anticipation-labs/anticipy-hardware/03_PCB/R1_TARGET_NOT_YET_DESIGNED/README.md

# R1 — not yet designed

This folder is intentionally empty.

R1 is the current target board. As of 2026-09-06 it exists only as a written brief:
[`../../01_CURRENT_TARGET_R1/Anticipy_PROD_R1_Flux_Build_Brief.md`](../../01_CURRENT_TARGET_R1/Anticipy_PROD_R1_Flux_Build_Brief.md).

No schematic, layout, BOM or fabrication output exists. When work starts, the KiCad project
belongs here.

The brief's own first instruction is worth repeating: create the project, record the requirements,
and return a block diagram, an interface/power-rail table, a proposed BOM with active manufacturer
part numbers, and a list of unresolved conflicts — **before** placing or routing anything.
