anticipation-labs/anticipy-hardware/08_HISTORICAL_PACKAGES/2026-08-27_v07_four_day_build_pack/mechanical/V07_FIT_REPORT.md

# Anticipy v0.7 no-custom-PCB retained fit report

Classification: four-day hand-assembled founder prototype, not customer production.

1. PASS — finished envelope
2. PASS — 15% XY envelopes inside cavity and outside chain keepout
3. PASS — 15% same-layer envelopes do not overlap
4. PASS — actual component boxes do not collide
5. PASS — actual components do not intersect printed structure
6. PASS — base, carrier and lid close without solid interference
7. PASS — all explicit Z gaps positive
8. PASS — 15% seated Z envelopes retain positive keeper/lid gaps
9. PASS — primary print meshes watertight
10. PASS — one positive body per primary print mesh

Finished envelope: 76.0 × 33.0 × 19.0 mm.
The 51 × 21 × 11 mm target is not claimed because the protected 35 × 25 × 6 mm pack alone needs 40.25 × 28.75 mm XY reservation after the 15% margin.
Printed plastic estimate: 17.11 g.
Nominal complete estimate: 36.91 g; with 15% uncertainty: 42.44 g.
Mass remains a physical weigh-in gate because supplier pack, wiring, foam and screw weights are not controlled here.

Positive digital clearance does not prove battery runtime, drop survival, acoustics, RF range, sealing or electrical safety.
