anticipation-labs/anticipy-hardware/latest_builds/E1P1/pcb/manufacturing/drill_report.txt

Drill report for Anticipy_R1_E1_PROTOTYPE.kicad_pcb
Created on 2026-09-09T07:02:48

Copper Layer Stackup:
    =============================================================
    L1 :  F.Cu                      front
    L2 :  In1.Cu                    in1
    L3 :  In2.Cu                    in2
    L4 :  B.Cu                      back

Drill file 'Anticipy_R1_E1_PROTOTYPE-PTH.drl' contains
    plated through holes:
    =============================================================
    T1  0.200mm  0.0079"  (128 holes))
    T2  0.304mm  0.0120"  (9 holes))
    T3  0.600mm  0.0236"  (4 holes)  (with 4 slots)

    Total plated holes count 141

Drill file 'Anticipy_R1_E1_PROTOTYPE-NPTH.drl' contains
    unplated through holes:
    =============================================================

    Total unplated holes count 0
