anticipation-labs/anticipy-hardware/02_PROTOTYPE_XIAO/00_FOLDER_STATUS.md

# Folder status

This is the latest saved XIAO wiring/CAD packet that does not depend on Lee's Electronics. Its old SAPA/Saturday schedule is no longer an active commitment. Use the wiring, CAD and QA gates as engineering reference only; do not assume SAPA has accepted the job or has the parts.

The enclosed UF2 remains on physical release hold. Do not ship a unit until the real battery, motor, charging, audio, BLE, thermal, enclosure and mechanical tests pass.
