anticipation-labs/anticipy-hardware/05_FIRMWARE/SOURCE/THIRD_PARTY_NOTICES.md

# Third-party basis and notices

This EVT is a modified fork of the public Omi DevKit firmware from `BasedHardware/omi`, inspected at commit `0303fd24579f8e3d0a3b1c3d9e5ad99adf87a4d2` (2026-08-28). That repository is distributed under the MIT License. Preserve its copyright and license notice when distributing source or binaries.

The embedded Opus 1.2.1 source contains copyright notices from Xiph.Org Foundation, Skype Limited and other contributors and is distributed under permissive BSD-style terms recorded in the individual source headers. Binary distributions must reproduce the applicable notices and disclaimers in their documentation/materials.

Nordic nRF Connect SDK, Zephyr, board support and toolchain components have their own upstream licenses. A production release must run a complete software-bill-of-materials and license-notice generation step; this short notice is not a substitute for that compliance output.
