anticipation-labs/anticipy-hardware/08_HISTORICAL_PACKAGES/2026-08-28_tuesday_evt_v0.1/TUESDAY_TRUTH.md

# Tuesday truth

The from-components architecture is technically plausible at the strict size. It is not yet proven hardware.

- **Plausible by Tuesday:** 10 cosmetic shells and 1–2 working engineering units, if all parts and a correctly sized protected cell are physically available Monday.
- **High-risk attempt:** 10 bench-built units by Tuesday evening with two experienced technicians, but with almost no debugging or validation time.
- **Not an honest promise:** 10 safe, private, 16-hour, customer-ready pendants by Tuesday.

The immediate blocker is not PLAUD or a custom PCB. It is obtaining 12 documented protected cells that physically measure no more than 25 × 20 × 5 mm, followed by proving unit 1.
