anticipation-labs/anticipy-hardware/08_HISTORICAL_PACKAGES/2026-08-28_execution_v1.0/07_SOURCES/SOURCE_LEDGER_V1.md

# Primary source ledger

| Decision | Source |
|---|---|
| PLAUD NotePin S is 51 × 21 × 11 mm and 17.4 g | https://www.plaud.ai/pages/plaud-notepin-s |
| PLAUD material family is aluminum alloy + polycarbonate | https://support.plaud.ai/hc/en-us/articles/53770668740761-What-is-the-difference-between-Plaud-NotePin-and-NotePin-S |
| Raytac AN54LV-15 is 8.4 × 6.4 × 1.5 mm and pre-certified | https://www.raytac.com/product/ins.php?index_id=169 |
| Raytac official land/keepout guide | https://www.raytac.com/document/act.php?act=1&index_id=103 |
| IM69D128S: PDM, 69 dB SNR, 520 µA, component-level IP57 | https://www.infineon.com/part/IM69D128S |
| nPM1300 charger, power path and fuel-gauge features | https://www.nordicsemi.com/Products/nPM1300 |
| DRV2605L A2/REG is the 1.8 V regulator output and requires bypass to ground | https://www.ti.com/lit/ds/symlink/drv2605l.pdf |
| MKDV4GCL-ABF: 4 Gbit, about 481 MB usable, managed SD/SPI NAND | https://datasheet.lcsc.com/datasheet/pdf/861dc17860b6ca6b6ed9c649f697f4e2.pdf?productCode=C51966232 |
| MKDV4GCL-ABF JLC/LCSC assembly stock record | https://jlcpcb.com/partdetail/MK-MKDV4GCLABF/C51966232 |
| PTS841 public dimensions/land and 100k-cycle rating | https://www.littelfuse.com/products/switches/tactile-switches/pts841 |
| VC0720B015F 7 mm leaded coin motor | https://www.vybronics.com/coin-vibration-motors/with-brushes/v-c0720b015f |
| LP571225 comparator battery | https://www.lithium-polymer-akkus.de/wp-content/uploads/2021/04/LP571225-3.7V-200mAh.pdf |
| Seeed XIAO nRF52840 Sense 3-pack for lab build | https://www.seeedstudio.com/Seeed-Studio-XIAO-nRF52840-Sense-3PCS-p-5922.html |
| P2S specifications and supported-material baseline | https://bambulab.com/en/p2s/specs |
| Bambu Silk/Silk+ printing guidance | https://wiki.bambulab.com/en/x1/manual/printing-with-silk-filaments |
| Bambu PLA Metal is metal-textured plastic, not an aluminum part | https://ca.store.bambulab.com/products/pla-metal |
| JLCPCB baseline PCB lead-time explanation | https://jlcpcb.com/help/article/pcb-fabrication-services-and-production-time |
| JLCPCB SMT lead-time explanation | https://jlcpcb.com/help/article/smt-service-lead-time-overview |

Source pages can change. Inventory and delivery remain unallocated until checkout or a written supplier acknowledgement.
