anticipation-labs/anticipy-hardware/08_HISTORICAL_PACKAGES/2026-09-05_master_package/06_ROUTING_CANDIDATES_NOT_FOR_FAB/00_MASTER_PACKAGE_WARNING.md

# Do not fabricate these candidates

These are independent subsystem-routing experiments from the 36-hour sprint. They are not cumulative and are not a released PCB. A senior PCB engineer may use them as routing evidence only after rebuilding/consolidating the final board and rerunning complete ERC, DRC, DFM, RF, power and mechanical review with zero unconnected items.
