anticipation-labs/anticipy-hardware/08_HISTORICAL_PACKAGES/2026-08-19_anticipy_design_ds_bundle/hardware/xiao-spec.html

Electronics

# XIAO nRF52840 Sense

Property | Value
PCB | 20.955 × 17.78 × 1.24 mm
USB-C shell | 8.94 w × 3.21 h · overhangs edge 1.53 mm
mic | PDM MEMS, aperture on top face
charger | BQ25101 — 50 mA stock, 100 mA with P0.13 low
flash | 2 MB QSPI (≈8 min Opus — emergency buffer only)
battery | BLL 752042 · 3.7 V · 500 mAh · max 8.0×20.5×43 mm
storage add-on | Adafruit 4682 3V microSD (SPI: D8 SCK · D9 MISO · D10 MOSI · D0 CS)
firmware | Omi devkit lineage, Zephyr · Opus 16 kHz over BLE · SD offline sync GATT service
