anticipation-labs/anticipy-hardware/08_HISTORICAL_PACKAGES/2026-09-05_master_package/05_OLDER_R0_KICAD_NOT_FOR_FAB/drc_unrouted_report.txt

** Drc report for /workspace/scratch/295a51172f48/anticipy_pcb_kicad/Anticipy_PROD_R0_EVT.kicad_pcb **
** Created on 2026-08-30 02:28:59 **

** Found 134 DRC violations **
[silk_overlap]: Silkscreen overlap
    Rule: board setup constraints silk; Severity: warning
    @(31.0000 mm, 38.6000 mm): PCB Text 'SW' on F.Silkscreen
    @(29.3500 mm, 38.4000 mm): Line on F.Silkscreen
[silk_overlap]: Silkscreen overlap
    Rule: board setup constraints silk; Severity: warning
    @(54.2500 mm, 35.3500 mm): Line on F.Silkscreen
    @(53.6594 mm, 35.2900 mm): Line on F.Silkscreen
[silk_over_copper]: Silkscreen clipped by solder mask
    Local override; Severity: warning
    @(31.2000 mm, 32.9000 mm): PCB Text 'U2 PMIC' on F.Silkscreen
[silk_over_copper]: Silkscreen clipped by solder mask
    Local override; Severity: warning
    @(38.3464 mm, 38.2200 mm): Line on F.Silkscreen
[silk_over_copper]: Silkscreen clipped by solder mask
    Local override; Severity: warning
    @(54.2500 mm, 35.3500 mm): Line on F.Silkscreen
[silk_over_copper]: Silkscreen clipped by solder mask
    Local override; Severity: warning
    @(53.1500 mm, 35.3500 mm): Line on F.Silkscreen
[silk_over_copper]: Silkscreen clipped by solder mask
    Local override; Severity: warning
    @(37.0000 mm, 38.5600 mm): Line on F.Silkscreen
[silk_over_copper]: Silkscreen clipped by solder mask
    Local override; Severity: warning
    @(37.0000 mm, 38.5600 mm): Line on F.Silkscreen
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
    @(50.2600 mm, 21.9400 mm): Pad 5 [GND] of MIC2 on F.Cu
[hole_clearance]: Hole clearance violation (board setup constraints hole clearance 0.2500 mm; actual 0.1000 mm)
    Rule: board setup constraints hole; Severity: error
    @(51.0000 mm, 21.9400 mm): NPTH pad of MIC2
    @(51.0000 mm, 21.3900 mm): Pad 5 [GND] of MIC2 on F.Cu
[hole_clearance]: Hole clearance violation (board setup constraints hole clearance 0.2500 mm; actual 0.1000 mm)
    Rule: board setup constraints hole; Severity: error
    @(51.0000 mm, 21.9400 mm): NPTH pad of MIC2
    @(51.0000 mm, 22.4900 mm): Pad 5 [GND] of MIC2 on F.Cu
[hole_clearance]: Hole clearance violation (board setup constraints hole clearance 0.2500 mm; actual 0.1944 mm)
    Rule: board setup constraints hole; Severity: error
    @(23.2050 mm, 27.1100 mm): NPTH pad of J1
    @(24.2800 mm, 26.8000 mm): Pad A1 [GND] of J1 on F.Cu
[hole_clearance]: Hole clearance violation (board setup constraints hole clearance 0.2500 mm; actual 0.1944 mm)
    Rule: board setup constraints hole; Severity: error
    @(23.2050 mm, 27.1100 mm): NPTH pad of J1
    @(24.2800 mm, 26.8000 mm): Pad B12 [GND] of J1 on F.Cu
[hole_clearance]: Hole clearance violation (board setup constraints hole clearance 0.2500 mm; actual 0.1944 mm)
    Rule: board setup constraints hole; Severity: error
    @(23.2050 mm, 32.8900 mm): NPTH pad of J1
    @(24.2800 mm, 33.2000 mm): Pad A12 [GND] of J1 on F.Cu
[hole_clearance]: Hole clearance violation (board setup constraints hole clearance 0.2500 mm; actual 0.1944 mm)
    Rule: board setup constraints hole; Severity: error
    @(23.2050 mm, 32.8900 mm): NPTH pad of J1
    @(24.2800 mm, 33.2000 mm): Pad B1 [GND] of J1 on F.Cu

** Found 171 unconnected pads **
[unconnected_items]: Missing connection between items
    Local override; Severity: error
    @(29.0000 mm, 30.7750 mm): Pad 2 [GND] of C3 on B.Cu
    @(28.7625 mm, 30.7500 mm): Pad 6 [GND] of U2 on F.Cu
[unconnected_items]: Missing connection between items
    Local override; Severity: error
    @(48.7625 mm, 36.3500 mm): Pad 8 [GND] of U3 on F.Cu
    @(48.7625 mm, 36.8500 mm): Pad 7 [GND] of U3 on F.Cu
[unconnected_items]: Missing connection between items
    Local override; Severity: error
    @(48.2500 mm, 36.8625 mm): Pad 6 [GND] of U3 on F.Cu
    @(48.7625 mm, 36.8500 mm): Pad 7 [GND] of U3 on F.Cu
[unconnected_items]: Missing connection between items
    Local override; Severity: error
    @(27.2000 mm, 32.4800 mm): Pad 2 [GND] of C16 on B.Cu
    @(27.0000 mm, 31.9250 mm): Pad 2 [GND] of C4 on F.Cu
[unconnected_items]: Missing connection between items
    Local override; Severity: error
    @(39.0100 mm, 38.6000 mm): Pad 2 [GND] of R13 on F.Cu
    @(39.3500 mm, 38.0000 mm): Pad 2 [GND] of C21 on B.Cu
[unconnected_items]: Missing connection between items
    Local override; Severity: error
    @(37.1625 mm, 22.6365 mm): Pad 4 [GND] of MIC1 on F.Cu
    @(37.2600 mm, 21.9400 mm): Pad 5 [GND] of MIC1 on F.Cu
[unconnected_items]: Missing connection between items
    Local override; Severity: error
    @(37.9375 mm, 36.0500 mm): Pad 2 [GND] of Q1 on F.Cu
    @(37.4350 mm, 35.5250 mm): Pad 11 [GND] of J2 on B.Cu
[unconnected_items]: Missing connection between items
    Local override; Severity: error
    @(31.2000 mm, 30.0000 mm): Pad 33 [GND] of U2 on F.Cu
    @(31.9750 mm, 30.0000 mm): Pad 2 [GND] of C6 on B.Cu
[unconnected_items]: Missing connection between items
    Local override; Severity: error
    @(37.1625 mm, 22.6365 mm): Pad 4 [GND] of MIC1 on F.Cu
    @(38.0000 mm, 22.4900 mm): Pad 5 [GND] of MIC1 on F.Cu
[unconnected_items]: Missing connection between items
    Local override; Severity: error
    @(51.7400 mm, 21.9400 mm): Pad 5 [GND] of MIC2 on F.Cu
    @(51.0000 mm, 22.4900 mm): Pad 5 [GND] of MIC2 on F.Cu
[unconnected_items]: Missing connection between items
    Local override; Severity: error
    @(50.2600 mm, 21.9400 mm): Pad 5 [GND] of MIC2 on F.Cu
    @(51.0000 mm, 21.3900 mm): Pad 5 [GND] of MIC2 on F.Cu
[unconnected_items]: Missing connection between items
    Local override; Severity: error
    @(51.0000 mm, 21.3900 mm): Pad 5 [GND] of MIC2 on F.Cu
    @(51.7400 mm, 21.9400 mm): Pad 5 [GND] of MIC2 on F.Cu
[unconnected_items]: Missing connection between items
    Local override; Severity: error
    @(38.0000 mm, 21.3900 mm): Pad 5 [GND] of MIC1 on F.Cu
    @(37.2600 mm, 21.9400 mm): Pad 5 [GND] of MIC1 on F.Cu
[unconnected_items]: Missing connection between items
    Local override; Severity: error
    @(38.7400 mm, 21.9400 mm): Pad 5 [GND] of MIC1 on F.Cu
    @(38.0000 mm, 22.4900 mm): Pad 5 [GND] of MIC1 on F.Cu
[unconnected_items]: Missing connection between items
    Local override; Severity: error
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
    @(33.0100 mm, 34.2000 mm): Pad 2 [I2C_SCL] of R1 on F.Cu
    @(47.2375 mm, 35.3500 mm): Pad 1 [I2C_SCL] of U3 on F.Cu
[unconnected_items]: Missing connection between items
    Local override; Severity: error
    @(31.4500 mm, 32.4375 mm): Pad 13 [I2C_SDA] of U2 on F.Cu
    @(31.2100 mm, 34.2000 mm): Pad 2 [I2C_SDA] of R2 on F.Cu
[unconnected_items]: Missing connection between items
    Local override; Severity: error
    @(47.2375 mm, 36.8500 mm): Pad 4 [I2C_SDA] of U3 on F.Cu
    @(53.8500 mm, 26.0000 mm): Pad 16 [I2C_SDA] of U1 on F.Cu
[unconnected_items]: Missing connection between items
    Local override; Severity: error
    @(31.2100 mm, 34.2000 mm): Pad 2 [I2C_SDA] of R2 on F.Cu
    @(47.2375 mm, 36.8500 mm): Pad 4 [I2C_SDA] of U3 on F.Cu
[unconnected_items]: Missing connection between items
    Local override; Severity: error
    @(28.7625 mm, 31.2500 mm): Pad 7 [PMIC_INT] of U2 on F.Cu
    @(58.0500 mm, 34.6500 mm): Pad 41 [PMIC_INT] of U1 on F.Cu
[unconnected_items]: Missing connection between items
    Local override; Severity: error
    @(47.7500 mm, 35.3375 mm): Pad 12 [ACC_INT1] of U3 on F.Cu
    @(59.6500 mm, 34.6500 mm): Pad 44 [ACC_INT1] of U1 on F.Cu
[unconnected_items]: Missing connection between items
    Local override; Severity: error
    @(48.2500 mm, 35.3375 mm): Pad 11 [ACC_INT2] of U3 on F.Cu
    @(59.2500 mm, 33.7500 mm): Pad 43 [ACC_INT2] of U1 on F.Cu
[unconnected_items]: Missing connection between items
    Local override; Severity: error
    @(56.8500 mm, 33.7500 mm): Pad 38 [PDM_CLK] of U1 on F.Cu
    @(51.8375 mm, 22.6365 mm): Pad 2 [PDM_CLK] of MIC2 on F.Cu
[unconnected_items]: Missing connection between items
    Local override; Severity: error
    @(51.8375 mm, 22.6365 mm): Pad 2 [PDM_CLK] of MIC2 on F.Cu
    @(38.8375 mm, 22.6365 mm): Pad 2 [PDM_CLK] of MIC1 on F.Cu
[unconnected_items]: Missing connection between items
    Local override; Severity: error
    @(57.2500 mm, 34.6500 mm): Pad 39 [PDM_DATA] of U1 on F.Cu
    @(54.7100 mm, 23.3000 mm): Pad 2 [PDM_DATA] of R15 on F.Cu
[unconnected_items]: Missing connection between items
    Local override; Severity: error
    @(54.7100 mm, 23.3000 mm): Pad 2 [PDM_DATA] of R15 on F.Cu
    @(41.7100 mm, 23.3000 mm): Pad 2 [PDM_DATA] of R14 on F.Cu
[unconnected_items]: Missing connection between items
    Local override; Severity: error
    @(37.1625 mm, 23.4585 mm): Pad 3 [PDM_DATA_MIC1] of MIC1 on F.Cu
    @(40.6900 mm, 23.3000 mm): Pad 1 [PDM_DATA_MIC1] of R14 on F.Cu
[unconnected_items]: Missing connection between items
    Local override; Severity: error
    @(50.1625 mm, 23.4585 mm): Pad 3 [PDM_DATA_MIC2] of MIC2 on F.Cu
    @(53.6900 mm, 23.3000 mm): Pad 1 [PDM_DATA_MIC2] of R15 on F.Cu
[unconnected_items]: Missing connection between items
    Local override; Severity: error
    @(42.6900 mm, 38.0000 mm): Pad 1 [SD_SCK_MCU] of R8 on B.Cu
    @(56.4500 mm, 34.6500 mm): Pad 37 [SD_SCK_MCU] of U1 on F.Cu
[unconnected_items]: Missing connection between items
    Local override; Severity: error
    @(43.7100 mm, 38.0000 mm): Pad 2 [SD_SCK_CARD] of R8 on B.Cu
    @(44.2950 mm, 35.6500 mm): Pad 5 [SD_SCK_CARD] of J2 on B.Cu
[unconnected_items]: Missing connection between items
    Local override; Severity: error
    @(44.8900 mm, 38.0000 mm): Pad 1 [SD_MOSI_MCU] of R9 on B.Cu
    @(56.0500 mm, 33.7500 mm): Pad 36 [SD_MOSI_MCU] of U1 on F.Cu
[unconnected_items]: Missing connection between items
    Local override; Severity: error
    @(42.0950 mm, 35.6500 mm): Pad 3 [SD_MOSI_CARD] of J2 on B.Cu
    @(45.9100 mm, 38.0000 mm): Pad 2 [SD_MOSI_CARD] of R9 on B.Cu
[unconnected_items]: Missing connection between items
    Local override; Severity: error
    @(48.1100 mm, 38.0000 mm): Pad 2 [SD_MISO_MCU] of R10 on B.Cu
    @(54.7500 mm, 32.0000 mm): Pad 29 [SD_MISO_MCU] of U1 on F.Cu
[unconnected_items]: Missing connection between items
    Local override; Severity: error
    @(46.4950 mm, 35.6500 mm): Pad 7 [SD_MISO_CARD] of J2 on B.Cu
    @(47.0900 mm, 38.0000 mm): Pad 1 [SD_MISO_CARD] of R10 on B.Cu
[unconnected_items]: Missing connection between items
    Local override; Severity: error
    @(40.9950 mm, 35.6500 mm): Pad 2 [SD_CS] of J2 on B.Cu
    @(41.5100 mm, 38.0000 mm): Pad 2 [SD_CS] of R7 on B.Cu
[unconnected_items]: Missing connection between items
    Local override; Severity: error
    @(54.7500 mm, 31.2000 mm): Pad 27 [SD_CS] of U1 on F.Cu
    @(40.9950 mm, 35.6500 mm): Pad 2 [SD_CS] of J2 on B.Cu
[unconnected_items]: Missing connection between items
    Local override; Severity: error
    @(37.2600 mm, 29.5000 mm): Pad 9 [SD_DETECT] of J2 on B.Cu
    @(60.0500 mm, 33.7500 mm): Pad 45 [SD_DETECT] of U1 on F.Cu
[unconnected_items]: Missing connection between items
    Local override; Severity: error
    @(32.8100 mm, 35.5000 mm): Pad 2 [USER_BTN] of R11 on F.Cu
    @(32.4500 mm, 32.4375 mm): Pad 15 [USER_BTN] of U2 on F.Cu
[unconnected_items]: Missing connection between items
    Local override; Severity: error
    @(29.3000 mm, 37.0000 mm): Pad 1 [USER_BTN] of SW1 on F.Cu
    @(32.8100 mm, 35.5000 mm): Pad 2 [USER_BTN] of R11 on F.Cu
[unconnected_items]: Missing connection between items
    Local override; Severity: error
    @(53.8500 mm, 29.2000 mm): Pad 22 [USER_BTN] of U1 on F.Cu
    @(32.4500 mm, 32.4375 mm): Pad 15 [USER_BTN] of U2 on F.Cu
[unconnected_items]: Missing connection between items
    Local override; Severity: error
    @(36.1900 mm, 38.6000 mm): Pad 1 [HAPTIC_PWM] of R12 on F.Cu
    @(53.8500 mm, 30.0000 mm): Pad 24 [HAPTIC_PWM] of U1 on F.Cu
[unconnected_items]: Missing connection between items
    Local override; Severity: error
    @(37.9900 mm, 38.6000 mm): Pad 1 [HAPTIC_GATE] of R13 on F.Cu
    @(37.9375 mm, 37.9500 mm): Pad 1 [HAPTIC_GATE] of Q1 on F.Cu
[unconnected_items]: Missing connection between items
    Local override; Severity: error
    @(37.2100 mm, 38.6000 mm): Pad 2 [HAPTIC_GATE] of R12 on F.Cu
    @(37.9900 mm, 38.6000 mm): Pad 1 [HAPTIC_GATE] of R13 on F.Cu
[unconnected_items]: Missing connection between items
    Local override; Severity: error
    @(39.1500 mm, 37.0000 mm): Pad 1 [HAPTIC_NEG] of D1 on F.Cu
    @(39.4800 mm, 35.2000 mm): Pad 2 [HAPTIC_NEG] of C23 on F.Cu
[unconnected_items]: Missing connection between items
    Local override; Severity: error
    @(36.0625 mm, 37.0000 mm): Pad 3 [HAPTIC_NEG] of Q1 on F.Cu
    @(39.1500 mm, 37.0000 mm): Pad 1 [HAPTIC_NEG] of D1 on F.Cu
[unconnected_items]: Missing connection between items
    Local override; Severity: error
    @(27.6000 mm, 37.5500 mm): Pad 1 [LED_BLUE_K] of LED1 on F.Cu
    @(32.9500 mm, 27.5625 mm): Pad 25 [LED_BLUE_K] of U2 on F.Cu
[unconnected_items]: Missing connection between items
    Local override; Severity: error
    @(27.6000 mm, 36.8500 mm): Pad 3 [LED_RED_K] of LED1 on F.Cu
    @(32.4500 mm, 27.5625 mm): Pad 26 [LED_RED_K] of U2 on F.Cu
[unconnected_items]: Missing connection between items
    Local override; Severity: error
    @(49.5000 mm, 38.3000 mm): Pad 1 [SWDIO] of TP1 on B.Cu
    @(62.8500 mm, 34.6500 mm): Pad 51 [SWDIO] of U1 on F.Cu
[unconnected_items]: Missing connection between items
    Local override; Severity: error
    @(51.0000 mm, 38.3000 mm): Pad 1 [SWDCLK] of TP2 on B.Cu
    @(63.6500 mm, 34.6500 mm): Pad 53 [SWDCLK] of U1 on F.Cu
[unconnected_items]: Missing connection between items
    Local override; Severity: error
    @(52.5000 mm, 38.3000 mm): Pad 1 [RESET] of TP3 on B.Cu
    @(57.6500 mm, 33.7500 mm): Pad 40 [RESET] of U1 on F.Cu
[unconnected_items]: Missing connection between items
    Local override; Severity: error
    @(54.7500 mm, 28.8000 mm): Pad 21 [UART_TX] of U1 on F.Cu
    @(57.0000 mm, 38.3000 mm): Pad 1 [UART_TX] of TP6 on B.Cu
[unconnected_items]: Missing connection between items
    Local override; Severity: error
    @(53.8500 mm, 28.4000 mm): Pad 20 [UART_RX] of U1 on F.Cu
    @(58.5000 mm, 38.3000 mm): Pad 1 [UART_RX] of TP7 on B.Cu

** Found 0 Footprint errors **

** End of Report **
