anticipation-labs/anticipy-hardware/03_PCB/R0B_CHECKPOINT_NOT_FOR_FAB/99_Superseded_Notice/SUPERSEDED_FILES_NOTICE.md

# Superseded files notice

The earlier Flux build brief, R0A source tree, 49 x 20 mm layout, removable microSD concept, and all experimental autorouter outputs are deliberately excluded from the active handoff.

The controlling checkpoint in this ZIP is `ANT-PROD-R0B` with a 45.8 x 18.0 mm board outline, soldered NAND storage, updated ESD protection, button/light-pipe interface targets, and explicit fabrication blockers.

Do not merge R0A, Flux, or experimental route files into R0B. If an engineer reuses any older idea, it must be independently reviewed and intentionally incorporated into a new controlled revision.
