anticipation-labs/anticipy-hardware/03_PCB/R0B_CHECKPOINT_NOT_FOR_FAB/01_Electrical_Source/Reports/placement.png

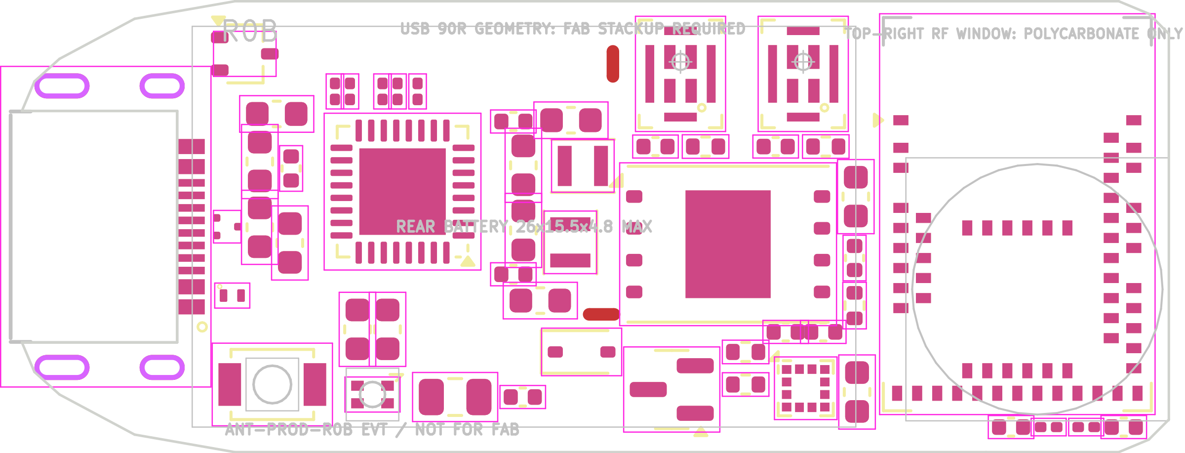
03_PCB/R0B_CHECKPOINT_NOT_FOR_FAB/01_Electrical_Source/Reports/placement.png
