anticipation-labs/anticipy-hardware/04_MECHANICAL/OPENSCAD_SHELL_PROGRAM_v5.1/beauty_back.png

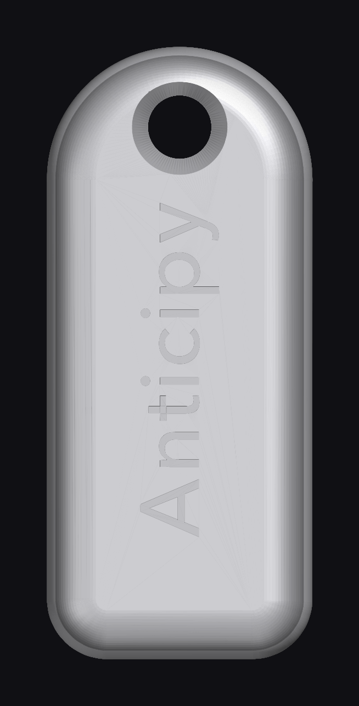
04_MECHANICAL/OPENSCAD_SHELL_PROGRAM_v5.1/beauty_back.png
