anticipation-labs/anticipy-hardware/04_MECHANICAL/OPENSCAD_SHELL_PROGRAM_v5.1/cmp_side_by_side.png

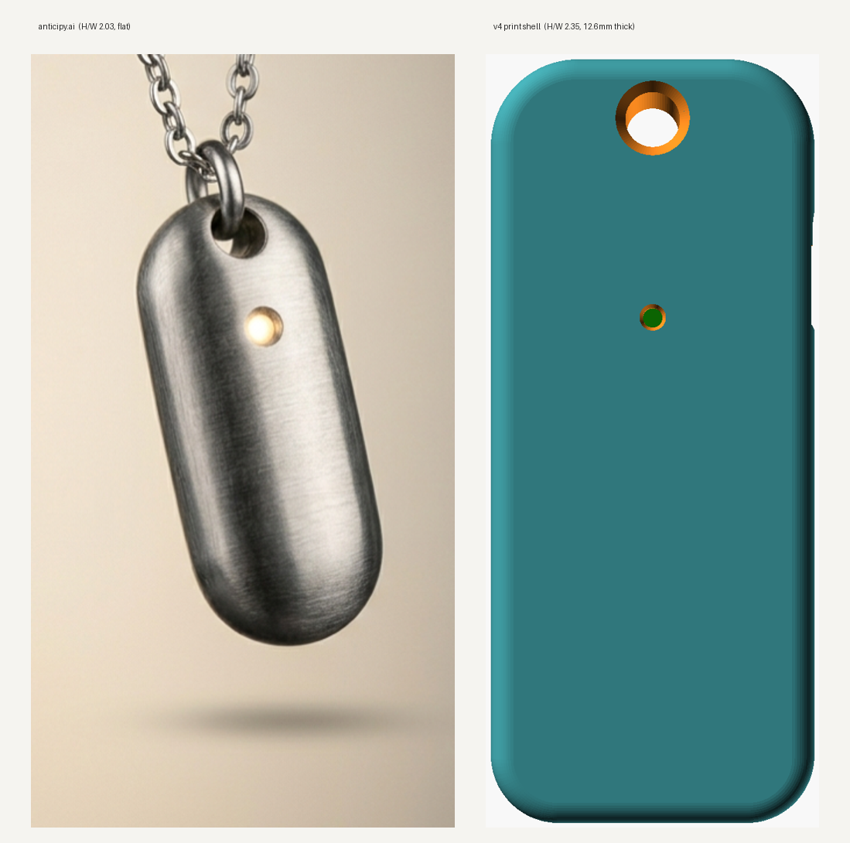
04_MECHANICAL/OPENSCAD_SHELL_PROGRAM_v5.1/cmp_side_by_side.png
