anticipation-labs/anticipy-hardware/04_MECHANICAL/OPENSCAD_SHELL_PROGRAM_v5.1/FINAL_v4_views.png

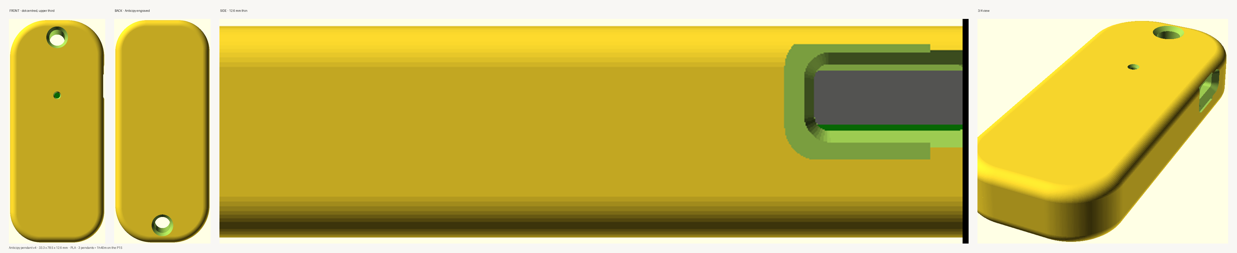
04_MECHANICAL/OPENSCAD_SHELL_PROGRAM_v5.1/FINAL_v4_views.png
