anticipation-labs/anticipy-hardware/04_MECHANICAL/OPENSCAD_SHELL_PROGRAM_v5.1/n_open.png

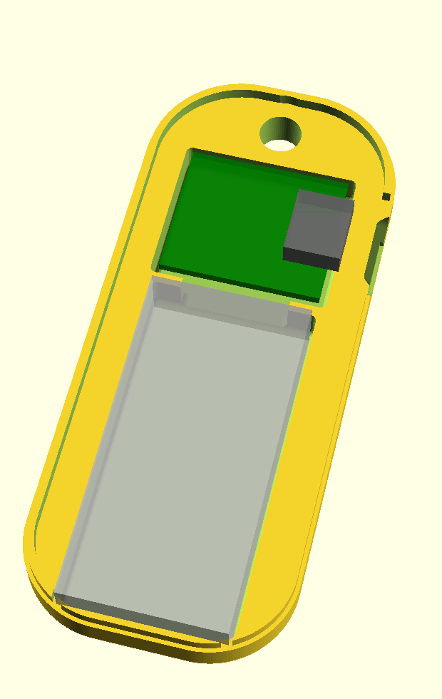
04_MECHANICAL/OPENSCAD_SHELL_PROGRAM_v5.1/n_open.png
