anticipation-labs/anticipy-hardware/04_MECHANICAL/OPENSCAD_SHELL_PROGRAM_v5.1/shape_A_square.png

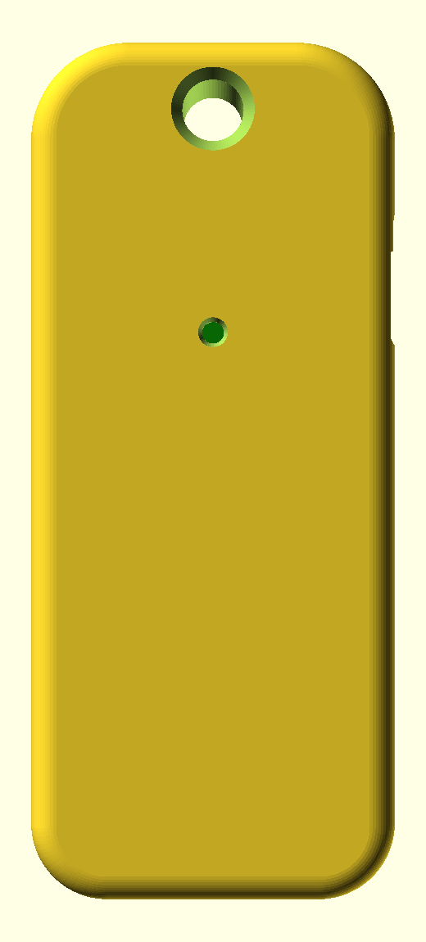
04_MECHANICAL/OPENSCAD_SHELL_PROGRAM_v5.1/shape_A_square.png
