anticipation-labs/anticipy-hardware/04_MECHANICAL/OPENSCAD_SHELL_PROGRAM_v5.1/v4_side.png

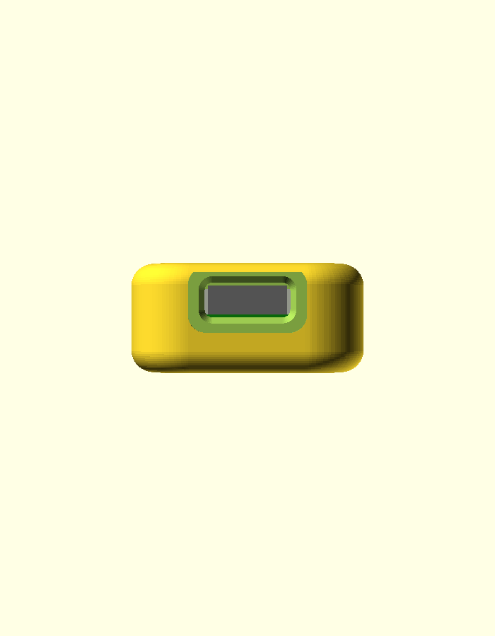
04_MECHANICAL/OPENSCAD_SHELL_PROGRAM_v5.1/v4_side.png
