anticipation-labs/anticipy-hardware/08_HISTORICAL_PACKAGES/2026-08-27_v07_four_day_build_pack/mechanical/v07_internal_layout.png

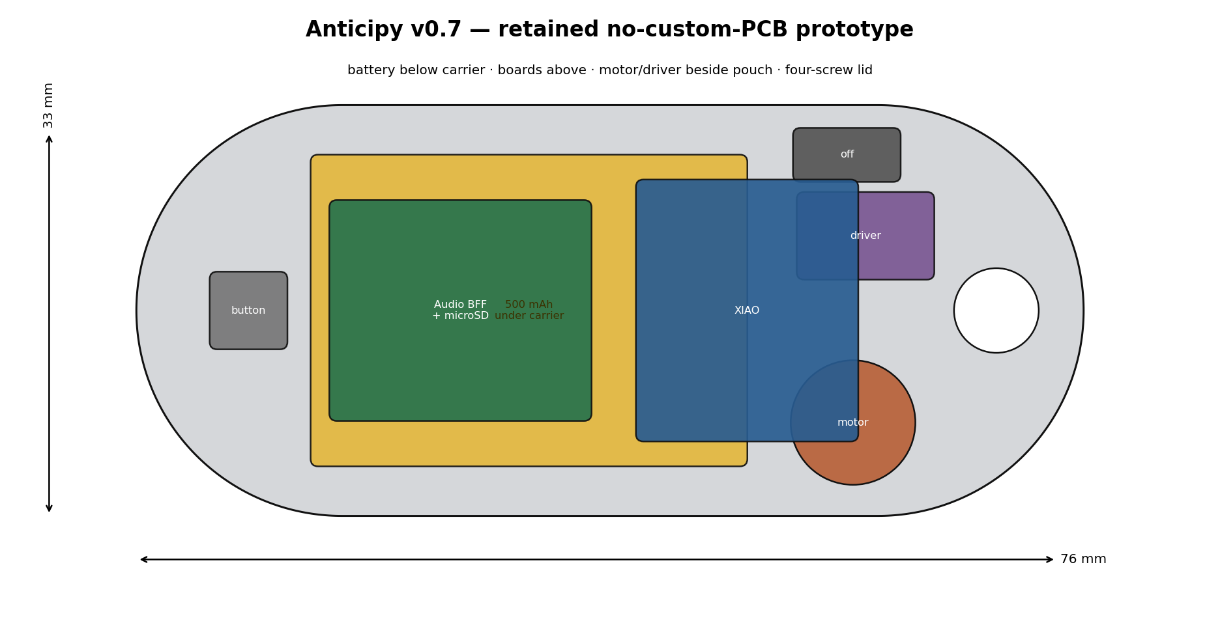
08_HISTORICAL_PACKAGES/2026-08-27_v07_four_day_build_pack/mechanical/v07_internal_layout.png
