anticipation-labs/anticipy-hardware/08_HISTORICAL_PACKAGES/2026-08-28_execution_v1.0/02_PRODUCTION_CAD/production_internal_layout.png

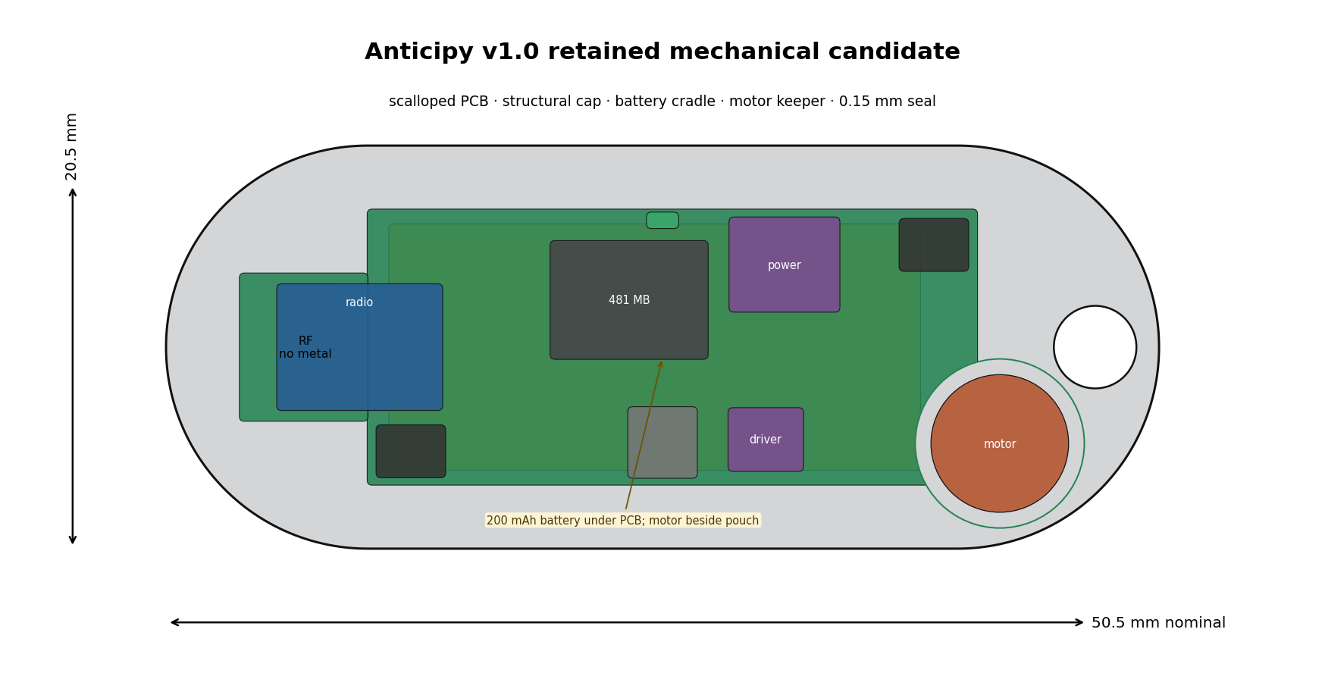
08_HISTORICAL_PACKAGES/2026-08-28_execution_v1.0/02_PRODUCTION_CAD/production_internal_layout.png
