anticipation-labs/anticipy-hardware/08_HISTORICAL_PACKAGES/2026-08-28_p2s_v07_enclosure/production_internal_layout.png

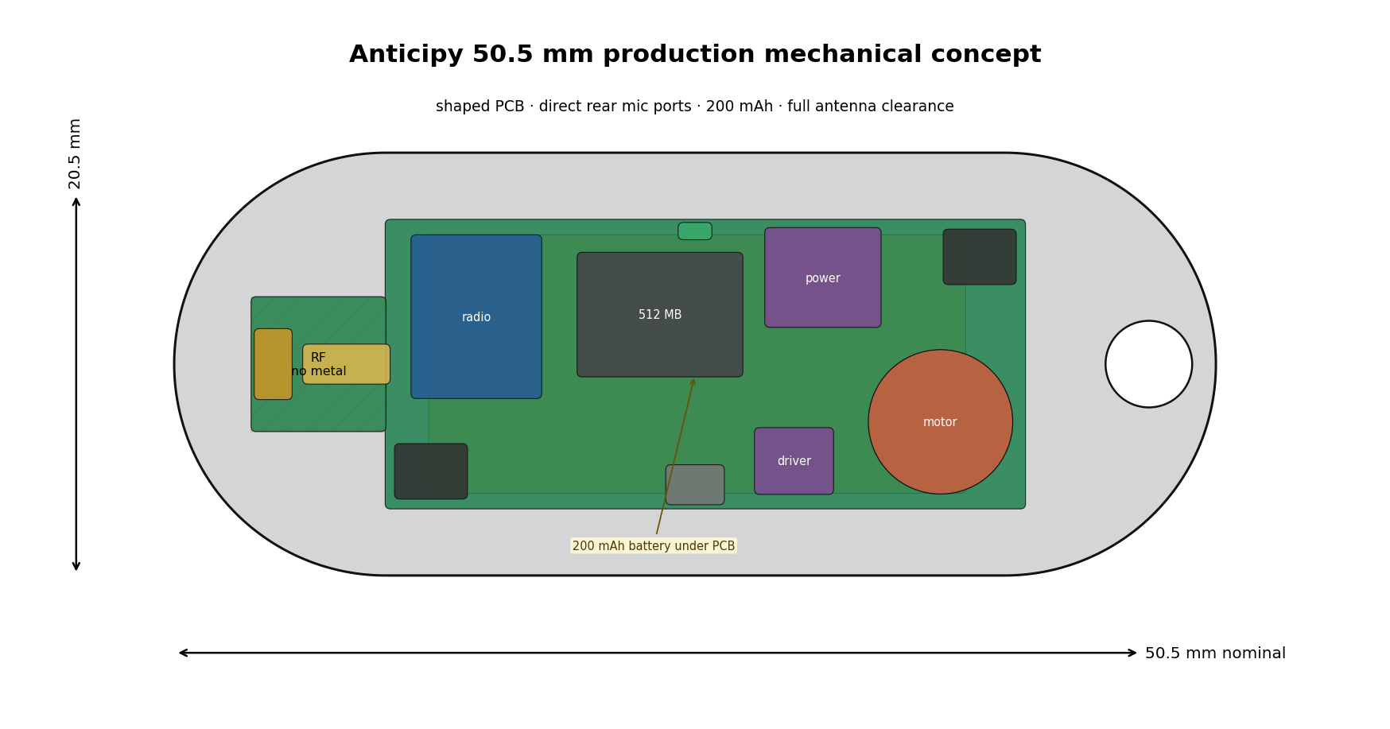
08_HISTORICAL_PACKAGES/2026-08-28_p2s_v07_enclosure/production_internal_layout.png
