anticipation-labs/anticipy-hardware/08_HISTORICAL_PACKAGES/2026-08-28_tuesday_evt_v0.1/anticipy_strict_evt_front_appearance.png

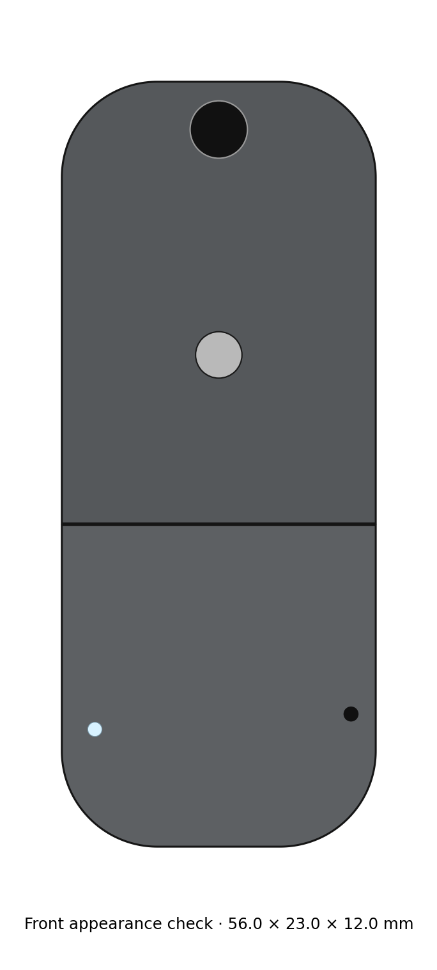
08_HISTORICAL_PACKAGES/2026-08-28_tuesday_evt_v0.1/anticipy_strict_evt_front_appearance.png
