anticipation-labs/anticipy-hardware/06_FACTORY_AND_QA/TEST_EVIDENCE/EXACT_SOURCING_2026-08-29.md

# Exact-size production candidate: live sourcing check

**Checked:** 2026-08-29 UTC  
**Destination:** West Vancouver, British Columbia, Canada  
**Scope:** corrected exact candidates for 3 EVT units and a later 50-unit build. No order was placed and no account/cart credentials were used. Stock and checkout freight can change without notice.

## Decision summary

- **Raytac AN54LV-15 is real and buyable in EVT quantity.** Raytac lists the 6.4 x 8.4 x 1.5 mm module as an active product. DigiKey Marketplace shows 45 pieces at USD 4.30, but Raytac—not DigiKey—ships them in approximately 14 days and charges USD 25 flat freight. Raytac's officially linked eBay listing adds five pieces at USD 6.00 plus USD 5.00 worldwide shipping.
- **It is not yet a production-secure 50-unit source.** The two visible online lots total exactly 50 pieces (45 + 5), leaving no attrition, rework or qualification spares and splitting the lot across channels. Direct Raytac allocation for at least 55–60 pieces is the appropriate production gate.
- **The standard LP571225 is not a 10 kOhm NTC pack.** Its product page and one-page drawing both explicitly say `NTC: No`. The supplier says it can customize a 10 kOhm ±1% at 25 C, B3380 NTC, but that requires a distinct controlled order drawing and a third lead.
- **The battery certification evidence is not purchase-release evidence for the custom NTC pack.** The standard page is tagged "IEC62133 Certified" and the drawing says the battery *parts* are IEC 62133 and RoHS compliant; another supplier page markets an "IEC62133 Certificate" version with different 50 mm wires and 26 mm length. No certificate/test-report number, exact-pack CB report, or exact LP571225 UN 38.3 test summary is downloadable from those pages. Obtain and match documents to the signed NTC pack drawing.
- **A complete exact-candidate cart is not executable today.** DigiKey currently shows zero VC0720B015F motors, while Vybronics' page still says 651 at DigiKey. That conflict must be resolved in writing. The custom battery is RFQ-only.

## Exact-candidate status table

Quantities assume one of each part per finished unit except **two IM69D128S microphones per unit**, matching the current production BOM.

| Candidate / exact order code | Live primary/authorized-source evidence | Cost for 3 EVT | Cost for 50 units | Status and procurement caveat |
|---|---|---:|---:|---|
| **Raytac AN54LV-15** | [Raytac](https://www.raytac.com/product/ins.php?index_id=169): 6.4 x 8.4 x 1.5 mm, chip antenna; FCC, IC/ISED, CE, Telec, KC, SRRC, NCC, RCM and WPC listed. [DigiKey Marketplace](https://www.digikey.com/en/products/detail/raytac/AN54LV-15/27793700): **45** in stock, USD 4.30 each, USD 25 flat freight, ships in approximately 14 days. [Raytac-linked eBay](https://www.ebay.com/itm/178290035890): **5** available, USD 6.00 each + USD 5.00 worldwide freight. | Preferred traceable route: USD **37.90** from DigiKey Marketplace (3 x 4.30 + 25 freight). Lower-cost official-linked eBay route: USD **23.00** (3 x 6 + 5 freight), before import charges. | Nominal online exhaustion: 45 DigiKey + 5 eBay = USD **253.50** including the two listed freight charges, before tax/import. | **EVT buyable; 50-unit production not released.** Exactly 50 visible gives zero spares. The eBay page says worldwide shipping and showed a Sep 4–22 estimate for its displayed generic location, not an address-validated West Vancouver promise. [Raytac direct](https://www.raytac.com/contact/) is RFQ/contact and says replies may take five business days. Raytac's RoHS/REACH report is still marked “Coming Soon.” |
| **Winbond W25N04KVZEIR** | [DigiKey Canada](https://www.digikey.ca/en/products/detail/winbond-electronics/W25N04KVZEIR/15182086): **406** in stock, active, but temporarily constrained and no backorders. [LCSC C6750381](https://www.lcsc.com/product-detail/C6750381.html): exact `W25N04KVZEIR TR`, **1,680** in stock/ships now, MOQ and multiple 30, USD 19.7556 at 30+. [JLCPCB C5342170](https://jlcpcb.com/partdetail/WinbondElec-W25N04KVZEIR/C5342170) lists the exact MPN as an Extended PCBA part; preordered material is for JLCPCB assembly only. | DigiKey: 3 x CAD 48.02 = CAD **144.06**. | DigiKey: 50 x CAD 41.9782 = CAD **2,098.91**. LCSC/JLC production option: buy 60 because of the 30-piece multiple = USD **1,185.34**, before freight/import/assembly. | **Buyable for 3 and 50.** Constrained-supply warning makes early reservation prudent. LCSC's 60-piece multiple provides 10 spares but uses a different commercial/PCBA flow. |
| **Infineon IM69D128SV01XTMA1** (2/unit) | [DigiKey Canada](https://www.digikey.ca/en/products/detail/infineon-technologies/IM69D128SV01XTMA1/17399510): **5,178** in stock; CAD 3.28 at 1, CAD 2.0346 at 100; 30-week manufacturer lead beyond stock. | 6 x CAD 3.28 = CAD **19.68**. | 100 x CAD 2.0346 = CAD **203.46**. | **Buyable.** Reserve all 100 plus yield spares from present stock; the quoted 30-week replenishment lead is material. |
| **Nordic NPM1300-CAAA-R** | [DigiKey Canada](https://www.digikey.ca/en/products/detail/nordic-semiconductor-asa/NPM1300-CAAA-R/19722484): **5,208** in stock; CAD 4.68 at 1, CAD 3.202 at 25; 20-week manufacturer lead beyond stock. | 3 x CAD 4.68 = CAD **14.04**. | 50 x CAD 3.202 = CAD **160.10**. | **Buyable.** WLCSP assembly/X-ray remains an assembler capability gate, not a sourcing gate. |
| **Texas Instruments DRV2605LYZFR** | [DigiKey Canada](https://www.digikey.ca/en/products/detail/texas-instruments/DRV2605LYZFR/4866959): **10,702** in stock; CAD 3.51 at 1, CAD 2.3636 at 25; 26-week manufacturer lead beyond stock. | 3 x CAD 3.51 = CAD **10.53**. | 50 x CAD 2.3636 = CAD **118.18**. | **Buyable.** DSBGA reflow/X-ray and exact support passives remain assembly/release gates. |
| **C&K / Littelfuse PTS841 GM SMTR LFS** | [Mouser Canada](https://www.mouser.ca/ProductDetail/CK/PTS841-GM-SMTR-LFS?qs=d0WKAl%252BL4KaUAcUzdsUy8A%3D%3D): **2,960** in stock/can ship immediately; CAD 0.619 at 1, CAD 0.569 at 25; nine-week factory lead beyond stock. | CAD **1.86**. | CAD **28.45**. | **Buyable.** Mouser's sub-CAD-100 shipment freight is extra unless consolidated with other Mouser material. |
| **Vybronics VC0720B015F** | [Vybronics](https://www.vybronics.com/coin-vibration-motors/with-brushes/v-c0720b015f) says **651** in DigiKey stock and quotes direct only for 2,000+ pieces. [DigiKey Canada](https://www.digikey.ca/en/products/detail/vybronics-inc/VC0720B015F/6570601) currently says **0** in stock, 500 past due, and nine-week standard lead; listed prices remain CAD 5.63 at 1 and CAD 4.5838 at 50. | **Not executable.** Price indication if replenished: CAD **16.89**. | **Not executable.** Price indication if replenished: CAD **229.19**. | **Conflicting / no verified buyable stock.** Do not count the manufacturer's mirrored DigiKey number until DigiKey or Vybronics confirms an allocated lot. The 25% tariff notation on Vybronics' page is a US tariff note, not a Canadian landed-cost quote. |
| **LiPol LP571225, custom three-wire 10 kOhm NTC pack** | [Standard LP571225 page](https://www.lipobattery.us/lithium-polymer-battery-lp571225-3-7v-200mah-0-74wh-with-protection-circuit-wires-10mm/): 5.7 x 12 x 25 mm, PCM, two 10 mm wires, **NTC: No**, MOQ 5, one week to ship only when stocked; new production 6–7 weeks at MOQ 5,000. Supplier offers custom 10 kOhm ±1%, B3380. [Standard drawing](https://www.lipobattery.us/wp-content/uploads/2021/04/LP571225-3.7V-200mAh.pdf): NTC No, PCM Yes, thickness tolerance to 6.0 mm, 26 mm finished length shown. [Alternate IEC-labelled page](https://www.lipobatteries.net/hot-selling-lipo-battery/lp571225-200mah-iec62133-certificate-lipo-batteries-manufacturer/) uses 50 mm wires and 26 mm length and says most packs lack thermistors. | **RFQ; MOQ 5; no public price or confirmed custom-sample lead.** | **RFQ; no published 50-piece production path.** Published new-production terms are MOQ 5,000 and 6–7 weeks. | **Custom controlled item; not purchase released.** Standard LP571225 does not meet the three-wire NTC requirement. Obtain a supplier-signed drawing and pack-specific compliance/transport documents before PO. |

## Candidate-cart arithmetic

These totals include only the corrected candidates above, not passives, PCB fabrication/assembly, programming, housings, freight not explicitly stated, or taxes.

| Build | Known-cost subtotal | Missing / blocking items |
|---|---:|---|
| **3 EVT, Canadian authorized distributors + DigiKey Marketplace module** | CAD **190.17** + USD **37.90**. The CAD subtotal is DigiKey semiconductors plus the Mouser switch; DigiKey's CAD 188.31 regular-stock portion is above its free-delivery threshold. | Exact motor unavailable; custom battery RFQ. Mouser freight is extra on its CAD 1.86 standalone order. |
| **50, DigiKey/Mouser semiconductor route + nominal split module lot** | CAD **2,609.10** + USD **253.50**. | Exact motor unavailable; custom battery RFQ; module lot has no spares and is therefore not a production release. |
| **50, LCSC/JLC-oriented W25 route + nominal split module lot** | CAD **510.19** + USD **1,185.34** for 60 W25 parts + USD **253.50** for 50 modules. | Same motor/battery/module blockers; add LCSC freight, import costs, consignment/global-sourcing handling, and PCBA charges. |

## LP571225 release requirements

The production item should remain `BAT-ANT-200-001`, not merely `LP571225`. Require a supplier-signed drawing that fixes all of the following:

- finished maximum envelope **27.0 x 12.5 x 6.0 mm**, including PCM, tape, weld tabs, NTC and lead exit; the public comparator drawing permits 26 ± 1 mm finished length, so 26 mm cannot be treated as the maximum;
- 3.7 V nominal, 200 mAh minimum/accepted capacity tolerance, 1S1P PCM thresholds, permitted charge current and temperature limits;
- **three leads**, exact colors/polarity/length/connector or stripped termination;
- NTC **10 kOhm ±1% at 25 C, B3380** and its physical placement on the cell;
- swelling allowance and lifecycle acceptance criteria;
- the exact finished pack's **IEC 62133-2 test report or CB certificate**, **UN 38.3 test summary**, SDS/MSDS, RoHS/REACH declarations, and dangerous-goods shipping declaration.

The supplier page's incorrect “27.75 Wh” field (the same page otherwise says 0.74 Wh) is an additional reason to rely on a signed drawing rather than web copy. Adding an NTC may also consume the entire 6.0 mm thickness limit; approve measured samples before enclosure release.

## Delivery, tax and schedule conclusion

- [DigiKey Canada](https://www.digikey.ca/en/help-support/delivery-information/delivery-time-and-cost) says regular CAD orders are DDP, free-delivery above CAD 100, and usually reach Canada in about 24 hours after dispatch, with customs capable of adding delay. Marketplace material is separate, CPT, excluded from free freight, and has duty/customs/tax due on delivery.
- Mouser Canada presents CAD orders as DDP and says prices include duty/customs on select shipping methods; GST/PST remain applicable. The switch-only order is below its CAD 100 free-freight threshold.
- The Raytac eBay, LCSC and battery-supplier routes are cross-border shipments. Budget checkout freight, brokerage, GST and BC PST as applicable; do not apply the US-only 25% Vybronics tariff note to a Canadian landed-cost model. Lithium batteries may also attract dangerous-goods freight and carrier restrictions.

**Reject a two-week promise.** A 2026-09-12 arrival for exact, assembled EVT units is not credible: the DigiKey Marketplace AN54LV-15 alone takes approximately 14 days merely to dispatch; its official-linked eBay page showed a Sep 4–22 range for a generic displayed location rather than West Vancouver; the exact motor has no verified distributor stock; and the required NTC battery is a custom RFQ item with no published sample lead.

For planning only, late September/October is the first defensible **3-EVT** window *after* written motor allocation and custom-battery sample confirmation, plus PCB assembly and transit. It is not presently a commit date. The **50-unit** build is not schedulable today: obtain a direct Raytac allocation with spares and a written 50-pack exception/lead from LiPol first. If the battery requires new production, its published 6–7 week clock precedes assembly and shipping, making November 2026 an aggressive planning floor rather than a promise.
