anticipation-labs/anticipy-hardware/latest_builds/E1P1/sourcing/SMT_27_Group_Live_Stock_Refresh.md

# E1P1: complete SMT source refresh

**The selected BOM has 27 ordering groups and 47 fitted components per board. Live pages cover 26 groups for 20 boards plus two-board spares. The remaining group is U1: its 25 previously ordered modules are consignment candidates, with no verified usable count or assembler receipt. A complete 20-board kit has not been verified.**

Checked 9 September 2026, 13:57–13:59 UTC (09:57–09:59 Boston). Every row below was read from its live product page. This is source availability, not allocation, delivery, assembly acceptance, or a purchase. The selected native changes and packaging aliases must appear in the release BOM before ordering.

Quantities: **940 fitted SMT pieces for 20 boards; 1,034 with two-board spares**. The 94 extra pieces are optional and do not replace an assembler-specific feeder/leader/attrition requirement. Offboard battery, motor, NTC, harness, cases and programming/test tools are separate.

| References | Selected ordering MPN | 20 fitted | Optional spares | Live stock | Source / UTC |
|---|---|---:|---:|---:|---|
| R13 R7 R12 | RC0402FR-0710KL | 60 | 6 | 12,854,598 | [DigiKey US](https://www.digikey.com/en/products/detail/yageo/RC0402FR-0710KL/729470) / 13:57:28 |
| R6 | RC0402FR-07100KL | 20 | 2 | 8,088,185 | [DigiKey US](https://www.digikey.com/en/products/detail/yageo/RC0402FR-07100KL/726526) / 13:57:29 |
| C7 C8 C2 C4 C3 C10 C9 | GRM188R61E106MA73D | 140 | 14 | 299,202 | [DigiKey US](https://www.digikey.com/en/products/detail/murata-electronics/GRM188R61E106MA73D/3900497) / 13:58:21 |
| C6 | EMK107BB7225KA-T | 20 | 2 | 171,421 | [DigiKey US](https://www.digikey.com/en/products/detail/taiyo-yuden/EMK107BB7225KA-T/4970646) / 13:57:31 |
| U4 | TPD2EUSB30ADRTR | 20 | 2 | 80,460 | [DigiKey US](https://www.digikey.com/en/products/detail/texas-instruments/TPD2EUSB30ADRTR/2520830) / 13:58:44 |
| L1 L2 | CIGT201610EH2R2MNE | 40 | 4 | 178,231 | [DigiKey US](https://www.digikey.com/en/products/detail/samsung-electro-mechanics/CIGT201610EH2R2MNE/7041223) / 13:57:32 |
| U1 | MDBT50Q-1MV2 | 20 | 2 | 14 | [DigiKey Marketplace / Raytac](https://www.digikey.com/en/products/detail/raytac/MDBT50Q-1MV2/13677591) / 13:57:33 |
| R2 R1 | RC0201FR-0710KL | 40 | 4 | 6,044,695 | [DigiKey US](https://www.digikey.com/en/products/detail/yageo/RC0201FR-0710KL/1948870) / 13:57:34 |
| LED1 | APHB1608LVBDSEKJ3C | 20 | 2 | 17,539 | [DigiKey US](https://www.digikey.com/en/products/detail/kingbright/APHB1608LVBDSEKJ3C/5803645) / 13:57:46 |
| SW1 | B3U-1000P | 20 | 2 | 119,580 | [DigiKey US](https://www.digikey.com/en/products/detail/omron-electronics-inc-emc-div/B3U-1000P/1859107) / 13:57:48 |
| Q1 | AO3400A | 20 | 2 | 299,214 | [DigiKey US](https://www.digikey.com/en/products/detail/alpha-omega-semiconductor-inc/AO3400A/1855772) / 13:57:49 |
| U2 | NPM1300-QEAA-R | 20 | 2 | 12,229 | [DigiKey US](https://www.digikey.com/en/products/detail/nordic-semiconductor-asa/NPM1300-QEAA-R/19722479) / 13:57:07 |
| R5 R8 | RC0402FR-07100RL | 40 | 4 | 2,456,693 | [DigiKey US](https://www.digikey.com/en/products/detail/yageo/RC0402FR-07100RL/726527) / 13:57:50 |
| J1 | USB4500-03-1-A | 20 | 2 | 16,152 | [DigiKey US](https://www.digikey.com/en/products/detail/gct/USB4500-03-1-A/15283198) / 13:57:08 |
| C14 C15 C16 | C0402C104M4RACTU | 60 | 6 | 148,419 | [DigiKey US](https://www.digikey.com/en/products/detail/kemet/C0402C104M4RACTU/2196240) / 13:57:51 |
| C17 C19 C22 | C1005X7R1C104K050BC | 60 | 6 | 1,506,626 | [DigiKey US](https://www.digikey.com/en/products/detail/tdk-corporation/C1005X7R1C104K050BC/2093220) / 13:57:52 |
| D1 | 1N4148WS-13-F | 20 | 2 | 1,824 | [Mouser USA](https://www.mouser.com/en/ProductDetail/Diodes-Incorporated/1N4148WS-13-F?qs=uwE%252BXfKqZqTz4dP8PH7EKg%3D%3D) / 13:58 |
| C13 | C0603X5R1E104K030BB | 20 | 2 | 933,292 | [DigiKey US](https://www.digikey.com/en/products/detail/tdk-corporation/C0603X5R1E104K030BB/3950907) / 13:58:41 |
| U6 | TPD2E2U06DCKR | 20 | 2 | 34 | [DigiKey US](https://www.digikey.com/en/products/detail/texas-instruments/TPD2E2U06DCKR/11502208) / 13:57:09 |
| R11 R10 | CRCW02010000Z0ED | 40 | 4 | 5,915,370 | [DigiKey US](https://www.digikey.com/en/products/detail/vishay-dale/CRCW02010000Z0ED/1178434) / 13:58:22 |
| C26 C25 | GRM155R60J106ME15D | 40 | 4 | 1,368,074 | [DigiKey US](https://www.digikey.com/en/products/detail/murata-electronics/GRM155R60J106ME15D/5877401) / 13:58:23 |
| MIC1 | CMM-3424DT-26165-TR | 20 | 2 | 2,759 | [DigiKey US](https://www.digikey.com/en/products/detail/same-sky-formerly-cui-devices/CMM-3424DT-26165-TR/20380848) / 13:58:24 |
| C23 | GRM21BR60J476ME01L | 20 | 2 | 777 | [DigiKey US](https://www.digikey.com/en/products/detail/murata-electronics/GRM21BR60J476ME01L/10703358) / 13:58:43 |
| R3 R4 | RC0201FR-07150KL | 40 | 4 | 8,350 | [DigiKey US](https://www.digikey.com/en/products/detail/yageo/RC0201FR-07150KL/3202384) / 13:58:25 |
| D2 | ESD441DPYR | 20 | 2 | 2,613 | [DigiKey US](https://www.digikey.com/en/products/detail/texas-instruments/ESD441DPYR/28715599) / 13:58:26 |
| C1 C18 C5 | C1608X7R1C105K080AC | 60 | 6 | 1,548,727 | [DigiKey US](https://www.digikey.com/en/products/detail/tdk-corporation/C1608X7R1C105K080AC/634395) / 13:58:28 |
| U5 | MX35LF4GE4AD-Z4I | 20 | 2 | 2,339 | [DigiKey US](https://www.digikey.com/en/products/detail/macronix/MX35LF4GE4AD-Z4I/18110032) / 13:57:10 |

## The actionable exceptions

- **U1 / MDBT50Q-1MV2:** DigiKey lists 14 via Raytac Marketplace and approximately 14 days to dispatch. This is neither enough quantity nor the Saturday route. Find and count the 25 previously ordered modules, preserve lot/moisture packaging, and transport an accepted kit to the assembler. Do not automatically repurchase them. Adafruit product 4078, which identifies this exact module, is currently out of stock; no verified domestic replacement stock for 20 was found in this bounded pass.
- **U6 / TPD2E2U06DCKR:** DigiKey has only34, but [Mouser USA](https://www.mouser.com/en/ProductDetail/Texas-Instruments/TPD2E2U06DCKR?qs=xZ%2FP%252ba9zWqa9UMTS1HgCWA%3D%3D) was live **107**, **Can Ship Immediately**, **USD0.268 each at10+**, around13:59UTC. This is the exact MPN, not a substitution. It can be sourced alongside D1 if still available. A dispatch statement does not reserve these units.
- **D1 / 1N4148WS-13-F:** live Mouser quantity1,824 and immediate-dispatch statement are reconfirmed. The -13 versus -7 code is the documented reel-package option, same SOD323 device. Cut tape is available, minimum1; no10,000-piece reel is required.
- DigiKey displays a high-volume processing warning that may add **one business day**. An in-stock page is insufficient to promise Boston arrival or a completed assembly by Saturday.

## Purchased-parts evidence and the correct credit

The saved `outputs/Anticipy_Boston_Procurement_2026-09-08/evidence/Live_Order_and_Delivery_Verification.json` was checked at00:58UTC on9September. It records a TME package of25 invoiced Raytac modules, carrier-delivered in British Columbia on3September at16:17UTC−0700. The companion `Updated_Inventory.json` explicitly keeps usable physical count null and Boston availability unverified. The DigiKey package containing25 invoiced AO3400A and20 invoiced B3U-1000P was carrier-delivered to West Vancouver on1September at12:25. This pass read that saved evidence; it did not perform a fresh carrier lookup or open/count packages.

Treat these three groups as **carrier-delivered consignment candidates**, not as an accepted production kit. If all are counted, usable and received by the assembler, fitted20 needs no new U1/Q1/SW1 purchases; optional22 needs two additional switches. The JSON carries conditional quantities while leaving actual usable stock and assembler receipt unknown. No private email IDs or tracking links are reproduced here.

## Selection traceability

- Packaging/ordering changes already supported by manufacturer documentation: GRM188R61E106MA73J→GRM188R61E106MA73D; C0402C104M4RAC7867→C0402C104M4RACTU; 1N4148WS-7-F→1N4148WS-13-F.
- Engineering selections in this release pass: U4 TPD2EUSB30ADRTR; C17/C19/C22 C1005X7R1C104K050BC; C13 C0603X5R1E104K030BB; C23 GRM21BR60J476ME01L. See the separate USB and passive component decision reports; these are not all mere package aliases.
- C6 EMK107BB7225KA-T is an actual active exact listing, live171,421. nPM1300-QEAA-R live12,229 and USB4500-03-1-A live16,152 are actual exact listings. No further invalid ordering code was found in these27 selected groups.
- Only MIC1 is fitted; do not purchase or install MIC2 for this population. The native BOM remains the placement authority.

**Release use:** this report completes the source-selection audit for the chosen design. Purchasing must reconfirm and allocate stock, and the assembler must receive the complete kit. It does not assert physical qualification or a Saturday production commitment. No supplier email, order, or file upload was sent.
