anticipation-labs/anticipy-hardware/03_PCB/R0B_CHECKPOINT_NOT_FOR_FAB/07_Messages/SUPPLIER_CONTACTS.md

# Verified supplier and engineering contacts

Verified on 2026-08-29 from official company pages.

| Organization | Use | Contact |
|---|---|---|
| CCI Canadian Circuits, Surrey | Primary rush PCB/PCBA capability request | `sales@canadiancircuits.com`, 604-599-8600, https://www.canadiancircuits.com/contact/ |
| Enigma Interconnect, Burnaby | Local bare-board backup | `boards@enigmacorp.com`, 604-420-3313, https://www.enigmacorp.com/quote |
| MistyWest, Vancouver | Full-service hardware engineering option | `contact@mistywest.com`, 604-292-7036, https://www.mistywest.com/contact/ |

These contacts are leads, not booked commitments. Ask for written confirmation of scope, owner, start time, price, material stock, and exact delivery date.
