anticipation-labs/anticipy-hardware/03_PCB/R0B_CHECKPOINT_NOT_FOR_FAB/00_Master_Guide/Anticipy_Project_Control.xlsx

Sheet: Overview
Anticipy R0B Project Control | Anticipy R0B Project Control | Anticipy R0B Project Control | Anticipy R0B Project Control | Anticipy R0B Project Control | Anticipy R0B Project Control
Release ANT-PROD-R0B-EVT-HANDOFF-2026-08-29 | Engineering WIP | Not approved for fabrication | Release ANT-PROD-R0B-EVT-HANDOFF-2026-08-29 | Engineering WIP | Not approved for fabrication | Release ANT-PROD-R0B-EVT-HANDOFF-2026-08-29 | Engineering WIP | Not approved for fabrication | Release ANT-PROD-R0B-EVT-HANDOFF-2026-08-29 | Engineering WIP | Not approved for fabrication | Release ANT-PROD-R0B-EVT-HANDOFF-2026-08-29 | Engineering WIP | Not approved for fabrication | Release ANT-PROD-R0B-EVT-HANDOFF-2026-08-29 | Engineering WIP | Not approved for fabrication
Metric | Current state
Fabrication status | BLOCKED
Board outline | 45.8 x 18.0 mm
PCB target | 4 layers, 0.80 mm
Provisional STEP | 0.82 mm - reconcile
Unrouted connections | 176
Open release gates | 18
Missing deliverables | 8
DO NOT upload the current KiCad board to a factory. A zero DRC violation count does not mean the board is routed; 176 unconnected items remain. | DO NOT upload the current KiCad board to a factory. A zero DRC violation count does not mean the board is routed; 176 unconnected items remain. | DO NOT upload the current KiCad board to a factory. A zero DRC violation count does not mean the board is routed; 176 unconnected items remain. | DO NOT upload the current KiCad board to a factory. A zero DRC violation count does not mean the board is routed; 176 unconnected items remain. | DO NOT upload the current KiCad board to a factory. A zero DRC violation count does not mean the board is routed; 176 unconnected items remain. | DO NOT upload the current KiCad board to a factory. A zero DRC violation count does not mean the board is routed; 176 unconnected items remain.
Immediate action | Owner | Status | Deadline | Evidence | Stop condition
Hire one accountable senior PCB lead | Omar | Open | Day 0 | Written acceptance and start time | No named owner
Select exact protected battery | PCB Lead | Open | Day 1 | Controlled drawing, sample and compliance file | Any missing battery evidence
Send capability RFQs without manufacturing release | Omar | Open | Day 0 | Written stack-up, stock and schedule | Factory assumes current files are released
Assign firmware and mechanical owners | Omar | Open | Day 0 | Named owners and availability | No bring-up or enclosure owner
Finish routing and Gate 0 review | PCB Lead | Open | Day 1-2 | Zero unconnected/ERC/DRC and release ZIP | Any unresolved engineering gate

Sheet: Gates
Release Gates | Release Gates | Release Gates | Release Gates | Release Gates | Release Gates
Every open row blocks the next release stage unless the exact evidence field is complete. | Every open row blocks the next release stage unless the exact evidence field is complete. | Every open row blocks the next release stage unless the exact evidence field is complete. | Every open row blocks the next release stage unless the exact evidence field is complete. | Every open row blocks the next release stage unless the exact evidence field is complete. | Every open row blocks the next release stage unless the exact evidence field is complete.
Gate ID | Phase | Requirement | Owner | Status | Required evidence / notes
G0-01 | P0 | Approve exact protected 3-wire battery and evidence | PCB Lead + Anticipy | Open | MPN, max drawing/STEP, protection, 10k NTC, polarity, limits, UN38.3, IEC 62133 evidence, MSDS, sample and stock
G0-02 | P0 | Complete and manually review every PCB connection | PCB Lead | Open | 176 unrouted connections at handoff
G0-03 | P0 | Review nPM1300 loops and grounds against Nordic reference | PCB Lead | Open | Signed schematic/layout review
G0-04 | P0 | Approve fabricator 0.80 mm stack and USB geometry | PCB Lead + Factory | Open | Stack-up, Dk, copper, dielectric, width/gap, coupon and TDR
G0-05 | P0 | Resolve 0.80 mm target versus 0.82 mm STEP export | PCB Lead + Mechanical | Open | Written thickness disposition
G0-06 | P0 | Close ERC, DRC, net-equivalence and unconnected reports | PCB Lead | Open | Zero unresolved errors and zero unconnected items
G0-07 | P0 | Generate and collision-review final PCBA STEP | PCB Lead + Mechanical | Open | Released STEP with maximum-height bodies
G0-08 | P0 | Generate dated checksummed manufacturing release | PCB Lead | Open | Gerbers, drills, IPC-356, BOM, CPL, drawings, STEP and README
GA-01 | Gate A | Bring up FA-001 and FA-002 with current limit | PCB + Firmware | Open | Rail/current/thermal logs
GA-02 | Gate A | Pass USB in both plug orientations | Firmware Lead | Open | Power, CC, enumeration and data transfer
GA-03 | Gate A | Pass BLE security, control and transfer | Firmware Lead | Open | RSSI and packet-loss record
GA-04 | Gate A | Pass both microphone channels and coexistence | Firmware + Audio | Open | Noise/tone/speech and haptic/BLE interference records
GA-05 | Gate A | Pass NAND ECC, bad-block and power-fail tests | Firmware Lead | Open | Write/read/hash, recovery, erase and near-capacity records
GA-06 | Gate A | Pass approved battery and charging tests | PCB Lead | Open | NTC, charge current, termination, protection and thermal logs
GA-07 | Gate A | Issue written remaining-ten release | Anticipy Approver | Open | Two passing serials and exact release checksums
GB-01 | Gate B | Pass final enclosure fit and retention | Mechanical Lead | Open | No collision, rattle, chafe or battery movement
GB-02 | Gate B | Pass sealed-unit acoustic and RF tests | Mechanical + Firmware | Open | Audio and BLE limits in worn/free-space orientations
GB-03 | Gate B | Pass sealed-unit charge, drop and runtime | QA Lead | Open | Thermal, overnight recording, backfill and drop records

Sheet: Deliverables
Deliverables Register | Deliverables Register | Deliverables Register | Deliverables Register | Deliverables Register
Present does not mean released. Use the status and notes columns before sending any file downstream. | Present does not mean released. Use the status and notes columns before sending any file downstream. | Present does not mean released. Use the status and notes columns before sending any file downstream. | Present does not mean released. Use the status and notes columns before sending any file downstream. | Present does not mean released. Use the status and notes columns before sending any file downstream.
Deliverable | Owner | Status | Location | Release note
Native KiCad project | PCB Lead | Present - WIP | 01_Electrical_Source | Editable but unrouted
Custom footprint library | PCB Lead | Present - verify | 01_Electrical_Source/Anticipy_R0B.pretty | Manufacturer review required
Draft BOM | PCB Lead + Procurement | Present - draft | BOM_DRAFT_DO_NOT_PROCURE.csv | Battery is TBD
Provisional board STEP/DXF | Mechanical Lead | Present - provisional | 02_Mechanical_CAD | Board only; STEP reports 0.82 mm
Released Gerbers and drills | PCB Lead | Missing | Future release | Blocked by routing/review
Released BOM and CPL | PCB Lead | Missing | Future release | Requires availability and final layout
Fab/assembly drawings + IPC-356 | PCB Lead | Missing | Future release | Requires final native source
Final PCBA STEP | PCB Lead | Missing | Future release | Requires full 3D bodies
Exact battery STEP/drawing | Battery Supplier + PCB Lead | Missing | Future release | Hard safety and fit gate
Production/factory firmware | Firmware Lead | Missing | Future release | Source, binary, hash and test commands
Final enclosure CAD/DXFs | Mechanical Lead | Missing | Future release | Requires PCBA and battery STEP
Assembly traveler | Mechanical + Integrator | Missing | Future release | Adhesive, cure, inspection and tests

Sheet: 7-Day Plan
Seven-Day Rush Plan | Seven-Day Rush Plan | Seven-Day Rush Plan | Seven-Day Rush Plan | Seven-Day Rush Plan | Seven-Day Rush Plan
A target, not a promise: one to five working EVT units is the practical success range if revision one works. | A target, not a promise: one to five working EVT units is the practical success range if revision one works. | A target, not a promise: one to five working EVT units is the practical success range if revision one works. | A target, not a promise: one to five working EVT units is the practical success range if revision one works. | A target, not a promise: one to five working EVT units is the practical success range if revision one works. | A target, not a promise: one to five working EVT units is the practical success range if revision one works.
Day | PCB / electrical | Mechanical | Firmware / test | Manufacturing / integration | Exit gate
0 | Hire PCB lead; review blockers | Start packaging study | Freeze bring-up plan | Send RFQs; reserve capacity | Named owners and written availability
1 | Battery decision; finish routing/review | Develop centre/face concept | Bench image and SWD plan | Factory returns stack-up and stock | Gate 0 release candidate
2 | Release only if every check passes | Update from released PCBA STEP | Release hashed FA firmware | Start exactly two first articles | Checksummed manufacturing release
3 | Support DFM/CAM | Fit and tolerance review | Prepare fixture and scripts | Fabricate/assemble FA-001/002 | No unapproved exception
4 | Lead current-limited bring-up | Correct fit issues | USB/BLE/audio/storage tests | Provide AOI/X-ray evidence | Both open-board FAs pass
5 | Close faults or approve remaining ten | Freeze enclosure after evidence | Freeze passed firmware hash | Assemble ten only after release | Written remaining-ten release
6 | Support integration faults | Produce/finish enclosure parts | Sealed regression | Integrate two sealed FAs | Both sealed FAs pass
7 | Final disposition | Final corrections | Runtime/backfill review | Integrate passed units; serialize | Passed units only

Sheet: Contacts
Contacts | Contacts | Contacts | Contacts | Contacts | Contacts
Verified from official company pages on 2026-08-29. Capability and schedule are not commitments until confirmed in writing. | Verified from official company pages on 2026-08-29. Capability and schedule are not commitments until confirmed in writing. | Verified from official company pages on 2026-08-29. Capability and schedule are not commitments until confirmed in writing. | Verified from official company pages on 2026-08-29. Capability and schedule are not commitments until confirmed in writing. | Verified from official company pages on 2026-08-29. Capability and schedule are not commitments until confirmed in writing. | Verified from official company pages on 2026-08-29. Capability and schedule are not commitments until confirmed in writing.
Organization | Use | Email | Phone | Official URL | Status
CCI Canadian Circuits | Primary rush PCB/PCBA capability request | sales@canadiancircuits.com | 604-599-8600 | https://www.canadiancircuits.com/contact/ | Not booked
Enigma Interconnect | Local bare-board backup | boards@enigmacorp.com | 604-420-3313 | https://www.enigmacorp.com/quote | Not booked
MistyWest | Full-service Vancouver hardware engineering option | contact@mistywest.com | 604-292-7036 | https://www.mistywest.com/contact/ | Not booked

Sheet: BOM Draft
Draft BOM - DO NOT PROCURE | Draft BOM - DO NOT PROCURE | Draft BOM - DO NOT PROCURE | Draft BOM - DO NOT PROCURE | Draft BOM - DO NOT PROCURE | Draft BOM - DO NOT PROCURE | Draft BOM - DO NOT PROCURE | Draft BOM - DO NOT PROCURE | Draft BOM - DO NOT PROCURE
Battery is a non-orderable placeholder and every row remains subject to final engineering and availability review. | Battery is a non-orderable placeholder and every row remains subject to final engineering and availability review. | Battery is a non-orderable placeholder and every row remains subject to final engineering and availability review. | Battery is a non-orderable placeholder and every row remains subject to final engineering and availability review. | Battery is a non-orderable placeholder and every row remains subject to final engineering and availability review. | Battery is a non-orderable placeholder and every row remains subject to final engineering and availability review. | Battery is a non-orderable placeholder and every row remains subject to final engineering and availability review. | Battery is a non-orderable placeholder and every row remains subject to final engineering and availability review. | Battery is a non-orderable placeholder and every row remains subject to final engineering and availability review.
reference | quantity_per_board | value | manufacturer | mpn | footprint | side | description | datasheet
U1 | 1 | MDBT50Q-1MV2 | Raytac | MDBT50Q-1MV2 | Anticipy_R0B:Raytac_MDBT50Q_R0B | Top | Certified nRF52840 module; rotation 0 puts antenna at the top board edge | https://www.raytac.com/download/index.php?index_id=43
U2 | 1 | nPM1300 | Nordic Semiconductor | NPM1300-QEAA-R | Package_DFN_QFN:QFN-32-1EP_5x5mm_P0.5mm_EP3.45x3.45mm | Top | PMIC, USB charger, two bucks, two LDO/load switches | https://docs.nordicsemi.com/bundle/ps_npm1300/
U3 | 1 | LIS2DW12TR | STMicroelectronics | LIS2DW12TR | Package_LGA:LGA-12_2x2mm_P0.5mm | Top | Low-power accelerometer, I2C, SA0 low | https://www.st.com/resource/en/datasheet/lis2dw12.pdf
U4 | 1 | TPD2EUSB30DRTR | Texas Instruments | TPD2EUSB30DRTR | Anticipy_R0B:Texas_DRT-3_R0B | Top | USB 2.0 data-line ESD protection | https://www.ti.com/lit/ds/symlink/tpd2eusb30.pdf
U6 | 1 | TPD2E2U06DCKR | Texas Instruments | TPD2E2U06DCKR | Package_TO_SOT_SMD:SOT-323_SC-70 | Top | Connector-side 5.5-V CC1/CC2 shunt ESD protection; no series impedance | https://www.ti.com/lit/gpn/TPD2E2U06
U5 | 1 | MX35LF4GE4AD-Z4I | Macronix | MX35LF4GE4AD-Z4I | Package_SON:WSON-8-1EP_8x6mm_P1.27mm_EP3.4x4.3mm | Top | 4-Gbit SLC serial NAND; firmware needs ECC, bad-block and power-loss handling | https://www.macronix.com/Lists/Datasheet/Attachments/9047/MX35LF4GE4AD%2C%203V%2C%204Gb%2C%20v1.6.pdf
MIC1 | 1 | CMM-3424DT-26165-TR | Same Sky | CMM-3424DT-26165-TR | Anticipy_R0B:SameSky_CMM-3424DT-26165-TR_TopPort_PDM | Top | Front-side top-port IP67 PDM microphone; SELECT low | https://www.sameskydevices.com/product/resource/cmm-3424dt-26165-tr.pdf
MIC2 | 1 | CMM-3424DT-26165-TR | Same Sky | CMM-3424DT-26165-TR | Anticipy_R0B:SameSky_CMM-3424DT-26165-TR_TopPort_PDM | Top | Front-side top-port IP67 PDM microphone; SELECT high | https://www.sameskydevices.com/product/resource/cmm-3424dt-26165-tr.pdf
J1 | 1 | USB4500-03-1-A | GCT | USB4500-03-1-A | Anticipy_R0B:USB_C_Receptacle_GCT_USB4500-03-1-A_MidMount | Top | 0.8-mm mid-mount USB-C; 12 grouped contacts plus four plated shell stakes | https://gct.co/connector/usb4500
BT1 | 1 | PROVISIONAL <=26x15.5x4.8mm PROTECTED 10kNTC | TBD | BATTERY-TBD-3WIRE | Anticipy_R0B:Battery_LiPo_3Wire_Solder_26x15.5 | Rear / hand solder | DO NOT SOURCE: exact protected three-wire pack, controlled max-tolerance drawing, polarity, 10k NTC configuration, UN38.3/IEC62133/MSDS, stock and runtime are release gates
SW1 | 1 | B3U-1000P | Omron | B3U-1000P | Button_Switch_SMD:SW_SPST_B3U-1000P | Top | Hard reset / ship-hold button; intentionally not tied to MCU
LED1 | 1 | APHB1608LVBDSEKJ3C | Kingbright | APHB1608LVBDSEKJ3C | Anticipy_R0B:LED_Kingbright_APHB1608LVBDSEKJ3C | Top | Red/blue status LED on nPM1300 fixed 5-mA sinks; blue low-battery brightness is a first-article gate | https://www.kingbrightusa.com/images/catalog/SPEC/APHB1608LVBDSEKJ3C.pdf
Q1 | 1 | AO3400A | Alpha & Omega Semiconductor | AO3400A | Package_TO_SOT_SMD:SOT-23 | Top | Low-side haptic MOSFET
D1 | 1 | 1N4148WS-7-F | Diodes Incorporated | 1N4148WS-7-F | Diode_SMD:D_SOD-323 | Top | Active-lifecycle haptic flyback diode; KiCad pad 1 is cathode | https://www.diodes.com/assets/Datasheets/ds12019.pdf
D2 | 1 | ESD441DPYR | Texas Instruments | ESD441DPYR | Anticipy_R0B:TI_DPY0002A_X1SON | Top | Connector-side 5.5-V VBUS shunt ESD/surge protector; TI DPY0002A land pattern | https://www.ti.com/lit/gpn/ESD441
M1 | 1 | VCLP1020B002L | Vybronics | VCLP1020B002L | Anticipy_R0B:Haptic_VCLP1020B002L_WirePads | Rear / hand solder | 10-mm coin haptic, hand soldered
NT1 | 1 | PVSS1-GND | Anticipy | NETTIE | NetTie:NetTie-2_SMD_Pad0.5mm | Top | Single-point buck-1 power-ground tie
NT2 | 1 | PVSS2-GND | Anticipy | NETTIE | NetTie:NetTie-2_SMD_Pad0.5mm | Top | Single-point buck-2 power-ground tie
L1 | 1 | 2.2uH | Samsung Electro-Mechanics | CIGT201610EH2R2MNE | Inductor_SMD:L_Murata_DFE201610P | Top | Buck-1 inductor
L2 | 1 | 2.2uH | Samsung Electro-Mechanics | CIGT201610EH2R2MNE | Inductor_SMD:L_Murata_DFE201610P | Top | Buck-2 inductor
R1 | 1 | 10k 1% | Yageo | RC0201FR-0710KL | Resistor_SMD:R_0201_0603Metric | Top | I2C pull-up
R2 | 1 | 10k 1% | Yageo | RC0201FR-0710KL | Resistor_SMD:R_0201_0603Metric | Top | I2C pull-up
R3 | 1 | 330k 1% | Yageo | RC0201FR-07330KL | Resistor_SMD:R_0201_0603Metric | Top | Buck-1 starts at 2.7 V; firmware raises 3V_MAIN to 3.0 V
R4 | 1 | 150k 1% | Yageo | RC0201FR-07150KL | Resistor_SMD:R_0201_0603Metric | Top | Buck-2 starts at 3.0 V
R5 | 1 | 100R 1% | Yageo | RC0402FR-07100RL | Resistor_SMD:R_0402_1005Metric | Top | MOSFET gate resistor
R6 | 1 | 100k 1% | Yageo | RC0402FR-07100KL | Resistor_SMD:R_0402_1005Metric | Top | MOSFET gate pulldown
R7 | 1 | 100k 1% | Yageo | RC0402FR-07100KL | Resistor_SMD:R_0402_1005Metric | Top | Flash chip-select default high
R8 | 1 | 100R 1% | Yageo | RC0402FR-07100RL | Resistor_SMD:R_0402_1005Metric | Top | PDM source isolation
R9 | 1 | 100R 1% | Yageo | RC0402FR-07100RL | Resistor_SMD:R_0402_1005Metric | Top | PDM source isolation
R10 | 1 | 27R 1% | Vishay Dale | CRCW020127R0FNED | Resistor_SMD:R_0201_0603Metric | Top | Raytac-recommended USB D+ series resistor
R11 | 1 | 27R 1% | Vishay Dale | CRCW020127R0FNED | Resistor_SMD:R_0201_0603Metric | Top | Raytac-recommended USB D- series resistor
C1 | 1 | 1uF 16V X7R | TDK | C1608X7R1C105K080AC | Capacitor_SMD:C_0603_1608Metric | Top | PMIC VBUS input
C2 | 1 | 10uF 25V X5R | Murata | GRM188R61E106MA73J | Capacitor_SMD:C_0603_1608Metric | Top | Buck-1 PVDD local return
C3 | 1 | 10uF 25V X5R | Murata | GRM188R61E106MA73J | Capacitor_SMD:C_0603_1608Metric | Top | Buck-2 PVDD local return
C4 | 1 | 10uF 25V X5R | Murata | GRM188R61E106MA73J | Capacitor_SMD:C_0603_1608Metric | Top | System rail bulk
C5 | 1 | 1uF 16V X7R | TDK | C1608X7R1C105K080AC | Capacitor_SMD:C_0603_1608Metric | Top | Protected USB output bypass
C6 | 1 | 2.2uF 16V X7R | Taiyo Yuden | EMK107BB7225KA-T | Capacitor_SMD:C_0603_1608Metric | Top | Battery input bypass
C7 | 1 | 10uF 25V X5R | Murata | GRM188R61E106MA73J | Capacitor_SMD:C_0603_1608Metric | Top | Buck-1 output
C8 | 1 | 10uF 25V X5R | Murata | GRM188R61E106MA73J | Capacitor_SMD:C_0603_1608Metric | Top | Buck-2 output
C9 | 1 | 10uF 25V X5R | Murata | GRM188R61E106MA73J | Capacitor_SMD:C_0603_1608Metric | Top | System rail second bulk
C10 | 1 | 10uF 25V X5R | Murata | GRM188R61E106MA73J | Capacitor_SMD:C_0603_1608Metric | Top | Microphone LDO output
C13 | 1 | 100nF 16V X5R | TDK | C0603X5R1C104K030BC | Capacitor_SMD:C_0201_0603Metric | Top | PMIC logic bypass; Nordic QEAA 0201 assembler gate
C14 | 1 | 100nF 16V X7R | KEMET | C0402C104M4RAC7867 | Capacitor_SMD:C_0402_1005Metric | Top | Buck-1 high-frequency input bypass; Nordic QEAA ref 1.2
C15 | 1 | 100nF 16V X7R | KEMET | C0402C104M4RAC7867 | Capacitor_SMD:C_0402_1005Metric | Top | Buck-2 high-frequency input bypass; Nordic QEAA ref 1.2
C16 | 1 | 100nF 16V X7R | KEMET | C0402C104M4RAC7867 | Capacitor_SMD:C_0402_1005Metric | Top | System high-frequency bypass; Nordic QEAA ref 1.2
C17 | 1 | 100nF 10V X7R | TDK | C1005X7R1A104K050BC | Capacitor_SMD:C_0402_1005Metric | Top | Flash local bypass
C18 | 1 | 1uF 16V X7R | TDK | C1608X7R1C105K080AC | Capacitor_SMD:C_0603_1608Metric | Top | Flash local bulk
C19 | 1 | 100nF 10V X7R | TDK | C1005X7R1A104K050BC | Capacitor_SMD:C_0402_1005Metric | Top | MIC1 local bypass
C20 | 1 | 100nF 10V X7R | TDK | C1005X7R1A104K050BC | Capacitor_SMD:C_0402_1005Metric | Top | MIC2 local bypass
C21 | 1 | 100nF 16V X5R | TDK | C0603X5R1C104K030BC | Capacitor_SMD:C_0201_0603Metric | Top | Accelerometer VDD local bypass
C22 | 1 | 100nF 10V X7R | TDK | C1005X7R1A104K050BC | Capacitor_SMD:C_0402_1005Metric | Top | Motor brush-noise capacitor
C23 | 1 | 47uF 6.3V X5R | Yageo | CC0805MKX5R5BB476 | Capacitor_SMD:C_0805_2012Metric | Top | Haptic rail bulk
C24 | 1 | 10uF 25V X5R | Murata | GRM188R61E106MA73J | Capacitor_SMD:C_0603_1608Metric | Top | Accelerometer local bulk
C25 | 1 | 10uF 6.3V X5R | Murata | GRM155R60J106ME15D | Capacitor_SMD:C_0402_1005Metric | Top | Raytac VDD/VDDH local bulk; effective capacitance is a first-article gate
C26 | 1 | 10uF 6.3V X5R | Murata | GRM155R60J106ME15D | Capacitor_SMD:C_0402_1005Metric | Top | Raytac VBUS local bulk; effective capacitance is a first-article gate
C27 | 1 | 100nF 16V X5R | TDK | C0603X5R1C104K030BC | Capacitor_SMD:C_0201_0603Metric | Top | Accelerometer VDDIO local bypass
