anticipation-labs/anticipy-hardware/03_PCB/R0B_CHECKPOINT_NOT_FOR_FAB/01_Electrical_Source/pad_net_report.csv

reference | value | pad | net | x_mm | y_mm | side
BT1 | PROVISIONAL <=26x15.5x4.8mm PROTECTED 10kNTC | 3 | GND | 54.4000 | 30.0700 | B
BT1 | PROVISIONAL <=26x15.5x4.8mm PROTECTED 10kNTC | 2 | NTC | 54.4000 | 28.8000 | B
BT1 | PROVISIONAL <=26x15.5x4.8mm PROTECTED 10kNTC | 1 | VBAT | 54.4000 | 27.5300 | B
C1 | 1uF 16V X7R | 1 | VBUS | 29.5000 | 30.8000 | F
C1 | 1uF 16V X7R | 2 | GND | 29.5000 | 29.2500 | F
C10 | 10uF 25V X5R | 1 | 3V_MIC | 34.6000 | 34.8750 | F
C10 | 10uF 25V X5R | 2 | GND | 34.6000 | 33.3250 | F
C13 | 100nF 16V X5R |  |  | 35.8000 | 24.9450 | F
C13 | 100nF 16V X5R |  |  | 35.8000 | 24.2550 | F
C13 | 100nF 16V X5R | 1 | 3V_MAIN | 35.8000 | 24.9200 | F
C13 | 100nF 16V X5R | 2 | GND | 35.8000 | 24.2800 | F
C14 | 100nF 16V X7R | 1 | VSYS | 39.1450 | 31.9000 | F
C14 | 100nF 16V X7R | 2 | PVSS1 | 40.1050 | 31.9000 | F
C15 | 100nF 16V X7R | 1 | VSYS | 39.1450 | 25.8000 | F
C15 | 100nF 16V X7R | 2 | PVSS2 | 40.1050 | 25.8000 | F
C16 | 100nF 16V X7R | 1 | VSYS | 30.7500 | 28.1550 | F
C16 | 100nF 16V X7R | 2 | GND | 30.7500 | 27.1950 | F
C17 | 100nF 10V X7R | 1 | 3V_FLASH | 53.2500 | 31.7300 | F
C17 | 100nF 10V X7R | 2 | GND | 53.2500 | 30.7700 | F
C18 | 1uF 16V X7R | 1 | 3V_FLASH | 53.3000 | 29.5750 | F
C18 | 1uF 16V X7R | 2 | GND | 53.3000 | 28.0250 | F
C19 | 100nF 10V X7R | 1 | 3V_MIC | 44.8200 | 26.8000 | F
C19 | 100nF 10V X7R | 2 | GND | 45.7800 | 26.8000 | F
C2 | 10uF 25V X5R | 1 | VSYS | 40.0250 | 30.9250 | F
C2 | 10uF 25V X5R | 2 | PVSS1 | 40.0250 | 29.3750 | F
C20 | 100nF 10V X7R | 1 | 3V_MIC | 49.6200 | 26.8000 | F
C20 | 100nF 10V X7R | 2 | GND | 50.5800 | 26.8000 | F
C21 | 100nF 16V X5R |  |  | 49.4550 | 38.2000 | F
C21 | 100nF 16V X5R |  |  | 50.1450 | 38.2000 | F
C21 | 100nF 16V X5R | 1 | 3V_MAIN | 49.4800 | 38.2000 | F
C21 | 100nF 16V X5R | 2 | GND | 50.1200 | 38.2000 | F
C22 | 100nF 10V X7R | 1 | 3V_MAIN | 39.5200 | 36.8000 | F
C22 | 100nF 10V X7R | 2 | HAPTIC_NEG | 40.4800 | 36.8000 | F
C23 | 47uF 6.3V X5R | 1 | 3V_MAIN | 36.3500 | 36.8000 | F
C23 | 47uF 6.3V X5R | 2 | GND | 38.2500 | 36.8000 | F
C24 | 10uF 25V X5R | 1 | 3V_MAIN | 53.3500 | 37.3750 | F
C24 | 10uF 25V X5R | 2 | GND | 53.3500 | 35.8250 | F
C25 | 10uF 6.3V X5R | 1 | 3V_MAIN | 58.0200 | 38.0000 | F
C25 | 10uF 6.3V X5R | 2 | GND | 58.9800 | 38.0000 | F
C26 | 10uF 6.3V X5R | 1 | VBUSOUT | 63.0200 | 38.0000 | F
C26 | 10uF 6.3V X5R | 2 | GND | 63.9800 | 38.0000 | F
C27 | 100nF 16V X5R |  |  | 51.1550 | 38.2000 | F
C27 | 100nF 16V X5R |  |  | 51.8450 | 38.2000 | F
C27 | 100nF 16V X5R | 1 | 3V_MAIN | 51.1800 | 38.2000 | F
C27 | 100nF 16V X5R | 2 | GND | 51.8200 | 38.2000 | F
C3 | 10uF 25V X5R | 1 | VSYS | 40.0250 | 26.7750 | F
C3 | 10uF 25V X5R | 2 | PVSS2 | 40.0250 | 28.3250 | F
C4 | 10uF 25V X5R | 1 | VSYS | 29.5000 | 26.6250 | F
C4 | 10uF 25V X5R | 2 | GND | 29.5000 | 28.1750 | F
C5 | 1uF 16V X7R | 1 | VBUSOUT | 30.7000 | 31.4250 | F
C5 | 1uF 16V X7R | 2 | GND | 30.7000 | 29.8750 | F
C6 | 2.2uF 16V X7R | 1 | VBAT | 29.4000 | 25.5000 | F
C6 | 2.2uF 16V X7R | 2 | GND | 30.9500 | 25.5000 | F
C7 | 10uF 25V X5R | 1 | 3V_MAIN | 39.9250 | 32.9500 | F
C7 | 10uF 25V X5R | 2 | PVSS1 | 41.4750 | 32.9500 | F
C8 | 10uF 25V X5R | 1 | 3V_FLASH | 41.1500 | 25.7500 | F
C8 | 10uF 25V X5R | 2 | PVSS2 | 42.7000 | 25.7500 | F
C9 | 10uF 25V X5R | 1 | VSYS | 33.4000 | 34.8750 | F
C9 | 10uF 25V X5R | 2 | GND | 33.4000 | 33.3250 | F
D1 | 1N4148WS-7-F | 1 | 3V_MAIN | 41.3000 | 35.0000 | F
D1 | 1N4148WS-7-F | 2 | HAPTIC_NEG | 43.4000 | 35.0000 | F
D2 | ESD441DPYR | 2 | GND | 28.7500 | 32.7500 | F
D2 | ESD441DPYR | 1 | VBUS | 28.0500 | 32.7500 | F
J1 | USB4500-03-1-A | S4 | GND | 21.6000 | 24.3800 | F
J1 | USB4500-03-1-A | S3 | GND | 21.6000 | 35.6200 | F
J1 | USB4500-03-1-A | S2 | GND | 25.6000 | 24.3800 | F
J1 | USB4500-03-1-A | S1 | GND | 25.6000 | 35.6200 | F
J1 | USB4500-03-1-A | 12 | GND | 26.7500 | 26.8000 | F
J1 | USB4500-03-1-A | 11 | VBUS | 26.7500 | 27.6000 | F
J1 | USB4500-03-1-A | 10 | USB_CC2 | 26.7500 | 28.2500 | F
J1 | USB4500-03-1-A | 9 |  | 26.7500 | 28.7500 | F
J1 | USB4500-03-1-A | 8 | USB_D+ | 26.7500 | 29.2500 | F
J1 | USB4500-03-1-A | 7 | USB_D- | 26.7500 | 29.7500 | F
J1 | USB4500-03-1-A | 6 | USB_D+ | 26.7500 | 30.2500 | F
J1 | USB4500-03-1-A | 5 | USB_D- | 26.7500 | 30.7500 | F
J1 | USB4500-03-1-A | 4 | USB_CC1 | 26.7500 | 31.2500 | F
J1 | USB4500-03-1-A | 3 |  | 26.7500 | 31.7500 | F
J1 | USB4500-03-1-A | 2 | VBUS | 26.7500 | 32.4000 | F
J1 | USB4500-03-1-A | 1 | GND | 26.7500 | 33.2000 | F
L1 | 2.2uH | 1 | 3V_MAIN | 41.9000 | 31.3500 | F
L1 | 2.2uH | 2 | SW1 | 41.9000 | 29.9000 | F
L2 | 2.2uH | 1 | 3V_FLASH | 43.1250 | 27.5750 | F
L2 | 2.2uH | 2 | SW2 | 41.6750 | 27.5750 | F
LED1 | APHB1608LVBDSEKJ3C | 4 | VSYS | 33.4000 | 37.0500 | F
LED1 | APHB1608LVBDSEKJ3C | 3 | LED_RED_K | 34.6000 | 37.0500 | F
LED1 | APHB1608LVBDSEKJ3C | 2 | VSYS | 33.4000 | 36.3500 | F
LED1 | APHB1608LVBDSEKJ3C | 1 | LED_BLUE_K | 34.6000 | 36.3500 | F
M1 | VCLP1020B002L | 2 | HAPTIC_NEG | 54.4000 | 33.6350 | B
M1 | VCLP1020B002L | 1 | 3V_MAIN | 54.4000 | 32.3650 | B
MIC1 | CMM-3424DT-26165-TR | 8 | GND | 45.0750 | 23.9000 | F
MIC1 | CMM-3424DT-26165-TR | 7 | GND | 46.3000 | 22.1750 | F
MIC1 | CMM-3424DT-26165-TR | 6 | GND | 47.5250 | 23.9000 | F
MIC1 | CMM-3424DT-26165-TR | 5 | GND | 46.3000 | 25.6250 | F
MIC1 | CMM-3424DT-26165-TR | 4 | PDM_DATA_MIC1 | 45.8750 | 24.5750 | F
MIC1 | CMM-3424DT-26165-TR | 3 | PDM_CLK | 45.8750 | 23.2250 | F
MIC1 | CMM-3424DT-26165-TR | 2 | GND | 46.7250 | 23.2250 | F
MIC1 | CMM-3424DT-26165-TR | 1 | 3V_MIC | 46.7250 | 24.5750 | F
MIC2 | CMM-3424DT-26165-TR | 8 | GND | 49.9750 | 23.9000 | F
MIC2 | CMM-3424DT-26165-TR | 7 | GND | 51.2000 | 22.1750 | F
MIC2 | CMM-3424DT-26165-TR | 6 | GND | 52.4250 | 23.9000 | F
MIC2 | CMM-3424DT-26165-TR | 5 | GND | 51.2000 | 25.6250 | F
MIC2 | CMM-3424DT-26165-TR | 4 | PDM_DATA_MIC2 | 50.7750 | 24.5750 | F
MIC2 | CMM-3424DT-26165-TR | 3 | PDM_CLK | 50.7750 | 23.2250 | F
MIC2 | CMM-3424DT-26165-TR | 2 | 3V_MIC | 51.6250 | 23.2250 | F
MIC2 | CMM-3424DT-26165-TR | 1 | 3V_MIC | 51.6250 | 24.5750 | F
NT1 | PVSS1-GND | 1 | PVSS1 | 42.6500 | 33.5000 | F
NT1 | PVSS1-GND | 2 | GND | 43.6500 | 33.5000 | F
NT2 | PVSS2-GND | 1 | PVSS2 | 43.6000 | 24.0000 | F
NT2 | PVSS2-GND | 2 | GND | 43.6000 | 23.0000 | F
Q1 | AO3400A | 1 | HAPTIC_GATE | 46.8875 | 37.4500 | F
Q1 | AO3400A | 2 | GND | 46.8875 | 35.5500 | F
Q1 | AO3400A | 3 | HAPTIC_NEG | 45.0125 | 36.5000 | F
R1 | 10k 1% |  |  | 34.4000 | 24.9450 | F
R1 | 10k 1% |  |  | 34.4000 | 24.2550 | F
R1 | 10k 1% | 1 | 3V_MAIN | 34.4000 | 24.9200 | F
R1 | 10k 1% | 2 | I2C_SCL | 34.4000 | 24.2800 | F
R10 | 27R 1% |  |  | 59.9550 | 38.0000 | F
R10 | 27R 1% |  |  | 60.6450 | 38.0000 | F
R10 | 27R 1% | 1 | USB_D+ | 59.9800 | 38.0000 | F
R10 | 27R 1% | 2 | USB_MCU_D+ | 60.6200 | 38.0000 | F
R11 | 27R 1% |  |  | 61.4550 | 38.0000 | F
R11 | 27R 1% |  |  | 62.1450 | 38.0000 | F
R11 | 27R 1% | 1 | USB_D- | 61.4800 | 38.0000 | F
R11 | 27R 1% | 2 | USB_MCU_D- | 62.1200 | 38.0000 | F
R2 | 10k 1% |  |  | 35.0000 | 24.9450 | F
R2 | 10k 1% |  |  | 35.0000 | 24.2550 | F
R2 | 10k 1% | 1 | 3V_MAIN | 35.0000 | 24.9200 | F
R2 | 10k 1% | 2 | I2C_SDA | 35.0000 | 24.2800 | F
R3 | 330k 1% |  |  | 32.5000 | 24.9450 | F
R3 | 330k 1% |  |  | 32.5000 | 24.2550 | F
R3 | 330k 1% | 1 | VSET1 | 32.5000 | 24.9200 | F
R3 | 330k 1% | 2 | GND | 32.5000 | 24.2800 | F
R4 | 150k 1% |  |  | 33.1000 | 24.9450 | F
R4 | 150k 1% |  |  | 33.1000 | 24.2550 | F
R4 | 150k 1% | 1 | VSET2 | 33.1000 | 24.9200 | F
R4 | 150k 1% | 2 | GND | 33.1000 | 24.2800 | F
R5 | 100R 1% | 1 | HAPTIC_PWM | 48.3900 | 35.0000 | F
R5 | 100R 1% | 2 | HAPTIC_GATE | 49.4100 | 35.0000 | F
R6 | 100k 1% | 1 | HAPTIC_GATE | 48.3900 | 36.3000 | F
R6 | 100k 1% | 2 | GND | 49.4100 | 36.3000 | F
R7 | 100k 1% | 1 | 3V_FLASH | 53.2500 | 33.6600 | F
R7 | 100k 1% | 2 | FLASH_CS | 53.2500 | 32.6400 | F
R8 | 100R 1% | 1 | PDM_DATA_MIC1 | 46.7900 | 26.8000 | F
R8 | 100R 1% | 2 | PDM_DATA | 47.8100 | 26.8000 | F
R9 | 100R 1% | 1 | PDM_DATA_MIC2 | 51.5900 | 26.8000 | F
R9 | 100R 1% | 2 | PDM_DATA | 52.6100 | 26.8000 | F
SW1 | B3U-1000P | 1 | SHPHLD_BTN | 28.3000 | 36.3000 | F
SW1 | B3U-1000P | 2 | GND | 31.7000 | 36.3000 | F
TP1 | SWDIO | 1 | SWDIO | 35.0000 | 30.0000 | B
TP10 | VSYS | 1 | VSYS | 35.0000 | 31.5000 | B
TP11 | VBUSOUT | 1 | VBUSOUT | 36.5000 | 31.5000 | B
TP12 | 3V_FLASH | 1 | 3V_FLASH | 38.0000 | 31.5000 | B
TP13 | 3V_MIC | 1 | 3V_MIC | 39.5000 | 31.5000 | B
TP14 | PMIC_INT | 1 | PMIC_INT | 41.0000 | 31.5000 | B
TP2 | SWDCLK | 1 | SWDCLK | 36.5000 | 30.0000 | B
TP3 | RESET | 1 | RESET | 38.0000 | 30.0000 | B
TP4 | 3V_MAIN | 1 | 3V_MAIN | 39.5000 | 30.0000 | B
TP5 | GND | 1 | GND | 41.0000 | 30.0000 | B
TP6 | UART_TX | 1 | UART_TX | 42.5000 | 30.0000 | B
TP7 | UART_RX | 1 | UART_RX | 44.0000 | 30.0000 | B
TP8 | VBAT | 1 | VBAT | 45.5000 | 30.0000 | B
TP9 | VBUS | 1 | VBUS | 47.0000 | 30.0000 | B
U1 | MDBT50Q-1MV2 | 1 | GND | 55.1000 | 25.7500 | F
U1 | MDBT50Q-1MV2 | 2 | GND | 55.1000 | 26.8500 | F
U1 | MDBT50Q-1MV2 | 3 |  | 55.1000 | 27.6500 | F
U1 | MDBT50Q-1MV2 | 4 |  | 55.1000 | 29.2500 | F
U1 | MDBT50Q-1MV2 | 5 |  | 56.0000 | 29.6500 | F
U1 | MDBT50Q-1MV2 | 6 |  | 55.1000 | 30.0500 | F
U1 | MDBT50Q-1MV2 | 7 |  | 56.0000 | 30.4500 | F
U1 | MDBT50Q-1MV2 | 8 |  | 55.1000 | 30.8500 | F
U1 | MDBT50Q-1MV2 | 9 |  | 56.0000 | 31.2500 | F
U1 | MDBT50Q-1MV2 | 10 |  | 55.1000 | 31.6500 | F
U1 | MDBT50Q-1MV2 | 11 |  | 56.0000 | 32.0500 | F
U1 | MDBT50Q-1MV2 | 12 |  | 55.1000 | 32.4500 | F
U1 | MDBT50Q-1MV2 | 13 |  | 56.0000 | 32.8500 | F
U1 | MDBT50Q-1MV2 | 14 |  | 55.1000 | 33.2500 | F
U1 | MDBT50Q-1MV2 | 15 | GND | 54.9500 | 36.6500 | F
U1 | MDBT50Q-1MV2 | 16 | I2C_SDA | 55.7500 | 36.6500 | F
U1 | MDBT50Q-1MV2 | 17 |  | 56.5500 | 36.6500 | F
U1 | MDBT50Q-1MV2 | 18 |  | 57.3500 | 36.6500 | F
U1 | MDBT50Q-1MV2 | 19 | I2C_SCL | 57.7500 | 35.7500 | F
U1 | MDBT50Q-1MV2 | 20 | UART_RX | 58.1500 | 36.6500 | F
U1 | MDBT50Q-1MV2 | 21 | UART_TX | 58.5500 | 35.7500 | F
U1 | MDBT50Q-1MV2 | 22 |  | 58.9500 | 36.6500 | F
U1 | MDBT50Q-1MV2 | 23 |  | 59.3500 | 35.7500 | F
U1 | MDBT50Q-1MV2 | 24 | HAPTIC_PWM | 59.7500 | 36.6500 | F
U1 | MDBT50Q-1MV2 | 25 |  | 60.1500 | 35.7500 | F
U1 | MDBT50Q-1MV2 | 26 |  | 60.5500 | 36.6500 | F
U1 | MDBT50Q-1MV2 | 27 |  | 60.9500 | 35.7500 | F
U1 | MDBT50Q-1MV2 | 28 | 3V_MAIN | 61.3500 | 36.6500 | F
U1 | MDBT50Q-1MV2 | 29 |  | 61.7500 | 35.7500 | F
U1 | MDBT50Q-1MV2 | 30 | 3V_MAIN | 62.1500 | 36.6500 | F
U1 | MDBT50Q-1MV2 | 31 |  | 62.9500 | 36.6500 | F
U1 | MDBT50Q-1MV2 | 32 | VBUSOUT | 63.7500 | 36.6500 | F
U1 | MDBT50Q-1MV2 | 33 | GND | 64.5500 | 36.6500 | F
U1 | MDBT50Q-1MV2 | 34 | USB_MCU_D- | 64.4000 | 35.6500 | F
U1 | MDBT50Q-1MV2 | 35 | USB_MCU_D+ | 64.4000 | 34.8500 | F
U1 | MDBT50Q-1MV2 | 36 |  | 63.5000 | 34.4500 | F
U1 | MDBT50Q-1MV2 | 37 |  | 64.4000 | 34.0500 | F
U1 | MDBT50Q-1MV2 | 38 | PDM_CLK | 63.5000 | 33.6500 | F
U1 | MDBT50Q-1MV2 | 39 | PDM_DATA | 64.4000 | 33.2500 | F
U1 | MDBT50Q-1MV2 | 40 | RESET | 63.5000 | 32.8500 | F
U1 | MDBT50Q-1MV2 | 41 | PMIC_INT | 64.4000 | 32.4500 | F
U1 | MDBT50Q-1MV2 | 42 | FLASH_SCK | 63.5000 | 32.0500 | F
U1 | MDBT50Q-1MV2 | 43 | FLASH_IO0 | 63.5000 | 31.2500 | F
U1 | MDBT50Q-1MV2 | 44 | FLASH_CS | 64.4000 | 30.8500 | F
U1 | MDBT50Q-1MV2 | 45 | FLASH_IO2 | 63.5000 | 30.4500 | F
U1 | MDBT50Q-1MV2 | 46 | FLASH_IO1 | 64.4000 | 30.0500 | F
U1 | MDBT50Q-1MV2 | 47 | FLASH_IO3 | 63.5000 | 29.6500 | F
U1 | MDBT50Q-1MV2 | 48 | ACC_INT1 | 64.4000 | 29.2500 | F
U1 | MDBT50Q-1MV2 | 49 | ACC_INT2 | 63.5000 | 28.8500 | F
U1 | MDBT50Q-1MV2 | 50 |  | 63.5000 | 28.0500 | F
U1 | MDBT50Q-1MV2 | 51 | SWDIO | 64.4000 | 27.6500 | F
U1 | MDBT50Q-1MV2 | 52 |  | 63.5000 | 27.2500 | F
U1 | MDBT50Q-1MV2 | 53 | SWDCLK | 64.4000 | 26.8500 | F
U1 | MDBT50Q-1MV2 | 54 |  | 63.5000 | 26.4500 | F
U1 | MDBT50Q-1MV2 | 55 | GND | 64.4000 | 25.7500 | F
U1 | MDBT50Q-1MV2 | 56 |  | 57.7500 | 30.0500 | F
U1 | MDBT50Q-1MV2 | 57 |  | 58.5500 | 30.0500 | F
U1 | MDBT50Q-1MV2 | 58 |  | 59.3500 | 30.0500 | F
U1 | MDBT50Q-1MV2 | 59 |  | 60.1500 | 30.0500 | F
U1 | MDBT50Q-1MV2 | 60 |  | 60.9500 | 30.0500 | F
U1 | MDBT50Q-1MV2 | 61 |  | 61.7500 | 30.0500 | F
U2 | nPM1300 | 1 | 3V_MAIN | 37.6375 | 30.3500 | F
U2 | nPM1300 | 2 | PVSS1 | 37.6375 | 29.8500 | F
U2 | nPM1300 | 3 | SW1 | 37.6375 | 29.3500 | F
U2 | nPM1300 | 4 | VSYS | 37.6375 | 28.8500 | F
U2 | nPM1300 | 5 | SW2 | 37.6375 | 28.3500 | F
U2 | nPM1300 | 6 | PVSS2 | 37.6375 | 27.8500 | F
U2 | nPM1300 | 7 | PMIC_INT | 37.6375 | 27.3500 | F
U2 | nPM1300 | 8 |  | 37.6375 | 26.8500 | F
U2 | nPM1300 | 9 |  | 36.9500 | 26.1625 | F
U2 | nPM1300 | 10 |  | 36.4500 | 26.1625 | F
U2 | nPM1300 | 11 |  | 35.9500 | 26.1625 | F
U2 | nPM1300 | 12 | 3V_MAIN | 35.4500 | 26.1625 | F
U2 | nPM1300 | 13 | I2C_SDA | 34.9500 | 26.1625 | F
U2 | nPM1300 | 14 | I2C_SCL | 34.4500 | 26.1625 | F
U2 | nPM1300 | 15 | SHPHLD_BTN | 33.9500 | 26.1625 | F
U2 | nPM1300 | 16 | VSET2 | 33.4500 | 26.1625 | F
U2 | nPM1300 | 17 | VSET1 | 32.7625 | 26.8500 | F
U2 | nPM1300 | 18 | NTC | 32.7625 | 27.3500 | F
U2 | nPM1300 | 19 | VBAT | 32.7625 | 27.8500 | F
U2 | nPM1300 | 20 | VSYS | 32.7625 | 28.3500 | F
U2 | nPM1300 | 21 | VBUS | 32.7625 | 28.8500 | F
U2 | nPM1300 | 22 | VBUSOUT | 32.7625 | 29.3500 | F
U2 | nPM1300 | 23 | USB_CC1 | 32.7625 | 29.8500 | F
U2 | nPM1300 | 24 | USB_CC2 | 32.7625 | 30.3500 | F
U2 | nPM1300 | 25 | LED_BLUE_K | 33.4500 | 31.0375 | F
U2 | nPM1300 | 26 | LED_RED_K | 33.9500 | 31.0375 | F
U2 | nPM1300 | 27 |  | 34.4500 | 31.0375 | F
U2 | nPM1300 | 28 | VSYS | 34.9500 | 31.0375 | F
U2 | nPM1300 | 29 | 3V_MIC | 35.4500 | 31.0375 | F
U2 | nPM1300 | 30 |  | 35.9500 | 31.0375 | F
U2 | nPM1300 | 31 |  | 36.4500 | 31.0375 | F
U2 | nPM1300 | 32 | 3V_FLASH | 36.9500 | 31.0375 | F
U2 | nPM1300 | 33 | GND | 35.2000 | 28.6000 | F
U2 | nPM1300 |  |  | 36.3500 | 29.7500 | F
U2 | nPM1300 |  |  | 36.3500 | 28.6000 | F
U2 | nPM1300 |  |  | 36.3500 | 27.4500 | F
U2 | nPM1300 |  |  | 35.2000 | 29.7500 | F
U2 | nPM1300 |  |  | 35.2000 | 28.6000 | F
U2 | nPM1300 |  |  | 35.2000 | 27.4500 | F
U2 | nPM1300 |  |  | 34.0500 | 29.7500 | F
U2 | nPM1300 |  |  | 34.0500 | 28.6000 | F
U2 | nPM1300 |  |  | 34.0500 | 27.4500 | F
U3 | LIS2DW12TR | 1 | I2C_SCL | 50.5375 | 35.7000 | F
U3 | LIS2DW12TR | 2 | 3V_MAIN | 50.5375 | 36.2000 | F
U3 | LIS2DW12TR | 3 | GND | 50.5375 | 36.7000 | F
U3 | LIS2DW12TR | 4 | I2C_SDA | 50.5375 | 37.2000 | F
U3 | LIS2DW12TR | 5 |  | 51.0500 | 37.2125 | F
U3 | LIS2DW12TR | 6 | GND | 51.5500 | 37.2125 | F
U3 | LIS2DW12TR | 7 | GND | 52.0625 | 37.2000 | F
U3 | LIS2DW12TR | 8 | GND | 52.0625 | 36.7000 | F
U3 | LIS2DW12TR | 9 | 3V_MAIN | 52.0625 | 36.2000 | F
U3 | LIS2DW12TR | 10 | 3V_MAIN | 52.0625 | 35.7000 | F
U3 | LIS2DW12TR | 11 | ACC_INT2 | 51.5500 | 35.6875 | F
U3 | LIS2DW12TR | 12 | ACC_INT1 | 51.0500 | 35.6875 | F
U4 | TPD2EUSB30DRTR | 1 | USB_D+ | 27.7750 | 29.6500 | F
U4 | TPD2EUSB30DRTR | 2 | USB_D- | 27.7750 | 30.3500 | F
U4 | TPD2EUSB30DRTR | 3 | GND | 28.6250 | 30.0000 | F
U5 | MX35LF4GE4AD-Z4I | 1 | FLASH_CS | 44.4500 | 28.7950 | F
U5 | MX35LF4GE4AD-Z4I | 2 | FLASH_IO1 | 44.4500 | 30.0650 | F
U5 | MX35LF4GE4AD-Z4I | 3 | FLASH_IO2 | 44.4500 | 31.3350 | F
U5 | MX35LF4GE4AD-Z4I | 4 | GND | 44.4500 | 32.6050 | F
U5 | MX35LF4GE4AD-Z4I | 5 | FLASH_IO0 | 51.9500 | 32.6050 | F
U5 | MX35LF4GE4AD-Z4I | 6 | FLASH_SCK | 51.9500 | 31.3350 | F
U5 | MX35LF4GE4AD-Z4I | 7 | FLASH_IO3 | 51.9500 | 30.0650 | F
U5 | MX35LF4GE4AD-Z4I | 8 | 3V_FLASH | 51.9500 | 28.7950 | F
U5 | MX35LF4GE4AD-Z4I | 9 | GND | 48.2000 | 30.7000 | F
U5 | MX35LF4GE4AD-Z4I |  |  | 47.3500 | 29.6250 | F
U5 | MX35LF4GE4AD-Z4I |  |  | 47.3500 | 31.7750 | F
U5 | MX35LF4GE4AD-Z4I |  |  | 49.0500 | 29.6250 | F
U5 | MX35LF4GE4AD-Z4I |  |  | 49.0500 | 31.7750 | F
U6 | TPD2E2U06DCKR | 1 | USB_CC1 | 27.9000 | 22.4500 | F
U6 | TPD2E2U06DCKR | 2 | USB_CC2 | 27.9000 | 23.7500 | F
U6 | TPD2E2U06DCKR | 3 | GND | 29.9000 | 23.1000 | F
