anticipation-labs/anticipy-hardware/08_HISTORICAL_PACKAGES/2026-08-27_v07_four_day_build_pack/mechanical/v07_full_assembly.step

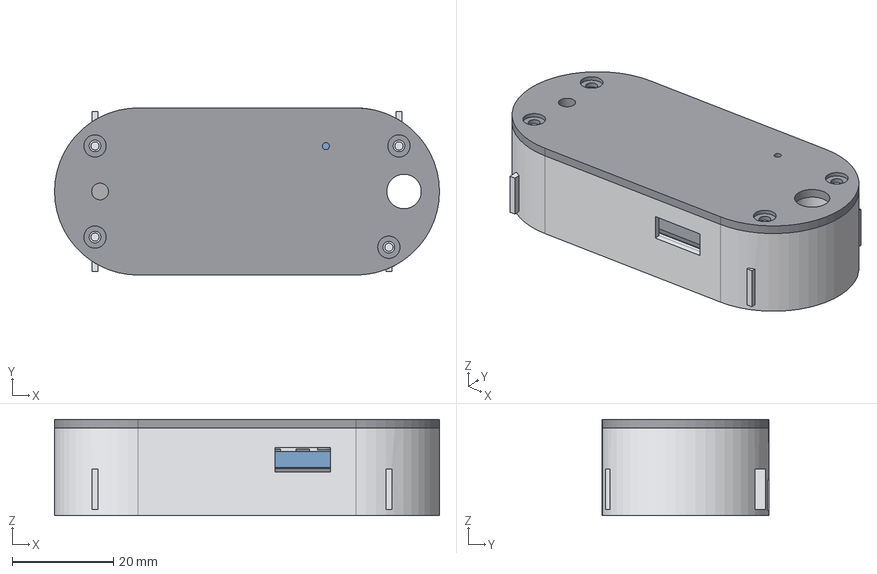
[picture p41: CAD file, 2026-09-06]
08_HISTORICAL_PACKAGES/2026-08-27_v07_four_day_build_pack/mechanical/v07_full_assembly.step
76.0 x 33.0 x 19.0 mm
P2S printed base
P2S printed lid
P2S printed board carrier
BBM protected 602535 500 mAh pack
Vybronics VCLP1020B002L ERM
haptic driver + 100 uF bulk-cap cluster
C&K OS102011MA1QN1 hard-off switch
Adafruit Audio BFF 5769 with microSD
Seeed XIAO nRF52840 Sense headerless
C&K KSC201G-LFS button
