anticipation-labs/anticipy-hardware/08_HISTORICAL_PACKAGES/2026-08-28_execution_v1.0/05_QA_FIXTURES/step/drop_release_released_assembly.step

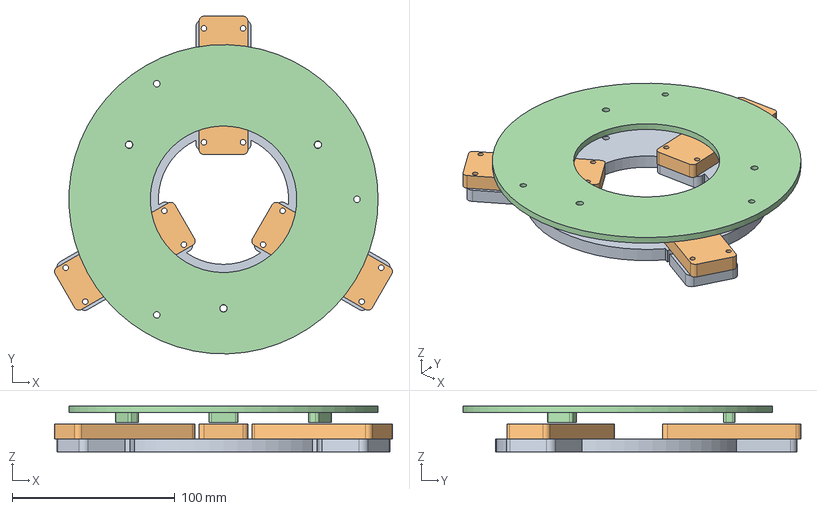
[picture p42: CAD file, 2026-09-06]
08_HISTORICAL_PACKAGES/2026-08-28_execution_v1.0/05_QA_FIXTURES/step/drop_release_released_assembly.step
207.7 x 207.5 x 28.0 mm
guide_1 x 3
finger_1 x 3
common_latch
