anticipation-labs/anticipy-hardware/02_PROTOTYPE_XIAO/CAD/PRINT_THESE/mic_drill_jig_usb_end_notched.stl

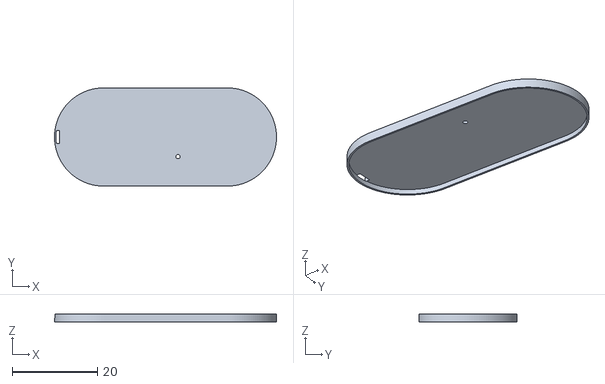
[picture p43: CAD file, 2026-09-06]
02_PROTOTYPE_XIAO/CAD/PRINT_THESE/mic_drill_jig_usb_end_notched.stl
52.0 x 23.0 x 1.80
