anticipation-labs/anticipy-hardware/02_PROTOTYPE_XIAO/CAD/REFERENCE_ONLY_STEP/ALT_LOCAL_MEASURE_MAX_battery_12x10x5p5.step

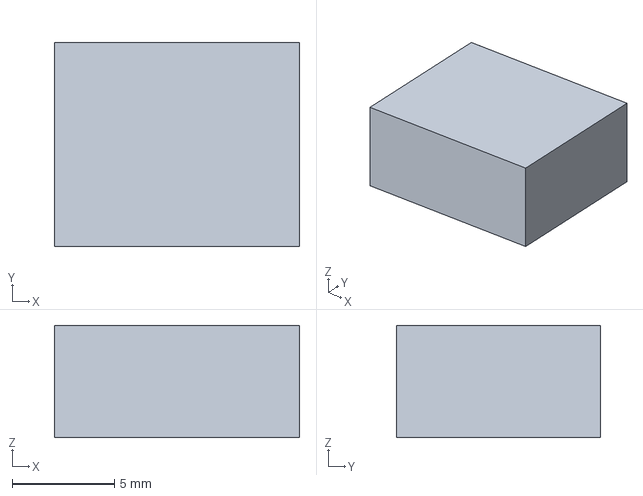
[picture p44: CAD file, 2026-09-06]
02_PROTOTYPE_XIAO/CAD/REFERENCE_ONLY_STEP/ALT_LOCAL_MEASURE_MAX_battery_12x10x5p5.step
12.0 x 10.0 x 5.50 mm
