anticipation-labs/anticipy-hardware/03_PCB/R0B_CHECKPOINT_NOT_FOR_FAB/02_Mechanical_CAD/ANT-PROD-R0B_PROVISIONAL_BOARD_ONLY.step

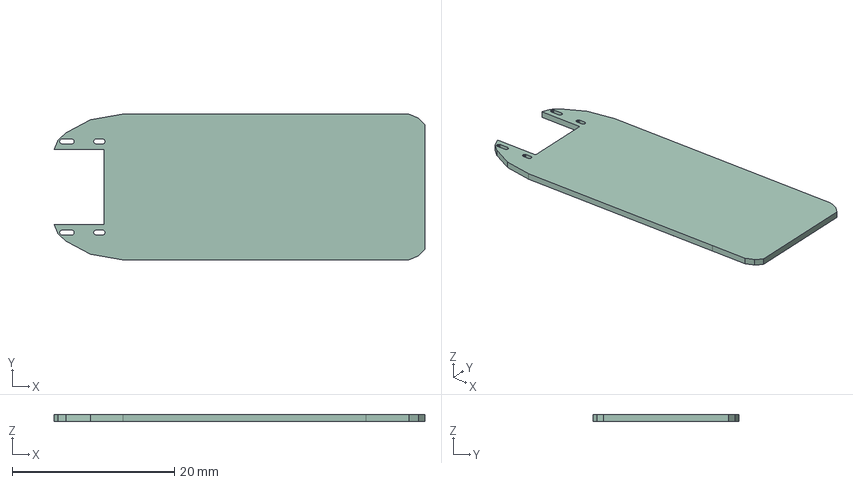
[picture p45: CAD file, 2026-09-06]
03_PCB/R0B_CHECKPOINT_NOT_FOR_FAB/02_Mechanical_CAD/ANT-PROD-R0B_PROVISIONAL_BOARD_ONLY.step
45.8 x 18.0 x 0.82 mm
