anticipation-labs/anticipy-hardware/04_MECHANICAL/MACHINIST_DRAWINGS/production_aluminum_cap.step

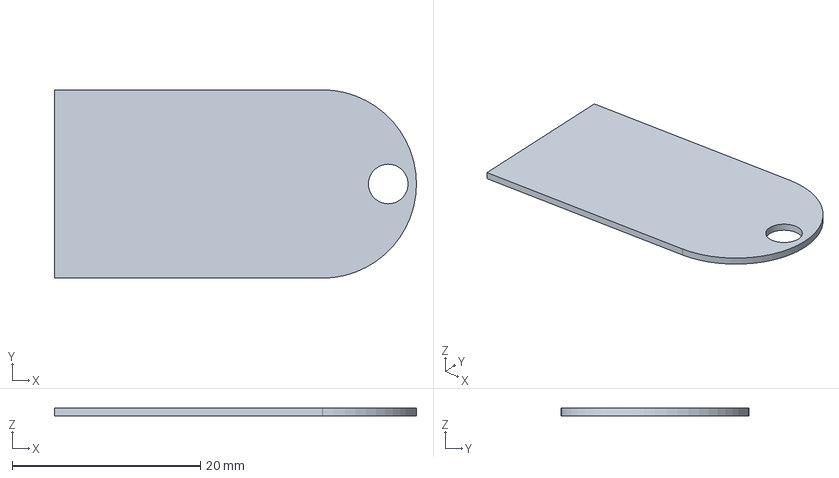
[picture p46: CAD file, 2026-09-06]
04_MECHANICAL/MACHINIST_DRAWINGS/production_aluminum_cap.step
38.4 x 20.0 x 0.8 mm
