anticipation-labs/anticipy-hardware/04_MECHANICAL/OPENSCAD_SHELL_PROGRAM_v5.1/ANTICIPY_v4_3pendants.3mf

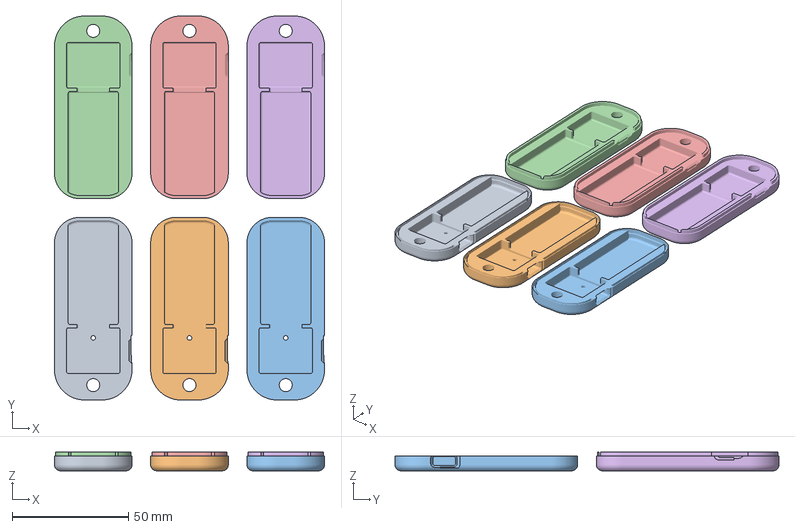
[picture p47: CAD file, 2026-09-06]
04_MECHANICAL/OPENSCAD_SHELL_PROGRAM_v5.1/ANTICIPY_v4_3pendants.3mf
116.0 x 164.9 x 8.00 mm
pendant1-front
pendant2-front
pendant3-front
pendant1-back
pendant2-back
pendant3-back
