anticipation-labs/anticipy-hardware/04_MECHANICAL/OPENSCAD_SHELL_PROGRAM_v5.1/stl/anticipy_v4_back.stl

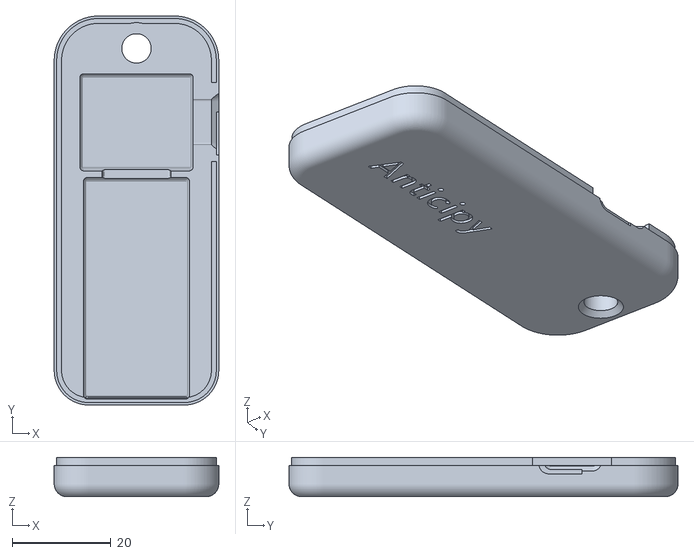
[picture p48: CAD file, 2026-09-06]
04_MECHANICAL/OPENSCAD_SHELL_PROGRAM_v5.1/stl/anticipy_v4_back.stl
33.3 x 78.8 x 8.00
