anticipation-labs/anticipy-hardware/04_MECHANICAL/OPENSCAD_SHELL_PROGRAM_v5.1/stl_v5/coupon_front_22.stl

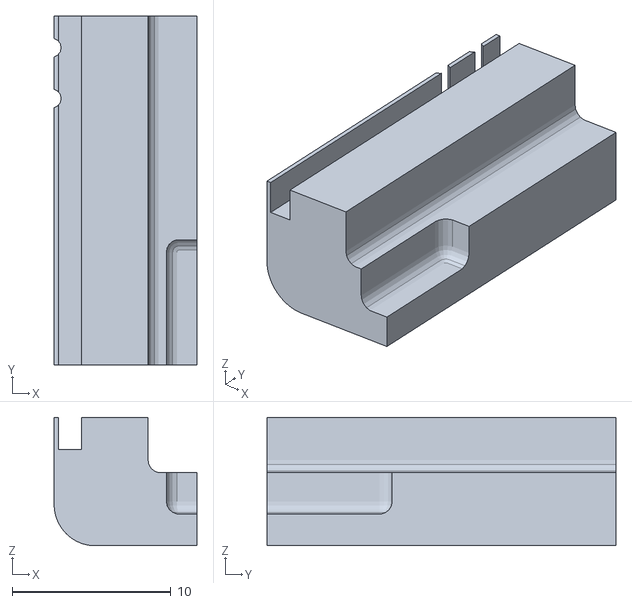
[picture p49: CAD file, 2026-09-06]
04_MECHANICAL/OPENSCAD_SHELL_PROGRAM_v5.1/stl_v5/coupon_front_22.stl
8.99 x 22.0 x 8.10
