anticipation-labs/anticipy-hardware/04_MECHANICAL/PRINT_READY/v09_compact_base.step

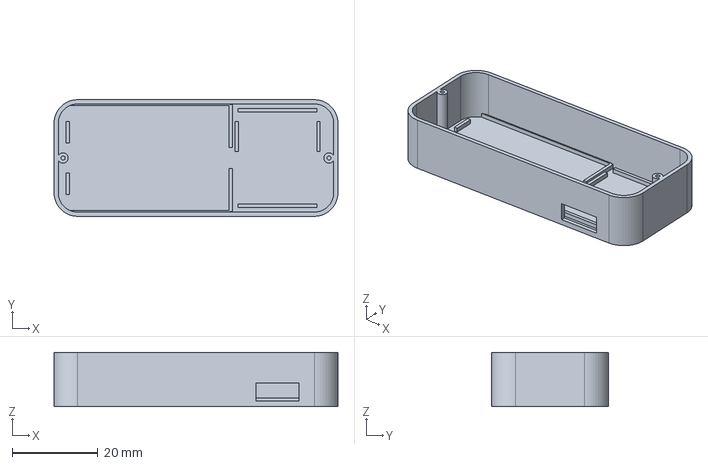
[picture p50: CAD file, 2026-09-06]
04_MECHANICAL/PRINT_READY/v09_compact_base.step
66.2 x 27.2 x 12.6 mm
