anticipation-labs/anticipy-hardware/04_MECHANICAL/PRINT_READY/xiao_prototype_plates/ALT_LOCAL_MEASURE_MAX_battery_24x10x5p5.stl

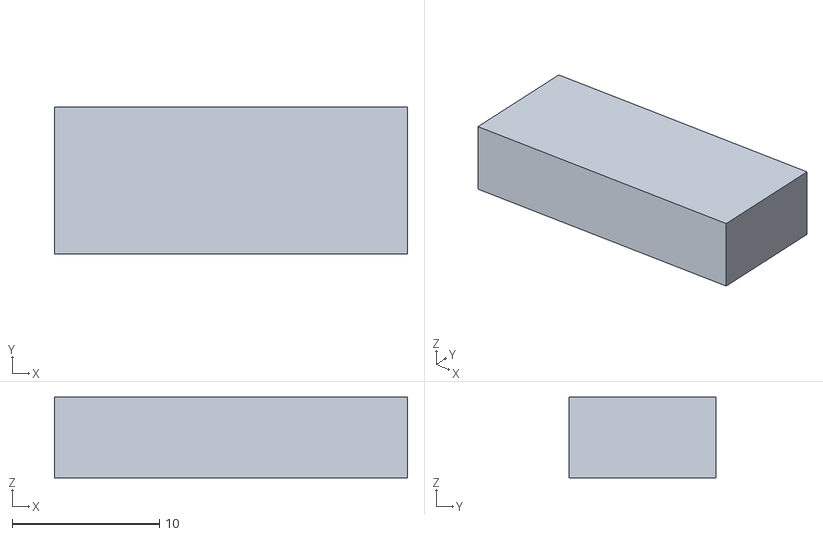
[picture p51: CAD file, 2026-09-06]
04_MECHANICAL/PRINT_READY/xiao_prototype_plates/ALT_LOCAL_MEASURE_MAX_battery_24x10x5p5.stl
24.0 x 10.0 x 5.50
