anticipation-labs/anticipy-hardware/04_MECHANICAL/REFERENCE_STEP/production_aluminum_cap_outline.dxf

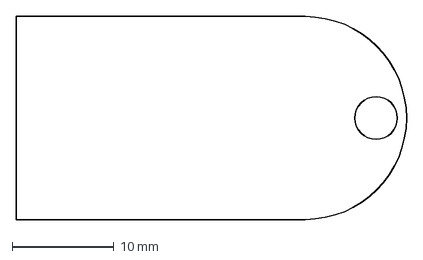
[picture p52: CAD file, 2026-09-06]
04_MECHANICAL/REFERENCE_STEP/production_aluminum_cap_outline.dxf
38.4 x 20.0 mm
