anticipation-labs/anticipy-hardware/06_FACTORY_AND_QA/QA_FIXTURES/step/drop_pose_key_25_C_XM_YM_ZP.step

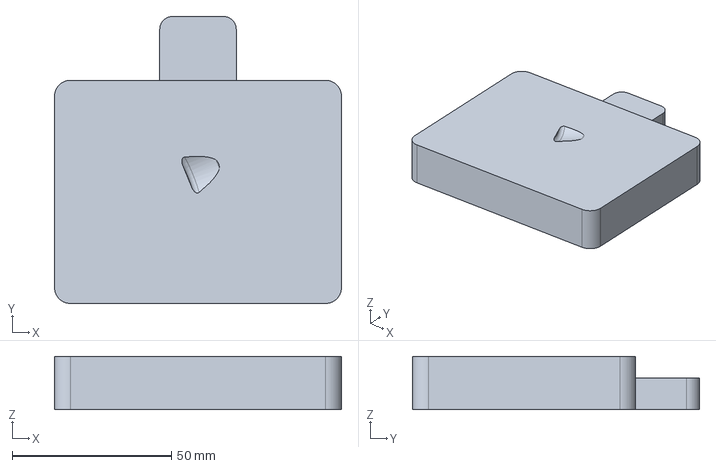
[picture p53: CAD file, 2026-09-06]
06_FACTORY_AND_QA/QA_FIXTURES/step/drop_pose_key_25_C_XM_YM_ZP.step
90.0 x 90.0 x 16.7 mm
