anticipation-labs/anticipy-hardware/08_HISTORICAL_PACKAGES/2026-08-19_anticipy_shell_openscad/PRINT_ME_anticipy_all8.3mf

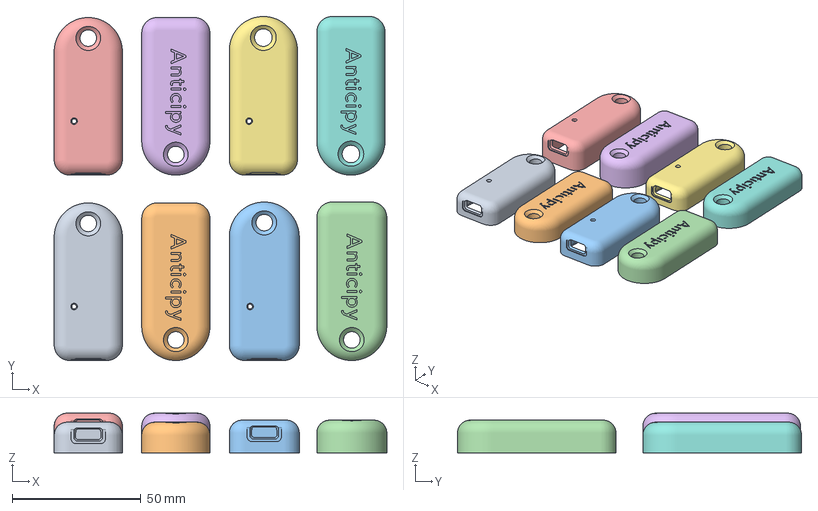
[picture p54: CAD file, 2026-09-06]
08_HISTORICAL_PACKAGES/2026-08-19_anticipy_shell_openscad/PRINT_ME_anticipy_all8.3mf
129.2 x 133.6 x 15.4 mm
V1 front
V1 back
V2 front
V2 back
V3 front
V3 back
V4 front
V4 back
