anticipation-labs/anticipy-hardware/08_HISTORICAL_PACKAGES/2026-08-19_anticipy_shell_openscad/stl_v5/v5_v1_back.stl

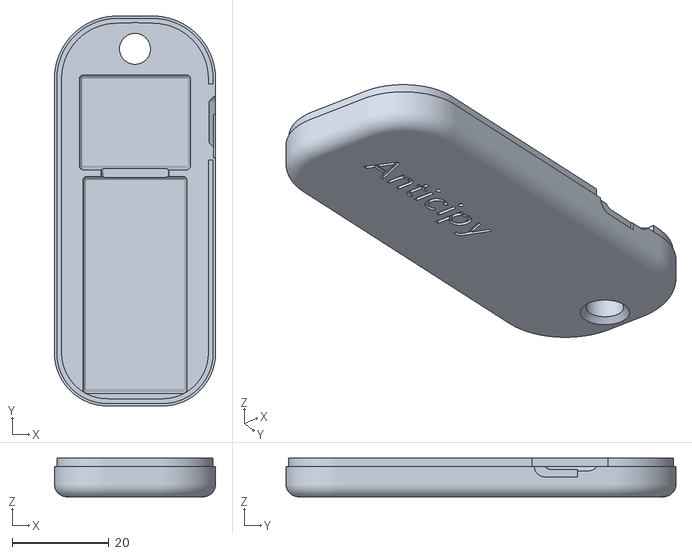
[picture p55: CAD file, 2026-09-06]
08_HISTORICAL_PACKAGES/2026-08-19_anticipy_shell_openscad/stl_v5/v5_v1_back.stl
33.3 x 80.7 x 8.00
