anticipation-labs/anticipy-hardware/08_HISTORICAL_PACKAGES/2026-08-27_v07_four_day_build_pack/mechanical/v07_base_shell.step

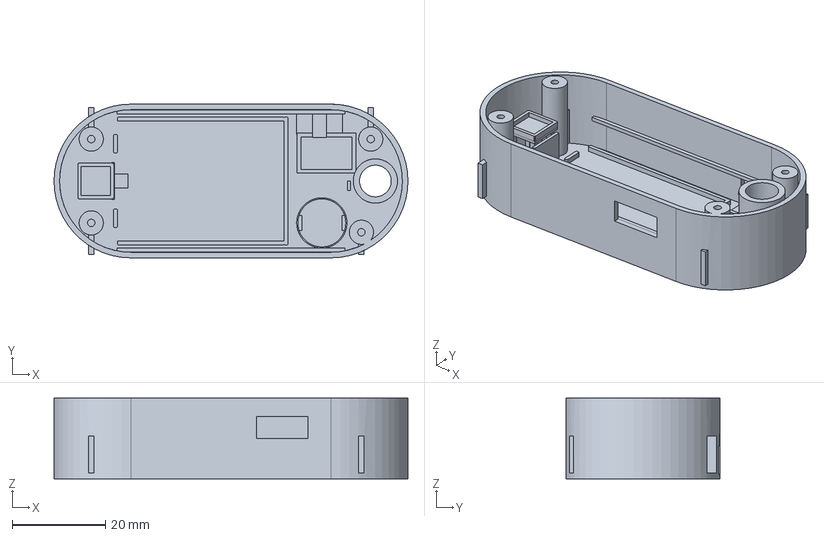
[picture p56: CAD file, 2026-09-06]
08_HISTORICAL_PACKAGES/2026-08-27_v07_four_day_build_pack/mechanical/v07_base_shell.step
76.0 x 33.0 x 17.3 mm
