anticipation-labs/anticipy-hardware/08_HISTORICAL_PACKAGES/2026-08-28_48h_v13/01_PRINT/PRINT_THIS_ONE_UNIT_P2S.3mf

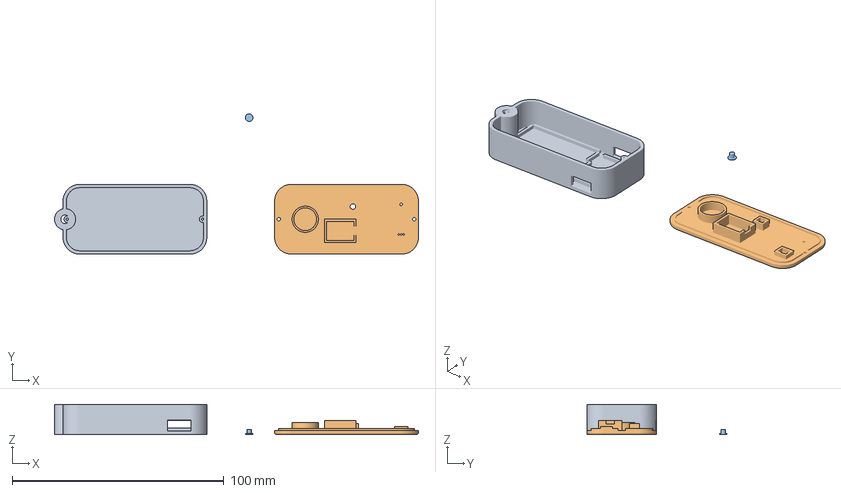
[picture p57: CAD file, 2026-09-06]
08_HISTORICAL_PACKAGES/2026-08-28_48h_v13/01_PRINT/PRINT_THIS_ONE_UNIT_P2S.3mf
172.0 x 66.3 x 14.4 mm
ANTICIPY_BASE
ANTICIPY_LID
ANTICIPY_BUTTON
