anticipation-labs/anticipy-hardware/08_HISTORICAL_PACKAGES/2026-08-28_execution_v1.0/01_PRINT_NOW/v09_dummy_haptic_12x8x3.stl

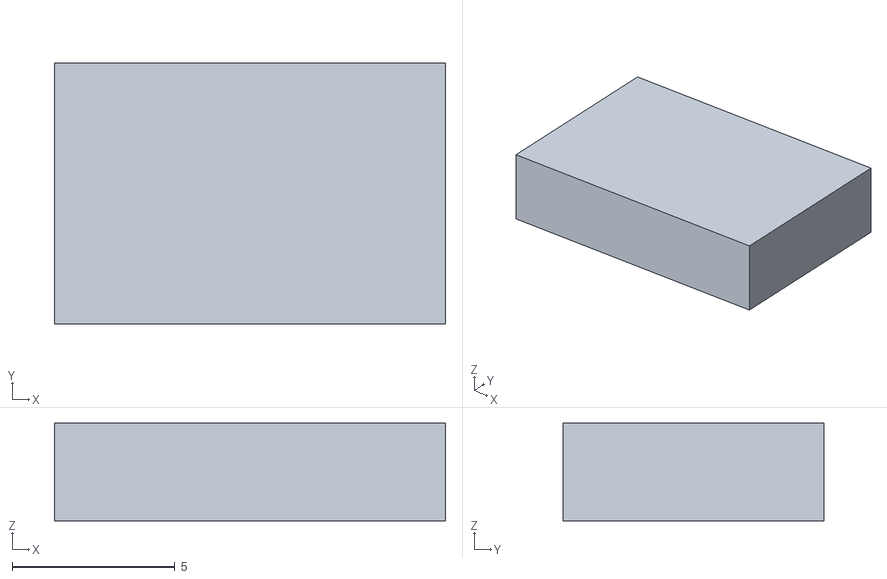
[picture p58: CAD file, 2026-09-06]
08_HISTORICAL_PACKAGES/2026-08-28_execution_v1.0/01_PRINT_NOW/v09_dummy_haptic_12x8x3.stl
12.0 x 8.00 x 3.00
