anticipation-labs/anticipy-hardware/08_HISTORICAL_PACKAGES/2026-08-28_execution_v1.0/02_PRODUCTION_CAD/production_print_front.stl

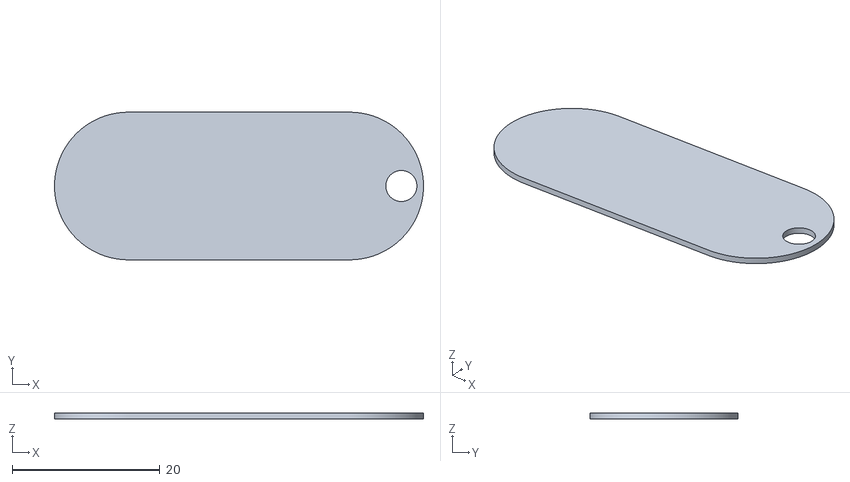
[picture p59: CAD file, 2026-09-06]
08_HISTORICAL_PACKAGES/2026-08-28_execution_v1.0/02_PRODUCTION_CAD/production_print_front.stl
50.0 x 20.0 x 0.8
