anticipation-labs/anticipy-hardware/08_HISTORICAL_PACKAGES/2026-08-28_p2s_v07_enclosure/P2S_v07_nopcb_retained.3mf

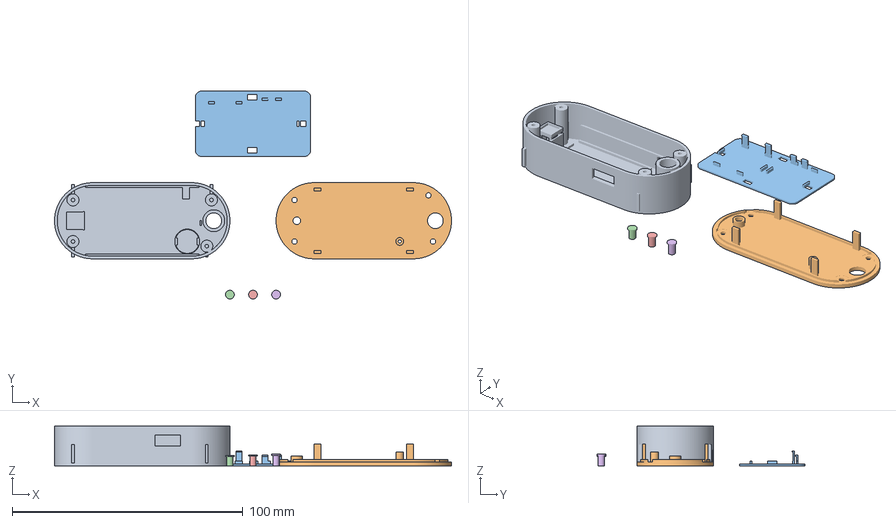
[picture p60: CAD file, 2026-09-06]
08_HISTORICAL_PACKAGES/2026-08-28_p2s_v07_enclosure/P2S_v07_nopcb_retained.3mf
172.0 x 90.1 x 17.3 mm
v07_base_shell.stl
v07_lid.stl
v07_carrier.stl
v07_button_plunger_4p0.stl
v07_button_plunger_4p3.stl
v07_button_plunger_4p6.stl
