anticipation-labs/anticipy-hardware/08_HISTORICAL_PACKAGES/2026-08-28_tuesday_evt_v0.1/anticipy_strict_evt_button_plunger_1p15.stl

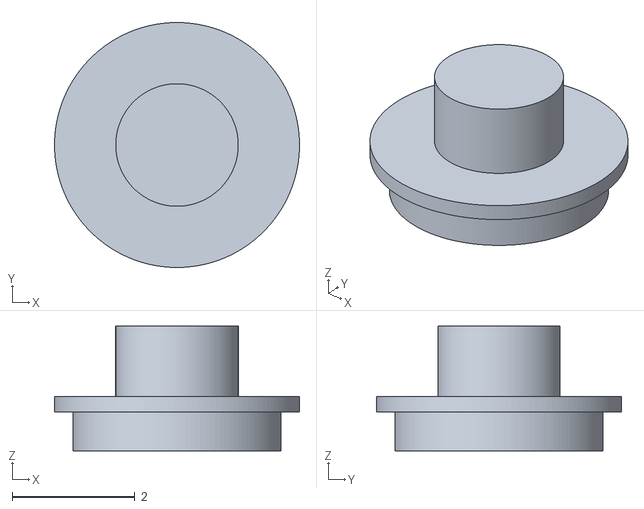
[picture p61: CAD file, 2026-09-06]
08_HISTORICAL_PACKAGES/2026-08-28_tuesday_evt_v0.1/anticipy_strict_evt_button_plunger_1p15.stl
4.00 x 4.00 x 2.04
