anticipation-labs/anticipy-hardware/latest_builds/E1P1/cad/Front_Oval_Shell.step

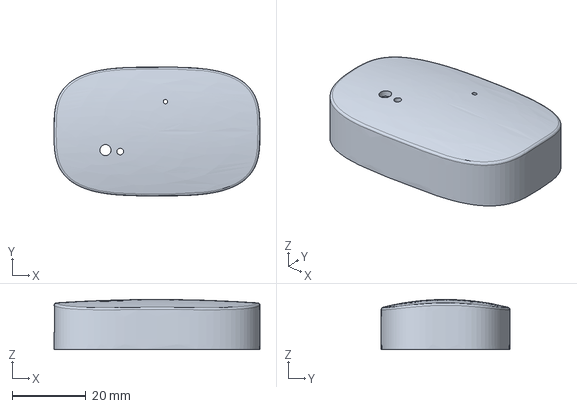
[picture p62: CAD file, 2026-09-10]
latest_builds/E1P1/cad/Front_Oval_Shell.step
56.0 x 35.0 x 13.6 mm
