anticipation-labs/anticipy-hardware/latest_builds/E1P1/pcb/electrical/models/Capacitor_SMD__C_0805_2012Metric.step

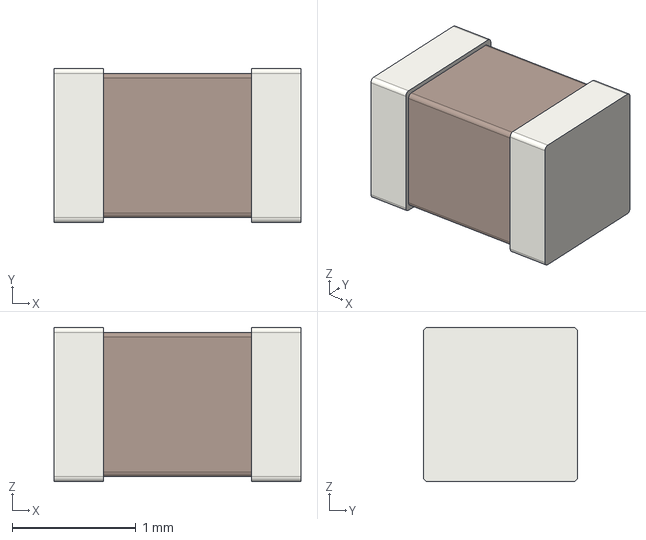
[picture p63: CAD file, 2026-09-10]
latest_builds/E1P1/pcb/electrical/models/Capacitor_SMD__C_0805_2012Metric.step
2.00 x 1.25 x 1.25 mm
