anticipation-labs/anticipy-hardware/latest_builds/E1P1/pcb/manufacturing/E1P1_Board_and_Nominal_Components.step

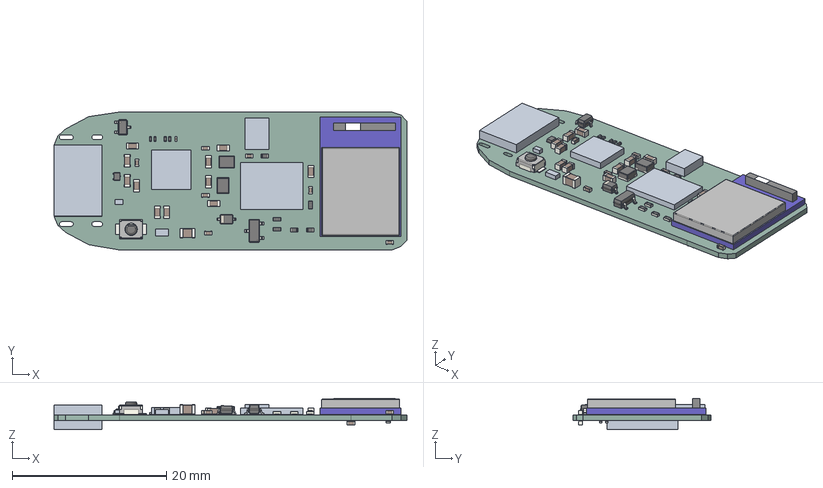
[picture p64: CAD file, 2026-09-10]
latest_builds/E1P1/pcb/manufacturing/E1P1_Board_and_Nominal_Components.step
45.8 x 17.9 x 4.04 mm
R_0402_1005Metric x 6
C_0603_1608Metric x 11
DRT_3
L_Murata_DFE201610P x 2
Raytac_MDBT50Q
R_0201_0603Metric x 6
SW_SPST_B3U-1000P
SOT-23
C_0402_1005Metric x 8
D_SOD-323
C_0201_0603Metric
SOT-323_SC-70
C_0805_2012Metric
Anticipy_R1_E1_PROTOTYPE_PCB
