anticipation-labs/anticipy-hardware/02_PROTOTYPE_XIAO/02_CAD_PRINT/driver_max_8x4x2_gauge.stl

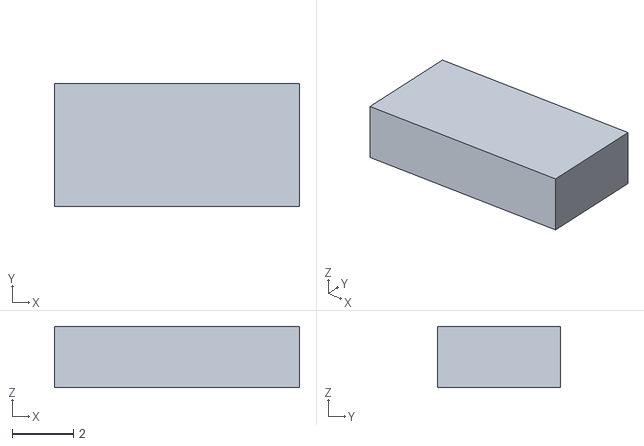
[picture p65: CAD file, 2026-09-06]
02_PROTOTYPE_XIAO/02_CAD_PRINT/driver_max_8x4x2_gauge.stl
8.00 x 4.00 x 2.00
