anticipation-labs/anticipy-hardware/02_PROTOTYPE_XIAO/CAD/PRINT_THESE/PRINT_TWO_PRIMARY_RENATA_ONLY_M2_keyed_retainer_posts_HEAD_DOWN.stl

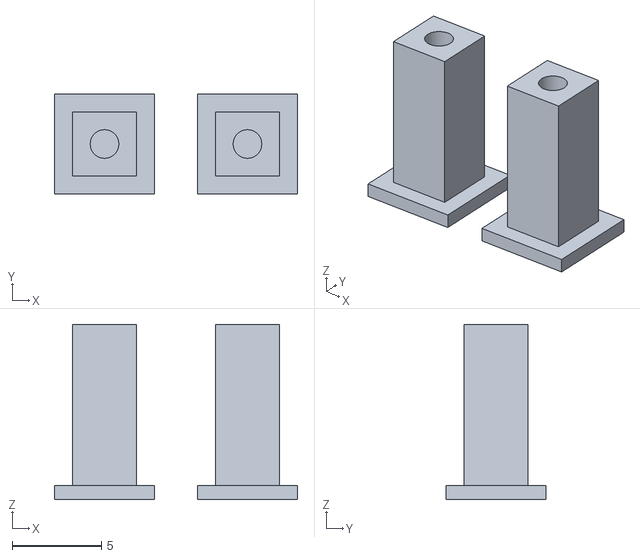
[picture p66: CAD file, 2026-09-06]
02_PROTOTYPE_XIAO/CAD/PRINT_THESE/PRINT_TWO_PRIMARY_RENATA_ONLY_M2_keyed_retainer_posts_HEAD_DOWN.stl
13.6 x 5.60 x 9.80
