anticipation-labs/anticipy-hardware/02_PROTOTYPE_XIAO/CAD/REFERENCE_ONLY_STEP/ALT_BENCH_ONLY_lower_fit_gauge_batt15_Vybronics10p2.step

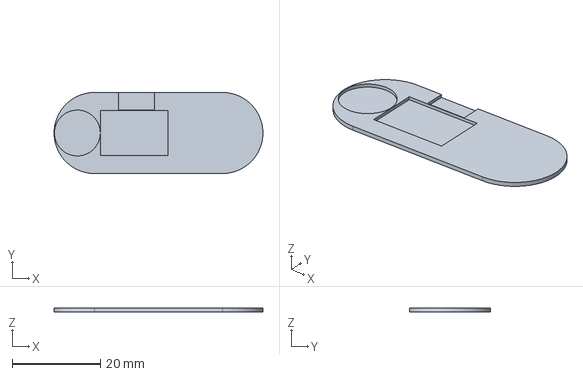
[picture p67: CAD file, 2026-09-06]
02_PROTOTYPE_XIAO/CAD/REFERENCE_ONLY_STEP/ALT_BENCH_ONLY_lower_fit_gauge_batt15_Vybronics10p2.step
47.4 x 18.4 x 0.8 mm
