anticipation-labs/anticipy-hardware/03_PCB/R0B_CHECKPOINT_NOT_FOR_FAB/02_Mechanical_CAD/ANT-PROD-R0B_PROVISIONAL_BOARD_OUTLINE.dxf

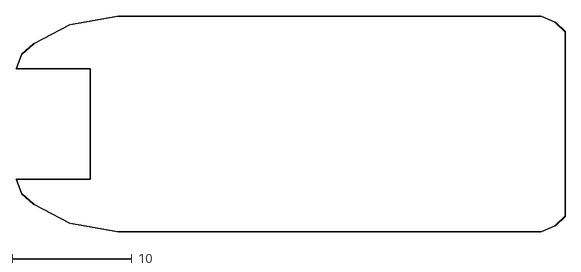
[picture p68: CAD file, 2026-09-06]
03_PCB/R0B_CHECKPOINT_NOT_FOR_FAB/02_Mechanical_CAD/ANT-PROD-R0B_PROVISIONAL_BOARD_OUTLINE.dxf
45.8 x 18.0
