anticipation-labs/anticipy-hardware/04_MECHANICAL/PRINT_READY/v09_button_plunger_1p7mm.stl

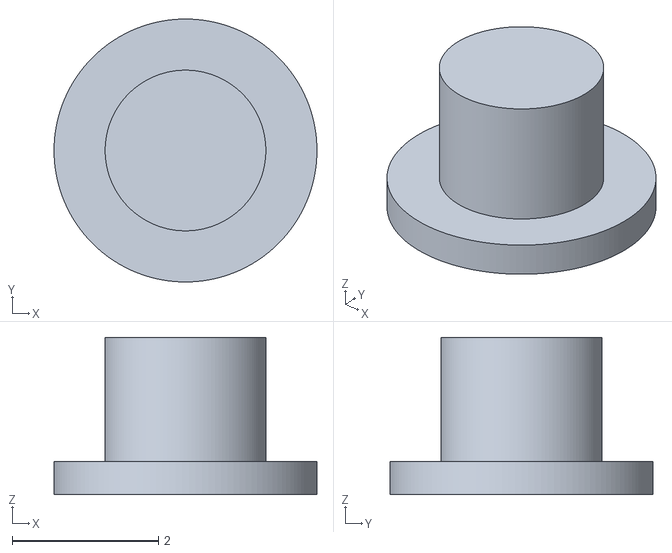
[picture p69: CAD file, 2026-09-06]
04_MECHANICAL/PRINT_READY/v09_button_plunger_1p7mm.stl
3.60 x 3.60 x 2.15
