anticipation-labs/anticipy-hardware/04_MECHANICAL/REFERENCE_STEP/production_button_boot.step

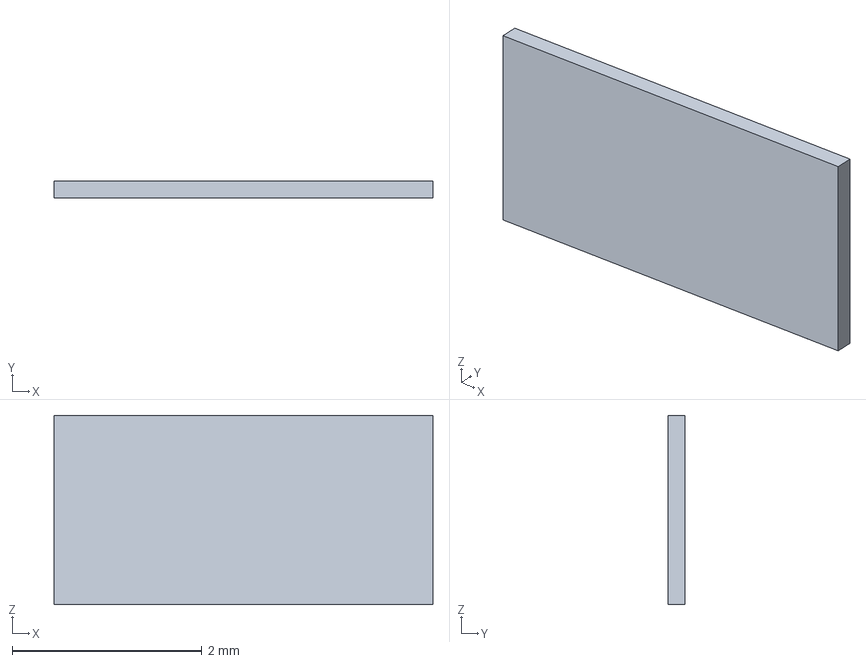
[picture p70: CAD file, 2026-09-06]
04_MECHANICAL/REFERENCE_STEP/production_button_boot.step
4.00 x 0.18 x 2.00 mm
