anticipation-labs/anticipy-hardware/06_FACTORY_AND_QA/QA_FIXTURES/step/drop_pose_key_18_E_YM_ZM.step

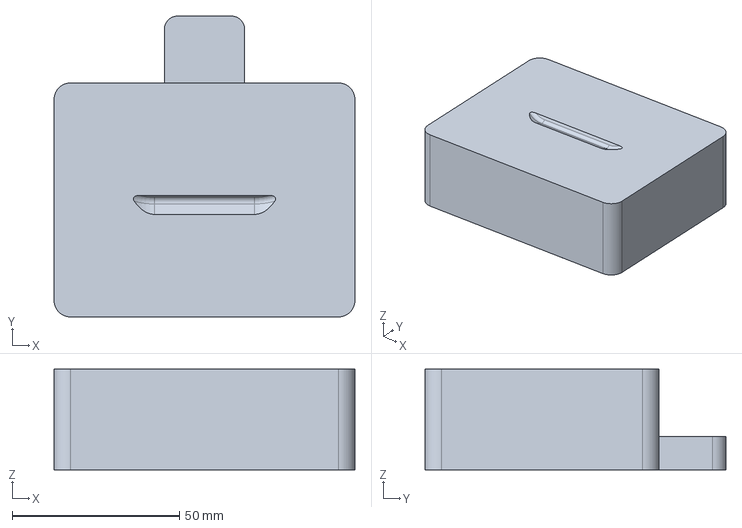
[picture p71: CAD file, 2026-09-06]
06_FACTORY_AND_QA/QA_FIXTURES/step/drop_pose_key_18_E_YM_ZM.step
90.0 x 90.0 x 30.1 mm
