anticipation-labs/anticipy-hardware/08_HISTORICAL_PACKAGES/2026-08-19_anticipy_shell_openscad/PRINT_ME_v5_3pendants.3mf

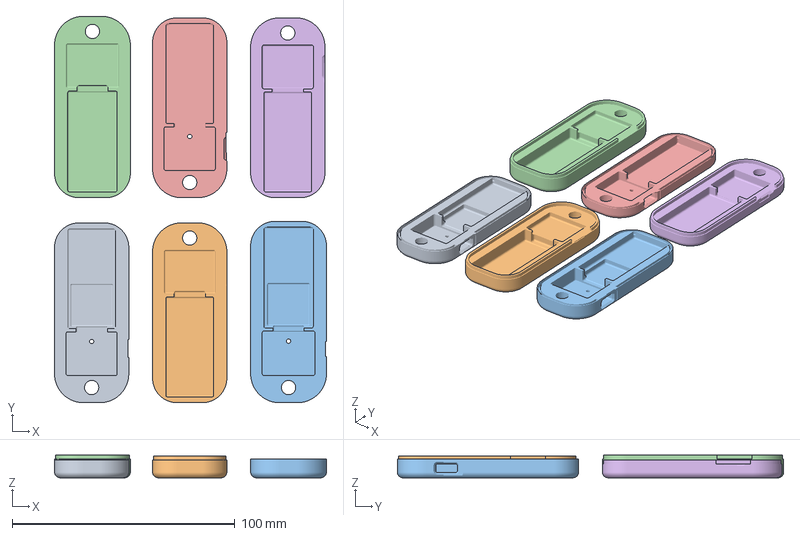
[picture p72: CAD file, 2026-09-06]
08_HISTORICAL_PACKAGES/2026-08-19_anticipy_shell_openscad/PRINT_ME_v5_3pendants.3mf
122.0 x 173.4 x 10.1 mm
V1-STORAGE front
V1-STORAGE back
V2-STORAGE-ROOMY front
V2-STORAGE-ROOMY back
V1-standard front
V1-standard back
