anticipation-labs/anticipy-hardware/08_HISTORICAL_PACKAGES/2026-08-27_v07_four_day_build_pack/mechanical/v07_button_plunger_4p3.step

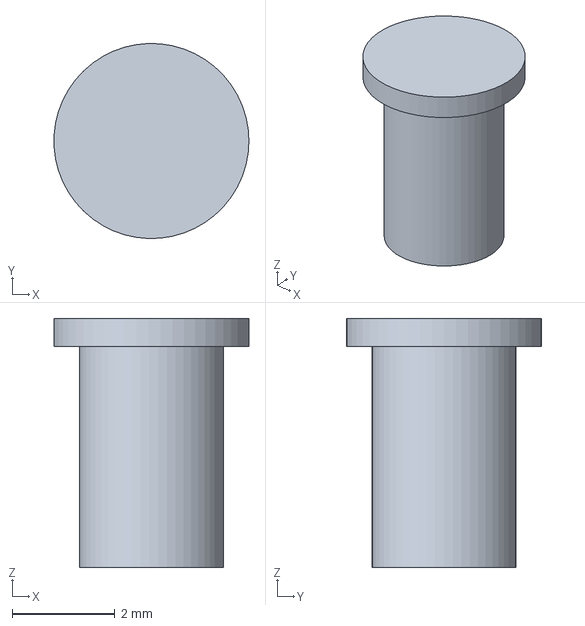
[picture p73: CAD file, 2026-09-06]
08_HISTORICAL_PACKAGES/2026-08-27_v07_four_day_build_pack/mechanical/v07_button_plunger_4p3.step
3.80 x 3.80 x 4.85 mm
