anticipation-labs/anticipy-hardware/08_HISTORICAL_PACKAGES/2026-08-28_48h_v13/01_PRINT/v13_button_plunger_2p0mm.stl

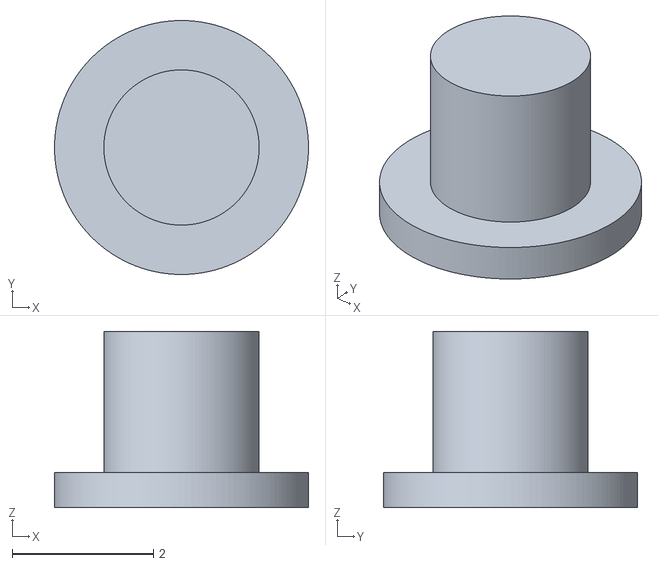
[picture p74: CAD file, 2026-09-06]
08_HISTORICAL_PACKAGES/2026-08-28_48h_v13/01_PRINT/v13_button_plunger_2p0mm.stl
3.60 x 3.60 x 2.50
