anticipation-labs/anticipy-hardware/08_HISTORICAL_PACKAGES/2026-08-28_execution_v1.0/01_PRINT_NOW/v09_dummy_motor_10x10x2p1.stl

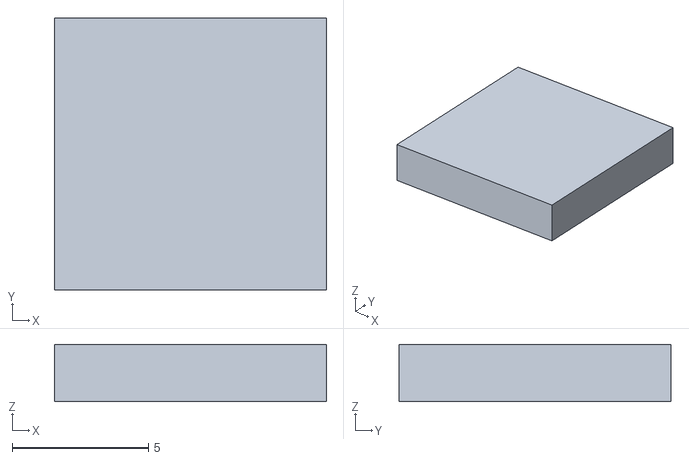
[picture p75: CAD file, 2026-09-06]
08_HISTORICAL_PACKAGES/2026-08-28_execution_v1.0/01_PRINT_NOW/v09_dummy_motor_10x10x2p1.stl
10.0 x 10.0 x 2.10
