anticipation-labs/anticipy-hardware/08_HISTORICAL_PACKAGES/2026-08-28_execution_v1.0/02_PRODUCTION_CAD/production_dummy_pcb_shaped_37.5x14x0.6.step

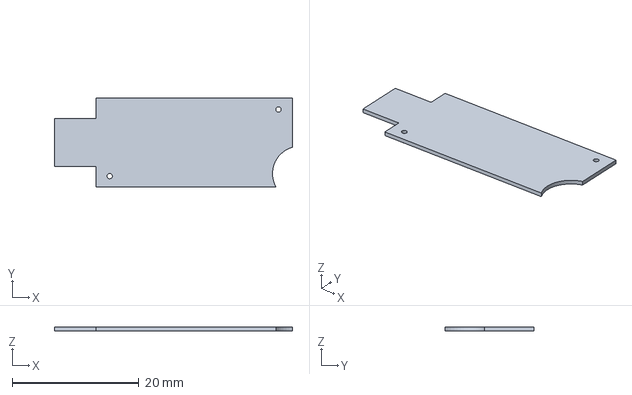
[picture p76: CAD file, 2026-09-06]
08_HISTORICAL_PACKAGES/2026-08-28_execution_v1.0/02_PRODUCTION_CAD/production_dummy_pcb_shaped_37.5x14x0.6.step
37.5 x 14.0 x 0.6 mm
