anticipation-labs/anticipy-hardware/08_HISTORICAL_PACKAGES/2026-08-28_execution_v1.0/05_QA_FIXTURES/step/drop_pose_key_03_F_YP.step

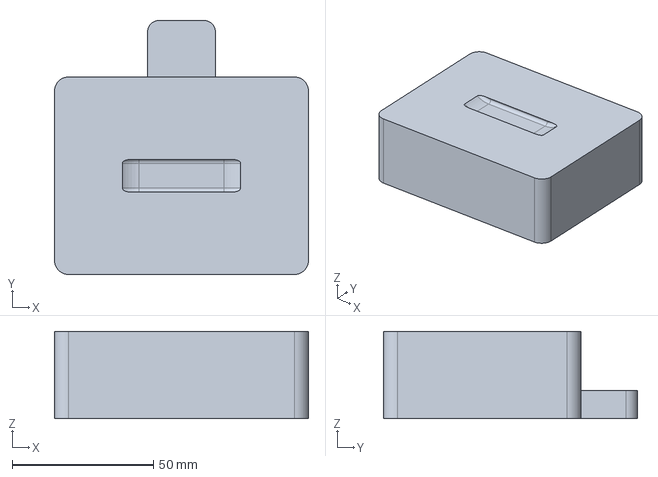
[picture p77: CAD file, 2026-09-06]
08_HISTORICAL_PACKAGES/2026-08-28_execution_v1.0/05_QA_FIXTURES/step/drop_pose_key_03_F_YP.step
90.0 x 90.0 x 31.0 mm
