anticipation-labs/anticipy-hardware/08_HISTORICAL_PACKAGES/2026-08-28_p2s_v07_enclosure/P2S_v07_fit_gauges.3mf

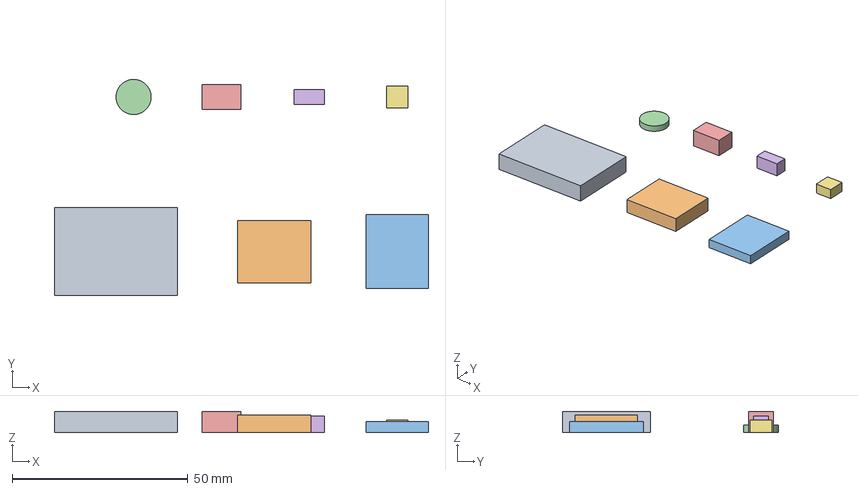
[picture p78: CAD file, 2026-09-06]
08_HISTORICAL_PACKAGES/2026-08-28_p2s_v07_enclosure/P2S_v07_fit_gauges.3mf
106.4 x 61.5 x 6.00 mm
v07_dummy_battery_35x25x6.stl
v07_dummy_audio_bff_21x17p7x5.stl
v07_dummy_xiao_rotated_17p8x21x3p2.stl
v07_dummy_motor_10x2p1.stl
v07_dummy_haptic_cap_cluster_11x7x6.stl
v07_dummy_switch_8p6x4p3x4p7.stl
v07_dummy_button_6p2x6p2x3p5.stl
