anticipation-labs/anticipy-hardware/08_HISTORICAL_PACKAGES/2026-08-28_tuesday_evt_v0.1/dummy_protected_502025_200_mah_lipo.stl

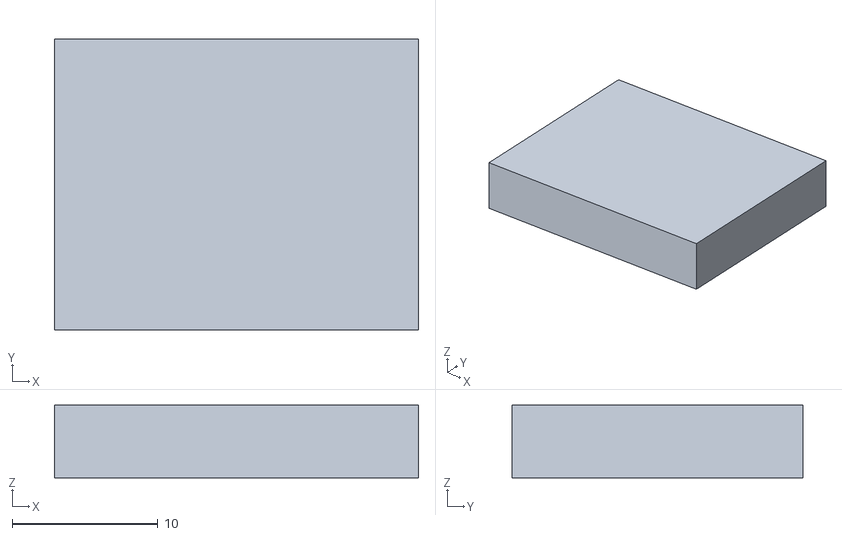
[picture p79: CAD file, 2026-09-06]
08_HISTORICAL_PACKAGES/2026-08-28_tuesday_evt_v0.1/dummy_protected_502025_200_mah_lipo.stl
25.0 x 20.0 x 5.00
