anticipation-labs/anticipy-hardware/08_HISTORICAL_PACKAGES/2026-09-05_master_package/02_XIAO_NO_LEES_REFERENCE/02_CAD_PRINT/midband_4p50mm_loose.stl

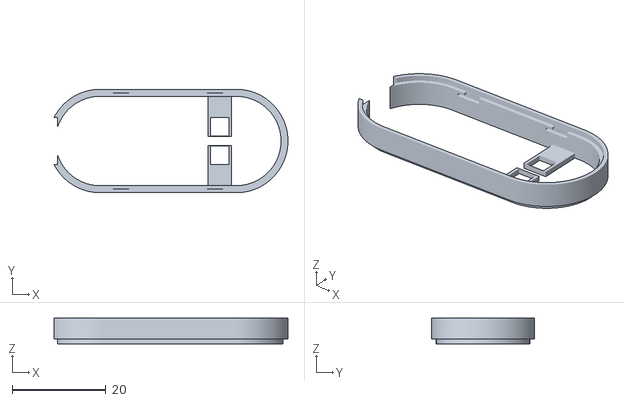
[picture p80: CAD file, 2026-09-06]
08_HISTORICAL_PACKAGES/2026-09-05_master_package/02_XIAO_NO_LEES_REFERENCE/02_CAD_PRINT/midband_4p50mm_loose.stl
49.8 x 22.0 x 5.50
