anticipation-labs/anticipy-hardware/08_HISTORICAL_PACKAGES/2026-09-05_master_package/03_XIAO_ALL_CAD/PRINT_THESE/ordered_shell_midband_rise_4p50mm_loose_tongue.stl

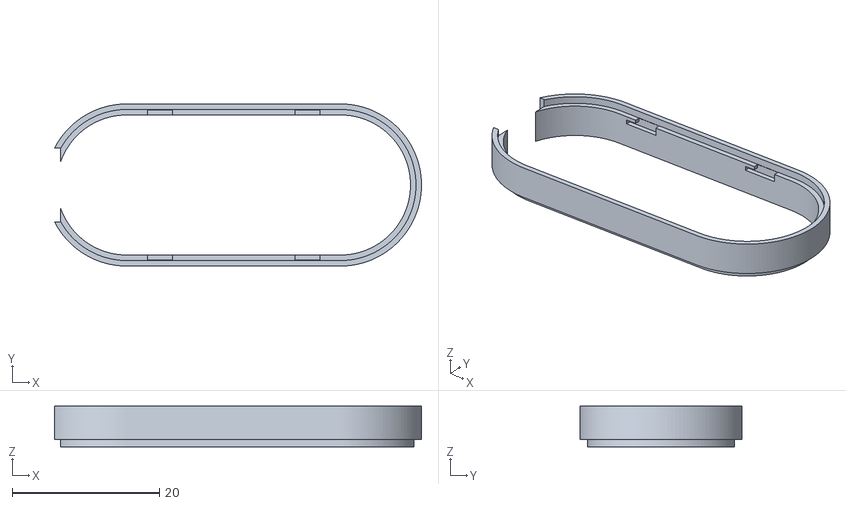
[picture p81: CAD file, 2026-09-06]
08_HISTORICAL_PACKAGES/2026-09-05_master_package/03_XIAO_ALL_CAD/PRINT_THESE/ordered_shell_midband_rise_4p50mm_loose_tongue.stl
49.8 x 22.0 x 5.50
