anticipation-labs/anticipy-hardware/latest_builds/E1P1/cad/Rear_Service_Cover.step

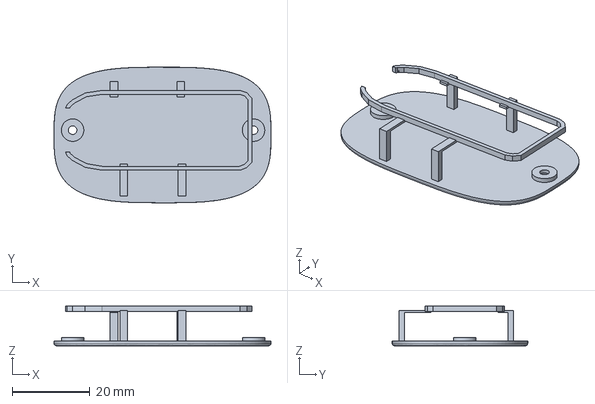
[picture p82: CAD file, 2026-09-10]
latest_builds/E1P1/cad/Rear_Service_Cover.step
56.0 x 35.0 x 10.3 mm
