anticipation-labs/anticipy-hardware/latest_builds/E1P1/pcb/electrical/models/Resistor_SMD__R_0201_0603Metric.step

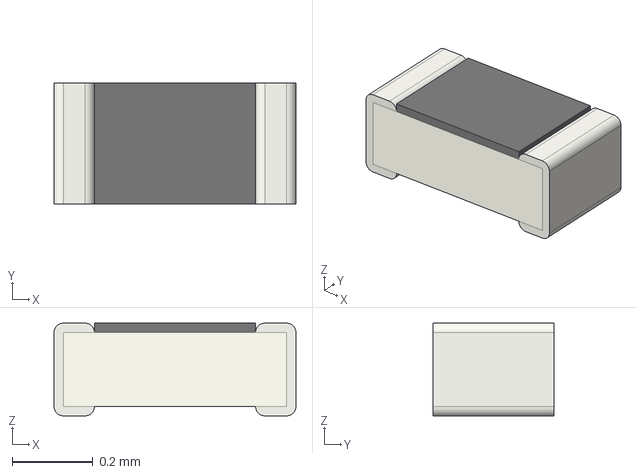
[picture p83: CAD file, 2026-09-10]
latest_builds/E1P1/pcb/electrical/models/Resistor_SMD__R_0201_0603Metric.step
0.6 x 0.3 x 0.23 mm
