anticipation-labs/anticipy-hardware/04_MECHANICAL/OPENSCAD_SHELL_PROGRAM_v5.1/COUPON_FIRST.3mf

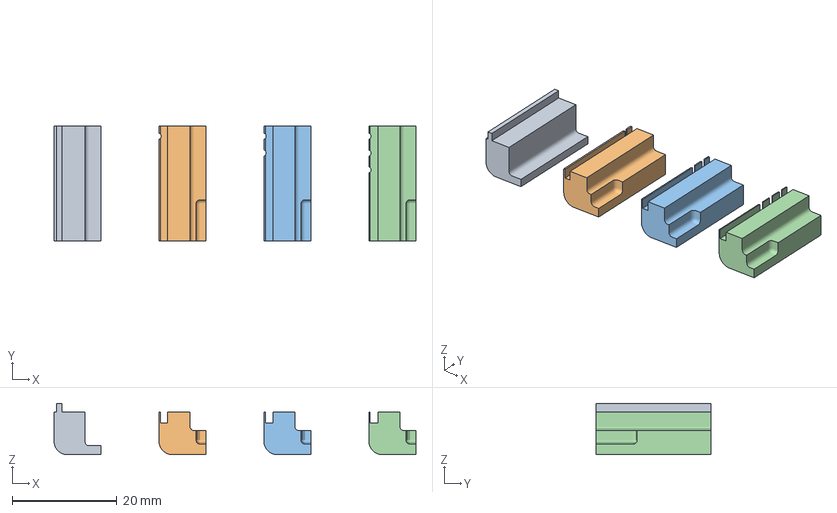
[picture p84: CAD file, 2026-09-06]
04_MECHANICAL/OPENSCAD_SHELL_PROGRAM_v5.1/COUPON_FIRST.3mf
69.0 x 22.0 x 9.80 mm
tongue (mate against each front)
groove 0.16 - 1 notch
groove 0.22 - 2 notches
groove 0.28 - 3 notches
