anticipation-labs/anticipy-hardware/04_MECHANICAL/OPENSCAD_SHELL_PROGRAM_v5.1/stl/pendant_v4_back.stl

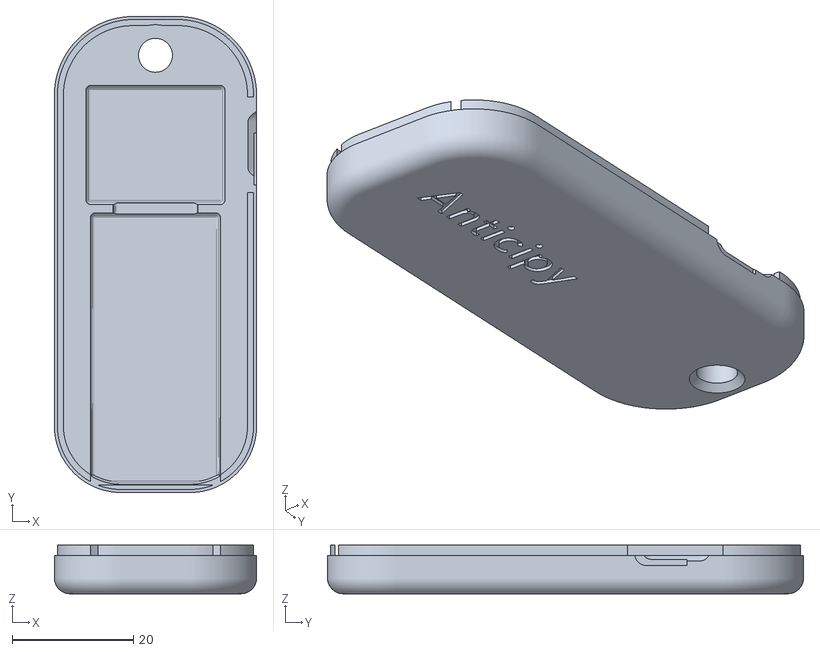
[picture p85: CAD file, 2026-09-06]
04_MECHANICAL/OPENSCAD_SHELL_PROGRAM_v5.1/stl/pendant_v4_back.stl
33.3 x 78.5 x 8.00
