anticipation-labs/anticipy-hardware/04_MECHANICAL/PRINT_READY/Anticipy_v09_five_units_P2S.3mf

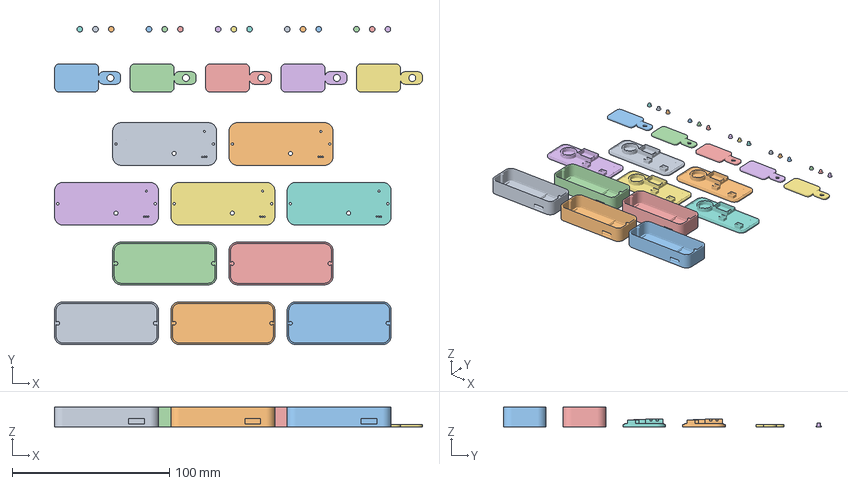
[picture p86: CAD file, 2026-09-06]
04_MECHANICAL/PRINT_READY/Anticipy_v09_five_units_P2S.3mf
234.1 x 202.4 x 12.6 mm
unit_1_base
unit_2_base
unit_3_base
unit_4_base
unit_5_base
unit_1_lid_exterior_face_down
unit_2_lid_exterior_face_down
unit_3_lid_exterior_face_down
unit_4_lid_exterior_face_down
unit_5_lid_exterior_face_down
unit_1_lanyard_backplate
unit_2_lanyard_backplate
unit_3_lanyard_backplate
unit_4_lanyard_backplate
unit_5_lanyard_backplate
unit_1_plunger_1.7mm
unit_1_plunger_1.9mm
unit_1_plunger_2.1mm
unit_2_plunger_1.7mm
unit_2_plunger_1.9mm
unit_2_plunger_2.1mm
unit_3_plunger_1.7mm
unit_3_plunger_1.9mm
unit_3_plunger_2.1mm
unit_4_plunger_1.7mm
unit_4_plunger_1.9mm
unit_4_plunger_2.1mm
unit_5_plunger_1.7mm
unit_5_plunger_1.9mm
unit_5_plunger_2.1mm
