anticipation-labs/anticipy-hardware/04_MECHANICAL/PRINT_READY/xiao_prototype_plates/PRINT_DECK_DOWN_then_FLIP_battery_safety_bridge.stl

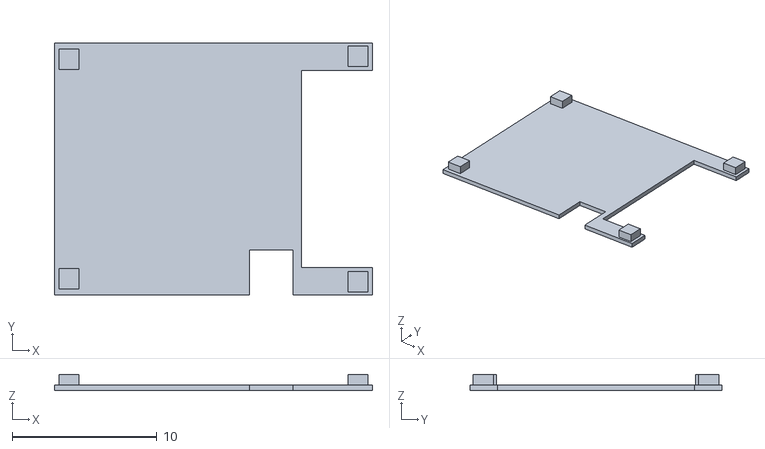
[picture p87: CAD file, 2026-09-06]
04_MECHANICAL/PRINT_READY/xiao_prototype_plates/PRINT_DECK_DOWN_then_FLIP_battery_safety_bridge.stl
22.0 x 17.4 x 1.13
