anticipation-labs/anticipy-hardware/04_MECHANICAL/REFERENCE_STEP/production_dummy_radio_AN54LV_8.4x6.4x1.5.step

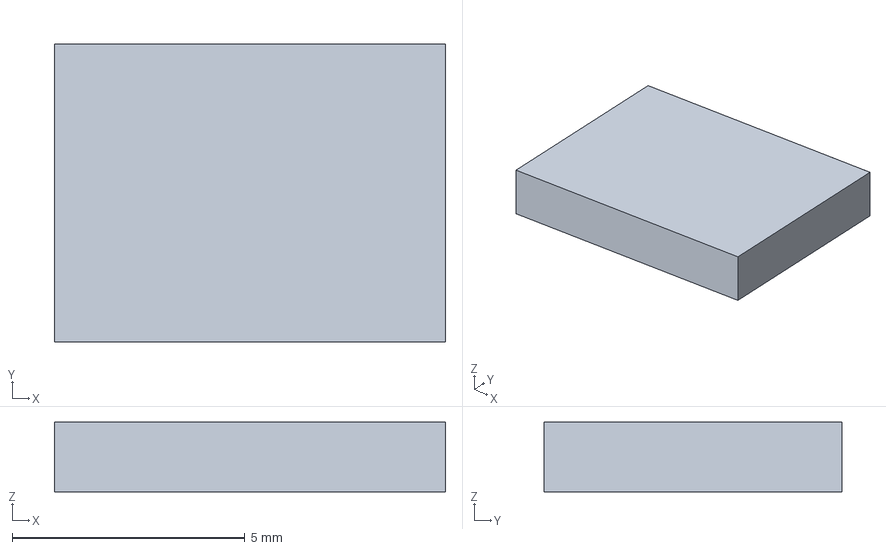
[picture p88: CAD file, 2026-09-06]
04_MECHANICAL/REFERENCE_STEP/production_dummy_radio_AN54LV_8.4x6.4x1.5.step
8.40 x 6.40 x 1.50 mm
