anticipation-labs/anticipy-hardware/08_HISTORICAL_PACKAGES/2026-08-19_anticipy_shell_openscad/PRINT_P1S_3pendants.3mf

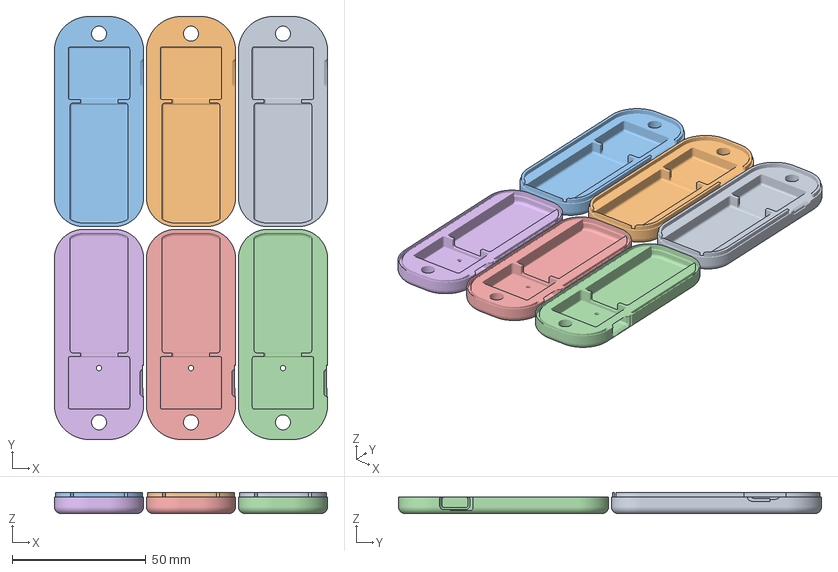
[picture p89: CAD file, 2026-09-06]
08_HISTORICAL_PACKAGES/2026-08-19_anticipy_shell_openscad/PRINT_P1S_3pendants.3mf
102.0 x 157.9 x 8.00 mm
pendant1-back
pendant2-back
pendant3-back
pendant1-front
pendant2-front
pendant3-front
