anticipation-labs/anticipy-hardware/08_HISTORICAL_PACKAGES/2026-08-19_anticipy_shell_openscad/stl_v5/v5_bat200_back.stl

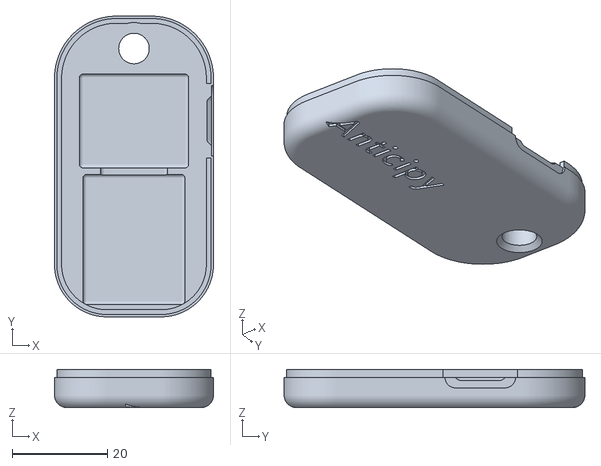
[picture p90: CAD file, 2026-09-06]
08_HISTORICAL_PACKAGES/2026-08-19_anticipy_shell_openscad/stl_v5/v5_bat200_back.stl
33.3 x 63.1 x 8.00
