anticipation-labs/anticipy-hardware/08_HISTORICAL_PACKAGES/2026-08-27_v07_four_day_build_pack/mechanical/v07_dummy_audio_bff_21x17p7x5.step

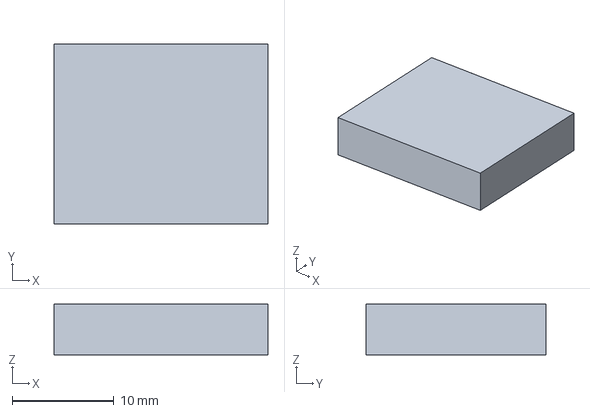
[picture p91: CAD file, 2026-09-06]
08_HISTORICAL_PACKAGES/2026-08-27_v07_four_day_build_pack/mechanical/v07_dummy_audio_bff_21x17p7x5.step
21.0 x 17.7 x 5.00 mm
