anticipation-labs/anticipy-hardware/08_HISTORICAL_PACKAGES/2026-08-28_48h_v13/01_PRINT/v13_dummy_haptic_driver.stl

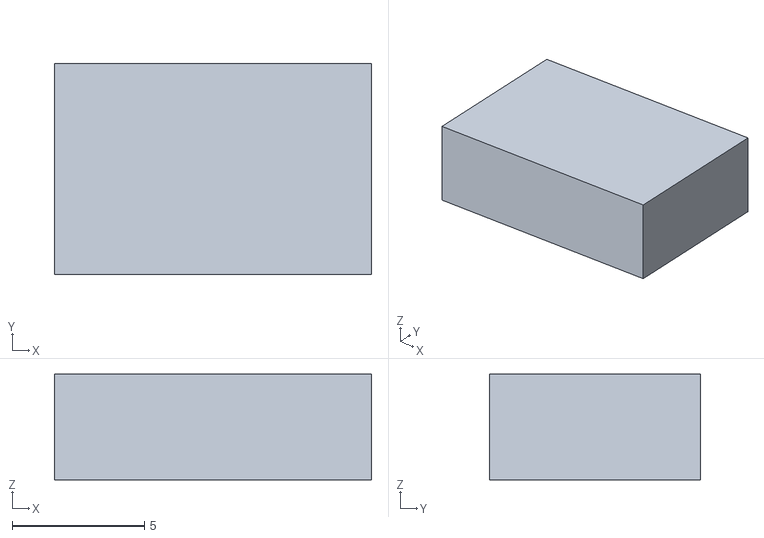
[picture p92: CAD file, 2026-09-06]
08_HISTORICAL_PACKAGES/2026-08-28_48h_v13/01_PRINT/v13_dummy_haptic_driver.stl
12.0 x 8.00 x 4.00
