anticipation-labs/anticipy-hardware/08_HISTORICAL_PACKAGES/2026-08-28_execution_v1.0/05_QA_FIXTURES/step/drop_pose_key_14_E_XM_ZM.step

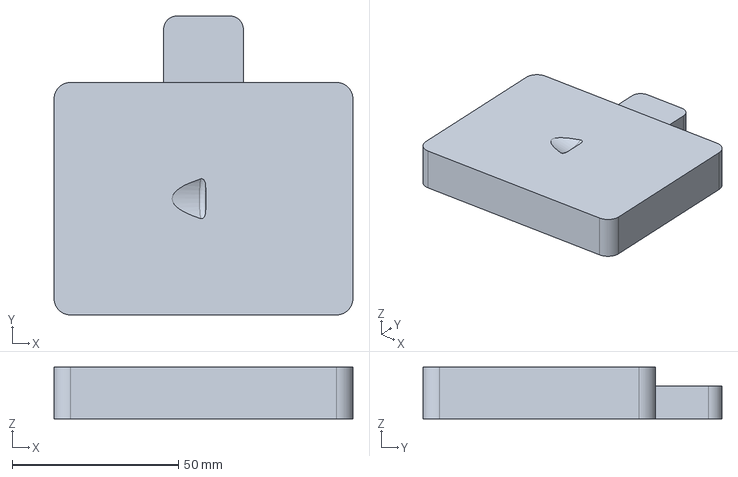
[picture p93: CAD file, 2026-09-06]
08_HISTORICAL_PACKAGES/2026-08-28_execution_v1.0/05_QA_FIXTURES/step/drop_pose_key_14_E_XM_ZM.step
90.0 x 90.0 x 15.6 mm
