anticipation-labs/anticipy-hardware/08_HISTORICAL_PACKAGES/2026-09-05_master_package/03_XIAO_ALL_CAD/PRINT_THESE/MEASURE_XIAO_official_bbox_22p482x17p78x4p46.stl

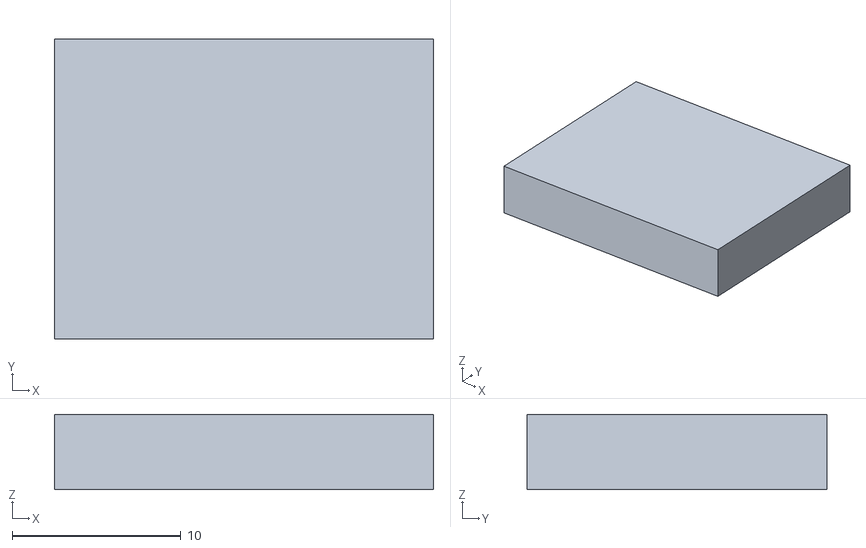
[picture p95: CAD file, 2026-09-06]
08_HISTORICAL_PACKAGES/2026-09-05_master_package/03_XIAO_ALL_CAD/PRINT_THESE/MEASURE_XIAO_official_bbox_22p482x17p78x4p46.stl
22.5 x 17.8 x 4.46
