anticipation-labs/anticipy-hardware/latest_builds/E1P1/cad/Clear_Lightpipe.step

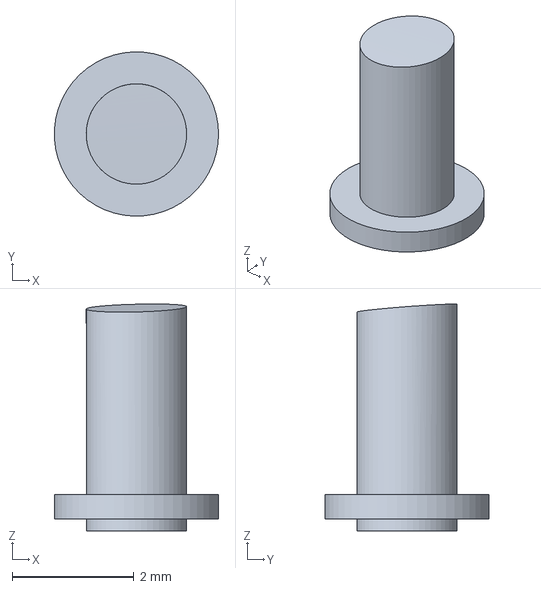
[picture p96: CAD file, 2026-09-10]
latest_builds/E1P1/cad/Clear_Lightpipe.step
2.70 x 2.70 x 3.73 mm
