anticipation-labs/anticipy-hardware/latest_builds/E1P1/pcb/electrical/models/Package_TO_SOT_SMD__Texas_DRT-3.step

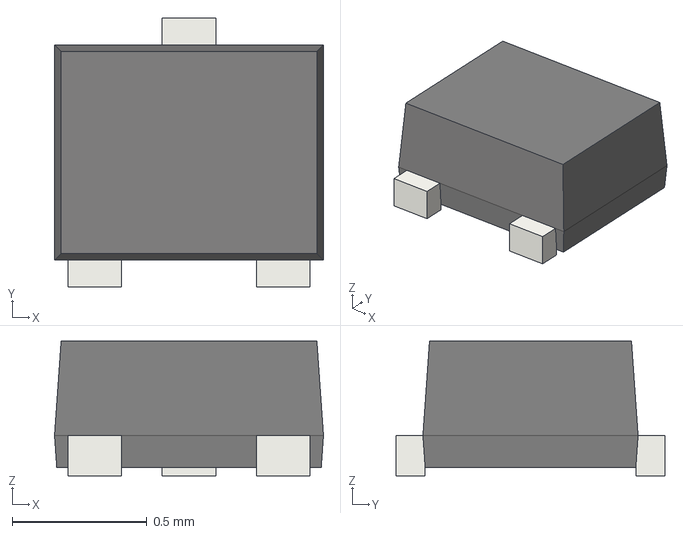
[picture p97: CAD file, 2026-09-10]
latest_builds/E1P1/pcb/electrical/models/Package_TO_SOT_SMD__Texas_DRT-3.step
1.00 x 1.00 x 0.5 mm
