anticipation-labs/anticipy-hardware/04_MECHANICAL/OPENSCAD_SHELL_PROGRAM_v5.1/stl_v5/v5_bat200_front.stl

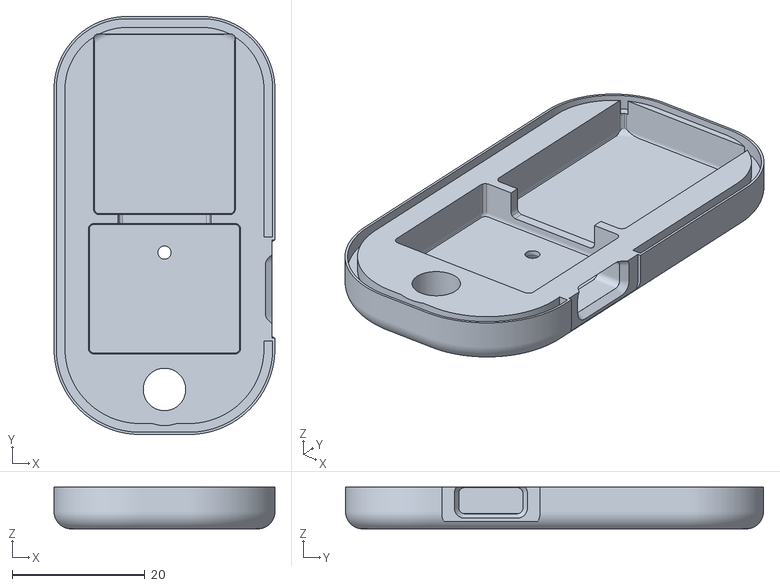
[picture p98: CAD file, 2026-09-06]
04_MECHANICAL/OPENSCAD_SHELL_PROGRAM_v5.1/stl_v5/v5_bat200_front.stl
33.3 x 63.1 x 6.30
