anticipation-labs/anticipy-hardware/04_MECHANICAL/PRINT_READY/v09_compact_lid.step

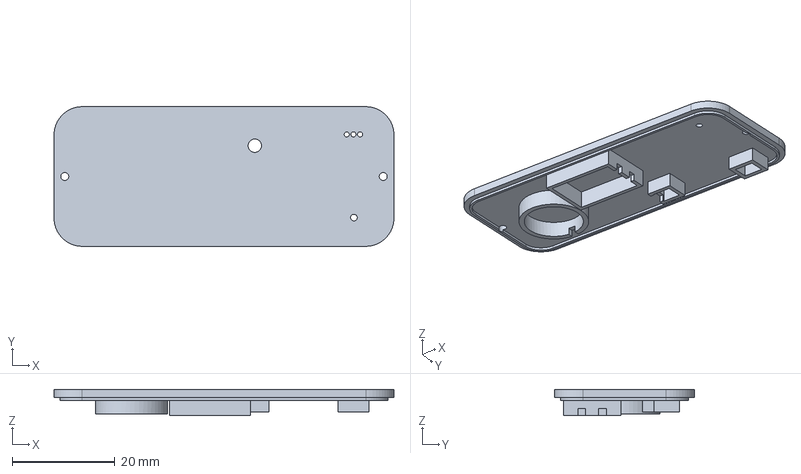
[picture p99: CAD file, 2026-09-06]
04_MECHANICAL/PRINT_READY/v09_compact_lid.step
66.2 x 27.2 x 5.15 mm
