anticipation-labs/anticipy-hardware/04_MECHANICAL/PRINT_READY/xiao_prototype_plates/PLAN_B_BENCH_ONLY_lower_fit_gauge_DTP401525_Vybronics_driver_rotated.stl

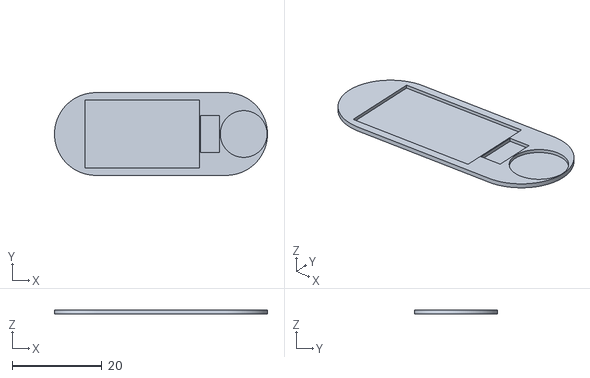
[picture p100: CAD file, 2026-09-06]
04_MECHANICAL/PRINT_READY/xiao_prototype_plates/PLAN_B_BENCH_ONLY_lower_fit_gauge_DTP401525_Vybronics_driver_rotated.stl
47.4 x 18.4 x 0.8
