anticipation-labs/anticipy-hardware/08_HISTORICAL_PACKAGES/2026-08-19_anticipy_shell_openscad/stl_v5/v5s_v2_front.stl

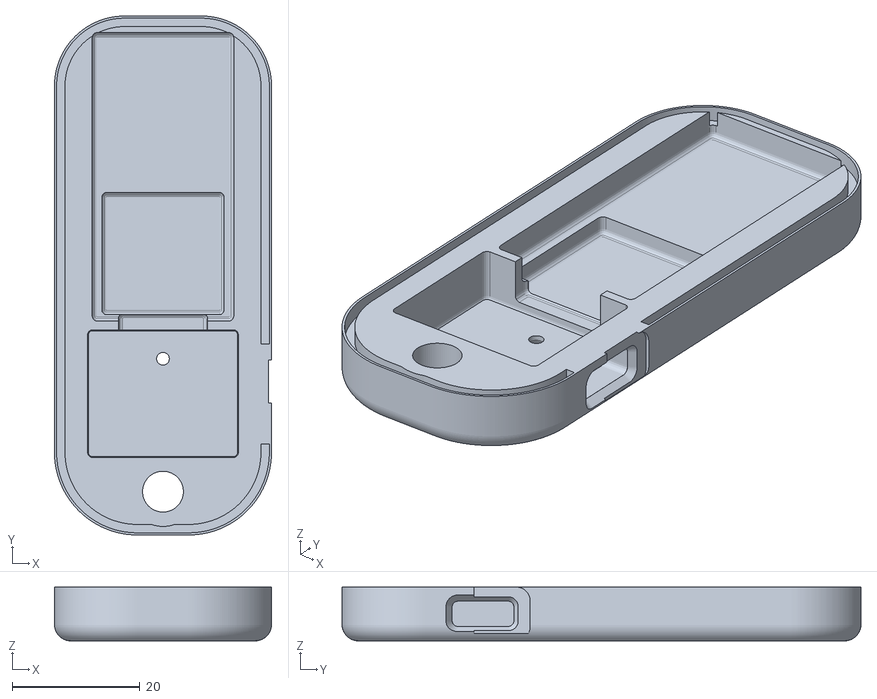
[picture p101: CAD file, 2026-09-06]
08_HISTORICAL_PACKAGES/2026-08-19_anticipy_shell_openscad/stl_v5/v5s_v2_front.stl
34.0 x 81.4 x 8.45
