anticipation-labs/anticipy-hardware/08_HISTORICAL_PACKAGES/2026-08-28_48h_v13/01_PRINT/v13_dummy_XIAO_SD_stack.stl

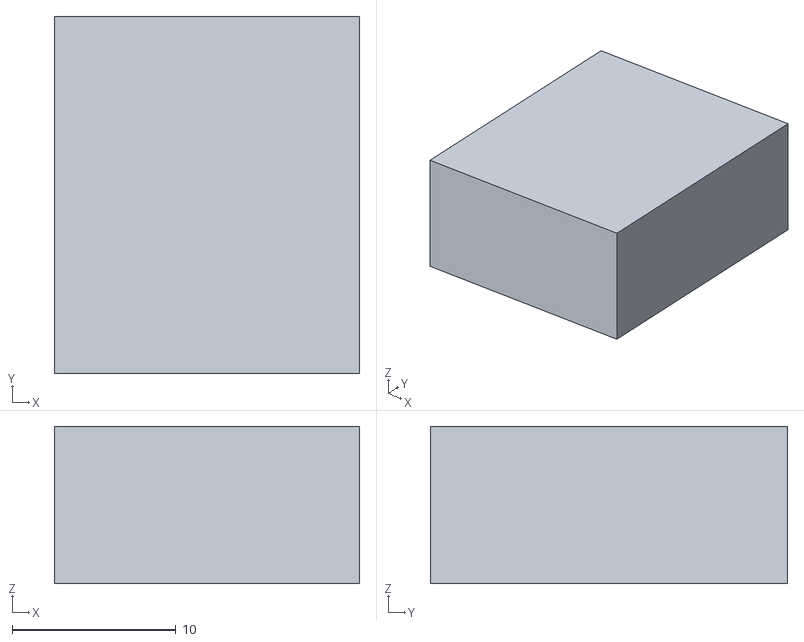
[picture p103: CAD file, 2026-09-06]
08_HISTORICAL_PACKAGES/2026-08-28_48h_v13/01_PRINT/v13_dummy_XIAO_SD_stack.stl
18.6 x 21.8 x 9.60
