anticipation-labs/anticipy-hardware/08_HISTORICAL_PACKAGES/2026-08-28_execution_v1.0/01_PRINT_NOW/v09_dummy_board_stack_17p8x21x7p0.stl

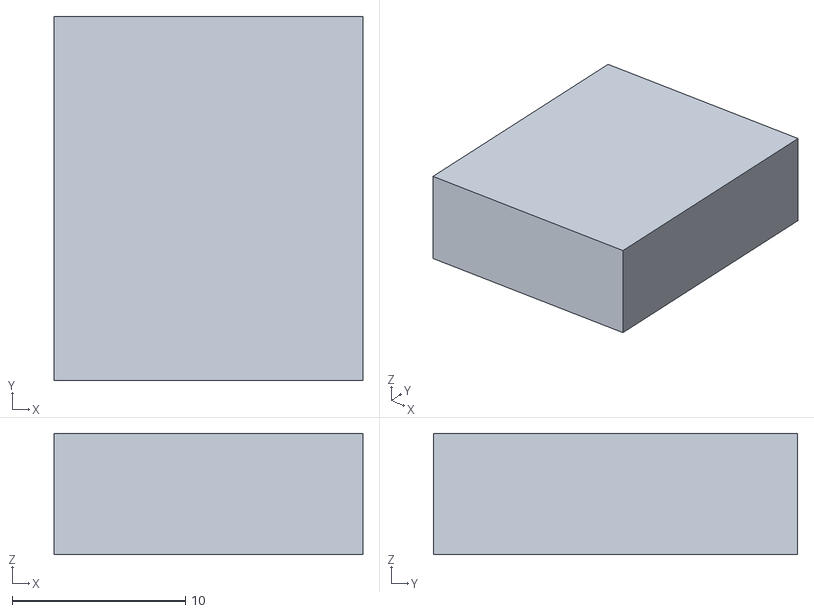
[picture p104: CAD file, 2026-09-06]
08_HISTORICAL_PACKAGES/2026-08-28_execution_v1.0/01_PRINT_NOW/v09_dummy_board_stack_17p8x21x7p0.stl
17.8 x 21.0 x 7.00
