anticipation-labs/anticipy-hardware/08_HISTORICAL_PACKAGES/2026-08-28_tuesday_evt_v0.1/anticipy_strict_evt_12_accessory_sets_plate.stl

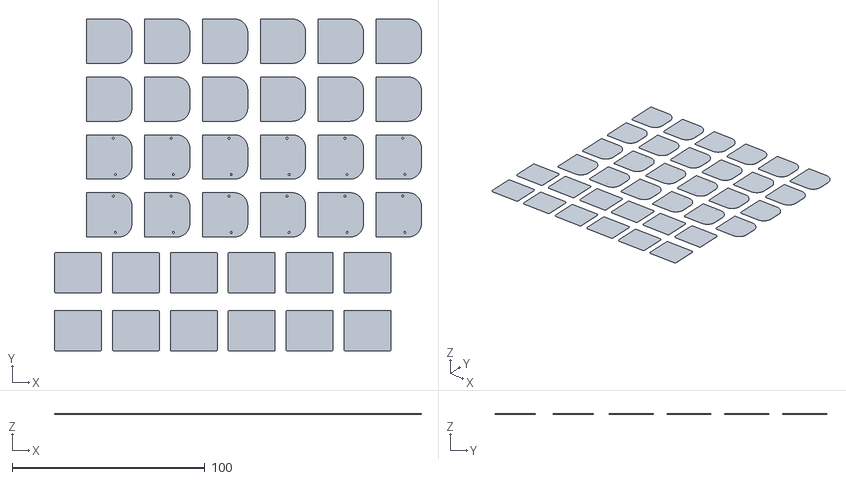
[picture p106: CAD file, 2026-09-06]
08_HISTORICAL_PACKAGES/2026-08-28_tuesday_evt_v0.1/anticipy_strict_evt_12_accessory_sets_plate.stl
190.2 x 172.1 x 0.635
