anticipation-labs/anticipy-hardware/latest_builds/E1P1/cad/Oval_E1_Three_Print_Parts_GEOMETRY_ONLY.3mf

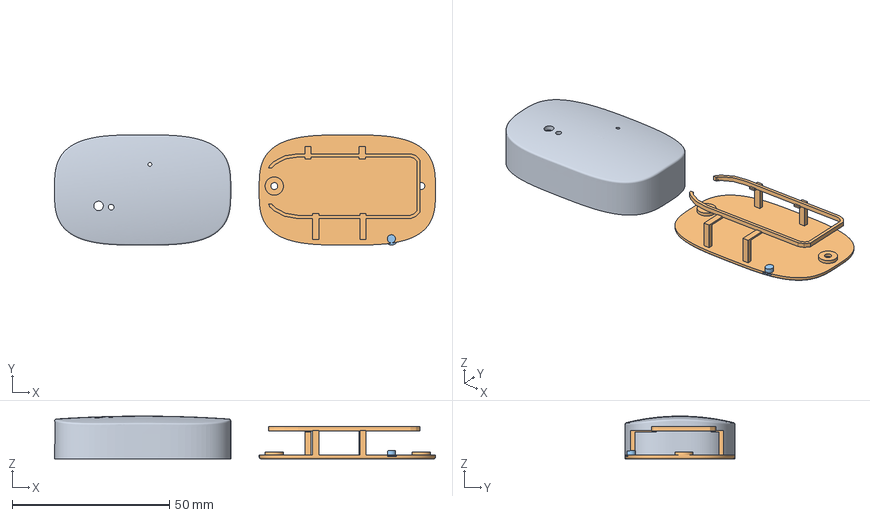
[picture p107: CAD file, 2026-09-10]
latest_builds/E1P1/cad/Oval_E1_Three_Print_Parts_GEOMETRY_ONLY.3mf
121.0 x 35.0 x 13.6 mm
Front_Oval_Shell
Rear_Service_Cover
Button_Plunger
