anticipation-labs/anticipy-hardware/latest_builds/E1P1/pcb/electrical/models/Inductor_SMD__L_Murata_DFE201610P.step

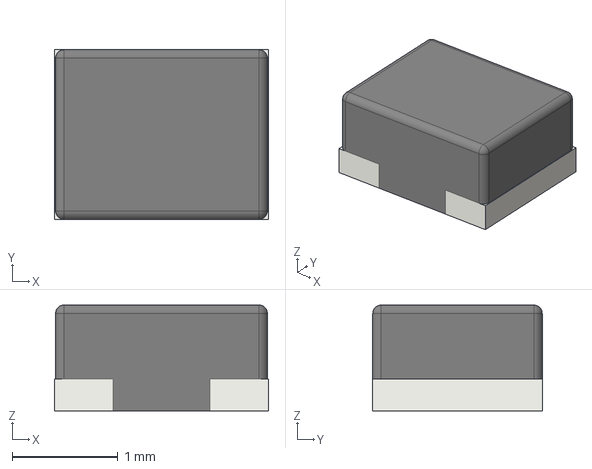
[picture p108: CAD file, 2026-09-10]
latest_builds/E1P1/pcb/electrical/models/Inductor_SMD__L_Murata_DFE201610P.step
2.02 x 1.60 x 1.00 mm
