anticipation-labs/anticipy-hardware/02_PROTOTYPE_XIAO/CAD/REFERENCE_ONLY_STEP/MEASURE_MAX_Vybronics_VCLP1020B002L_10p2x2p3.step

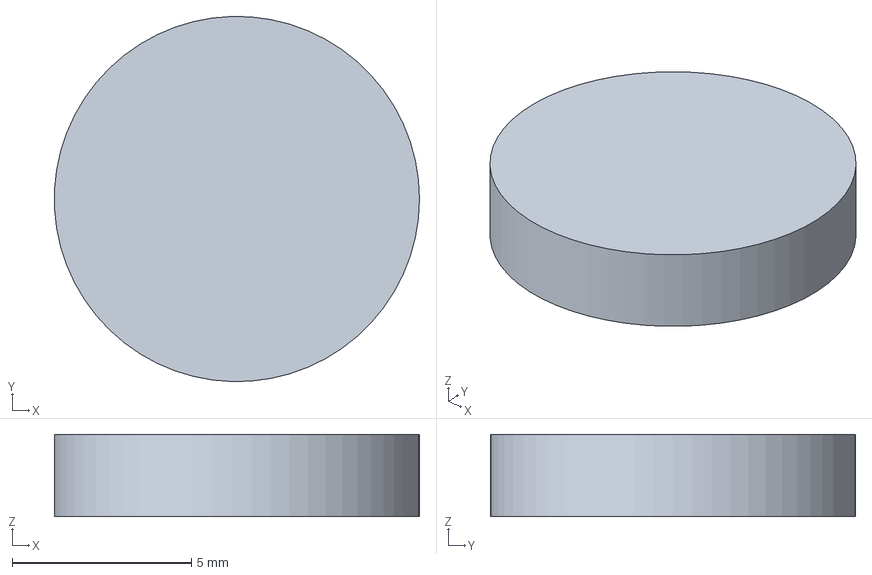
[picture p109: CAD file, 2026-09-06]
02_PROTOTYPE_XIAO/CAD/REFERENCE_ONLY_STEP/MEASURE_MAX_Vybronics_VCLP1020B002L_10p2x2p3.step
10.2 x 10.2 x 2.30 mm
