anticipation-labs/anticipy-hardware/04_MECHANICAL/PRINT_READY/v09_dummy_button_B3U_3x2p5x1p6.stl

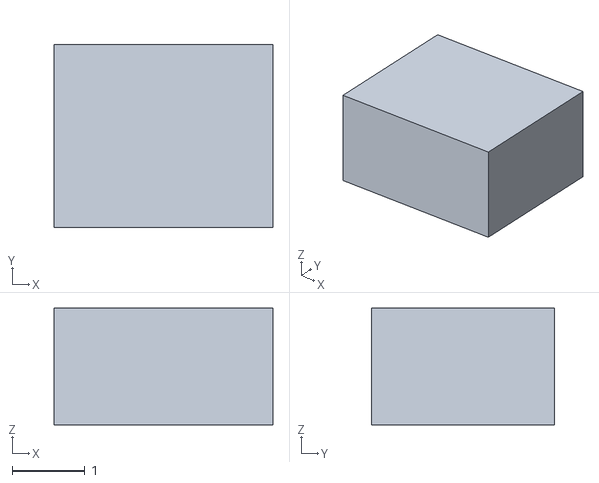
[picture p111: CAD file, 2026-09-06]
04_MECHANICAL/PRINT_READY/v09_dummy_button_B3U_3x2p5x1p6.stl
3.00 x 2.50 x 1.60
