anticipation-labs/anticipy-hardware/06_FACTORY_AND_QA/QA_FIXTURES/step/drop_three_cord_lift_yoke_petg.step

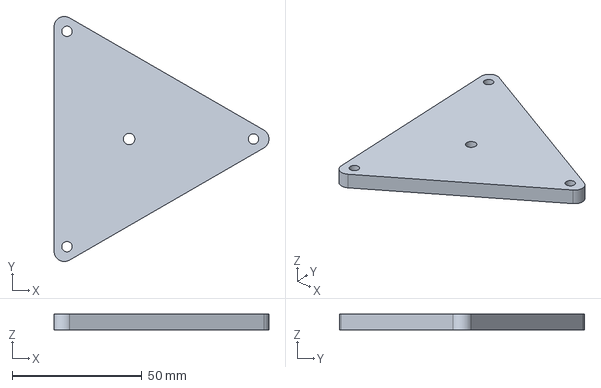
[picture p112: CAD file, 2026-09-06]
06_FACTORY_AND_QA/QA_FIXTURES/step/drop_three_cord_lift_yoke_petg.step
83.0 x 94.6 x 6.00 mm
