anticipation-labs/anticipy-hardware/08_HISTORICAL_PACKAGES/2026-08-19_anticipy_shell_openscad/stl/pendant_v4_front.stl

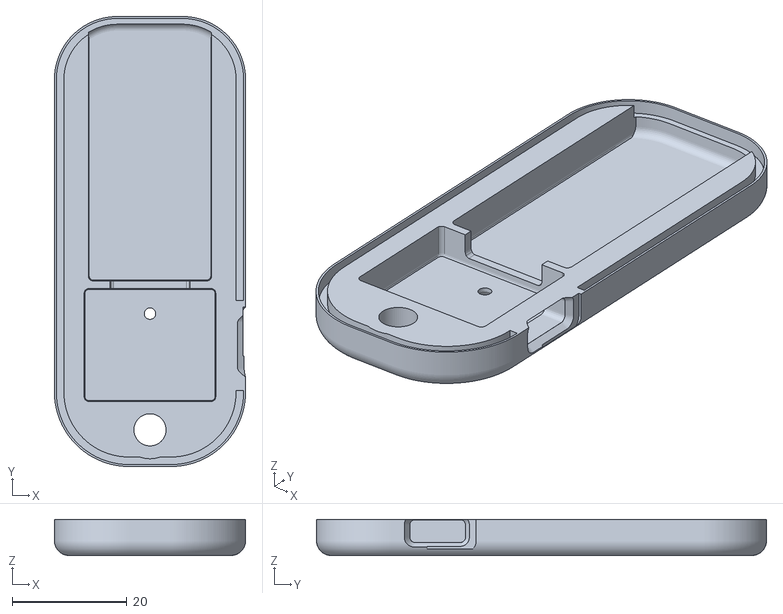
[picture p113: CAD file, 2026-09-06]
08_HISTORICAL_PACKAGES/2026-08-19_anticipy_shell_openscad/stl/pendant_v4_front.stl
33.3 x 78.5 x 6.30
