anticipation-labs/anticipy-hardware/08_HISTORICAL_PACKAGES/2026-08-28_48h_v13/01_PRINT/v13_dummy_BBM_602535_battery.stl

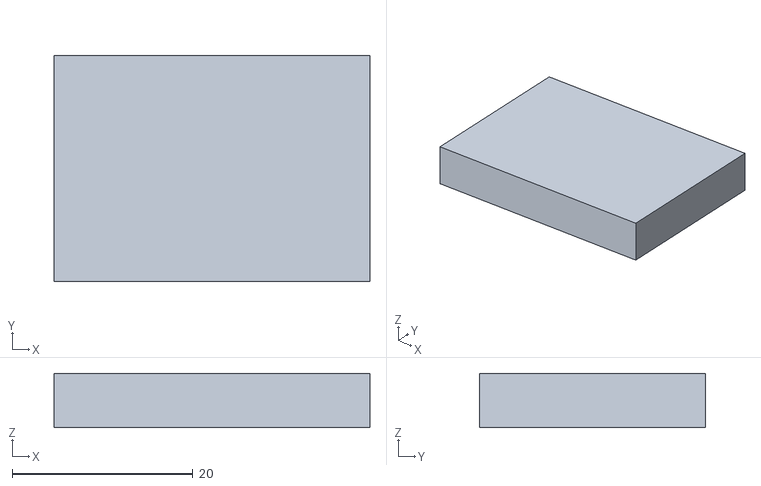
[picture p114: CAD file, 2026-09-06]
08_HISTORICAL_PACKAGES/2026-08-28_48h_v13/01_PRINT/v13_dummy_BBM_602535_battery.stl
35.0 x 25.0 x 6.00
