anticipation-labs/anticipy-hardware/08_HISTORICAL_PACKAGES/2026-08-28_execution_v1.0/02_PRODUCTION_CAD/production_dummy_battery_27x12.5x6.step

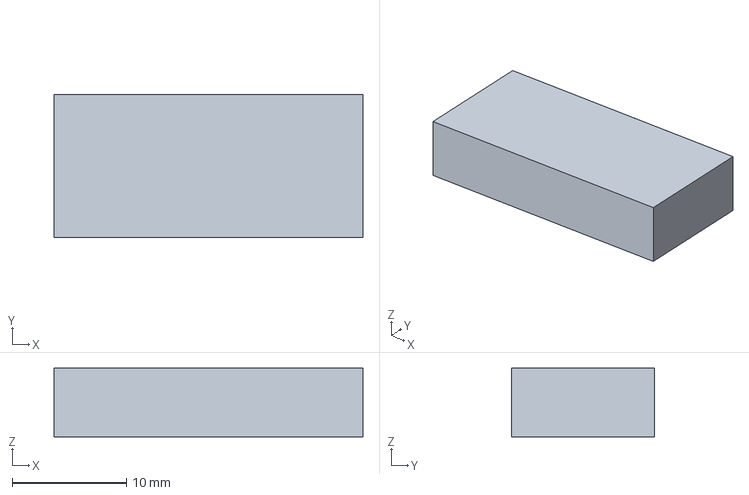
[picture p115: CAD file, 2026-09-06]
08_HISTORICAL_PACKAGES/2026-08-28_execution_v1.0/02_PRODUCTION_CAD/production_dummy_battery_27x12.5x6.step
27.0 x 12.5 x 6.00 mm
