anticipation-labs/anticipy-hardware/08_HISTORICAL_PACKAGES/2026-08-28_execution_v1.0/05_QA_FIXTURES/step/rattle_cassette_liner_base_tpu95a.step

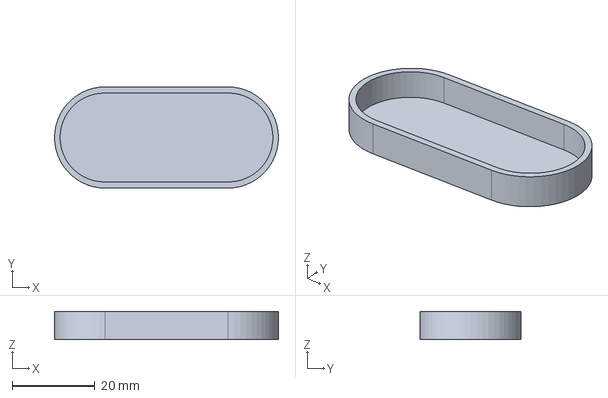
[picture p116: CAD file, 2026-09-06]
08_HISTORICAL_PACKAGES/2026-08-28_execution_v1.0/05_QA_FIXTURES/step/rattle_cassette_liner_base_tpu95a.step
54.2 x 24.5 x 6.80 mm
