anticipation-labs/anticipy-hardware/08_HISTORICAL_PACKAGES/2026-08-28_tuesday_evt_v0.1/anticipy_strict_evt_back_rf_nose.step

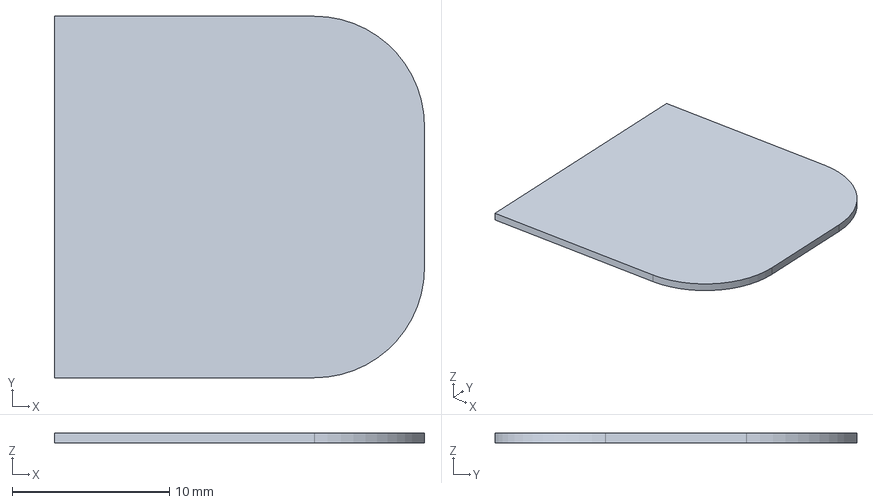
[picture p117: CAD file, 2026-09-06]
08_HISTORICAL_PACKAGES/2026-08-28_tuesday_evt_v0.1/anticipy_strict_evt_back_rf_nose.step
23.5 x 23.0 x 0.635 mm
