anticipation-labs/anticipy-hardware/08_HISTORICAL_PACKAGES/2026-08-19_anticipy_design_ds_bundle/assembly/build-steps.html

Assembly

# Build sequence

01Clip header pins flush · kapton the stubs and cell

02EVA-line both bays · battery in, wire-end toward board, wires never cross the closing channel

03SD module flat on battery face · caps across power · leads through tunnel

04Board nose-first at 15° into the flush port, flat onto shelf

05Magnetic tip into port · click shut · run the FULL test gate unglued

06Pass → acetone-weld rims · cure 24 h · seam slurry

07Sand 220→600 · primer ×2 · Rub 'n Buff titanium · steel-wool grain · satin clear ×2 · cure 48 h

08Thread 22" curb chain · nape magnetic clasp · wear
