anticipation-labs/anticipy-hardware/07_PROCUREMENT/Anticipy_Build_Guide_VISUAL.pdf

1

# LAY OUT YOUR PARTS

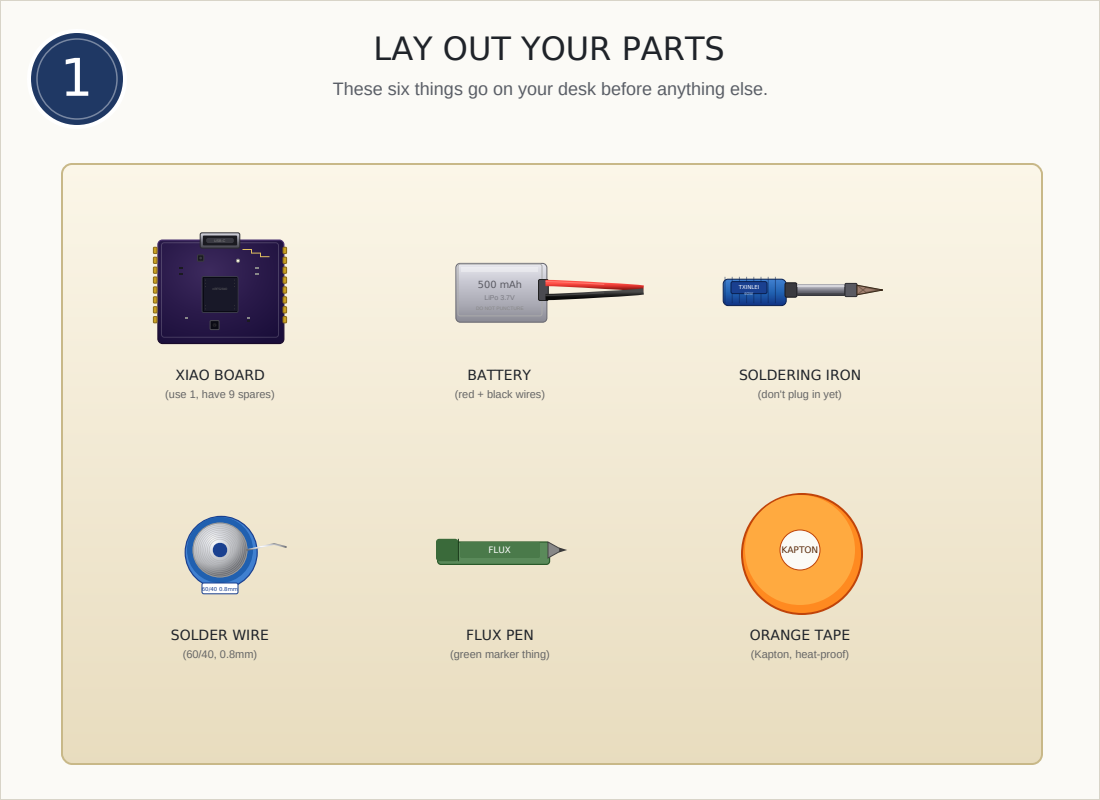
[picture p135: page 1]
USB-C; nRF52840; 500 mAh; LiPo 3.7V; TXINLEI; SOLDER WIRE; FLUX; KAPTON

These six things go on your desk before anything else.

DO NOT PUNCTURE

XIAO BOARD
(use 1, have 9 spares)

BATTERY
(red + black wires)

SOLDERING IRON
(don't plug in yet)

FLUX PEN
(green marker thing)

ORANGE TAPE
(Kapton, heat-proof)

2

# PLUG IN THE IRON

Put it in the stand. Set the dial to 350°C. Wait 5 minutes.

SET TO
350°C

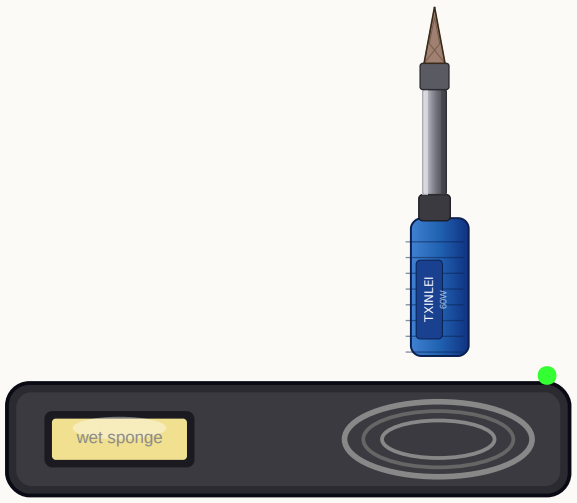
[picture p136: figure]
wet sponge; TXINLEI

(660°F)

⏱ WAIT 5 MIN

3

# ⚠ SAFETY

The iron tip is hot enough to burn through skin in 1 second.
!

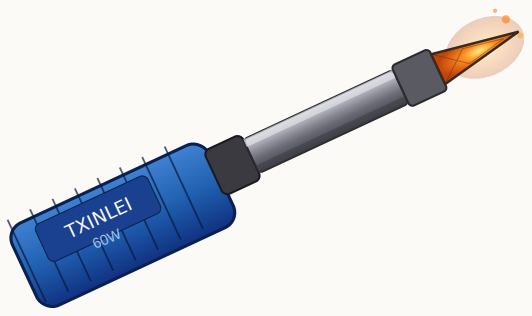
[picture p137: figure]
TXINLEI

### NEVER TOUCH THE METAL PART

4

# WIPE TIP ON WET SPONGE

Just brush it across. It'll sizzle. That's right.

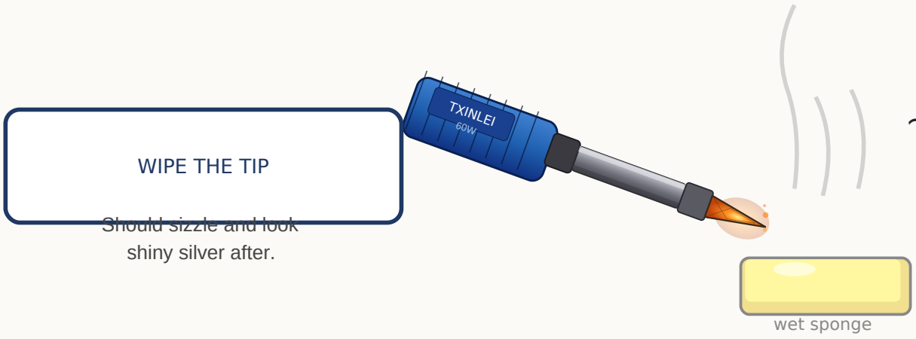
[picture p138: figure]
TXINLEI; wet sponge; WIPE THE TIP; Should sizzle and look shiny silver after.

## ~ sssss ~

5

# FLIP THE BOARD OVER

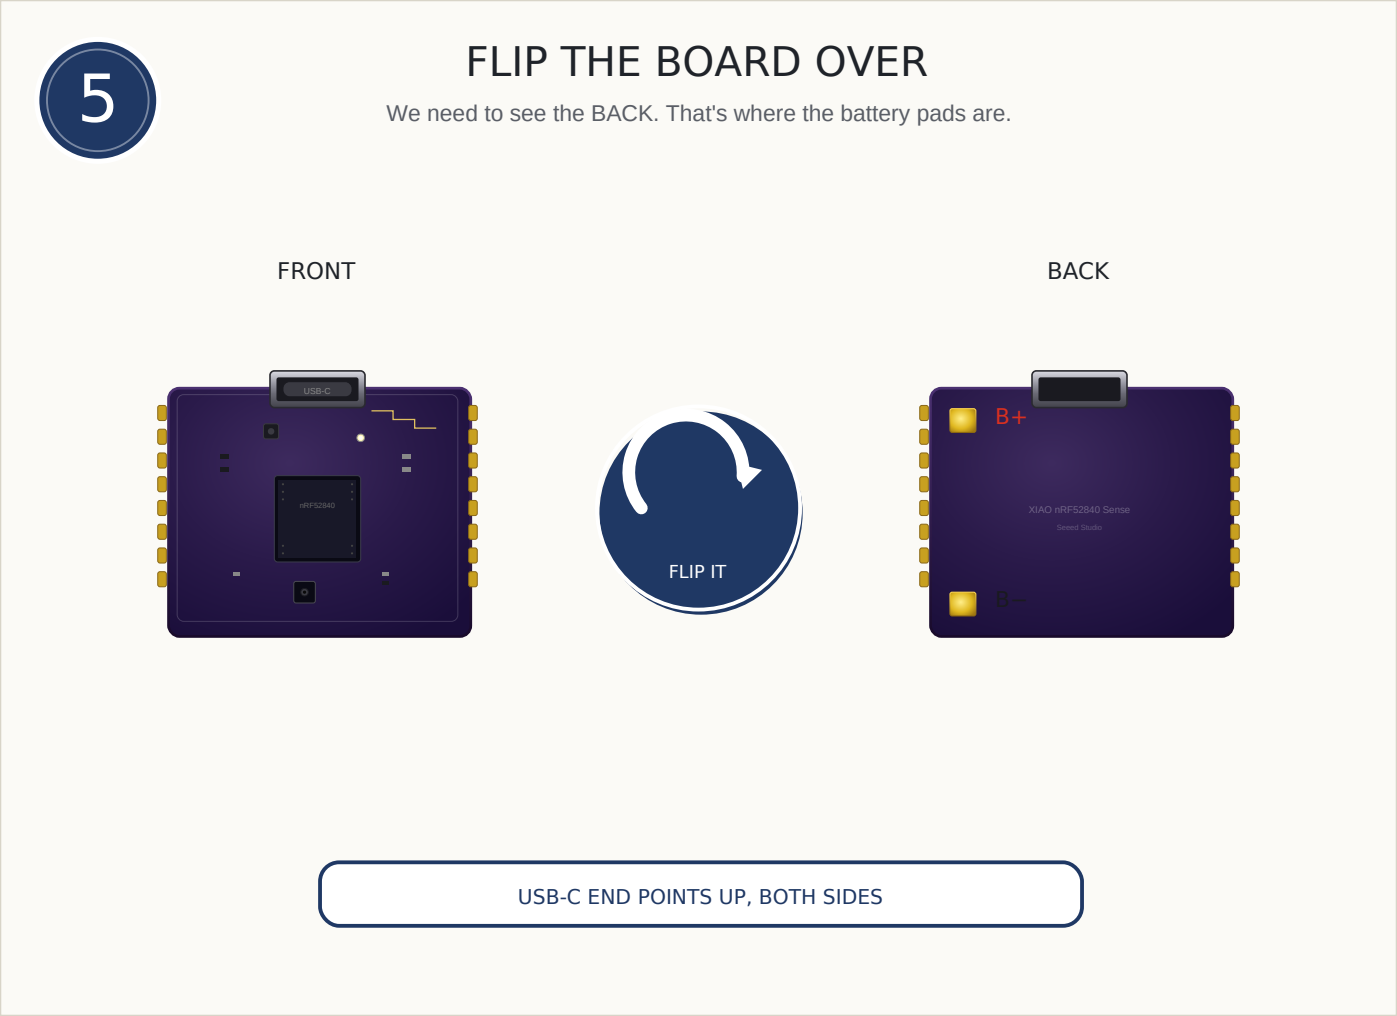
[picture p139: page 5]
FRONT; USB-C; nRF52840; FLIP IT; BACK; XIAO nRF52840 Sense; Seeed Studio

We need to see the BACK. That's where the battery pads are.

USB-C END POINTS UP, BOTH SIDES

6

# FIND THE TWO GOLD SQUARES

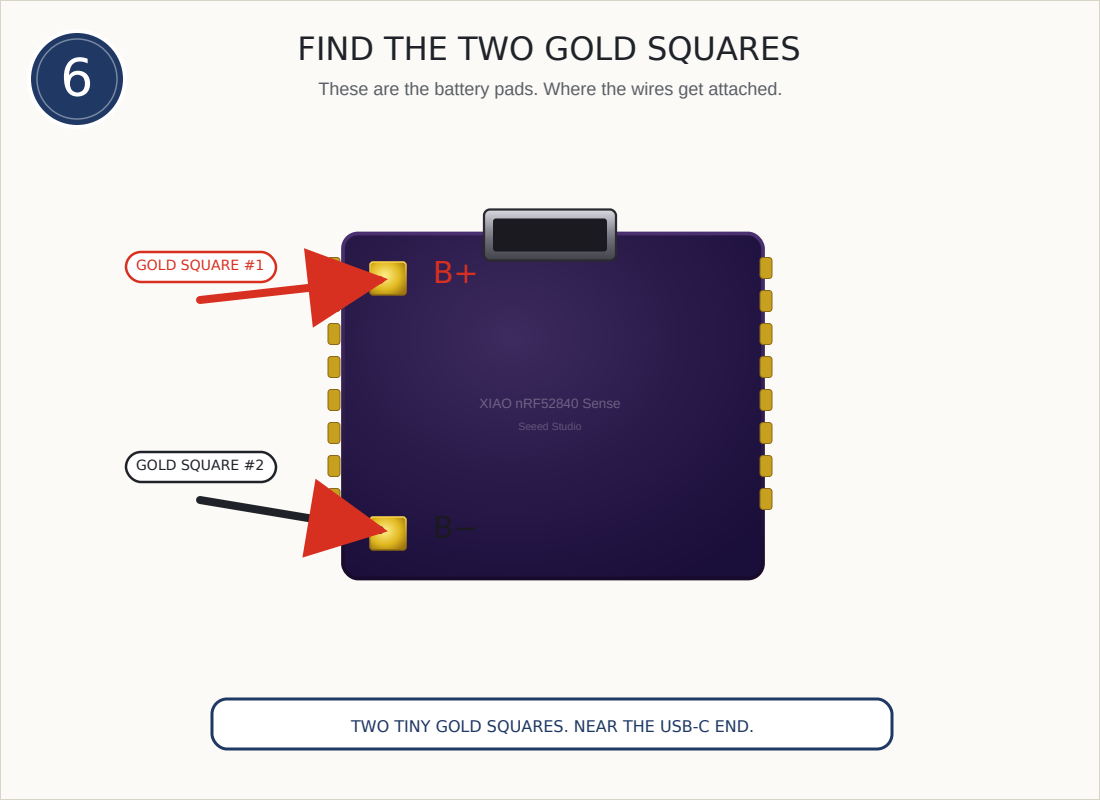
[picture p140: page 6]
XIAO nRF52840 Sense; Seeed Studio; GOLD SQUARE #1; GOLD SQUARE #2

These are the battery pads. Where the wires get attached.

TWO TINY GOLD SQUARES. NEAR THE USB-C END.

7

# B+ AND B−

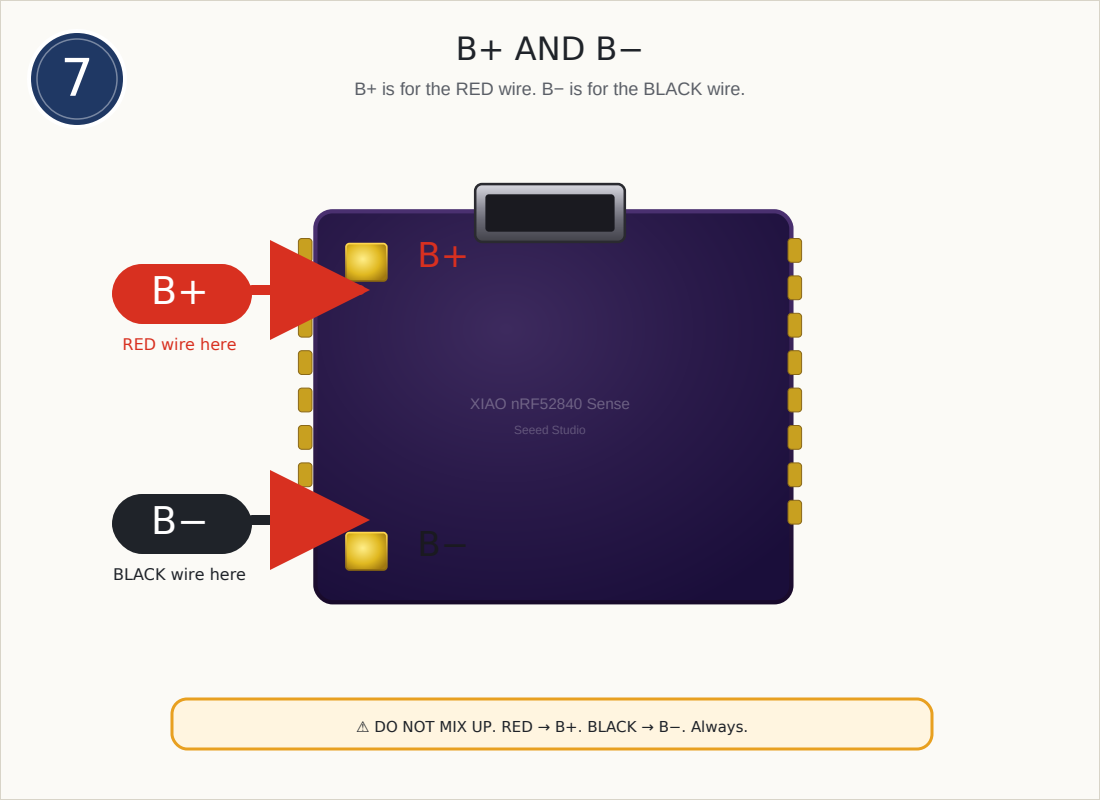
[picture p141: page 7]
XIAO nRF52840 Sense; Seeed Studio

B+ is for the RED wire. B− is for the BLACK wire.

RED wire here

BLACK wire here

⚠ DO NOT MIX UP. RED → B+. BLACK → B−. Always.

8

# GET THE BATTERY OUT

Open the baggie. Take one battery out. Set the rest aside.

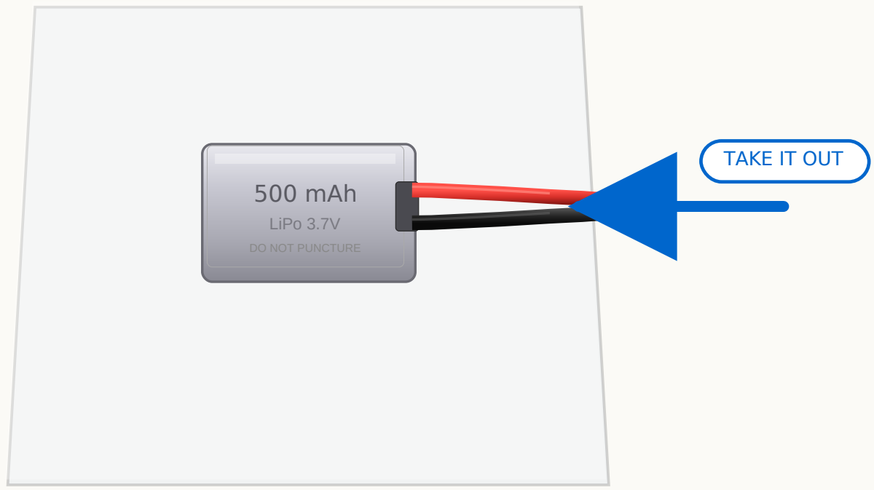
[picture p142: figure]
500 mAh; LiPo 3.7V; DO NOT PUNCTURE; TAKE IT OUT

PICK ONE BATTERY. THE 500mAh DRONE LiPO.

9

# CHECK THE WIRES

Look at the wire tips. About 3mm of bare silver should be showing.

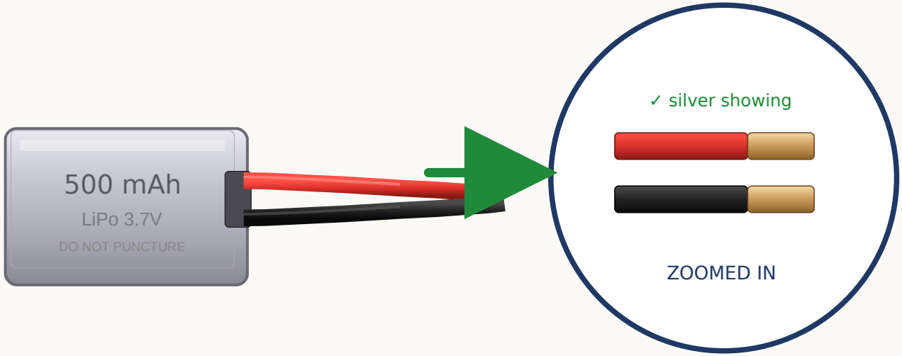
[picture p143: figure]
500 mAh; LiPo 3.7V; DO NOT PUNCTURE; ZOOMED IN; ✓ silver showing

✓ THE BARE SILVER/COPPER TIPS SHOULD ALREADY BE SHOWING

10

# NEVER LET WIRES TOUCH

Bare red touching bare black = short circuit. Always keep them apart.

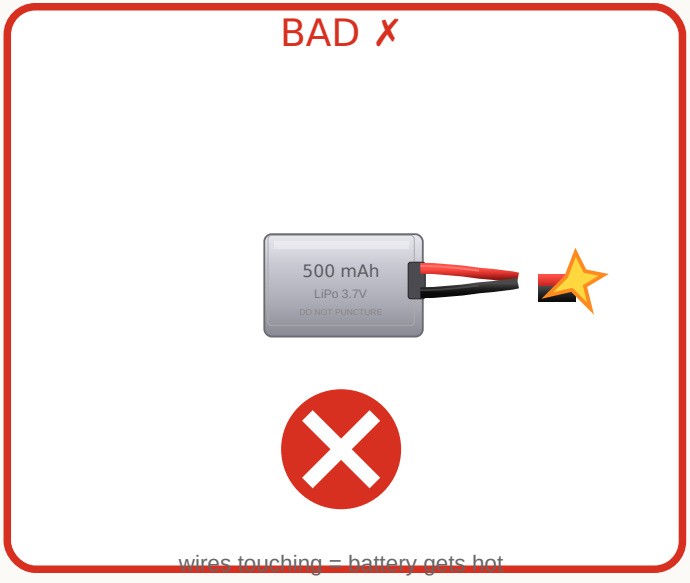
[picture p144: figure]
500 mAh; LiPo 3.7V; DO NOT PUNCTURE; BAD ✗; wires touching = battery gets hot
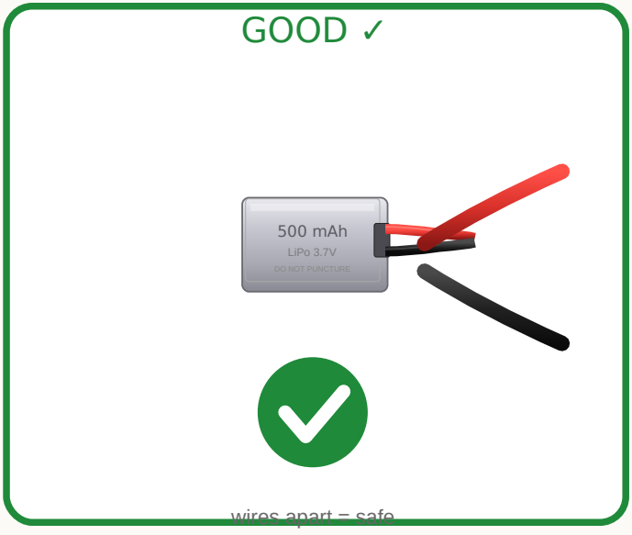
[picture p145: figure]
500 mAh; LiPo 3.7V; DO NOT PUNCTURE; GOOD ✓; wires apart = safe

11

# DAB A DOT OF FLUX ON B+

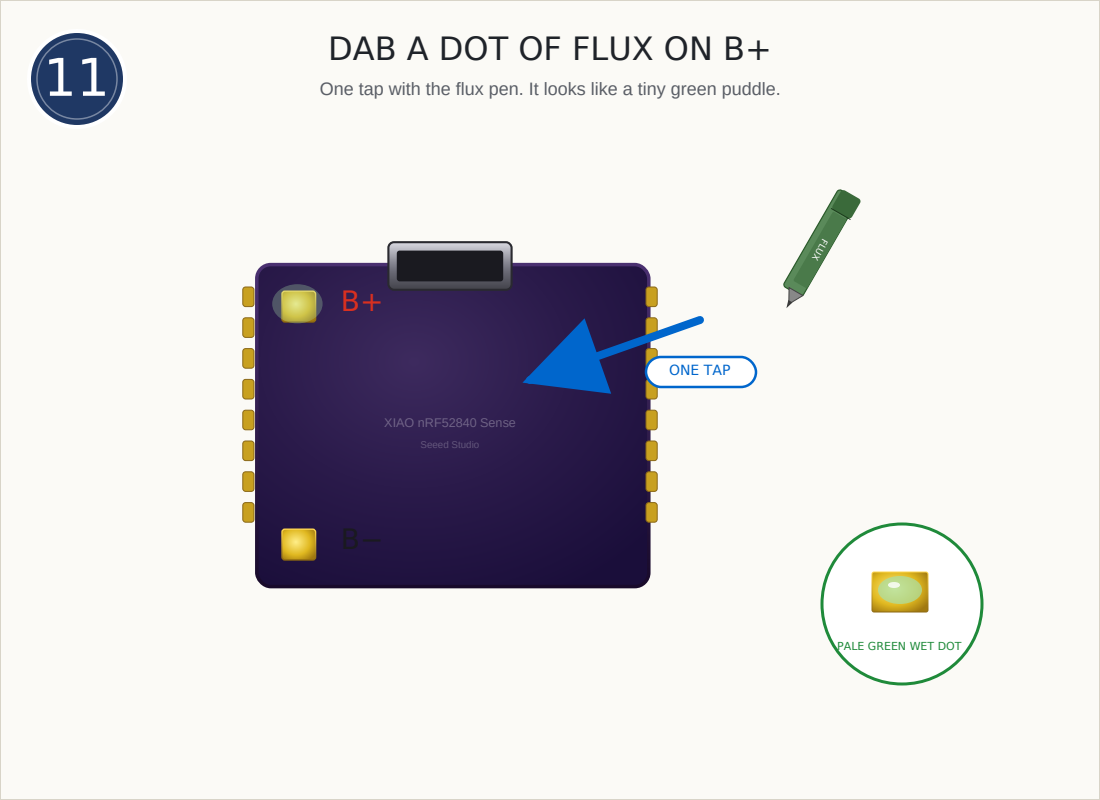
[picture p146: page 11]
XIAO nRF52840 Sense; Seeed Studio; FLUX; ONE TAP

One tap with the flux pen. It looks like a tiny green puddle.

PALE GREEN WET DOT

12

# PLACE RED WIRE ON B+

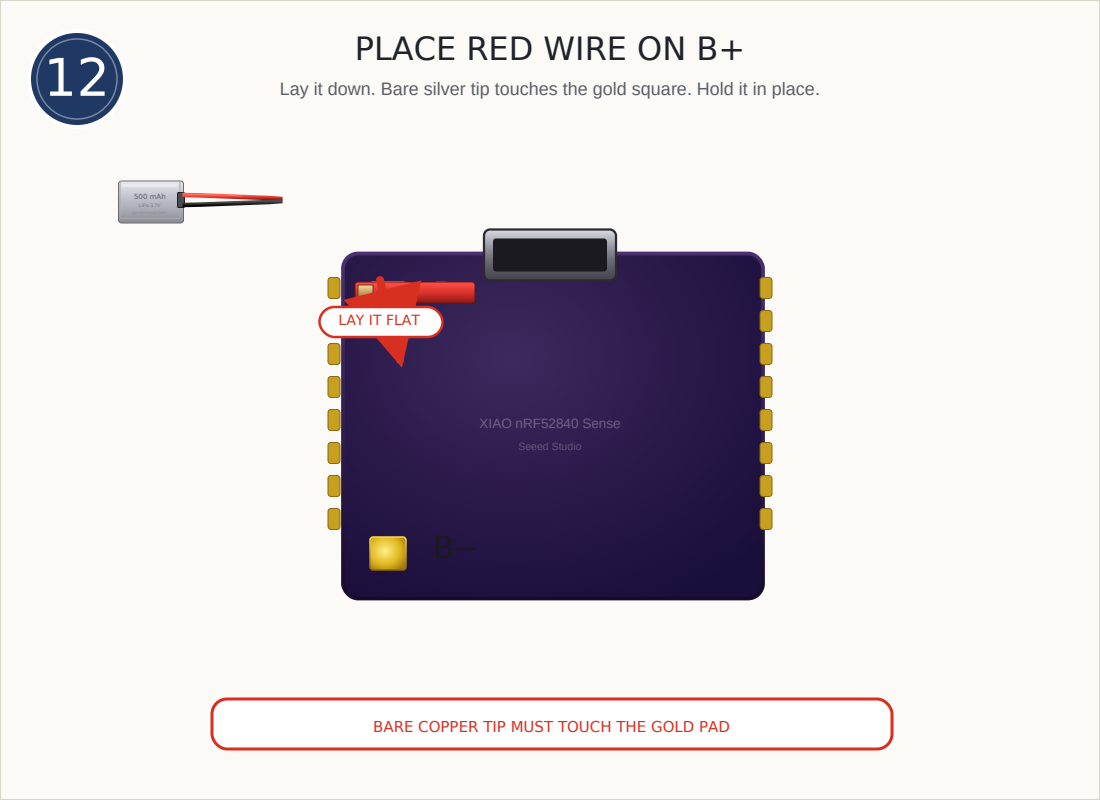
[picture p147: page 12]
XIAO nRF52840 Sense; Seeed Studio; 500 mAh; LiPo 3.7V

Lay it down. Bare silver tip touches the gold square. Hold it in place.

DO NOT PUNCTURE

LAY IT FLAT

BARE COPPER TIP MUST TOUCH THE GOLD PAD

13

# TOUCH IRON TO WIRE+PAD

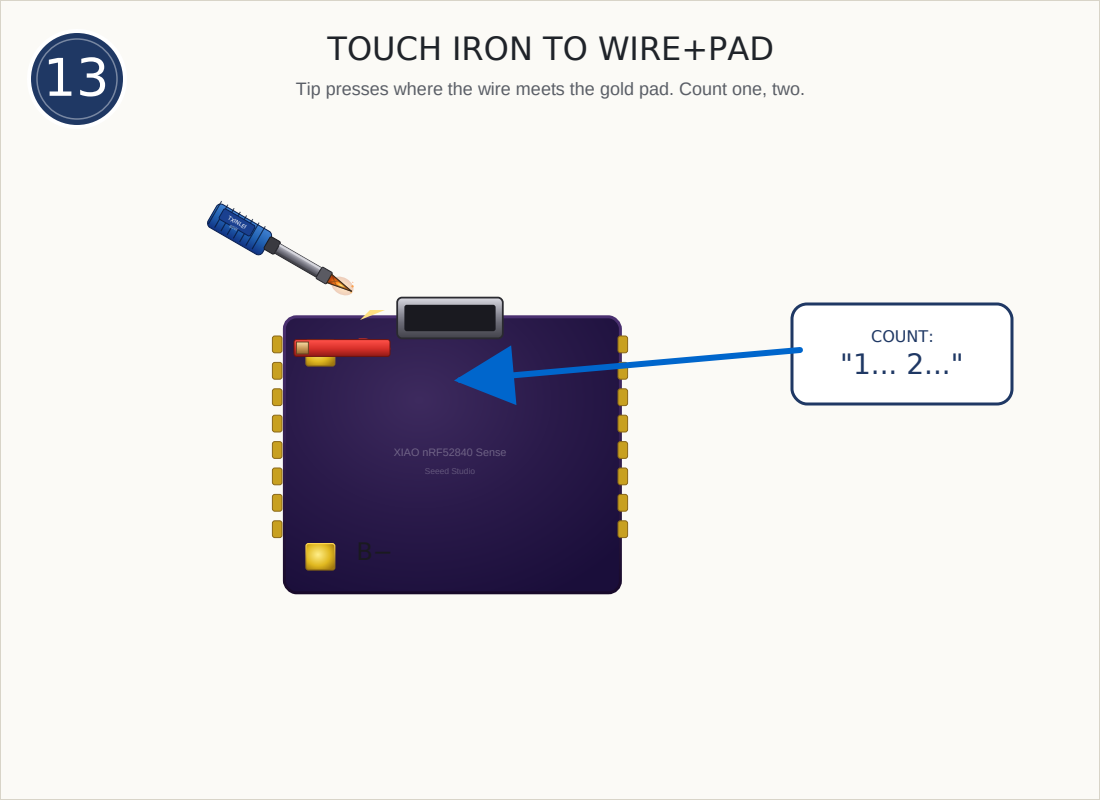
[picture p148: page 13]
XIAO nRF52840 Sense; Seeed Studio; TXINLEI; COUNT: "1... 2..."

Tip presses where the wire meets the gold pad. Count one, two.

14

# FEED SOLDER INTO THE JOINT

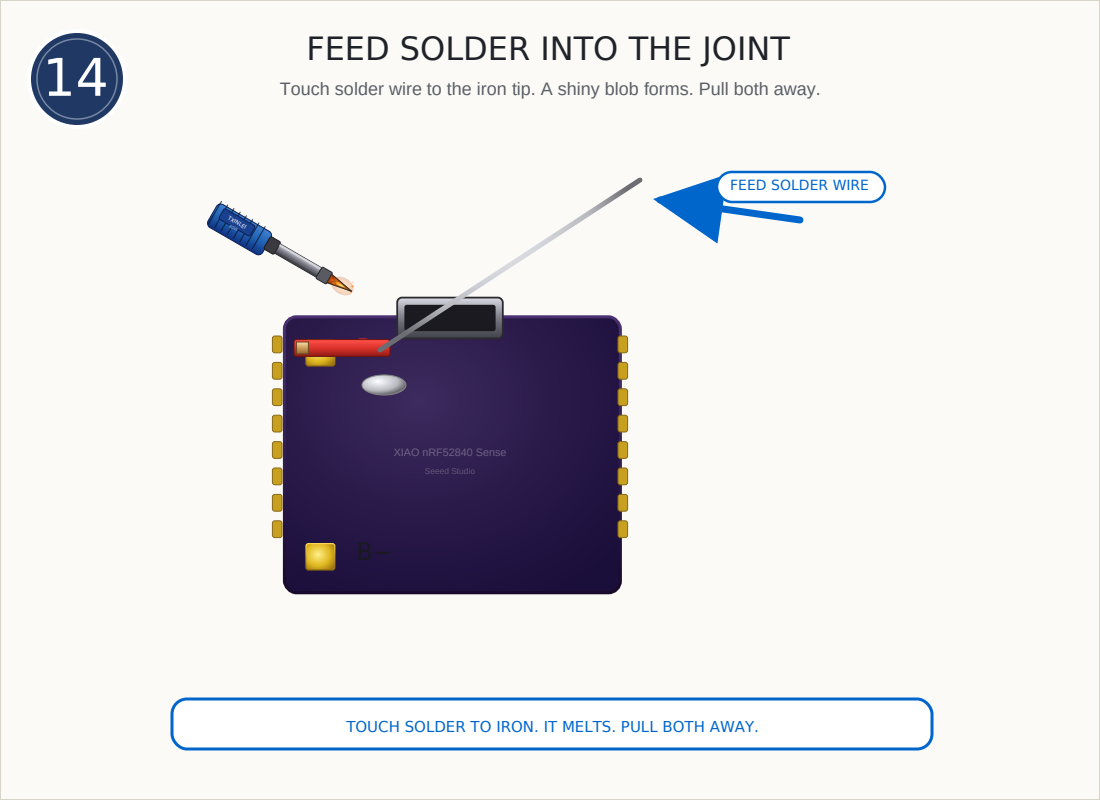
[picture p149: page 14]
XIAO nRF52840 Sense; Seeed Studio; TXINLEI

Touch solder wire to the iron tip. A shiny blob forms. Pull both away.

FEED SOLDER WIRE

TOUCH SOLDER TO IRON. IT MELTS. PULL BOTH AWAY.

15

# DON'T MOVE FOR 5 SECONDS

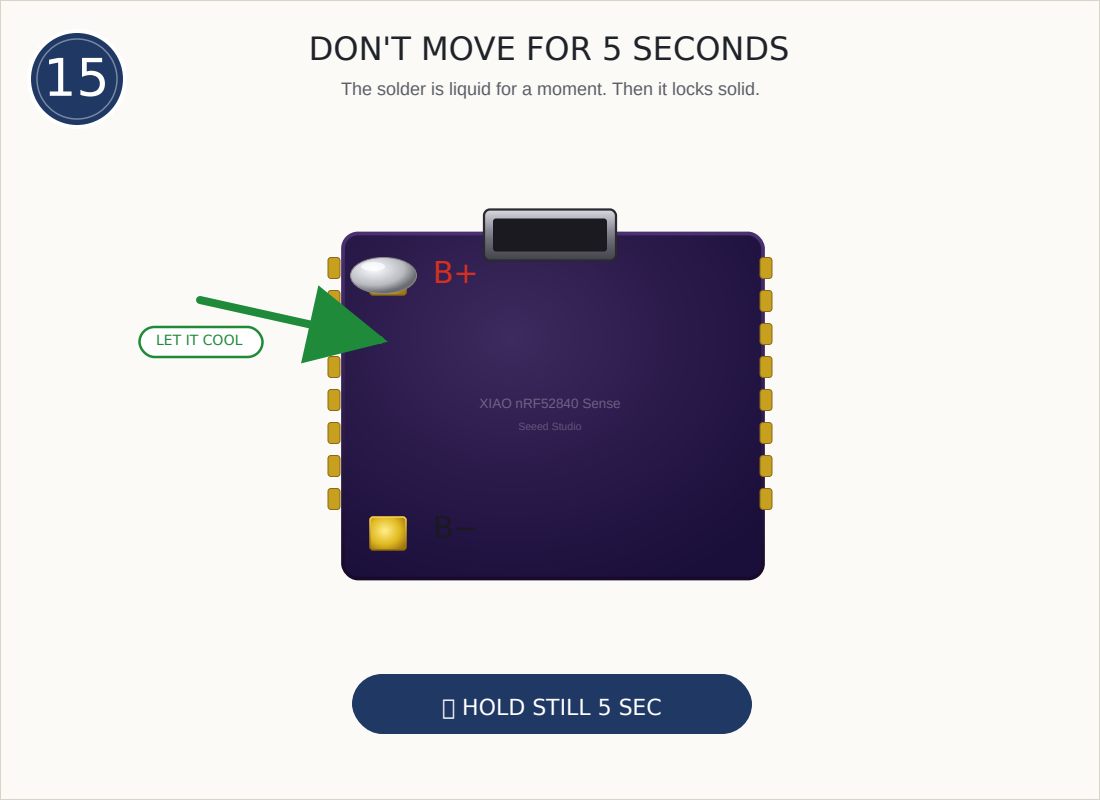
[picture p150: page 15]
XIAO nRF52840 Sense; Seeed Studio

The solder is liquid for a moment. Then it locks solid.

LET IT COOL

⏱ HOLD STILL 5 SEC

16

# WHAT GOOD LOOKS LIKE

Shiny silver dome. Smooth. Wider at the bottom than the top.

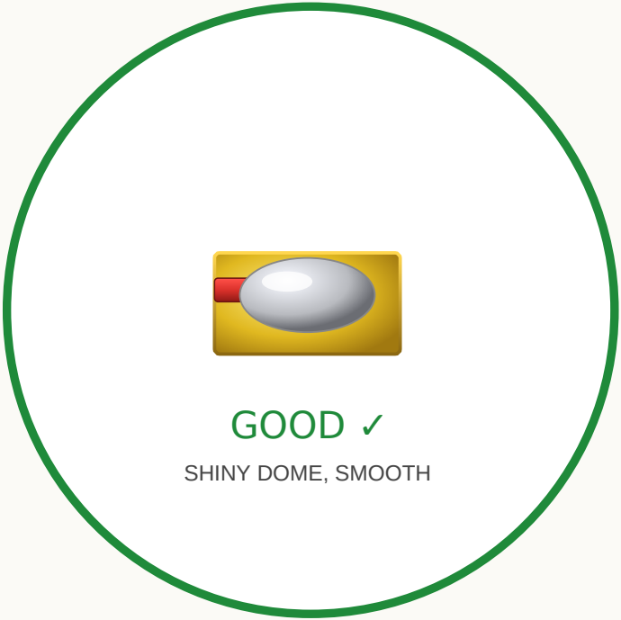
[picture p151: figure]
GOOD ✓; SHINY DOME, SMOOTH

✓ MIRROR SHINY = ELECTRICITY FLOWS

17

# WHAT BAD LOOKS LIKE

Dull gray means it didn't bond. A ball means too much solder.

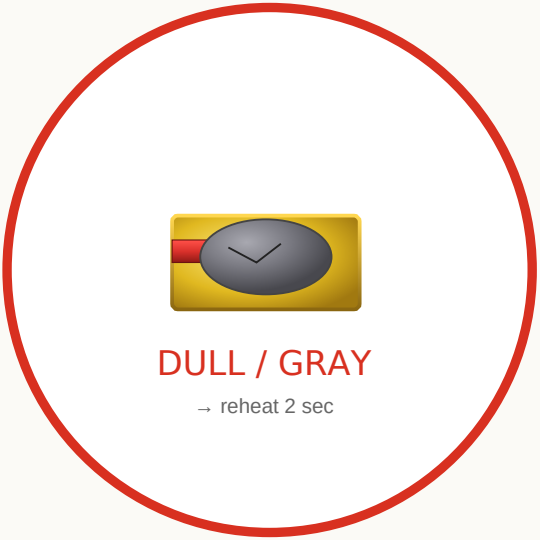
[picture p152: figure]
DULL / GRAY; → reheat 2 sec
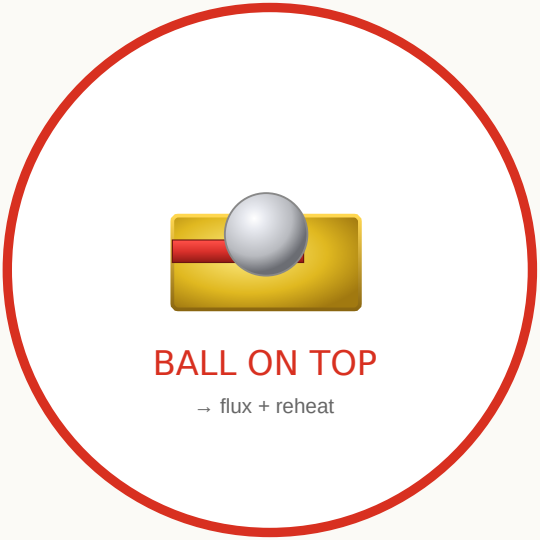
[picture p153: figure]
BALL ON TOP; → flux + reheat

IF EITHER OF THESE → REHEAT AND TRY AGAIN

18

# NOW SOLDER THE BLACK WIRE

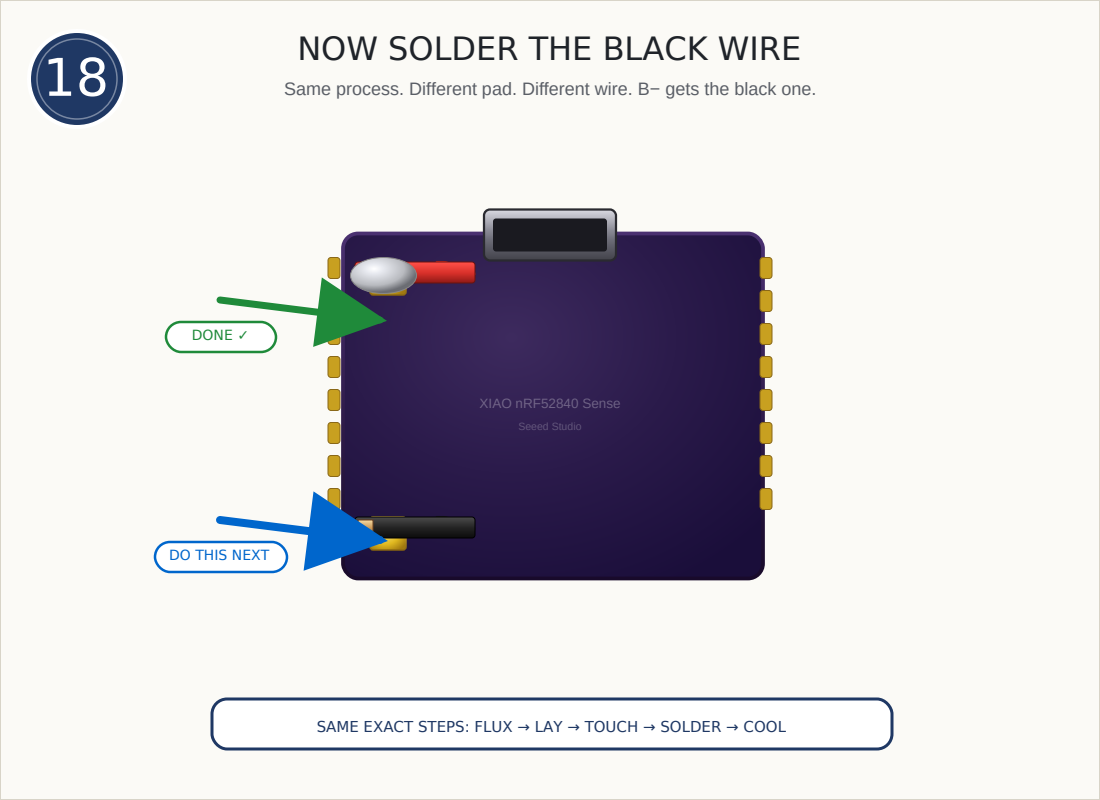
[picture p154: page 18]
XIAO nRF52840 Sense; Seeed Studio; DONE ✓

Same process. Different pad. Different wire. B− gets the black one.

DO THIS NEXT

SAME EXACT STEPS: FLUX → LAY → TOUCH → SOLDER → COOL

19

# BOTH WIRES SOLDERED

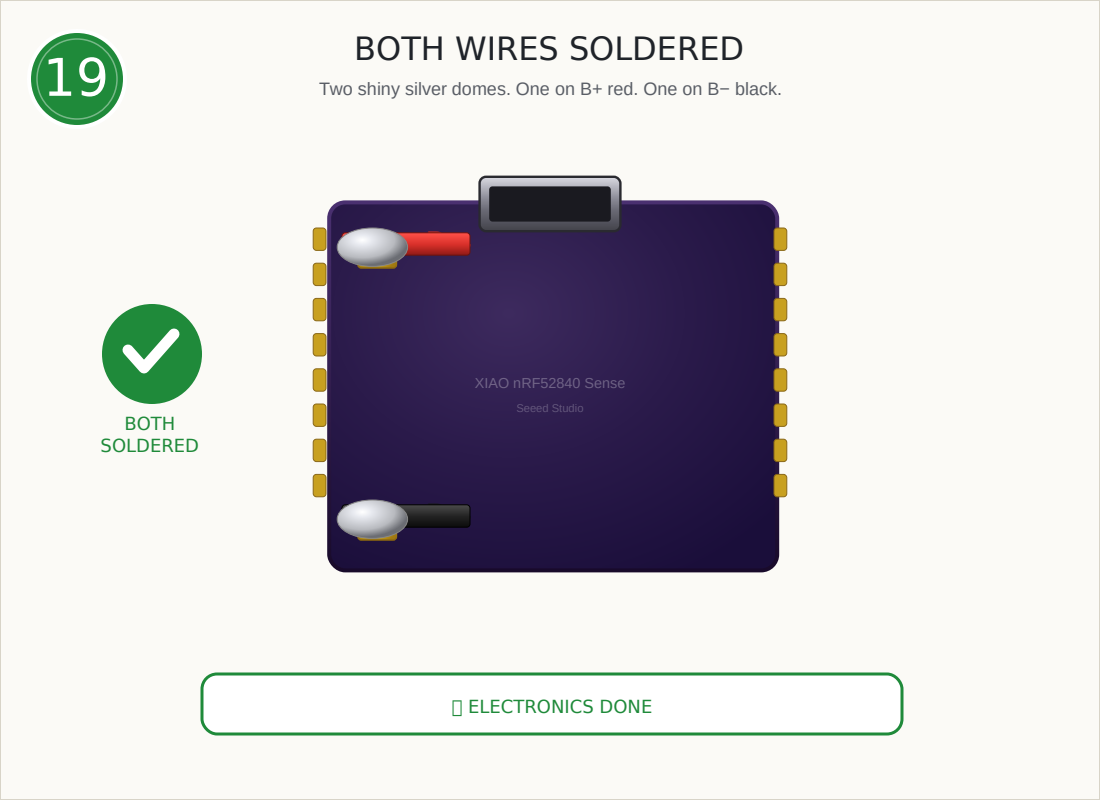
[picture p155: page 19]
XIAO nRF52840 Sense; Seeed Studio; BOTH SOLDERED; 🎉 ELECTRONICS DONE

Two shiny silver domes. One on B+ red. One on B− black.

20

# PUT THE IRON BACK

Always in the stand. Even when you're 'just resting' it. Always. TXINLEI 60W

BACK IN THE STAND

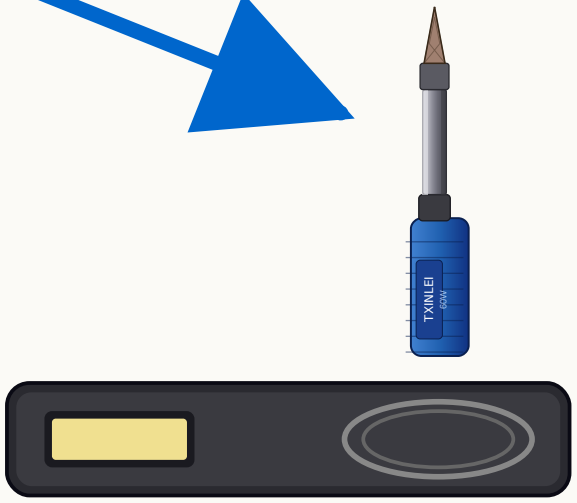
[picture p156: figure]

⚠ NEVER LAY THE IRON ON THE DESK. EVEN COOL, IT BURNS.

21

# PLUG INTO YOUR MAC

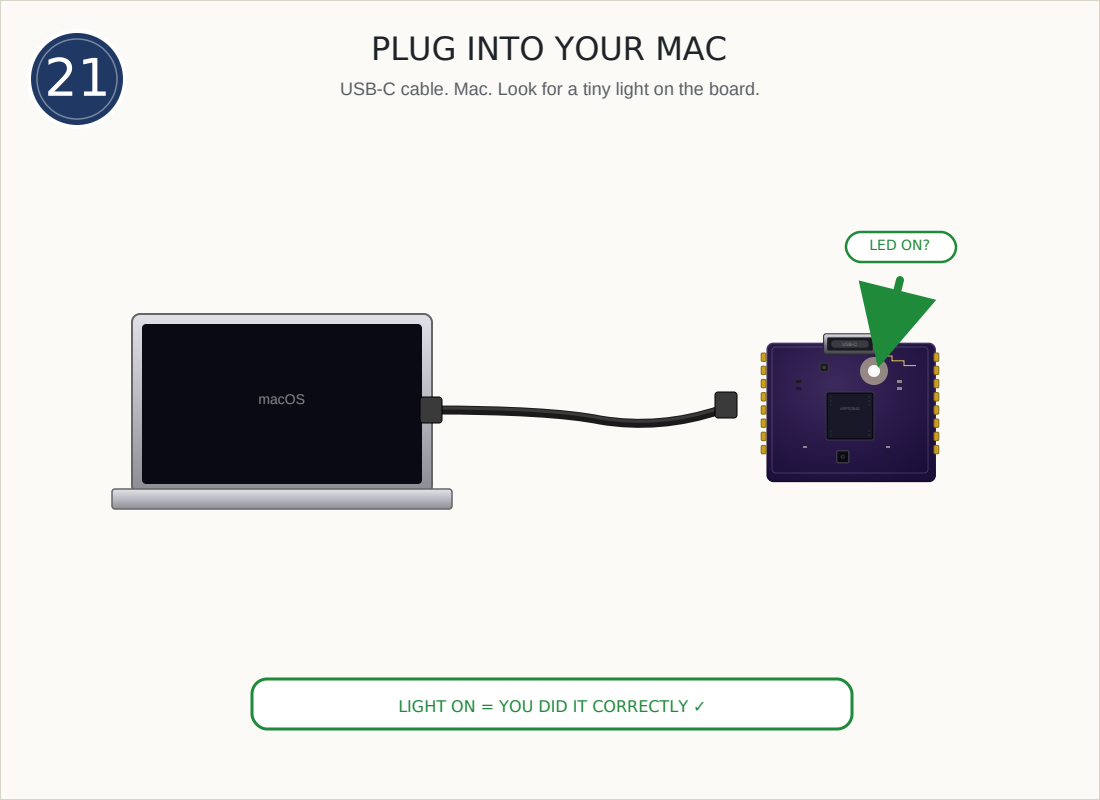
[picture p157: page 21]
macOS; USB-C; nRF52840; LED ON?

USB-C cable. Mac. Look for a tiny light on the board.

LIGHT ON = YOU DID IT CORRECTLY ✓

22

# LED GLOWS = CELEBRATE

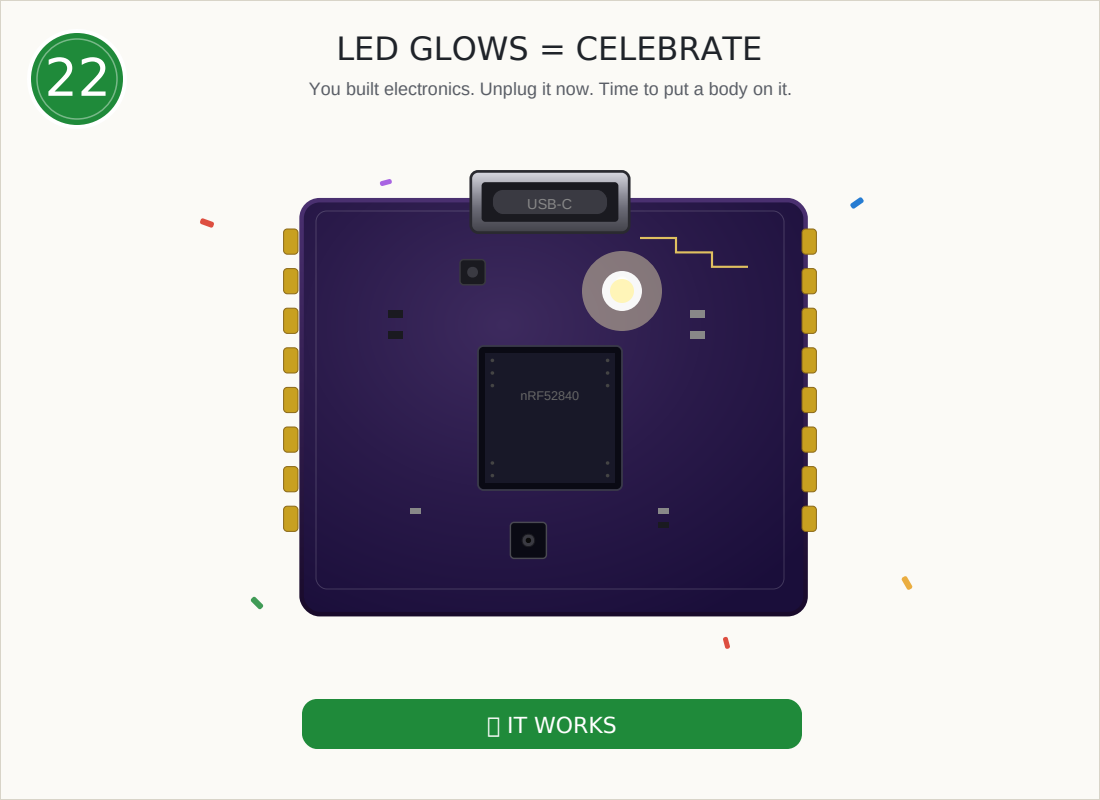
[picture p158: page 22]
USB-C; nRF52840; 🎉 IT WORKS

You built electronics. Unplug it now. Time to put a body on it.

23

# IF NO LIGHT

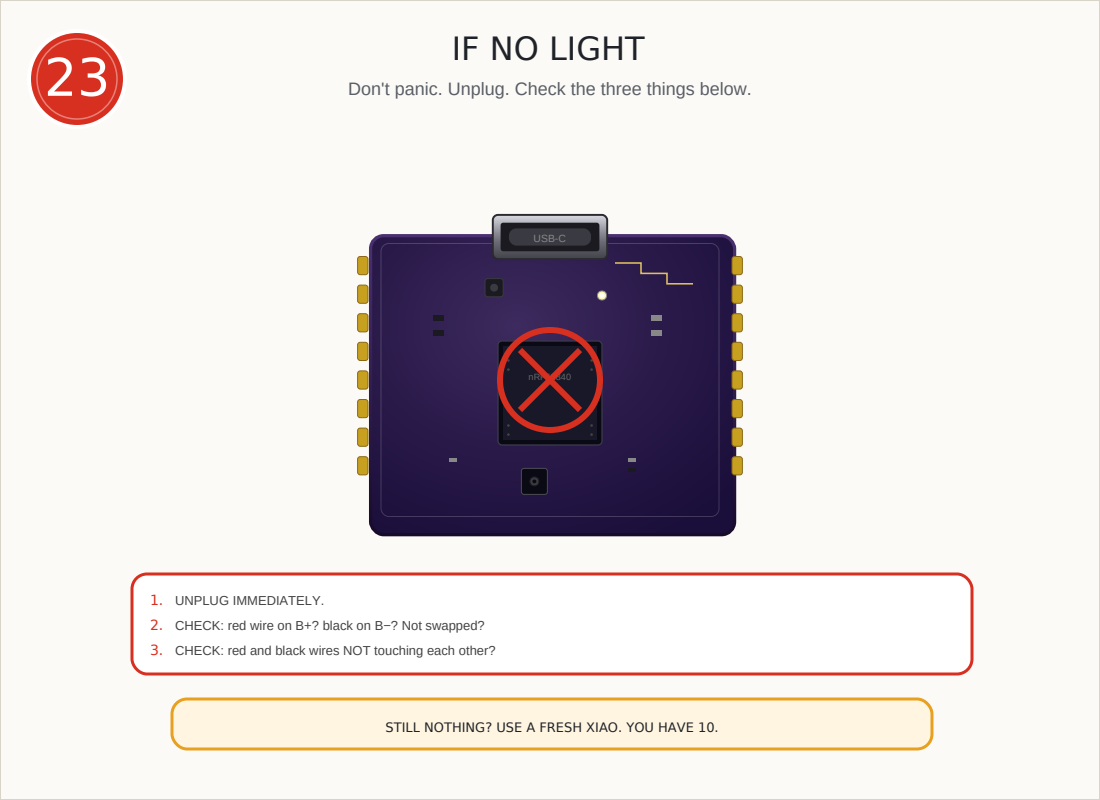
[picture p159: page 23]
USB-C; nRF52840

Don't panic. Unplug. Check the three things below.

1. UNPLUG IMMEDIATELY.
2. CHECK: red wire on B+? black on B−? Not swapped?
3. CHECK: red and black wires NOT touching each other?

STILL NOTHING? USE A FRESH XIAO. YOU HAVE 10.

24

# CUT A SMALL PIECE OF FOAM TAPE

Black double-sided tape. Cut a piece about the size of a pinkie nail.

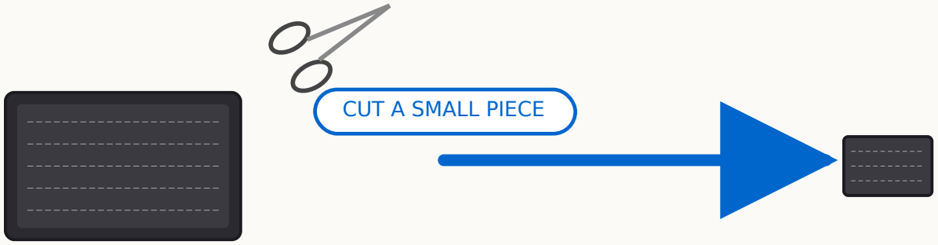
[picture p160: figure]
CUT A SMALL PIECE

15mm × 10mm
about the size of a pinkie nail

DOUBLE-SIDED FOAM TAPE FROM YOUR PARTS KIT

25

# PEEL ONE SIDE OF THE TAPE

Pull off the paper film. Sticky side is now exposed.

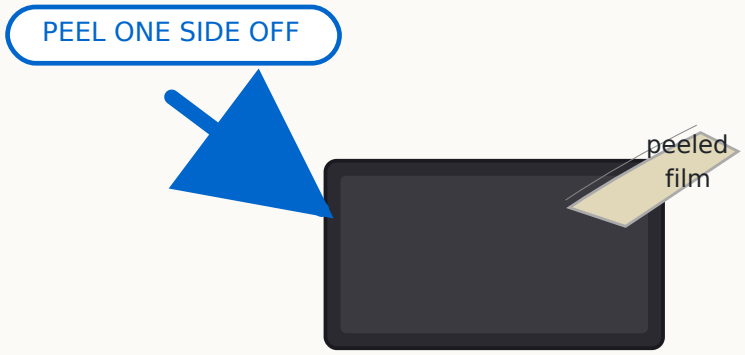
[picture p161: figure]
peeled film; PEEL ONE SIDE OFF

↑ STICKY SIDE NOW EXPOSED ↑

26

# STICK TAPE TO BATTERY

Press the exposed sticky side onto the flat side of the battery.

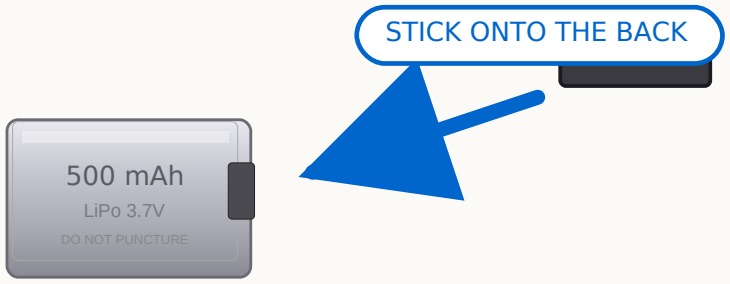
[picture p162: figure]
500 mAh; LiPo 3.7V; DO NOT PUNCTURE; STICK ONTO THE BACK

500 mAh

LiPo 3.7V

DO NOT PUNCTURE

STICK IT TO THE FLAT SIDE OF THE BATTERY (NOT THE WIRE END)

28

# WRAP IT IN ORANGE TAPE

One lap of Kapton tape around the whole stack. Keeps everything tight.

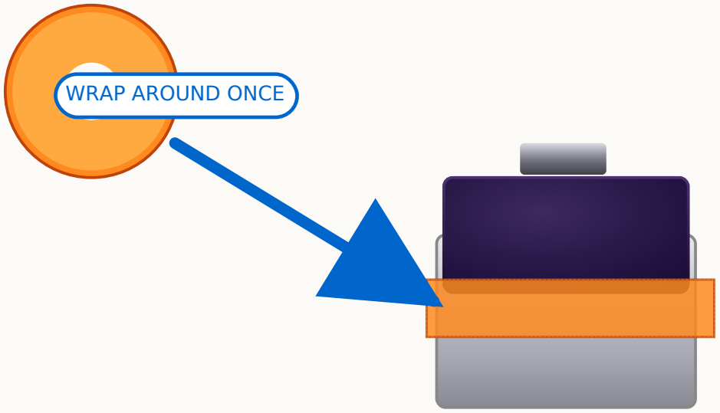
[picture p163: figure]
KAPTON; WRAP AROUND ONCE

ONE LAP OF ORANGE TAPE LOCKS IT ALL TOGETHER

29

# DONE: ELECTRONICS COMPLETE

Charge it once now. Then we put a body on it.

YOU HAVE A
WORKING BRAIN

about 25mm × 22mm × 8mm

smaller than a quarter

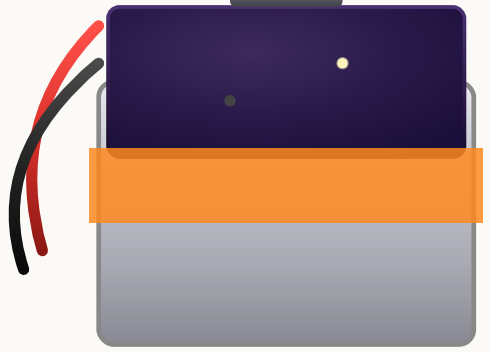
[picture p164: figure]

⚠ TREAT IT LIKE A TINY PHONE. NO DROPS. NO WATER.
