anticipation-labs/anticipy-hardware/07_PROCUREMENT/Anticipy_v0_Build_Guide.pdf

# Build Your Anticipy Pendant

The super-simple picture guide. Like building Legos.

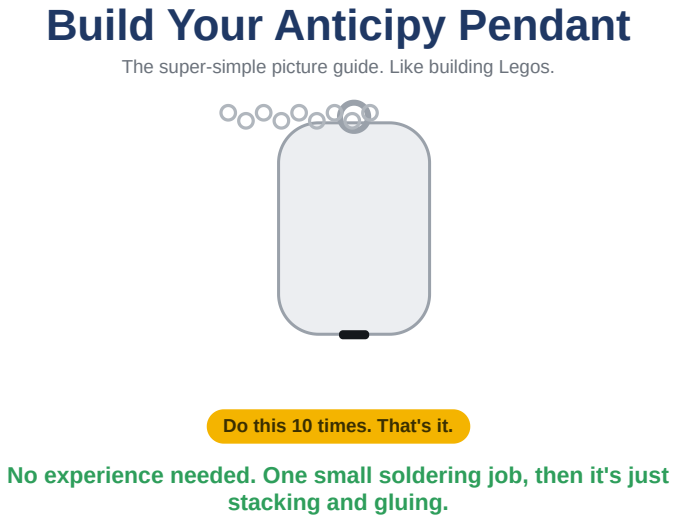
[picture p165: page 1]

Do this 10 times. That's it.

No experience needed. One small soldering job, then it's just

stacking and gluing.

# What you have

Four things make one pendant.

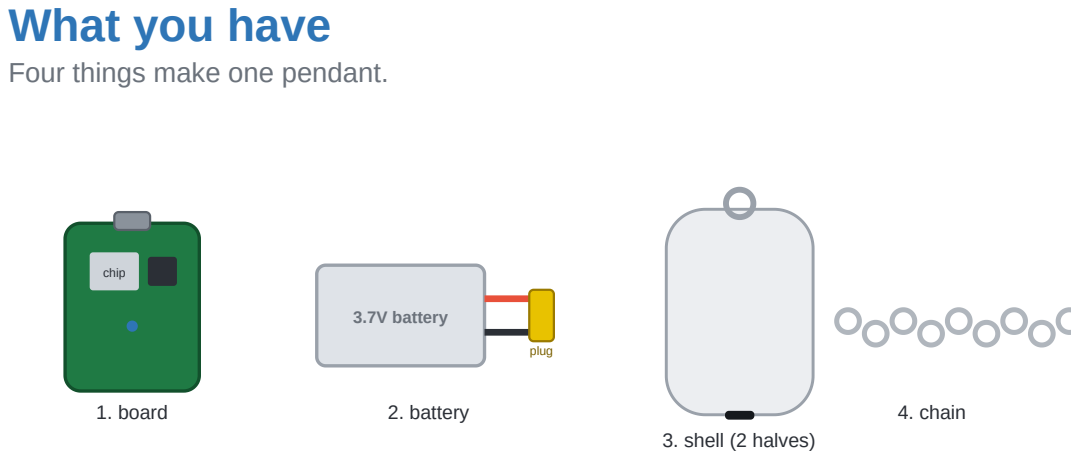
[picture p166: page 2]
chip; 1. board; 3.7V battery; plug; 2. battery; 3. shell (2 halves); 4. chain

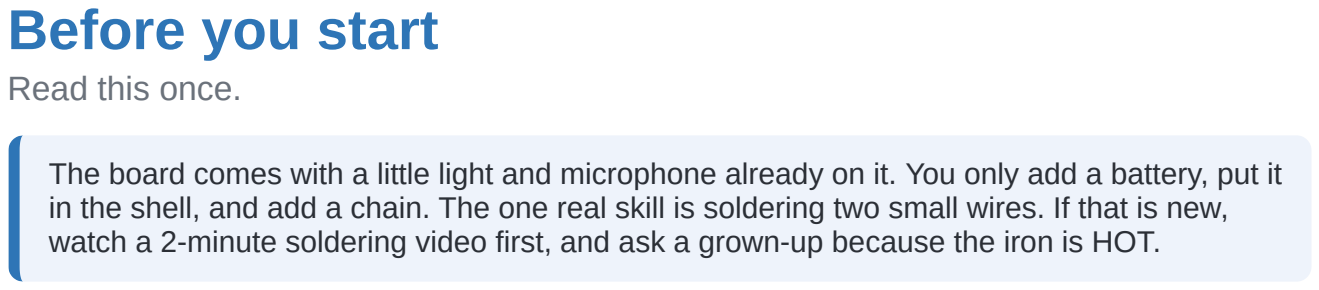
[picture p167: figure]
Before you start; Read this once.

The board comes with a little light and microphone already on it. You only add a battery, put it in the shell, and add a chain. The one real skill is soldering two small wires. If that is new, watch a 2-minute soldering video first, and ask a grown-up because the iron is HOT.

1

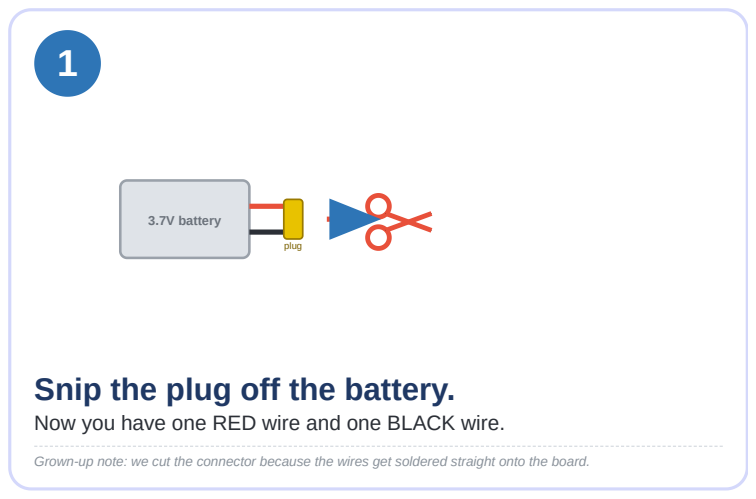
[picture p168: page 4]
3.7V battery; plug

Snip the plug off the battery.
Now you have one RED wire and one BLACK wire.

Grown-up note: we cut the connector because the wires get soldered straight onto the board.

2

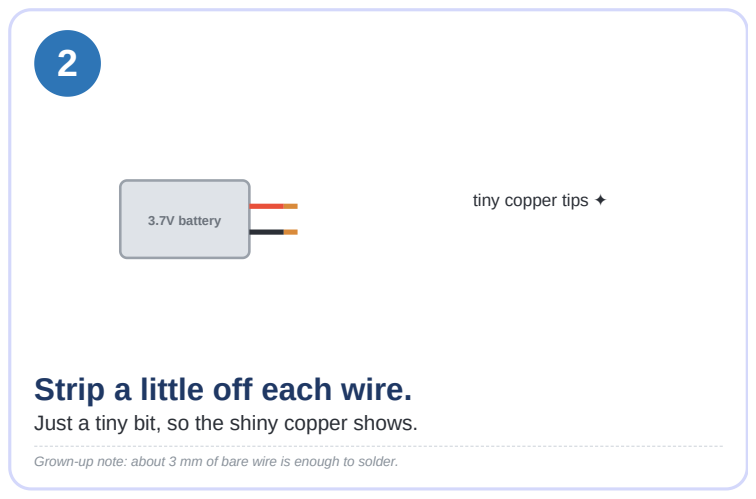
[picture p169: page 5]
3.7V battery

tiny copper tips ✦

Strip a little off each wire.
Just a tiny bit, so the shiny copper shows.

Grown-up note: about 3 mm of bare wire is enough to solder.

3

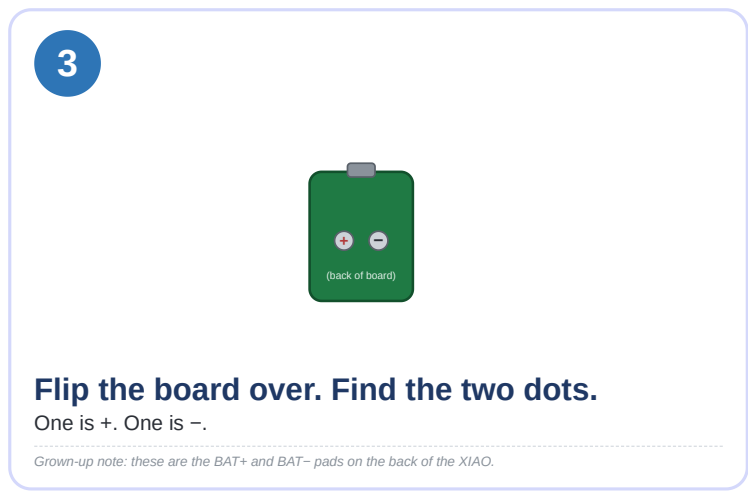
[picture p170: page 6]

(back of board)

Flip the board over. Find the two dots.
One is +. One is −.

Grown-up note: these are the BAT+ and BAT− pads on the back of the XIAO.

4

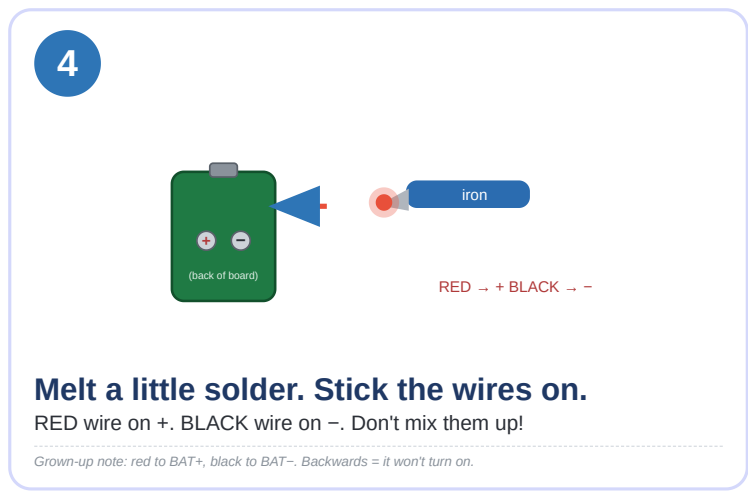
[picture p171: page 7]
iron; RED → + BLACK → −

(back of board)

Melt a little solder. Stick the wires on.
RED wire on +. BLACK wire on −. Don't mix them up!

Grown-up note: red to BAT+, black to BAT−. Backwards = it won't turn on.

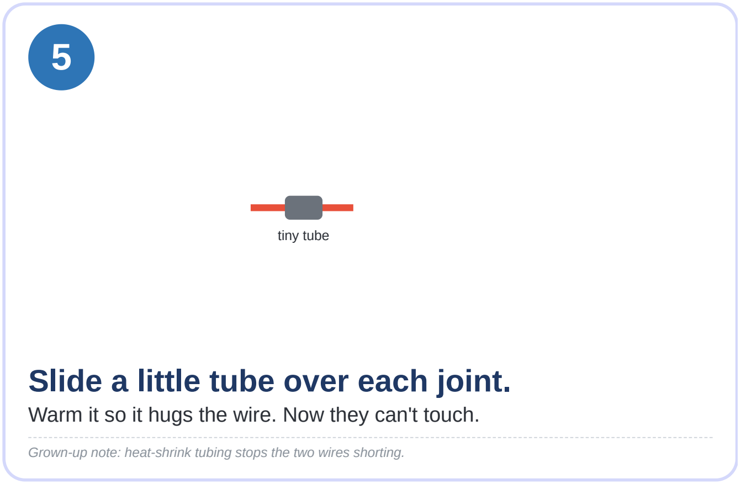
[picture p172: figure]
tiny tube; Slide a little tube over each joint.

Warm it so it hugs the wire. Now they can't touch.

Grown-up note: heat-shrink tubing stops the two wires shorting.

6

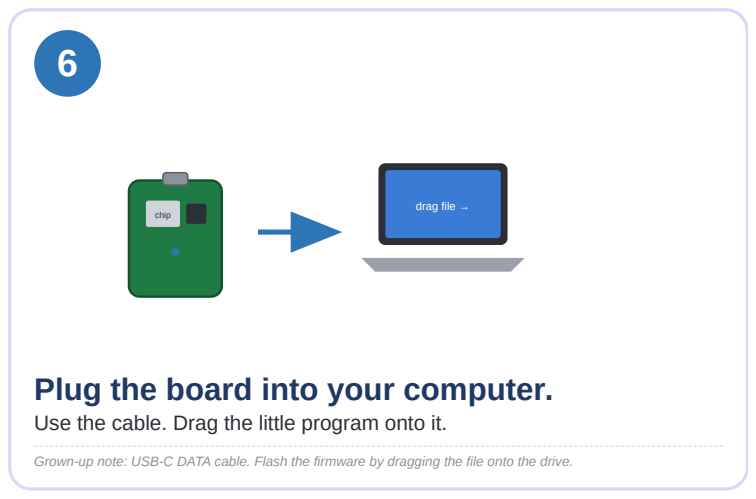
[picture p173: page 9]
chip; drag file →

Plug the board into your computer.
Use the cable. Drag the little program onto it.

Grown-up note: USB-C DATA cable. Flash the firmware by dragging the file onto the drive.

7

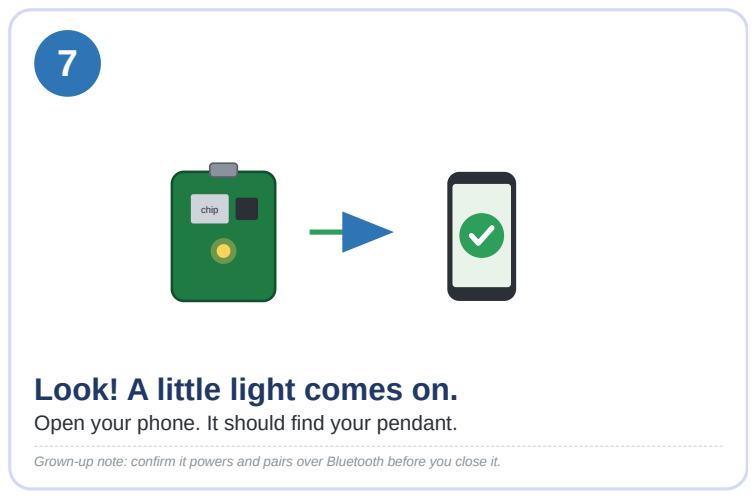
[picture p174: page 10]
chip

Look! A little light comes on.
Open your phone. It should find your pendant.

Grown-up note: confirm it powers and pairs over Bluetooth before you close it.

8

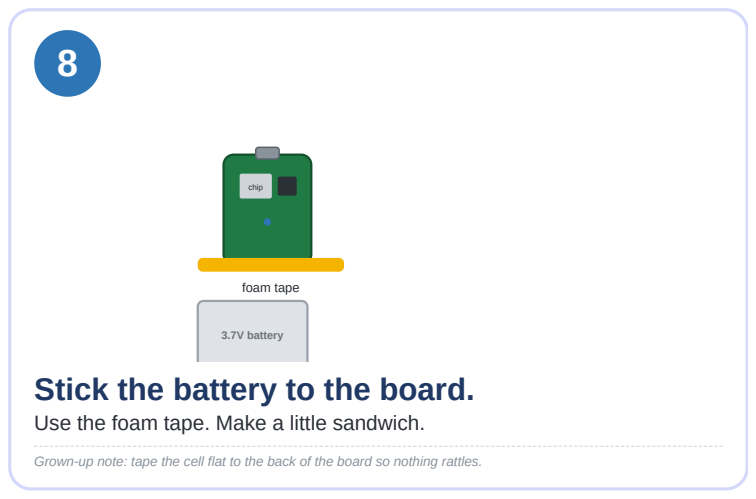
[picture p175: page 11]
chip; foam tape; 3.7V battery

Stick the battery to the board.
Use the foam tape. Make a little sandwich.

Grown-up note: tape the cell flat to the back of the board so nothing rattles.

9

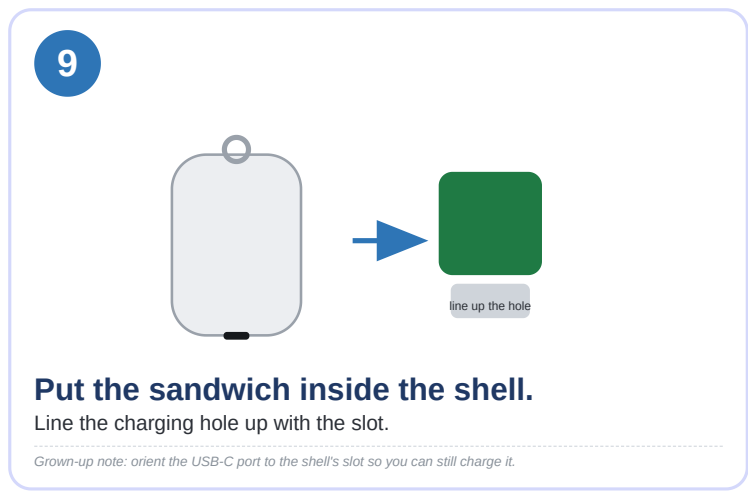
[picture p176: page 12]

line up the hole

Put the sandwich inside the shell.
Line the charging hole up with the slot.

Grown-up note: orient the USB-C port to the shell's slot so you can still charge it.

10

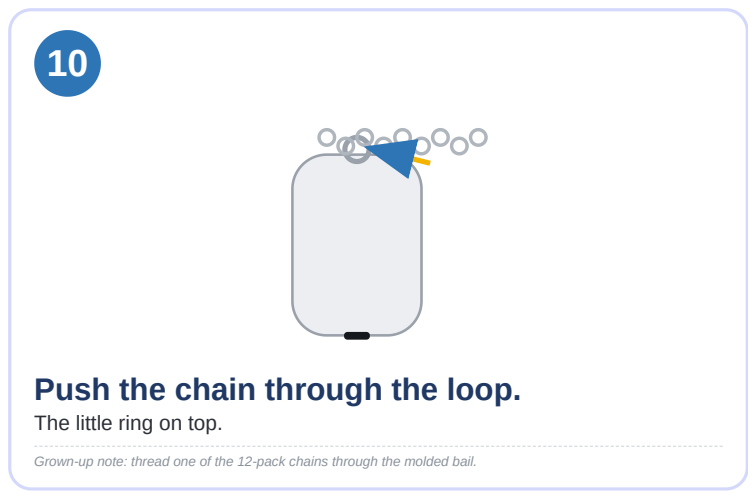
[picture p177: page 13]

Push the chain through the loop.
The little ring on top.

Grown-up note: thread one of the 12-pack chains through the molded bail.

11

+

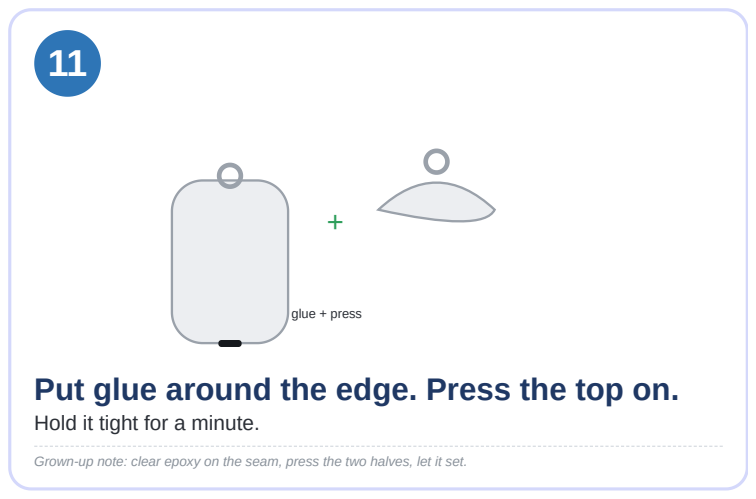
[picture p178: page 14]
glue + press

Put glue around the edge. Press the top on.
Hold it tight for a minute.

Grown-up note: clear epoxy on the seam, press the two halves, let it set.

12

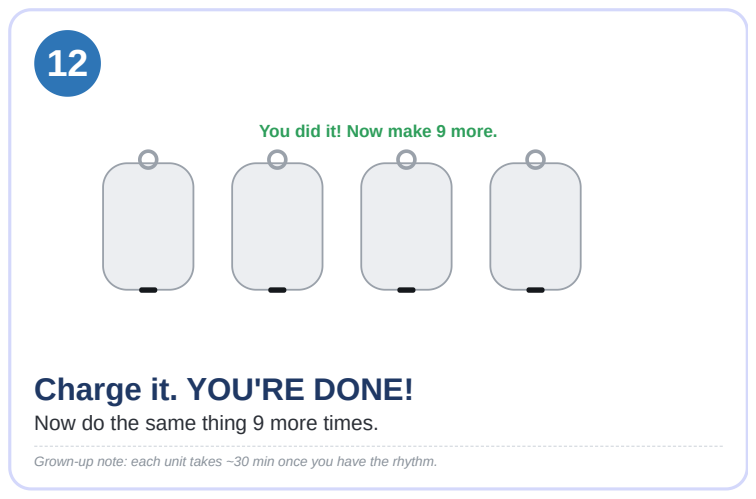
[picture p179: page 15]

You did it! Now make 9 more.

Charge it. YOU'RE DONE!
Now do the same thing 9 more times.

Grown-up note: each unit takes ~30 min once you have the rhythm.

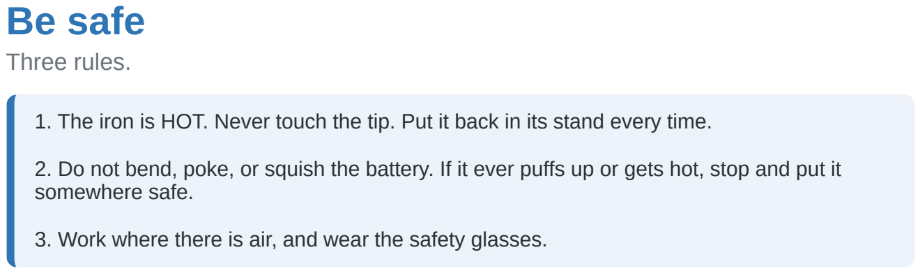
[picture p180: figure]
Be safe; Three rules.; somewhere safe.

1. The iron is HOT. Never touch the tip. Put it back in its stand every time.
2. Do not bend, poke, or squish the battery. If it ever puffs up or gets hot, stop and put it
3. Work where there is air, and wear the safety glasses.

# Shopping checklist

## GREEN = already in your cart. RED = still need to add. Bring this so you do not get

stuck.

Status | Item | Note
HAVE | 10 x XIAO board (nRF52840 Sense) | shipped from DigiKey
IN CART | Battery: 5-pack 3.7V 500mAh | you have 5 cells
IN CART | Battery: EEMB 3.7V 250mAh | 1 slim cell
IN CART | Chain: 12-pack stainless 20in
IN CART | Double-sided foam tape
IN CART | Clear epoxy (Gorilla, 5-min) | glue the shell shut
IN CART | Kapton tape | insulate the solder joints
IN CART | Silicone wire 30AWG | longer leads if needed
IN CART | Soldering iron kit (iron + 5 tips + stand) | NOTE: no solder included!
ADD | Solder wire, rosin-core 60/40 | the kit has none. REQUIRED
ADD | USB-C DATA cable (not charge-only) | to flash + charge the board. REQUIRED
ADD | Flush cutters | cut the battery plug + trim wires
ADD | Flux pen (rosin) | makes the tiny soldering easy
ADD MORE More batteries: bump the 5-pack to x2 or x3 | you have 6 cells; 10 units need ~12
OPTIONAL | Helping-hands clip (~$12, not the $61 one) | holds the board, or just tape it
OPTIONAL | Multimeter | check a cell / catch a short. Buy local, faster
OPTIONAL | Isopropyl alcohol (90%+) | clean off flux. Buy at a pharmacy
OPTIONAL | Heat-shrink tube | or just wrap joints in your kapton tape
DECIDE | 3D-print the shells OR order prints | you need 10-12 shells
LATER | Apple Developer + a test iPhone | for the phone app, not blocking
