anticipation-labs/anticipy-hardware/latest_builds/E1P1/E1P1_Fabrication_and_Assembly.pdf

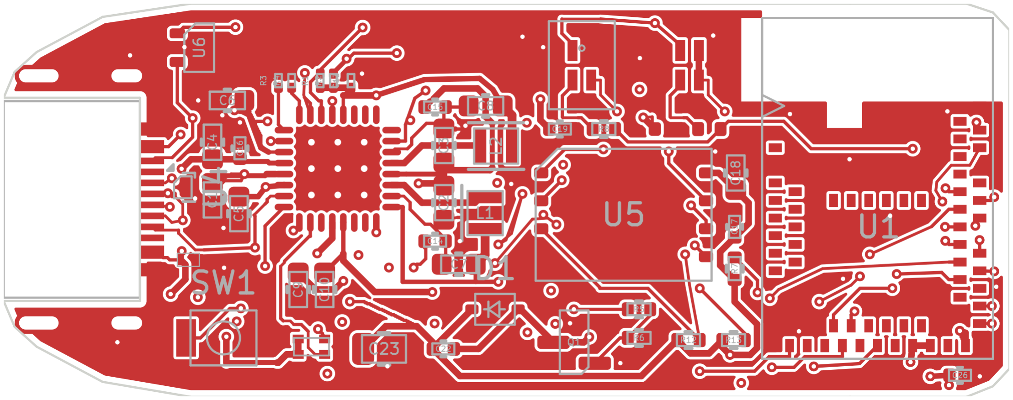
[picture p181: figure]

Anticipy E1P1 | Prototype manufacturing data | 2026-09-09 | 1

ANTICIPY LABS / E1P1 / 09 SEPTEMBER 2026

# PCB fabrication and assembly release

Corrected prototype manufacturing data. This document identifies the frozen PCB, its required fabrication process and the first-article checks. It is not a finished-wearable qualification certificate.

Actual native front-copper and placement export. USB-C is at the left cutout; the antenna keepout is at the upper right. Not a 1:1 print template.

Released geometry | Verified file checks
45.75 x 17.88 x 0.80 mm; 4 copper layers | DRC 0 / unrouted 0 / schematic parity 0 / ERC 0
47 machine-fitted parts: 44 top, 3 bottom | All 45 named nets pass independent copper connectivity
1,310 track segments / 137 vias | No ignored DRC/ERC categories or individual exclusions

## Corrections included

Moved U4 away from C1, repaired its three short front-copper branches and removed their negative courtyard exception. Corrected U2/U4 mask openings. Specified epoxy-filled, copper-capped vias. Fixed the four component selections and three packaging aliases across schematic, board, libraries and BOMs; named the selected Jauch battery consistently.

## Use the whole release

Native project: pcb/electrical/Anticipy_R1_E1_PROTOTYPE.kicad_pro. Use the matching Gerbers, drills, IPC netlist, placement CSV, fitted BOM, DNP list, paste and via-coordinate CSV in pcb/manufacturing/. The supplied STEP shows the board and nominal component envelopes; Gerbers and drills control manufacture.

PCB SHA-256: 78fe28acde6ceb3ab33aac8af503d4c4
18540cce31979cc91d3add5e5d0bec36

Anticipy E1P1 | Prototype manufacturing data | 2026-09-09 | 2

# Fabrication requirements

Use the exact outline and USB cutout. Do not scale. Target outline tolerance +/-0.10 mm and finished thickness 0.80 +/-0.08 mm. Material: FR-4; ENIG exposed finish, green mask and white silk. This process is more demanding than an ordinary tented-via four-layer order.

Layer, top to bottom | Nominal thickness | Dielectric basis
F.Cu | 0.0350 mm | Outer nominal 1 oz
Prepreg | 0.0994 mm | 3313 RC57%; Dk 4.10
In1.Cu | 0.0152 mm | Inner copper
Core | 0.5000 mm | NanYa NP-155F; Dk 4.48
In2.Cu | 0.0152 mm | Inner copper
Prepreg | 0.0994 mm | 3313 RC57%; Dk 4.10
B.Cu | 0.0350 mm | Outer nominal 1 oz

Native JLC04081H-3313 basis; copper plus dielectric sum 0.7992 mm. Approximately 10 um mask layers are additional. The manufacturer must return the actual finished stackup, plating/etch geometry and thickness.

Feature | Required process
All 137 vias | Nonconductive epoxy fill, planarize and copper cap both ends: IPC-4761 Type VII. 128 x nominal
0.200 mm bores; 9 x nominal 0.304 mm. Follow the via-coordinate CSV. Ordinary tenting is insufficient.
Four J1 plated slots | Keep open: two 0.600 x 1.400 mm and two 0.600 x 1.800 mm. Do not fill connector slots. No NPTH
features.
Track / annulus / mask | Minimum track and normal clearance 0.127 mm; smallest via annulus 0.125 mm. U2/U4 local mask
expansion 0.050 mm; U2 nominal mask dam 0.100 mm. Preserve supplied mask geometry.

## USB: 90 ohms differential +/-10%

Main B.Cu pair: 0.135 mm width / 0.150 mm gap, about 33.74 mm, over actual filled In2 ground across 0.0994 mm prepreg. The recorded supplier uniform-line model supports these dimensions. Require a representative 81-99 ohm coupon/TDR result and CAM review of launches, vias and nearby ground. Preserve the 0.300 mm coplanar zone spacing and RF keepouts. A coupon does not certify the whole USB channel.

Bare-board acceptance: 100% electrical test against IPC-D-356, AOI, dimensions, filled-via/cap quality and representative microsection/coupon records. Panel rails, tooling and depanel tabs belong outside the final outline and antenna area.

Anticipy E1P1 | Prototype manufacturing data | 2026-09-09 | 3

# Assembly and first articles

47 fitted SMT references, 27 exact MPN groups. C20, MIC2 and R9 are DNP. Use the fitted-only paste files; do not add paste to test pads. External BT1, M1 and TH1 are installed after reflow.

## Stencil and inspection

Starting specification: 80 um laser-cut electropolished stencil, Type 5 SAC305 paste, existing apertures. U4 maximum stencil thickness is 101.6 um. Minimum screened area ratio is 0.994 at 80 um; C13 is 1.118. U2 thermal paste is nine 0.925 mm square windows, 62.86% nominal coverage. Use SPI, profiled two-sided reflow, AOI and first-article hidden-joint X-ray. These checks define the process; production yield is not yet measured.
Closely placed PMIC parts assume +/-0.05 mm placement per part. U4/C1 maximum-body gap after repair is 0.375 mm before that placement allowance. Keep flux, cleaning fluid and debris out of the microphone acoustic port; do not ultrasonically clean it. Solder the USB shell stakes and avoid board bending during depaneling.
External part | Wiring
Jauch LP561836JU+PCM+2 WIRES 50MM 350 mAh minimum protected pack | BT1.1 = positive VBAT BT1.2 = negative GND
VCLP1020B002L motor | M1.1 = 3V_MAIN M1.2 = HAPTIC_NEG
B57540G1103F000, separate 10k NTC | TH1.1 = NTC / TH1.2 = GND Insulate and thermally couple to cell
SWD probe signal | Back-side PCB test pad
SWDIO / SWCLK | TP1 / TP2
nRESET (optional) / VTref sense / GND | TP3 / TP4 (3V_MAIN) / TP5

## First-power order

1. Inspect unpowered boards, soldering, shorts and polarity; leave battery disconnected.
2. Apply current-limited 5 V through J1; measure 3V_MAIN before attaching the probe.
3. Program the supplied E1P1 BUCK2-main bench HEX over SWD and verify readback. VTref only senses voltage; do not power the board from it.
4. Capture boot logs, rail/current measurements, audio, BLE/USB, LED/button and motor checks. Keep charging disabled; do not attach an unverified pack.

## Limits that remain

Physical hardware tests have not run. The included bench firmware has live PDM/Opus/BLE audio and NAND identification; full offline NAND recording/recovery/backfill, qualified charging and signed updates remain incomplete. Do not deliver these as qualified customer wearables. The board does not fit a 30 x 14 x 8 mm overall shell.

Supply: 26 of 27 MPN groups have sufficient listed distributor stock for 20 boards plus two-board spares. U1 radio modules must be allocated; 25 carrier-delivered modules in BC are consignment candidates, not confirmed usable stock at an assembler.

Anticipy E1P1 | Prototype manufacturing data | 2026-09-09 | 4

# Fitted placement index

Every machine-fitted reference, including parts whose native F.Fab reference label is hidden. Coordinates and rotation below are the exact exported placement CSV values: millimetres, X right / Y up; T = top, B = bottom. Native editor Y coordinates have the opposite sign. Do not mirror or negate these values a second time for machine import.

Ref / side | X | Y | Rot.
C1 / T | 29.500 | -30.025 | -90
C10 / T | 34.600 | -34.100 | -90
C13 / T | 35.800 | -24.600 | 90
C14 / T | 39.625 | -31.900 | 0
C15 / T | 39.625 | -25.800 | 0
C16 / T | 30.750 | -27.675 | 90
C17 / T | 53.250 | -31.250 | 90
C18 / T | 53.300 | -28.800 | 90
C19 / T | 45.300 | -26.800 | 0
C2 / T | 40.025 | -30.150 | -90
C22 / T | 40.000 | -36.800 | 0
C23 / T | 37.300 | -36.800 | 0
C25 / B | 58.500 | -38.000 | 180
C26 / T | 63.500 | -38.000 | 0
C3 / T | 40.025 | -27.550 | 90
C4 / T | 29.500 | -27.400 | 90
C5 / T | 30.700 | -30.650 | -90
C6 / T | 30.175 | -25.500 | 180
C7 / T | 40.700 | -32.950 | 180
C8 / T | 41.925 | -25.750 | 180
C9 / T | 33.400 | -34.100 | -90
D1 / T | 42.350 | -35.000 | 0
D2 / T | 28.400 | -32.750 | 0
J1 / T | 20.000 | -30.000 | 90
Ref / side | X | Y | Rot.
L1 / T | 41.900 | -30.625 | 90
L2 / T | 42.400 | -27.575 | 180
LED1 / T | 34.000 | -36.700 | 0
MIC1 / T | 46.300 | -23.900 | 0
Q1 / T | 45.950 | -36.500 | 180
R1 / T | 34.400 | -24.600 | 90
R10 / B | 63.300 | -34.600 | 0
R11 / B | 63.300 | -35.400 | 0
R12 / T | 51.150 | -36.400 | 0
R13 / T | 53.200 | -36.400 | 0
R2 / T | 35.000 | -24.600 | 90
R3 / T | 32.500 | -24.600 | 90
R4 / T | 33.100 | -24.600 | 90
R5 / T | 48.900 | -35.000 | 0
R6 / T | 48.900 | -36.300 | 0
R7 / T | 53.250 | -33.150 | 90
R8 / T | 47.300 | -26.800 | 0
SW1 / T | 30.000 | -36.300 | 0
U1 / T | 59.750 | -29.500 | 0
U2 / T | 35.200 | -28.600 | 180
U4 / T | 28.150 | -29.450 | -90
U5 / T | 48.200 | -30.700 | 0
U6 / T | 28.900 | -23.100 | 0

Use the native package drawing, component pin-1 marks and machine-specific rotation convention to validate the first placement. MPNs are in Machine_Assembly_BOM.csv. U2 is at native (35.2,28.6); U4 is at native (28.15,29.45).

1 | 2 | 3 | 4 | 5 | 6 | 7 | 8 | 9 | 10 | 11
1 | 2 | 3 | 4 | 5 | 6 | 7 | 8 | 9 | 10 | 11

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
FGH Date: 2026-09-09

KiCad E.D.A. 10.0.6

Size: A2 | Rev: E1P1 Id: 1/1

Title: Anticipy E1P1 power-corrected prototype schematic

File: Anticipy_R1_E1_PROTOTYPE.kicad_sch

Sheet: /

Anticipy

E1P1 FIRST-ARTICLE PACKAGE - PHYSICAL QUALIFICATION PENDING

E1 prototype / native ERC + PCB parity required / physical validation pending

A 1 | B

2 SW1 B3U-1000P

1 | 2 R11

0R

1 | 2 R10

0R

1 | 2 R9

100R 1%

1 | 2 R1

10k 1%

1 | 2 R2

10k 1%

IO 1 | GND 2 D2

ESD441DPYR

IO1 1

IO2 2 | GND 3 U6

TPD2E2U06DCKR

SWDCLK 1 | TP2

SWDCLK

SWDIO 1 | TP1

SWDIO

1 | 2 C19

100nF 16V X7R

1 | 2 C17

100nF 16V X7R

1 | 2 C7

10uF 25V X5R

1 | 2 C18

1uF 16V X7R

1 | 2 C16

100nF 16V X7R

1 | 2 C15

100nF 16V X7R

RESET 1 | TP3 RESET
3V_MAIN 1 | TP4

3V_MAIN

1 | 2 C22

100nF 16V X7R

1 | 2 C20

100nF 16V X7R

1 | 2 C26

10uF 6.3V X5R

1 | 2 C25

10uF 6.3V X5R

1 | 2 C23

47uF 6.3V X5R

1 | 2 C9

10uF 25V X5R

1 | 2 C8

10uF 25V X5R

1 | 2 C14

100nF 16V X7R

1 | 2 C13

100nF 25V X5R

1 | 2 C10

10uF 25V X5R

1 | 2 C6

2.2uF 16V X7R

1 | 2 R5

100R 1%

1 | 2 R6

100k 1%

1 | 2 R8

100R 1%

1 | 2 R7

10k 1%

1 | 2 R4

150k 1%

1 | 2 R3

150k 1%

1 | 2 C3

10uF 25V X5R

1 | 2 C2

10uF 25V X5R

1 | 2 C4

10uF 25V X5R

1 | 2 C5

1uF 16V X7R

BUCK1OUT 1 PVSS1 2

SW1 3 PVDD 4

# SW2 5 PVSS2 6 GPIO0 7 GPIO1 8 GPIO2 9 GPIO3 10 GPIO4 11

VDDIO 12

SDA 13

SCL 14

SHPHLD 15

VSET2 16

VSET1 17 | NTC 18

VBAT 19

VSYS 20

VBUS 21

VBUSOUT 22 CC1 23 CC2 24

LED0 25

LED1 26

LED2 27

LDO1IN 28

LDO1OUT 29

LDO2IN 30

LDO2OUT 31 BUCK2OUT 32

EP 33 U2

nPM1300

CS# 1

SO/SIO1 2 WP#/SIO2 3 GND 4

SI/SIO0 5

SCLK 6 HOLD#/SIO3 7

VCC 8

EP 9 U5 MX35LF4GE4AD-Z4I

IO1 1

IO2 2 | GND 3 U4

TPD2EUSB30ADRTR

VDD 1

SELECT 2 CLOCK 3 DATA 4 | GND 5 GND 6 GND 7 GND 8 MIC1 CMM-3424DT-26165-TR
1 | 2 C1

1uF 16V X7R

GND 1 GND 2 P1.10 3 P1.11 4 P1.12 5 P1.13 6 P1.14 7 P1.15 8 P0.03/AIN1 9 P0.29/AIN5 10 P0.02/AIN0 11 P0.31/AIN7 12 P0.28/AIN4 13 P0.30/AIN6 14 GND 15 P0.27 16 P0.00/XL1 17 P0.01/XL2 18 P0.26 19 P0.04/AIN2 20 P0.05/AIN3 21 P0.06 22 P0.07/TRACECLK 23 P0.08 24 P1.08 25 P1.09/TRACEDATA3 26 P0.11/TRACEDATA2 27

VDD 28 P0.12/TRACEDATA1 29

VDDH 30 DCCH 31

VBUS 32 GND 33 D- 34 D+ 35 P0.14 36 P0.13 37 P0.16 38 P0.15 39 P0.18/RESET 40 P0.17 41 P0.19 42 P0.21 43 P0.20 44 P0.23 45 P0.22 46 P1.00/TRACEDATA0 47 P0.24 48 P0.25 49 P1.02 50

SWDIO 51 P0.09/NFC1 52

SWDCLK 53 P0.10/NFC2 54 GND 55 P1.04 56 P1.06 57 P1.07 58 P1.05 59 P1.03 60 P1.01 61 U1 MDBT50Q-1MV2 | pwr 1 PWR_FLAG pwr 1 PWR_FLAG | pwr 1 PWR_FLAG
1 | 2 L2

2.2uH

1 | 2 L1

2.2uH

VDD 1

SELECT 2 CLOCK 3 DATA 4 | GND 5 GND 6 GND 7 GND 8 MIC2 CMM-3424DT-26165-TR

PVSS2

1 | GND

2 NT2 PVSS2-GND

PVSS1

1 | GND

2 NT1 PVSS1-GND

3V_MIC 1 | TP13

3V_MIC

VSYS 1 | TP10

VSYS

2V5_AUX 1 | TP12

2V5_AUX

VBUSOUT 1 | TP11

VBUSOUT

GND 1 | TP5 GND
PMIC_INT 1 | TP14 PMIC_INT
NTC 1 | GND 2 TH1

10k 1% external NTC

VBUS 1 | TP9

VBUS

UART_TX 1 | TP6 UART_TX
VBAT 1 | TP8

VBAT

UART_RX 1 | TP7 UART_RX

GND_A1_B12 1

VBUS_A4_B9 2

SBU2_B8 3 CC1_A5 4 D-_B7 5 D+_A6 6 D-_A7 7 D+_B6 8

SBU1_A8 9 CC2_B5 10

VBUS_B4_A9 11 GND_B1_A12 12

SHIELD S1

SHIELD S2

SHIELD S3

SHIELD S4 J1 USB4500-03-1-A

1 | 2 R13

10k 1%

1 | 2 R12

10k 1%

+

1 | -

2 M1

VCLP1020B002L

K

1

A 2 D1

1N4148WS-13-F

VBAT+ 1

VBAT- 2 BT1

Jauch 350mAh min protected 1S LiPo

G

1

S

2 | D

3 Q1

AO3400A

BLUE_K 1 BLUE_A 2 | RED_K 3 RED_A 4 LED1

APHB1608LVBDSEKJ3C

2V5_AUX

GND

LED_BLUE_K

VSYS

LED_RED_K

SHPHLD_BTN

GND | HAPTIC_GATE GND | HAPTIC_NEG

VSYS

3V_MAIN

VBAT | HAPTIC_NEG HAPTIC_NEG

3V_MAIN

GND

FLASH_IO3

3V_MAIN | FLASH_IO2

GND

3V_MAIN

GND

VBUS

VBAT

VBUS

## VBUS UART_RX UART_TX

## GND USB_D-

GND

PMIC_INT

USB_D+

NTC

USB_D+

USB_D-

USB_CC1

2V5_AUX

GND

3V_MIC

## VBUSOUT VSYS

GND

VBUS | PVSS1 PVSS2 | GND USB_CC2 | GND

USB_D-

GND | 2V5_AUX | SW1
3V_MAIN | SW2 GND

USB_MCU_D-

VSYS

PDM_DATA_MIC2 | PDM_DATA

SW2

USB_D+ | USB_MCU_D+
PVSS2 | VBUS | PVSS2
GND | PVSS1
PDM_DATA_MIC2 | GND

3V_MAIN

3V_MAIN | I2C_SCL

I2C_SDA

VBUS

PDM_CLK

SW1 | NTC

VBAT GND

I2C_SDA

I2C_SCL UART_RX UART_TX HAPTIC_PWM

GND USB_CC2 USB_CC1 | GND

VSYS

3V_MAIN

3V_MAIN

GND

PVSS1

3V_MIC

GND

VBUS

GND

PVSS2 PVSS1

VBUSOUT

3V_MAIN

VBUSOUT GND USB_MCU_D-

USB_MCU_D+

USB_CC1

3V_MAIN

PDM_CLK

PDM_DATA RESET PMIC_INT FLASH_SCK

FLASH_IO0

FLASH_CS

FLASH_IO2

FLASH_IO1

FLASH_IO3

3V_MIC

USB_CC2 | GND

SWDIO

USB_D+

SWDCLK | USB_D-

GND

VSYS

VSYS

VSYS

VSYS

GND

GND

PVSS2

VSYS | PVSS1

LED_BLUE_K

GND

GND

GND

PMIC_INT | LED_RED_K

3V_MAIN

I2C_SDA

I2C_SCL SHPHLD_BTN

VSET2

VSET1

VBUSOUT | GND
PDM_DATA_MIC1 | GND
VSYS | GND

PDM_CLK

GND

VSET1 | GND

3V_MIC

VSET2 | GND

3V_MAIN

3V_MAIN | FLASH_CS

FLASH_IO3

PDM_DATA_MIC1 | PDM_DATA

FLASH_SCK

HAPTIC_GATE | GND HAPTIC_GATE

GND

HAPTIC_PWM

FLASH_IO0

VBAT | GND
2V5_AUX | PVSS1

GND

## VBUSOUT RESET SWDIO

SWDCLK

VSYS | GND
3V_MIC | GND

FLASH_IO2

FLASH_IO1

3V_MAIN | GND

FLASH_CS GND

3V_MAIN | PVSS2

3V_MAIN

3V_MAIN | HAPTIC_NEG
3V_MAIN | GND

3V_MAIN

GND

3V_MAIN | GND

GND

3V_MIC

3V_MAIN

3V_MIC | GND

GND

GND

3V_MIC

MIC2/R9/C20 DNP baseline. No IMU. NAND type is a requirement exception proposal. RF: module antenna keepout from exact vendor drawing; shell/metal clearance NOT validated. STORAGE: 4-Gbit raw SLC NAND requires ECC, bad-block, filesystem and power-loss firmware. BT1: Jauch LP561836JU+PCM, 350mAh min + external TH1. CHARGING DISABLED pending pack-specific tests. BUTTON: SW1 switches SHPHLD to GND only; PMIC_INT reports state to MCU. USB CC1/CC2 connect directly to nPM1300. Do not fit external 5.1k Rd resistors. POWER: BUCK2 boots 3V_MAIN = 3.0V for MCU + NAND. BUCK1 = unloaded 2V5_AUX. LDSW1 input = 3V_MAIN. Never tie buck outputs. R1 E1 / FIRST-ARTICLE PROTOTYPE / QUALIFICATION PENDING

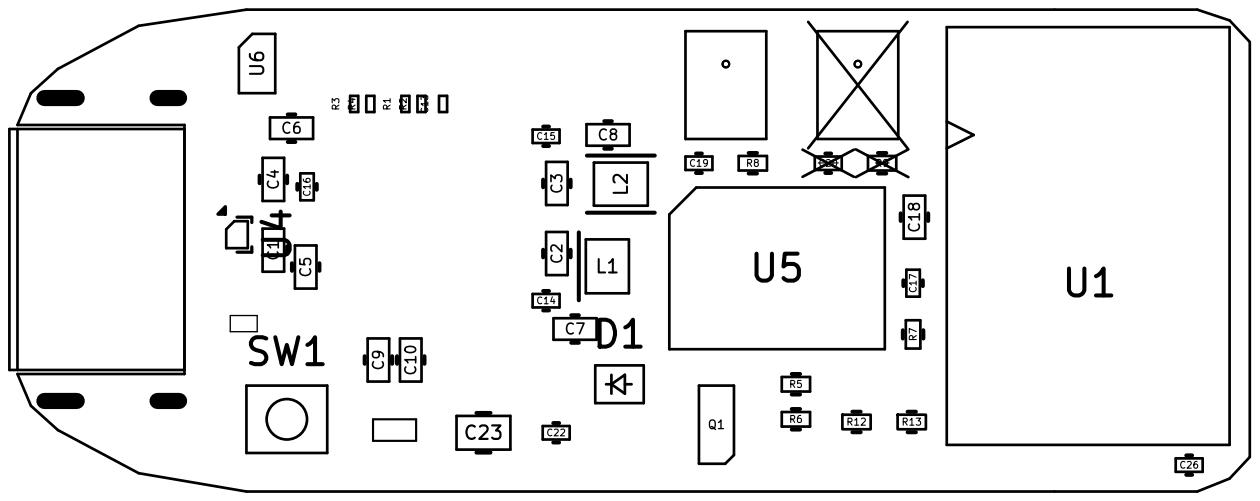
[picture p182: page 6]

R11 R10 | C25

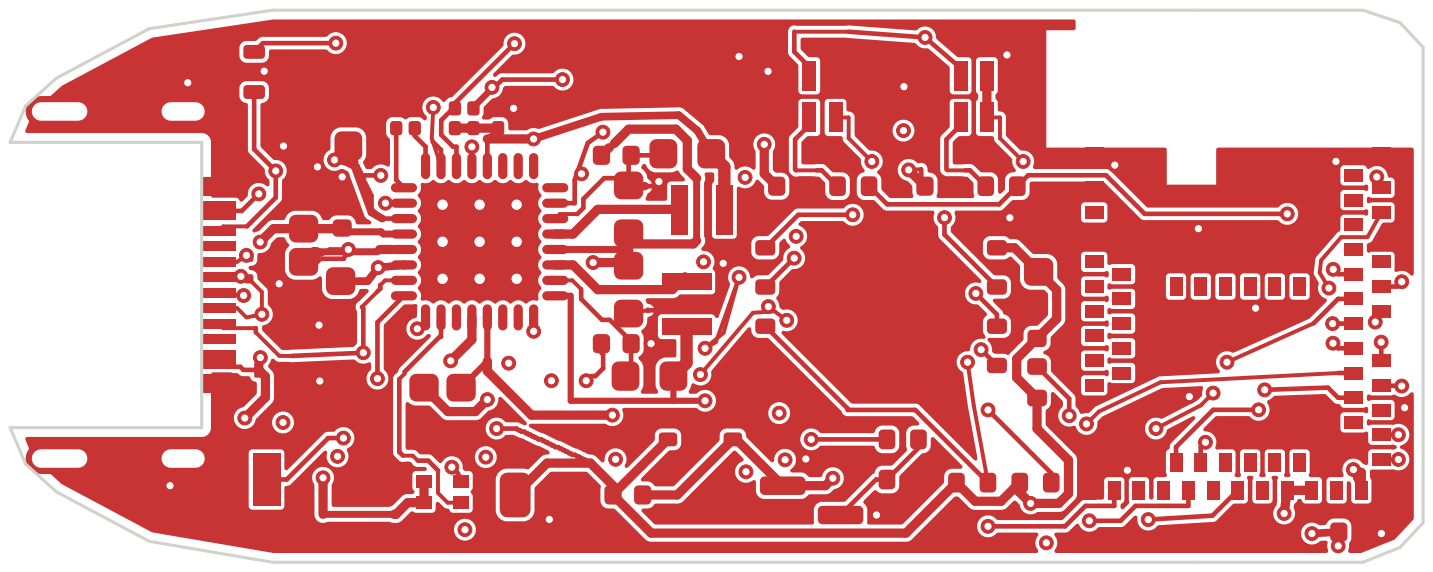
[picture p183: page 8]

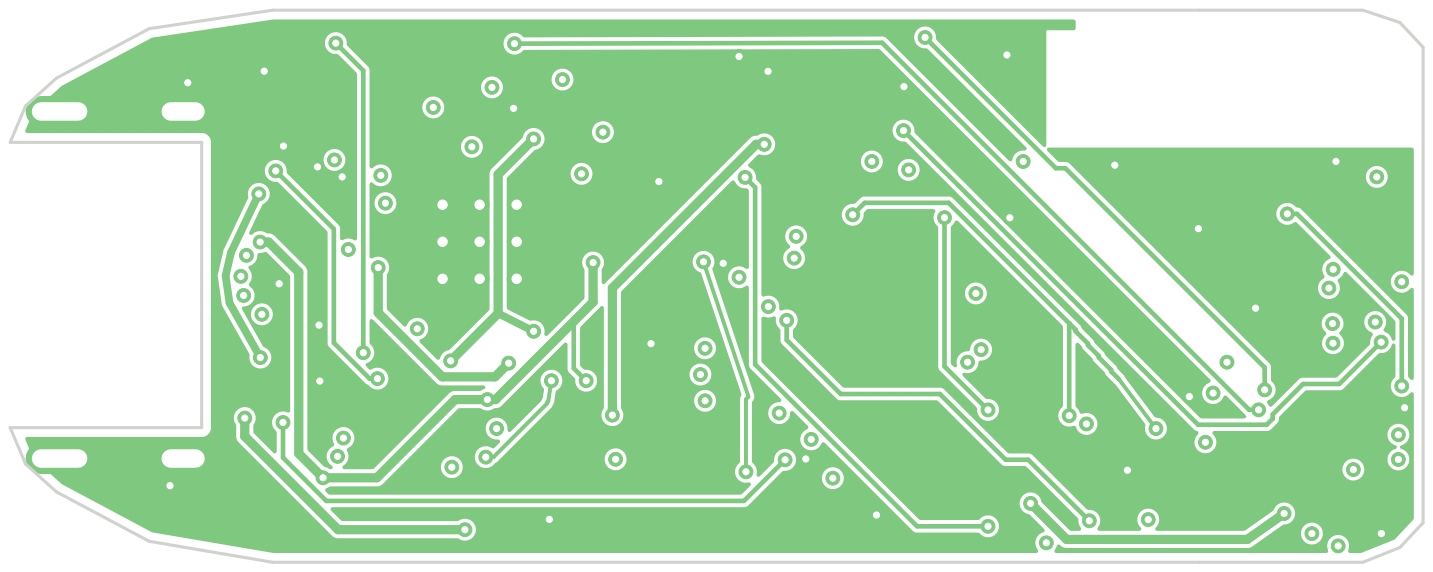
[picture p184: page 9]

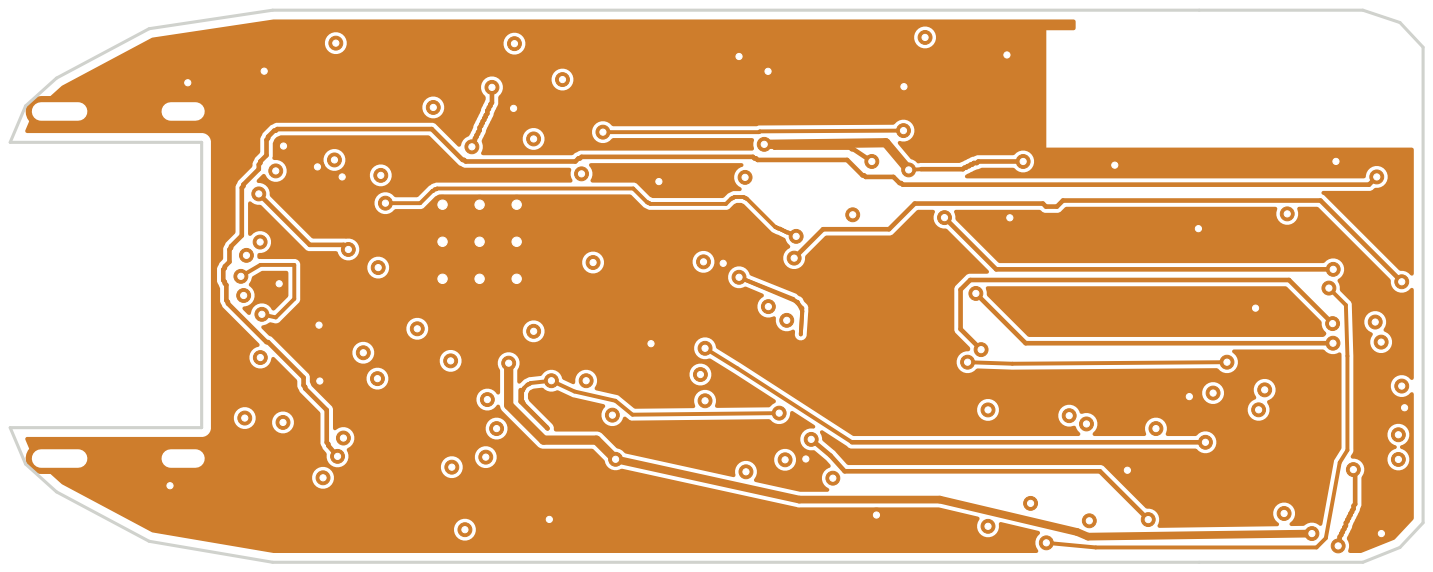
[picture p185: page 10]

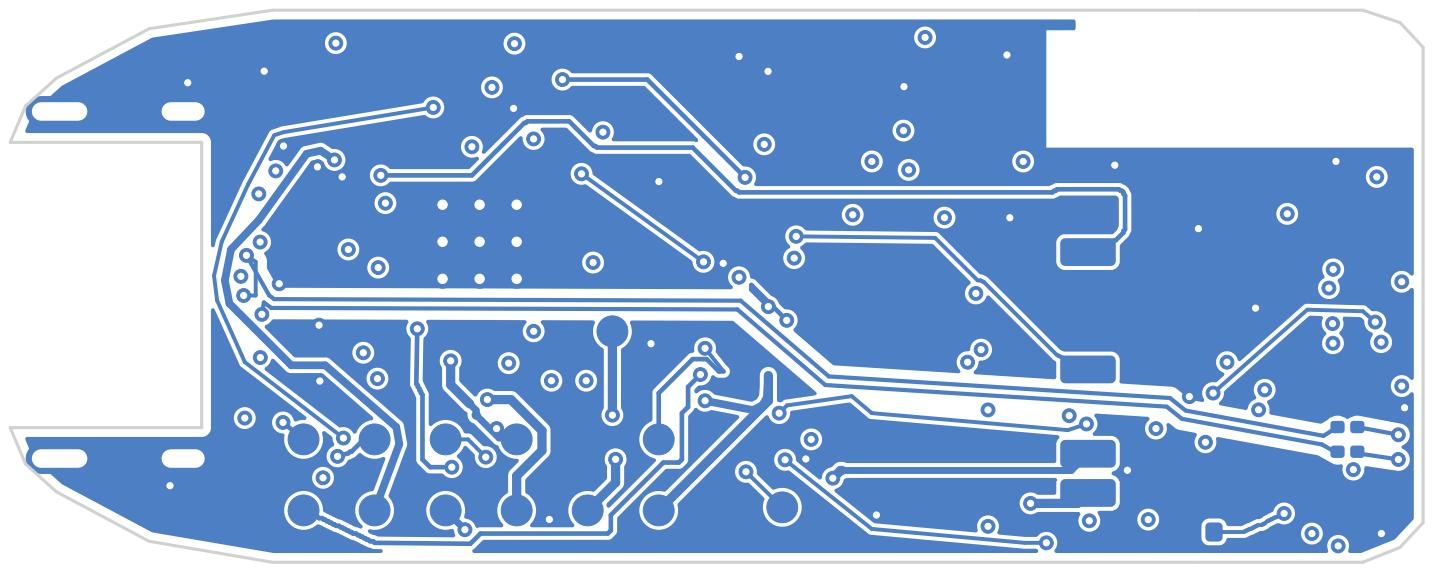
[picture p186: page 11]

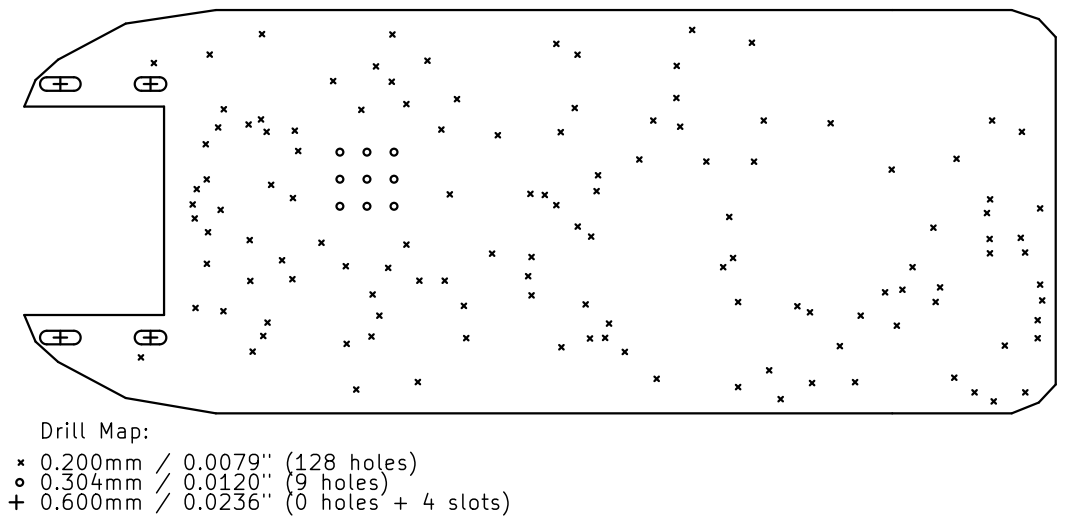
[picture p187: page 12]
Drill Map:; 0.200mm / 0.0079" (128 holes) 0.304mm; 0.0236" (0 holes + 4 slots)
