anticipation-labs/anticipy-hardware/04_MECHANICAL/PRINT_READY/Anticipy_v09_five_units_plate_layout.png

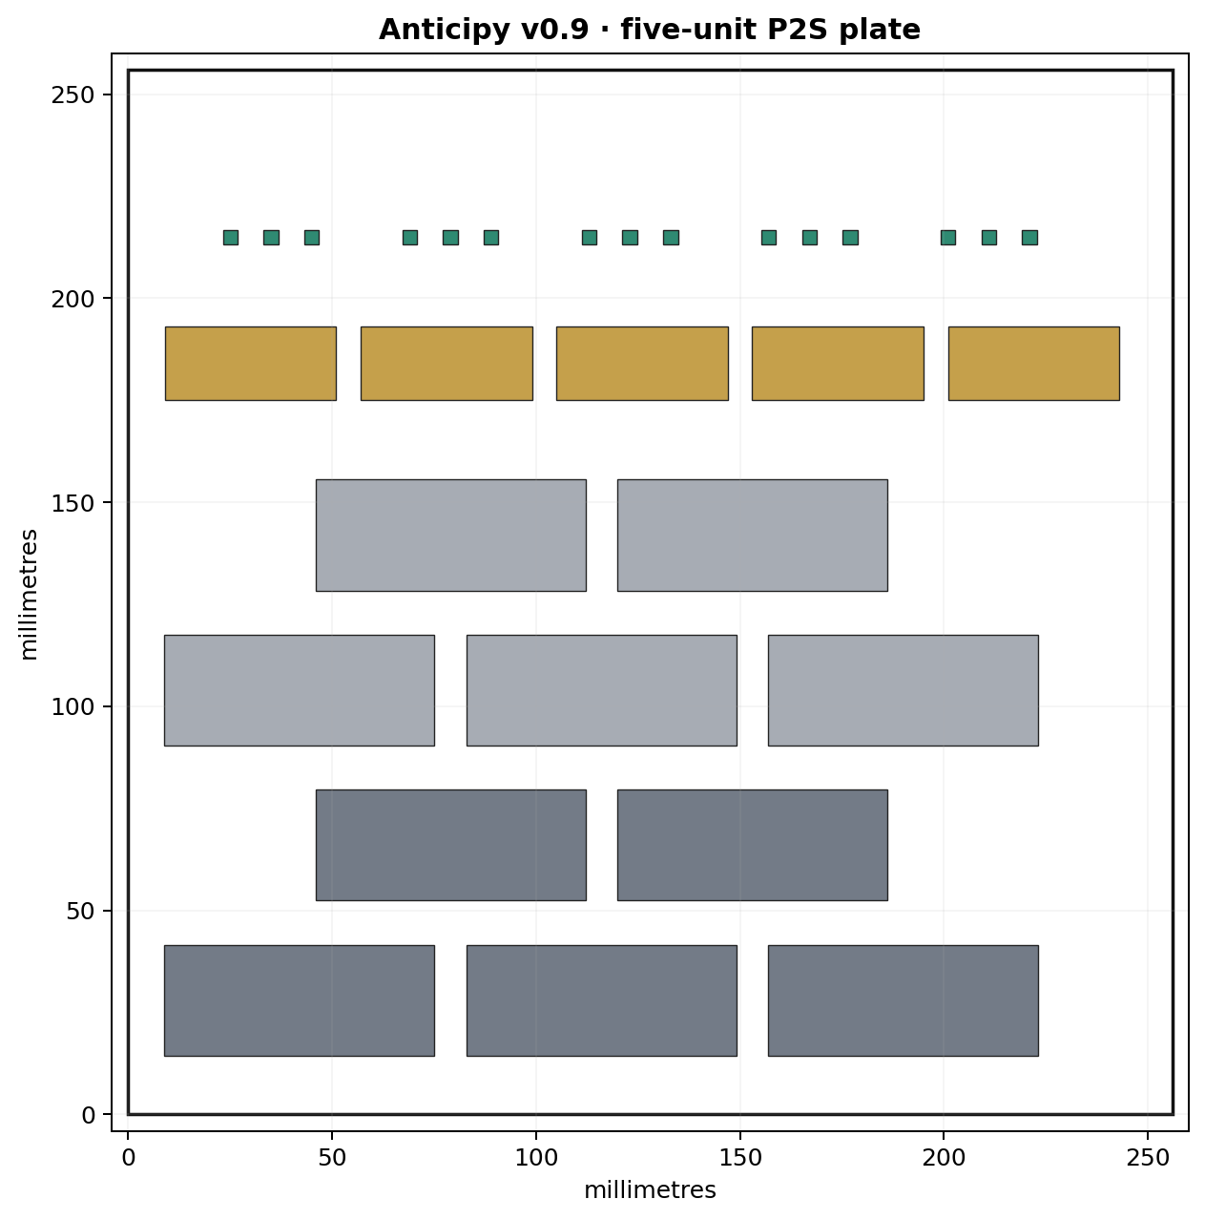
04_MECHANICAL/PRINT_READY/Anticipy_v09_five_units_plate_layout.png
