anticipation-labs/anticipy-hardware/04_MECHANICAL/PRINT_READY/v09_internal_layout.png

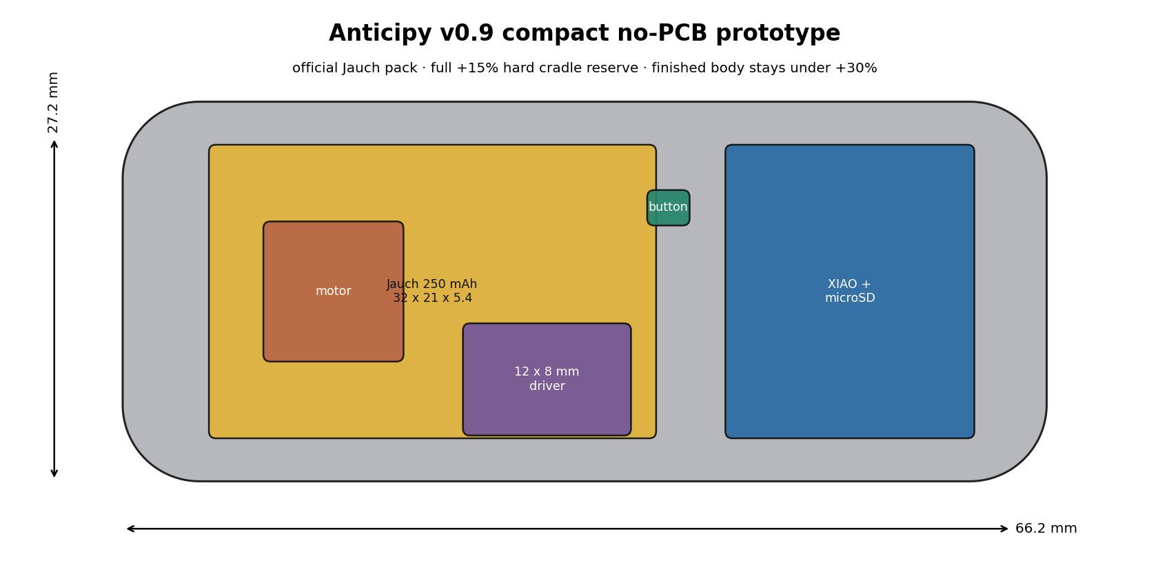
04_MECHANICAL/PRINT_READY/v09_internal_layout.png
