anticipation-labs/anticipy-hardware/08_HISTORICAL_PACKAGES/2026-08-28_48h_v13/01_PRINT/PRINT_THIS_ONE_UNIT_P2S_preview.png

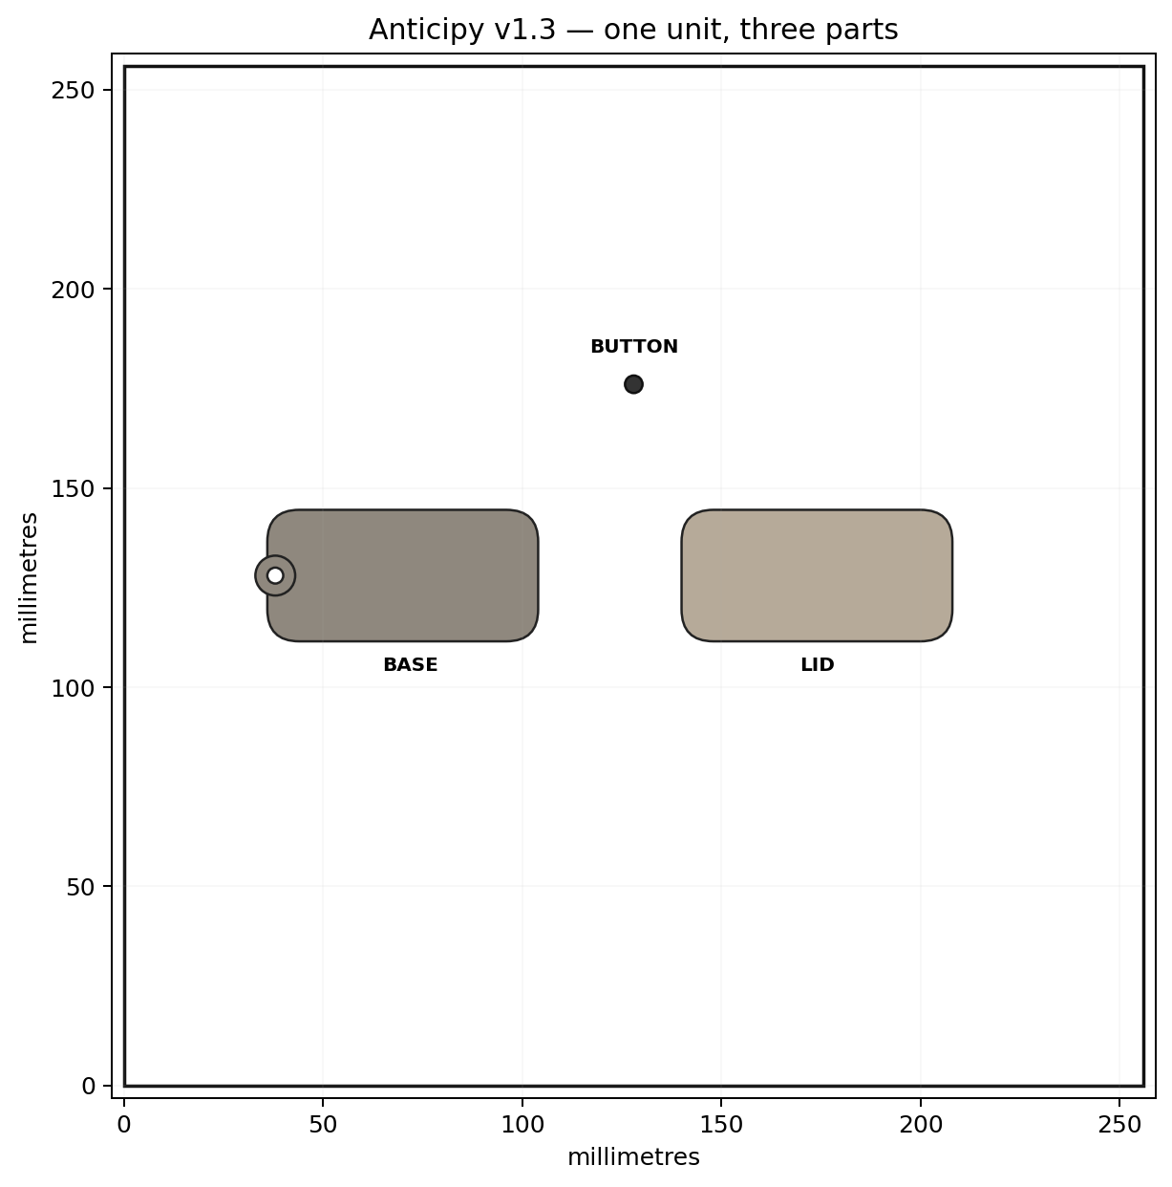
08_HISTORICAL_PACKAGES/2026-08-28_48h_v13/01_PRINT/PRINT_THIS_ONE_UNIT_P2S_preview.png
