anticipation-labs/anticipy-hardware/08_HISTORICAL_PACKAGES/2026-08-28_48h_v13/01_PRINT/v13_internal_layout.png

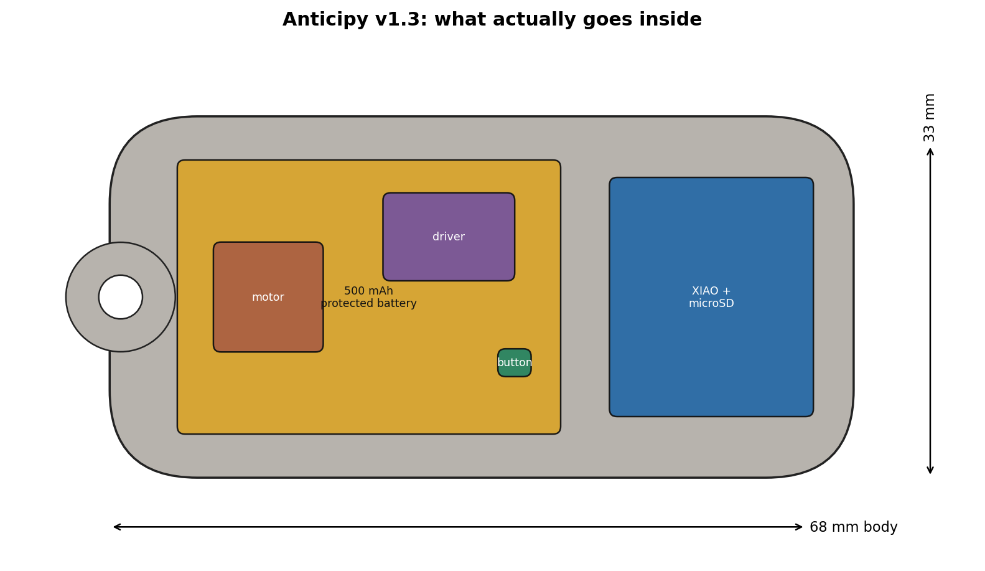
08_HISTORICAL_PACKAGES/2026-08-28_48h_v13/01_PRINT/v13_internal_layout.png
