anticipation-labs/anticipy-hardware/latest_builds/E1P1/cad/Oval_E1_Gold_Exterior.png

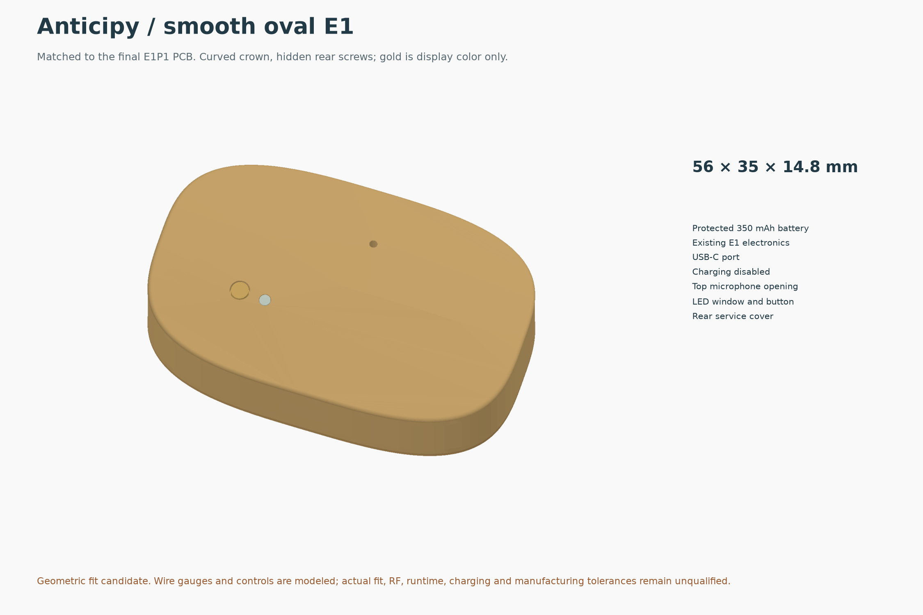
latest_builds/E1P1/cad/Oval_E1_Gold_Exterior.png
