anticipation-labs/anticipy-hardware/latest_builds/E1P1/cad/Oval_E1_Inside.png

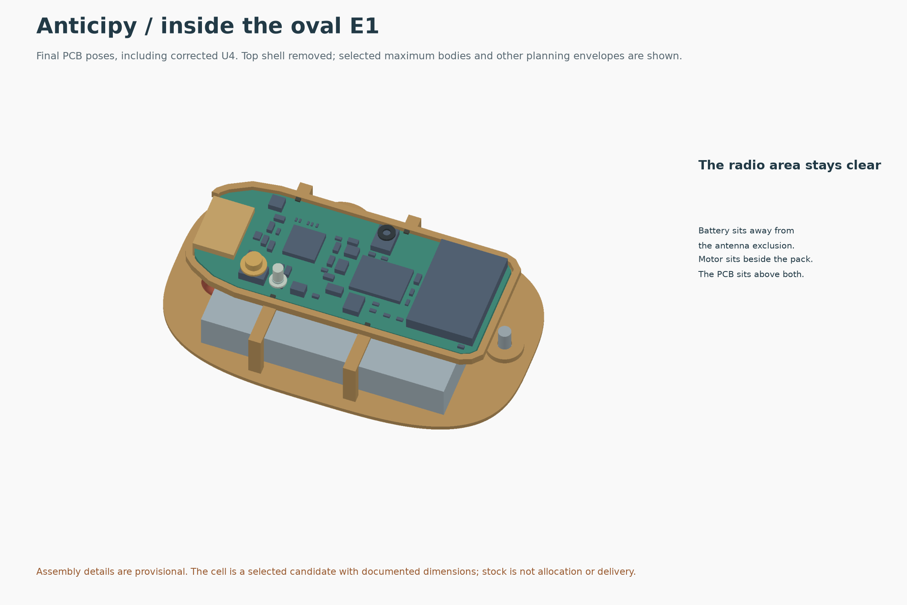
latest_builds/E1P1/cad/Oval_E1_Inside.png
