anticipation-labs/anticipy-hardware/latest_builds/reference_evidence/TI_DRT_land_pattern.png

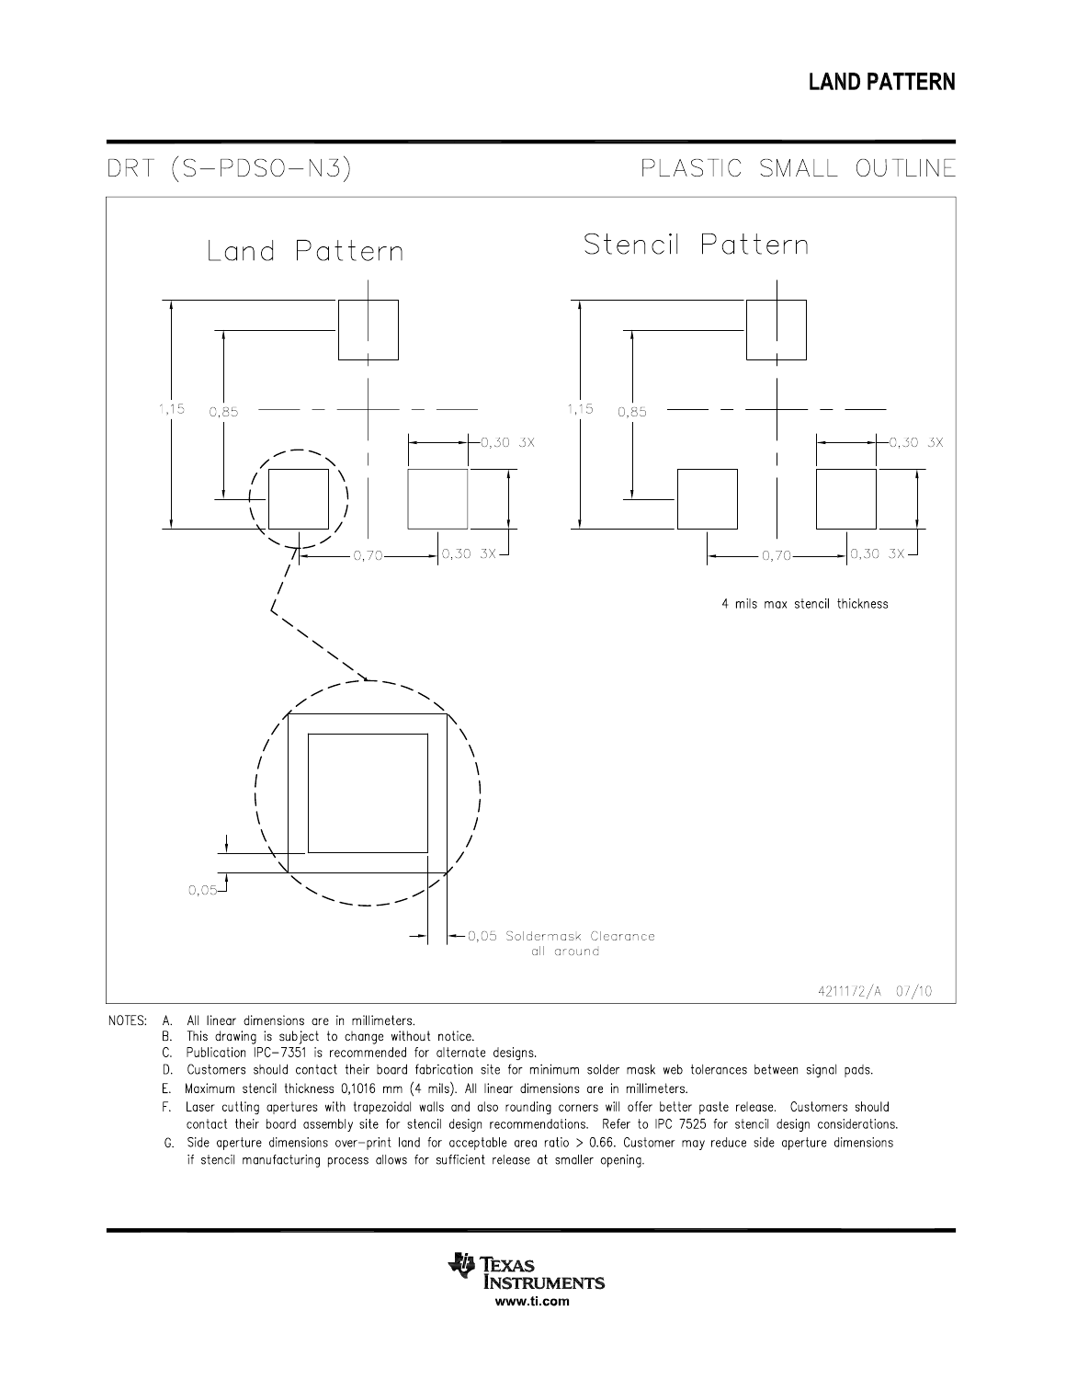
latest_builds/reference_evidence/TI_DRT_land_pattern.png
