anticipation-labs/anticipy-hardware/latest_builds/reference_evidence/TI_electrical_page5.png

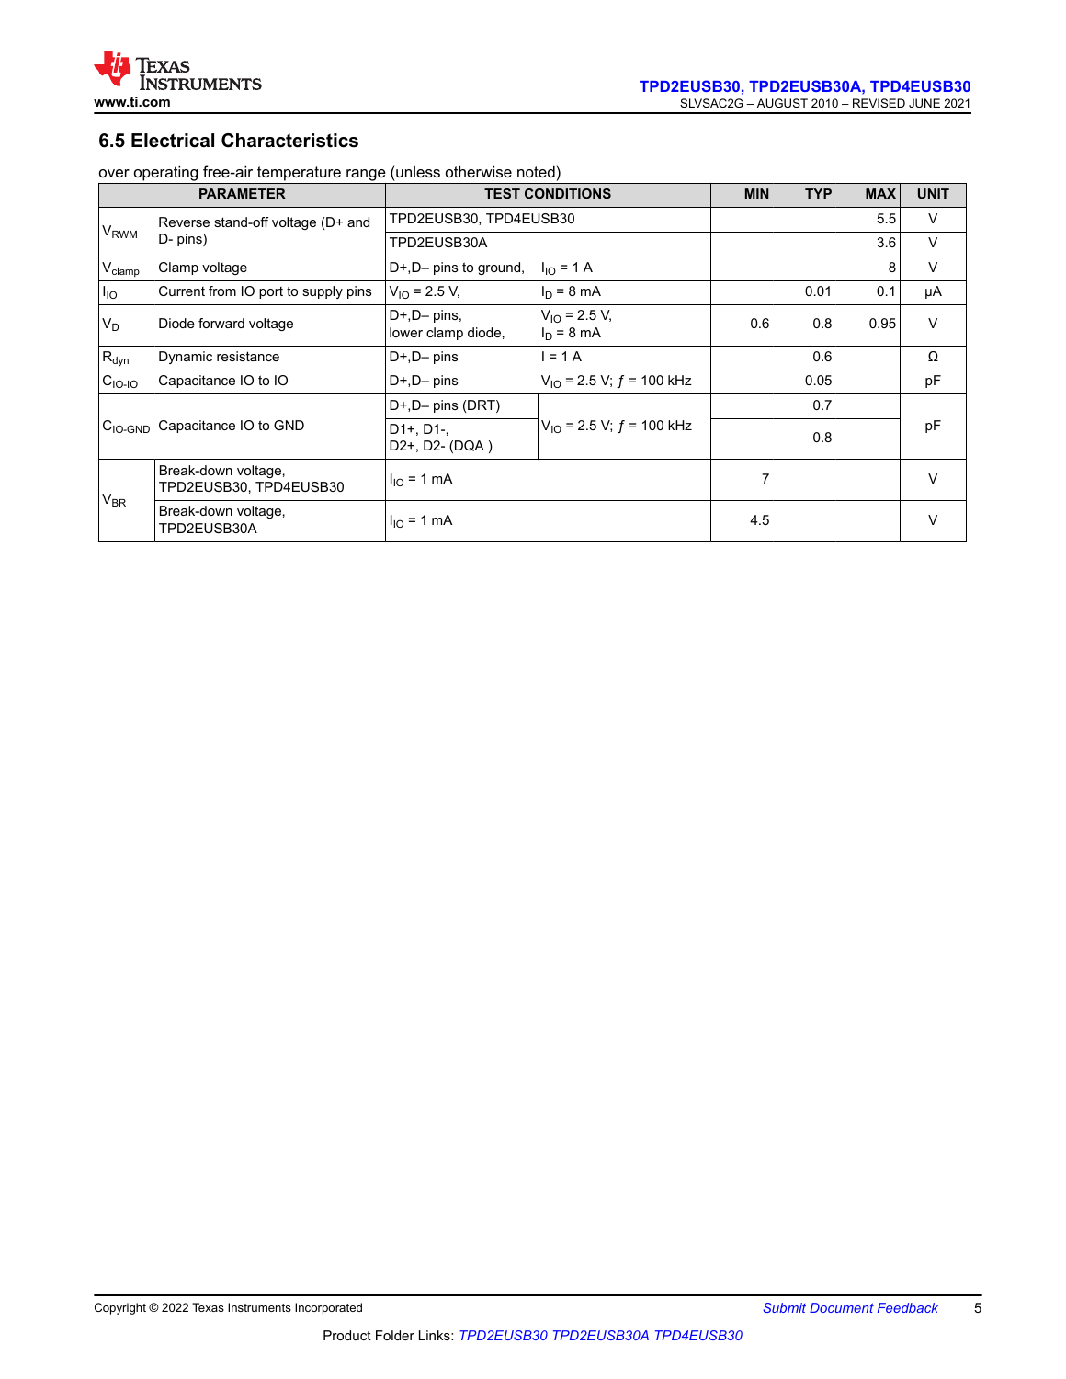
latest_builds/reference_evidence/TI_electrical_page5.png
