anticipation-labs/anticipy-hardware/03_PCB/R0B_CHECKPOINT_NOT_FOR_FAB/01_Electrical_Source/Reports/verify_project_r0b_drc.txt

** Drc report for /workspace/scratch/295a51172f48/anticipy_pcb_kicad_r0b/Anticipy_PROD_R0B_EVT.kicad_pcb **
** Created on 2026-08-29 16:30:52 **

** Found 0 DRC violations **

** Found 176 unconnected pads **
[unconnected_items]: Missing connection between items
    Local override; Severity: error
    @(36.9500 mm, 31.0375 mm): Pad 32 [3V_FLASH] of U2 on F.Cu
    @(38.0000 mm, 31.5000 mm): Pad 1 [3V_FLASH] of TP12 on B.Cu
[unconnected_items]: Missing connection between items
    Local override; Severity: error
    @(53.3000 mm, 29.5750 mm): Pad 1 [3V_FLASH] of C18 on F.Cu
    @(51.9500 mm, 28.7950 mm): Pad 8 [3V_FLASH] of U5 on F.Cu
[unconnected_items]: Missing connection between items
    Local override; Severity: error
    @(53.2500 mm, 31.7300 mm): Pad 1 [3V_FLASH] of C17 on F.Cu
    @(53.2500 mm, 33.6600 mm): Pad 1 [3V_FLASH] of R7 on F.Cu
[unconnected_items]: Missing connection between items
    Local override; Severity: error
    @(53.3000 mm, 29.5750 mm): Pad 1 [3V_FLASH] of C18 on F.Cu
    @(53.2500 mm, 31.7300 mm): Pad 1 [3V_FLASH] of C17 on F.Cu
[unconnected_items]: Missing connection between items
    Local override; Severity: error
    @(41.1500 mm, 25.7500 mm): Pad 1 [3V_FLASH] of C8 on F.Cu
    @(43.1250 mm, 27.5750 mm): Pad 1 [3V_FLASH] of L2 on F.Cu
[unconnected_items]: Missing connection between items
    Local override; Severity: error
    @(43.1250 mm, 27.5750 mm): Pad 1 [3V_FLASH] of L2 on F.Cu
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
[unconnected_items]: Missing connection between items
    Local override; Severity: error
    @(35.2000 mm, 28.6000 mm): Pad 33 [GND] of U2 on F.Cu
    @(41.0000 mm, 30.0000 mm): Pad 1 [GND] of TP5 on B.Cu
[unconnected_items]: Missing connection between items
    Local override; Severity: error
    @(55.1000 mm, 25.7500 mm): Pad 1 [GND] of U1 on F.Cu
    @(64.4000 mm, 25.7500 mm): Pad 55 [GND] of U1 on F.Cu
[unconnected_items]: Missing connection between items
    Local override; Severity: error
    @(48.3900 mm, 36.3000 mm): Pad 1 [HAPTIC_GATE] of R6 on F.Cu
    @(49.4100 mm, 35.0000 mm): Pad 2 [HAPTIC_GATE] of R5 on F.Cu
[unconnected_items]: Missing connection between items
    Local override; Severity: error
    @(46.8875 mm, 37.4500 mm): Pad 1 [HAPTIC_GATE] of Q1 on F.Cu
    @(48.3900 mm, 36.3000 mm): Pad 1 [HAPTIC_GATE] of R6 on F.Cu
[unconnected_items]: Missing connection between items
    Local override; Severity: error
    @(45.0125 mm, 36.5000 mm): Pad 3 [HAPTIC_NEG] of Q1 on F.Cu
    @(43.4000 mm, 35.0000 mm): Pad 2 [HAPTIC_NEG] of D1 on F.Cu
[unconnected_items]: Missing connection between items
    Local override; Severity: error
    @(43.4000 mm, 35.0000 mm): Pad 2 [HAPTIC_NEG] of D1 on F.Cu
    @(40.4800 mm, 36.8000 mm): Pad 2 [HAPTIC_NEG] of C22 on F.Cu
[unconnected_items]: Missing connection between items
    Local override; Severity: error
    @(45.0125 mm, 36.5000 mm): Pad 3 [HAPTIC_NEG] of Q1 on F.Cu
    @(54.4000 mm, 33.6350 mm): Pad 2 [HAPTIC_NEG] of M1 on B.Cu
[unconnected_items]: Missing connection between items
    Local override; Severity: error
    @(48.3900 mm, 35.0000 mm): Pad 1 [HAPTIC_PWM] of R5 on F.Cu
    @(59.7500 mm, 36.6500 mm): Pad 24 [HAPTIC_PWM] of U1 on F.Cu
[unconnected_items]: Missing connection between items
    Local override; Severity: error
    @(34.4000 mm, 24.2800 mm): Pad 2 [I2C_SCL] of R1 on F.Cu
    @(34.4500 mm, 26.1625 mm): Pad 14 [I2C_SCL] of U2 on F.Cu
[unconnected_items]: Missing connection between items
    Local override; Severity: error
    @(50.5375 mm, 35.7000 mm): Pad 1 [I2C_SCL] of U3 on F.Cu
    @(57.7500 mm, 35.7500 mm): Pad 19 [I2C_SCL] of U1 on F.Cu
[unconnected_items]: Missing connection between items
    Local override; Severity: error
    @(34.4500 mm, 26.1625 mm): Pad 14 [I2C_SCL] of U2 on F.Cu
    @(50.5375 mm, 35.7000 mm): Pad 1 [I2C_SCL] of U3 on F.Cu
[unconnected_items]: Missing connection between items
    Local override; Severity: error
    @(35.0000 mm, 24.2800 mm): Pad 2 [I2C_SDA] of R2 on F.Cu
    @(34.9500 mm, 26.1625 mm): Pad 13 [I2C_SDA] of U2 on F.Cu
[unconnected_items]: Missing connection between items
    Local override; Severity: error
    @(50.5375 mm, 37.2000 mm): Pad 4 [I2C_SDA] of U3 on F.Cu
    @(55.7500 mm, 36.6500 mm): Pad 16 [I2C_SDA] of U1 on F.Cu
[unconnected_items]: Missing connection between items
    Local override; Severity: error
    @(34.9500 mm, 26.1625 mm): Pad 13 [I2C_SDA] of U2 on F.Cu
    @(50.5375 mm, 37.2000 mm): Pad 4 [I2C_SDA] of U3 on F.Cu
[unconnected_items]: Missing connection between items
    Local override; Severity: error
    @(33.4500 mm, 31.0375 mm): Pad 25 [LED_BLUE_K] of U2 on F.Cu
    @(34.6000 mm, 36.3500 mm): Pad 1 [LED_BLUE_K] of LED1 on F.Cu
[unconnected_items]: Missing connection between items
    Local override; Severity: error
    @(33.9500 mm, 31.0375 mm): Pad 26 [LED_RED_K] of U2 on F.Cu
    @(34.6000 mm, 37.0500 mm): Pad 3 [LED_RED_K] of LED1 on F.Cu
[unconnected_items]: Missing connection between items
    Local override; Severity: error
    @(32.7625 mm, 27.3500 mm): Pad 18 [NTC] of U2 on F.Cu
    @(54.4000 mm, 28.8000 mm): Pad 2 [NTC] of BT1 on B.Cu
[unconnected_items]: Missing connection between items
    Local override; Severity: error
    @(50.7750 mm, 23.2250 mm): Pad 3 [PDM_CLK] of MIC2 on F.Cu
    @(45.8750 mm, 23.2250 mm): Pad 3 [PDM_CLK] of MIC1 on F.Cu
[unconnected_items]: Missing connection between items
    Local override; Severity: error
    @(63.5000 mm, 33.6500 mm): Pad 38 [PDM_CLK] of U1 on F.Cu
    @(50.7750 mm, 23.2250 mm): Pad 3 [PDM_CLK] of MIC2 on F.Cu
[unconnected_items]: Missing connection between items
    Local override; Severity: error
    @(52.6100 mm, 26.8000 mm): Pad 2 [PDM_DATA] of R9 on F.Cu
    @(47.8100 mm, 26.8000 mm): Pad 2 [PDM_DATA] of R8 on F.Cu
[unconnected_items]: Missing connection between items
    Local override; Severity: error
    @(64.4000 mm, 33.2500 mm): Pad 39 [PDM_DATA] of U1 on F.Cu
    @(52.6100 mm, 26.8000 mm): Pad 2 [PDM_DATA] of R9 on F.Cu
[unconnected_items]: Missing connection between items
    Local override; Severity: error
    @(45.8750 mm, 24.5750 mm): Pad 4 [PDM_DATA_MIC1] of MIC1 on F.Cu
    @(46.7900 mm, 26.8000 mm): Pad 1 [PDM_DATA_MIC1] of R8 on F.Cu
[unconnected_items]: Missing connection between items
    Local override; Severity: error
    @(50.7750 mm, 24.5750 mm): Pad 4 [PDM_DATA_MIC2] of MIC2 on F.Cu
    @(51.5900 mm, 26.8000 mm): Pad 1 [PDM_DATA_MIC2] of R9 on F.Cu
[unconnected_items]: Missing connection between items
    Local override; Severity: error
    @(37.6375 mm, 27.3500 mm): Pad 7 [PMIC_INT] of U2 on F.Cu
    @(41.0000 mm, 31.5000 mm): Pad 1 [PMIC_INT] of TP14 on B.Cu
[unconnected_items]: Missing connection between items
    Local override; Severity: error
    @(41.0000 mm, 31.5000 mm): Pad 1 [PMIC_INT] of TP14 on B.Cu
    @(64.4000 mm, 32.4500 mm): Pad 41 [PMIC_INT] of U1 on F.Cu
[unconnected_items]: Missing connection between items
    Local override; Severity: error
    @(41.4750 mm, 32.9500 mm): Pad 2 [PVSS1] of C7 on F.Cu
    @(42.6500 mm, 33.5000 mm): Pad 1 [PVSS1] of NT1 on F.Cu
[unconnected_items]: Missing connection between items
    Local override; Severity: error
    @(40.1050 mm, 31.9000 mm): Pad 2 [PVSS1] of C14 on F.Cu
    @(41.4750 mm, 32.9500 mm): Pad 2 [PVSS1] of C7 on F.Cu
[unconnected_items]: Missing connection between items
    Local override; Severity: error
    @(40.0250 mm, 29.3750 mm): Pad 2 [PVSS1] of C2 on F.Cu
    @(37.6375 mm, 29.8500 mm): Pad 2 [PVSS1] of U2 on F.Cu
[unconnected_items]: Missing connection between items
    Local override; Severity: error
    @(40.0250 mm, 29.3750 mm): Pad 2 [PVSS1] of C2 on F.Cu
    @(40.1050 mm, 31.9000 mm): Pad 2 [PVSS1] of C14 on F.Cu
[unconnected_items]: Missing connection between items
    Local override; Severity: error
    @(42.7000 mm, 25.7500 mm): Pad 2 [PVSS2] of C8 on F.Cu
    @(43.6000 mm, 24.0000 mm): Pad 1 [PVSS2] of NT2 on F.Cu
[unconnected_items]: Missing connection between items
    Local override; Severity: error
    @(37.6375 mm, 27.8500 mm): Pad 6 [PVSS2] of U2 on F.Cu
    @(40.0250 mm, 28.3250 mm): Pad 2 [PVSS2] of C3 on F.Cu
[unconnected_items]: Missing connection between items
    Local override; Severity: error
    @(40.0250 mm, 28.3250 mm): Pad 2 [PVSS2] of C3 on F.Cu
    @(40.1050 mm, 25.8000 mm): Pad 2 [PVSS2] of C15 on F.Cu
[unconnected_items]: Missing connection between items
    Local override; Severity: error
    @(42.7000 mm, 25.7500 mm): Pad 2 [PVSS2] of C8 on F.Cu
    @(40.1050 mm, 25.8000 mm): Pad 2 [PVSS2] of C15 on F.Cu
[unconnected_items]: Missing connection between items
    Local override; Severity: error
    @(38.0000 mm, 30.0000 mm): Pad 1 [RESET] of TP3 on B.Cu
    @(63.5000 mm, 32.8500 mm): Pad 40 [RESET] of U1 on F.Cu
[unconnected_items]: Missing connection between items
    Local override; Severity: error
    @(28.3000 mm, 36.3000 mm): Pad 1 [SHPHLD_BTN] of SW1 on F.Cu
    @(33.9500 mm, 26.1625 mm): Pad 15 [SHPHLD_BTN] of U2 on F.Cu
[unconnected_items]: Missing connection between items
    Local override; Severity: error
    @(37.6375 mm, 29.3500 mm): Pad 3 [SW1] of U2 on F.Cu
    @(41.9000 mm, 29.9000 mm): Pad 2 [SW1] of L1 on F.Cu
[unconnected_items]: Missing connection between items
    Local override; Severity: error
    @(37.6375 mm, 28.3500 mm): Pad 5 [SW2] of U2 on F.Cu
    @(41.6750 mm, 27.5750 mm): Pad 2 [SW2] of L2 on F.Cu
[unconnected_items]: Missing connection between items
    Local override; Severity: error
    @(36.5000 mm, 30.0000 mm): Pad 1 [SWDCLK] of TP2 on B.Cu
    @(64.4000 mm, 26.8500 mm): Pad 53 [SWDCLK] of U1 on F.Cu
[unconnected_items]: Missing connection between items
    Local override; Severity: error
    @(35.0000 mm, 30.0000 mm): Pad 1 [SWDIO] of TP1 on B.Cu
    @(64.4000 mm, 27.6500 mm): Pad 51 [SWDIO] of U1 on F.Cu
[unconnected_items]: Missing connection between items
    Local override; Severity: error
    @(44.0000 mm, 30.0000 mm): Pad 1 [UART_RX] of TP7 on B.Cu
    @(58.1500 mm, 36.6500 mm): Pad 20 [UART_RX] of U1 on F.Cu
[unconnected_items]: Missing connection between items
    Local override; Severity: error
    @(42.5000 mm, 30.0000 mm): Pad 1 [UART_TX] of TP6 on B.Cu
    @(58.5500 mm, 35.7500 mm): Pad 21 [UART_TX] of U1 on F.Cu
[unconnected_items]: Missing connection between items
    Local override; Severity: error
    @(26.7500 mm, 31.2500 mm): Pad 4 [USB_CC1] of J1 on F.Cu
    @(32.7625 mm, 29.8500 mm): Pad 23 [USB_CC1] of U2 on F.Cu
[unconnected_items]: Missing connection between items
    Local override; Severity: error
    @(32.7625 mm, 29.8500 mm): Pad 23 [USB_CC1] of U2 on F.Cu
    @(27.9000 mm, 22.4500 mm): Pad 1 [USB_CC1] of U6 on F.Cu
[unconnected_items]: Missing connection between items
    Local override; Severity: error
    @(27.9000 mm, 23.7500 mm): Pad 2 [USB_CC2] of U6 on F.Cu
    @(26.7500 mm, 28.2500 mm): Pad 10 [USB_CC2] of J1 on F.Cu
[unconnected_items]: Missing connection between items
    Local override; Severity: error
    @(26.7500 mm, 28.2500 mm): Pad 10 [USB_CC2] of J1 on F.Cu
    @(32.7625 mm, 30.3500 mm): Pad 24 [USB_CC2] of U2 on F.Cu
[unconnected_items]: Missing connection between items
    Local override; Severity: error
    @(26.7500 mm, 29.2500 mm): Pad 8 [USB_D+] of J1 on F.Cu
    @(26.7500 mm, 30.2500 mm): Pad 6 [USB_D+] of J1 on F.Cu
[unconnected_items]: Missing connection between items
    Local override; Severity: error
    @(27.7750 mm, 29.6500 mm): Pad 1 [USB_D+] of U4 on F.Cu
    @(26.7500 mm, 29.2500 mm): Pad 8 [USB_D+] of J1 on F.Cu
[unconnected_items]: Missing connection between items
    Local override; Severity: error
    @(59.9800 mm, 38.0000 mm): Pad 1 [USB_D+] of R10 on F.Cu
    @(27.7750 mm, 29.6500 mm): Pad 1 [USB_D+] of U4 on F.Cu
[unconnected_items]: Missing connection between items
    Local override; Severity: error
    @(26.7500 mm, 29.7500 mm): Pad 7 [USB_D-] of J1 on F.Cu
    @(26.7500 mm, 30.7500 mm): Pad 5 [USB_D-] of J1 on F.Cu
[unconnected_items]: Missing connection between items
    Local override; Severity: error
    @(26.7500 mm, 30.7500 mm): Pad 5 [USB_D-] of J1 on F.Cu
    @(27.7750 mm, 30.3500 mm): Pad 2 [USB_D-] of U4 on F.Cu
[unconnected_items]: Missing connection between items
    Local override; Severity: error
    @(61.4800 mm, 38.0000 mm): Pad 1 [USB_D-] of R11 on F.Cu
    @(27.7750 mm, 30.3500 mm): Pad 2 [USB_D-] of U4 on F.Cu
[unconnected_items]: Missing connection between items
    Local override; Severity: error
    @(60.6200 mm, 38.0000 mm): Pad 2 [USB_MCU_D+] of R10 on F.Cu
    @(64.4000 mm, 34.8500 mm): Pad 35 [USB_MCU_D+] of U1 on F.Cu
[unconnected_items]: Missing connection between items
    Local override; Severity: error
    @(62.1200 mm, 38.0000 mm): Pad 2 [USB_MCU_D-] of R11 on F.Cu
    @(64.4000 mm, 35.6500 mm): Pad 34 [USB_MCU_D-] of U1 on F.Cu
[unconnected_items]: Missing connection between items
    Local override; Severity: error
    @(29.4000 mm, 25.5000 mm): Pad 1 [VBAT] of C6 on F.Cu
    @(32.7625 mm, 27.8500 mm): Pad 19 [VBAT] of U2 on F.Cu
[unconnected_items]: Missing connection between items
    Local override; Severity: error
    @(45.5000 mm, 30.0000 mm): Pad 1 [VBAT] of TP8 on B.Cu
    @(54.4000 mm, 27.5300 mm): Pad 1 [VBAT] of BT1 on B.Cu
[unconnected_items]: Missing connection between items
    Local override; Severity: error
    @(32.7625 mm, 27.8500 mm): Pad 19 [VBAT] of U2 on F.Cu
    @(45.5000 mm, 30.0000 mm): Pad 1 [VBAT] of TP8 on B.Cu
[unconnected_items]: Missing connection between items
    Local override; Severity: error
    @(26.7500 mm, 32.4000 mm): Pad 2 [VBUS] of J1 on F.Cu
    @(28.0500 mm, 32.7500 mm): Pad 1 [VBUS] of D2 on F.Cu
[unconnected_items]: Missing connection between items
    Local override; Severity: error
    @(29.5000 mm, 30.8000 mm): Pad 1 [VBUS] of C1 on F.Cu
    @(28.0500 mm, 32.7500 mm): Pad 1 [VBUS] of D2 on F.Cu
[unconnected_items]: Missing connection between items
    Local override; Severity: error
    @(29.5000 mm, 30.8000 mm): Pad 1 [VBUS] of C1 on F.Cu
    @(32.7625 mm, 28.8500 mm): Pad 21 [VBUS] of U2 on F.Cu
[unconnected_items]: Missing connection between items
    Local override; Severity: error
    @(26.7500 mm, 27.6000 mm): Pad 11 [VBUS] of J1 on F.Cu
    @(29.5000 mm, 30.8000 mm): Pad 1 [VBUS] of C1 on F.Cu
[unconnected_items]: Missing connection between items
    Local override; Severity: error
    @(32.7625 mm, 28.8500 mm): Pad 21 [VBUS] of U2 on F.Cu
    @(47.0000 mm, 30.0000 mm): Pad 1 [VBUS] of TP9 on B.Cu
[unconnected_items]: Missing connection between items
    Local override; Severity: error
    @(63.0200 mm, 38.0000 mm): Pad 1 [VBUSOUT] of C26 on F.Cu
    @(63.7500 mm, 36.6500 mm): Pad 32 [VBUSOUT] of U1 on F.Cu
[unconnected_items]: Missing connection between items
    Local override; Severity: error
    @(32.7625 mm, 29.3500 mm): Pad 22 [VBUSOUT] of U2 on F.Cu
    @(30.7000 mm, 31.4250 mm): Pad 1 [VBUSOUT] of C5 on F.Cu
[unconnected_items]: Missing connection between items
    Local override; Severity: error
    @(36.5000 mm, 31.5000 mm): Pad 1 [VBUSOUT] of TP11 on B.Cu
    @(32.7625 mm, 29.3500 mm): Pad 22 [VBUSOUT] of U2 on F.Cu
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
[unconnected_items]: Missing connection between items
    Local override; Severity: error
    @(33.4000 mm, 34.8750 mm): Pad 1 [VSYS] of C9 on F.Cu
    @(35.0000 mm, 31.5000 mm): Pad 1 [VSYS] of TP10 on B.Cu

** Found 0 Footprint errors **

** End of Report **
