anticipation-labs/anticipy-hardware/latest_builds/E1P1/pcb/verification/all_45_nets.csv

net | unique_pads | track_segments | vias | total_track_mm | min_track_width_mm | max_track_width_mm | F.Cu_mm | In1.Cu_mm | In2.Cu_mm | B.Cu_mm | F.Cu_without_adjacent_GND_mm | In1.Cu_without_adjacent_GND_mm | In2.Cu_without_adjacent_GND_mm | B.Cu_without_adjacent_GND_mm
2V5_AUX | 4 | 13 | 1 | 19.6 | 0.2 | 0.4 | 10.839 | 0 | 0 | 8.761 | 2.909 | 0 | 0 | 2.987
3V_MAIN | 22 | 146 | 6 | 81.521 | 0.127 | 0.4 | 53.905 | 18.548 | 0 | 9.068 | 9.382 | 7.025 | 0 | 5.188
3V_MIC | 8 | 48 | 5 | 42.79 | 0.127 | 0.3 | 16.563 | 10.96 | 12.551 | 2.715 | 7.408 | 9.722 | 2.129 | 0.684
FLASH_CS | 3 | 24 | 5 | 30.152 | 0.127 | 0.15 | 7.496 | 16.25 | 0 | 6.406 | 2.321 | 8.881 | 0 | 2.679
FLASH_IO0 | 2 | 7 | 2 | 16.382 | 0.15 | 0.15 | 1.404 | 0 | 14.978 | 0 | 0.705 | 0 | 1.929 | 0
FLASH_IO1 | 2 | 12 | 2 | 23.662 | 0.15 | 0.15 | 2.045 | 0 | 21.617 | 0 | 0.734 | 0 | 1.644 | 0
FLASH_IO2 | 3 | 11 | 2 | 26.387 | 0.127 | 0.15 | 17.986 | 0 | 8.401 | 0 | 5.44 | 0 | 2.76 | 0
FLASH_IO3 | 3 | 10 | 3 | 26.97 | 0.15 | 0.15 | 6.878 | 6.812 | 13.28 | 0 | 2.019 | 1.883 | 2.391 | 0
FLASH_SCK | 2 | 6 | 2 | 14.31 | 0.15 | 0.15 | 2.08 | 0 | 12.231 | 0 | 0.733 | 0 | 1.822 | 0
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
