anticipation-labs/anticipy-hardware/03_PCB/R0_ROUTING_HISTORY_NOT_FOR_FAB/preview/top.png

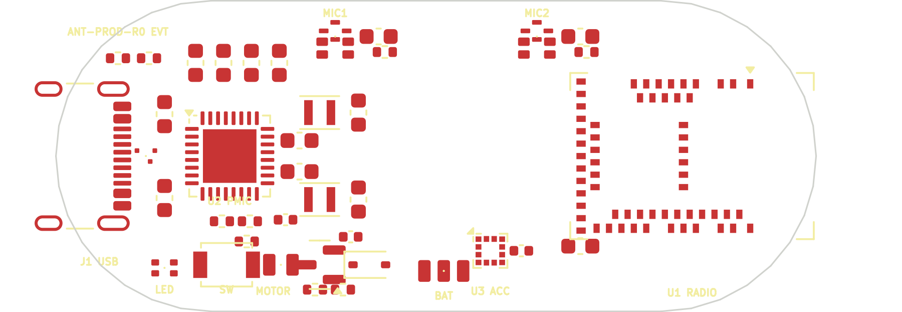
03_PCB/R0_ROUTING_HISTORY_NOT_FOR_FAB/preview/top.png
