anticipation-labs/anticipy-hardware/08_HISTORICAL_PACKAGES/2026-08-28_tuesday_evt_v0.1/anticipy_strict_evt_aluminum_template.pdf

## ANTICIPY STRICT EVT - 1:1 ALUMINUM CAPS

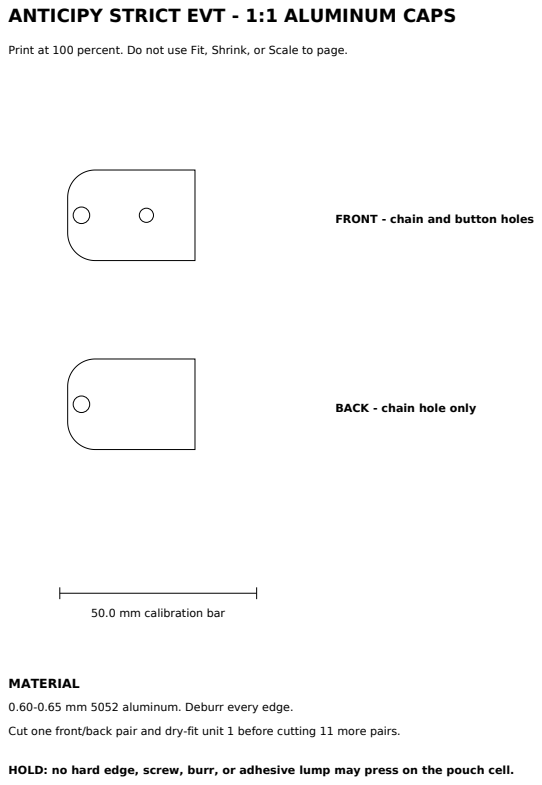
[picture p198: page 1]
MATERIAL

Print at 100 percent. Do not use Fit, Shrink, or Scale to page.

FRONT - chain and button holes

BACK - chain hole only

50.0 mm calibration bar

0.60-0.65 mm 5052 aluminum. Deburr every edge.

Cut one front/back pair and dry-fit unit 1 before cutting 11 more pairs.

HOLD: no hard edge, screw, burr, or adhesive lump may press on the pouch cell.
