anticipation-labs/anticipy-hardware/08_HISTORICAL_PACKAGES/2026-08-28_execution_v1.0/03_PRODUCTION_PCB/docs/sources/AN54LV-15_recommended_pad_20260702.pdf

# Antenna area Antenna area

2.9

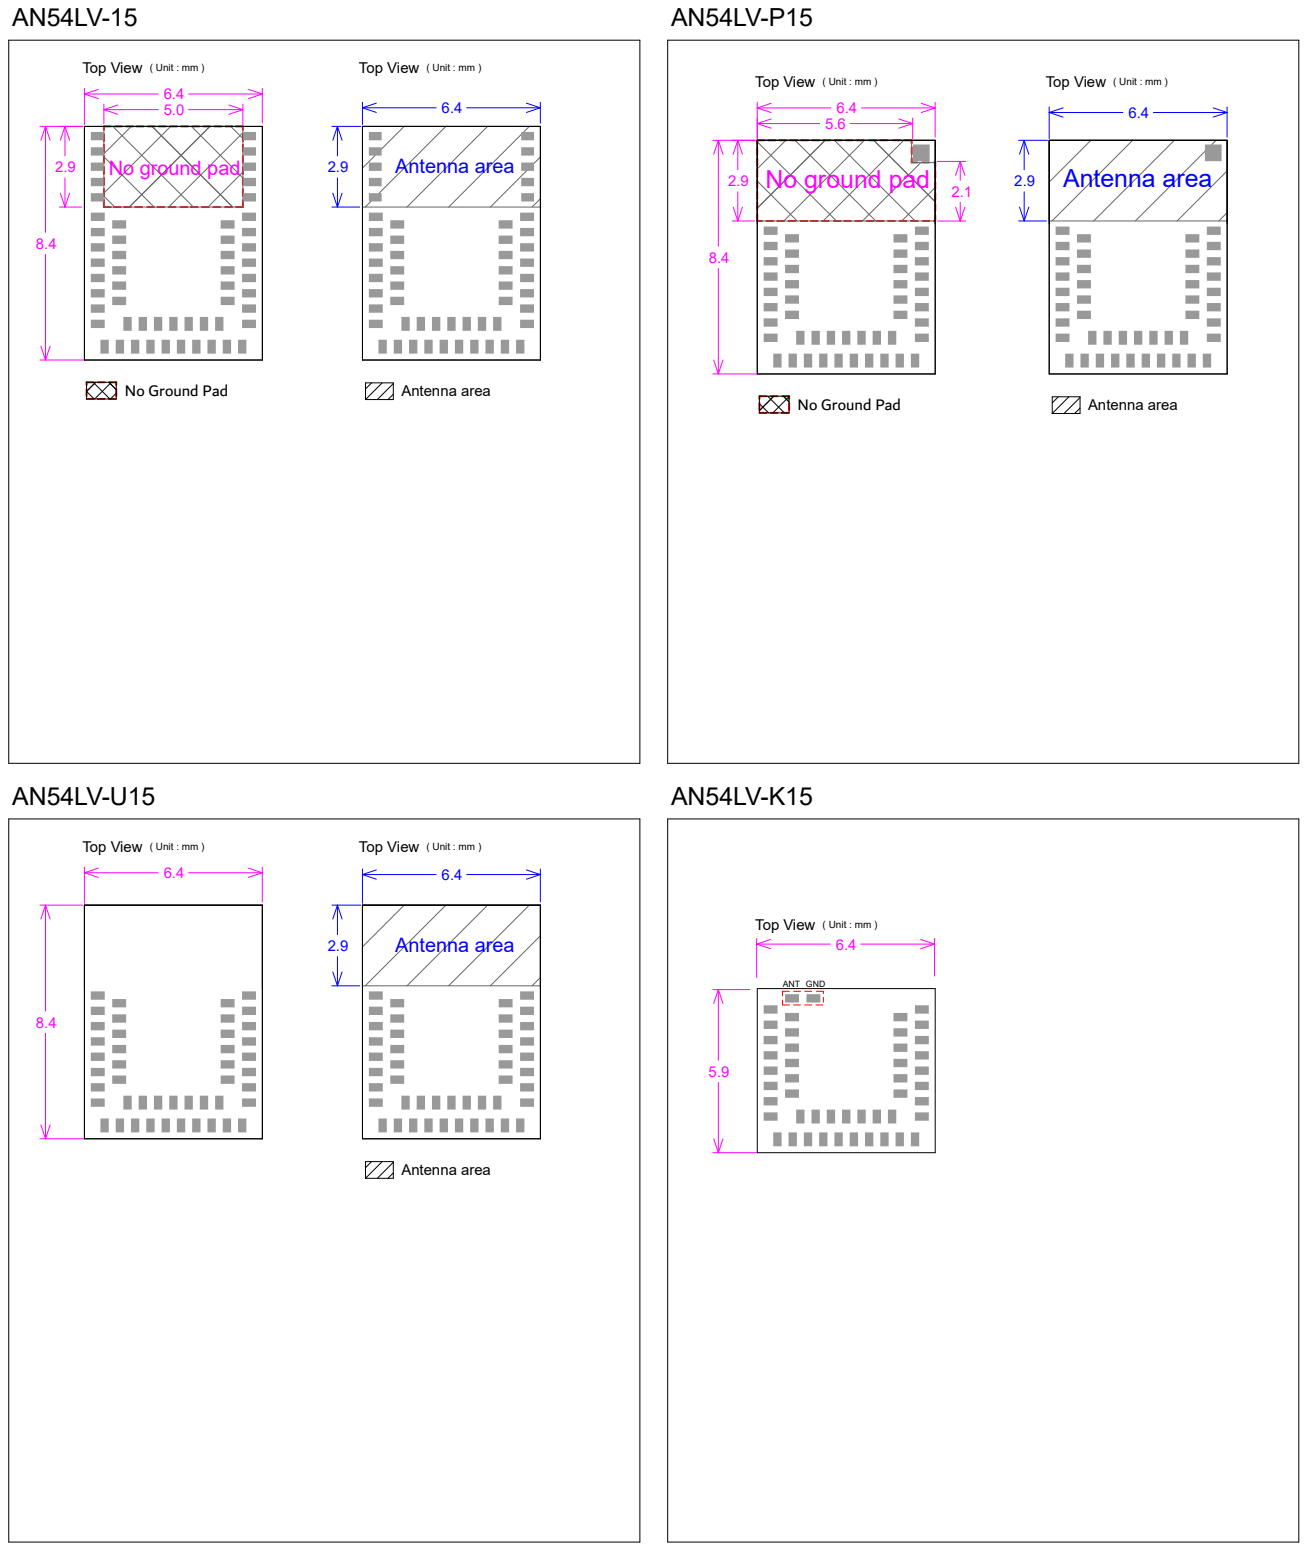
[picture p199: page 1]
Antenna area; ANT GND; Top View; Top View ( Unit : mm ); ( Unit : mm ); No Ground Pad; No ground pad

Top View ( Unit : mm )
